MarkMakies/PIMD/coil-v4/IMG_1528.JPEG

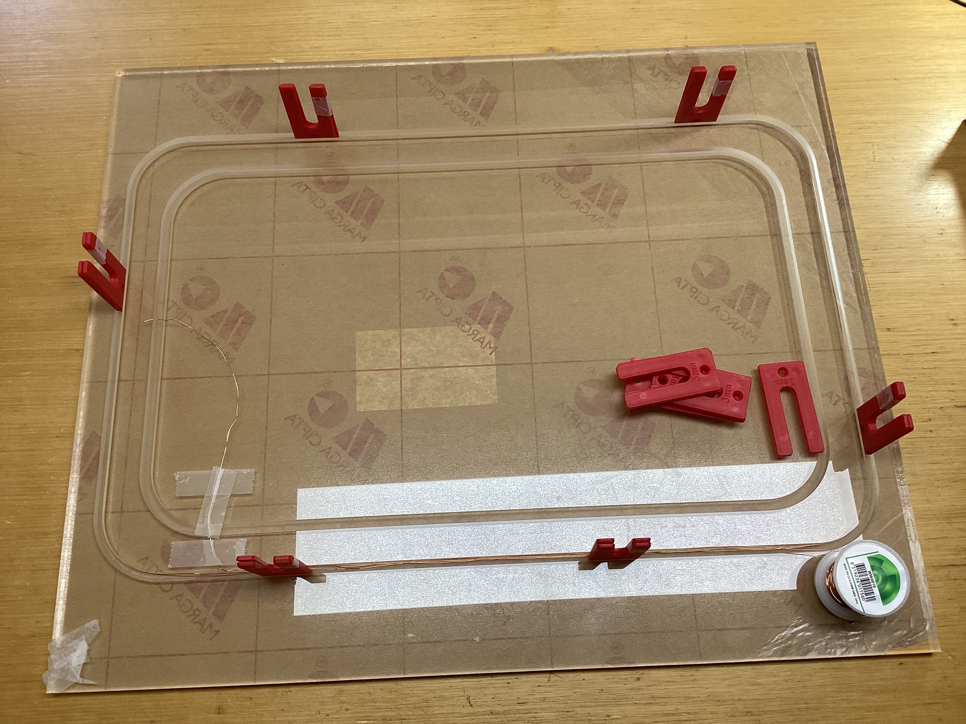
coil-v4/IMG_1528.JPEG
