MarkMakies/PIMD/coil-v4/IMG_1532.JPEG

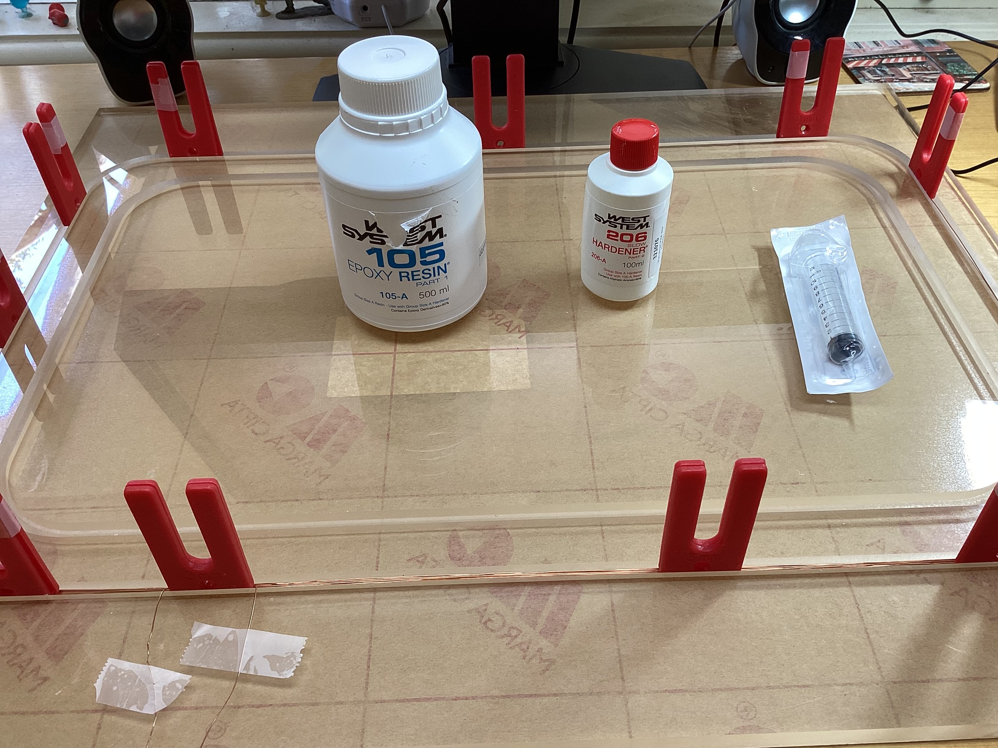
coil-v4/IMG_1532.JPEG
