MarkMakies/PIMD/coil-v4/IMG_1539.JPEG

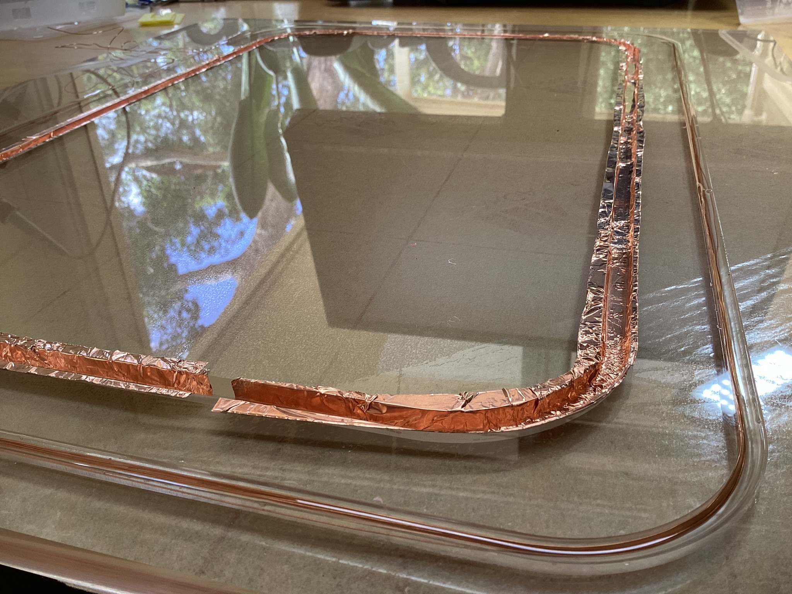
coil-v4/IMG_1539.JPEG
