MarkMakies/PIMD/coil-v4/IMG_1540.JPEG

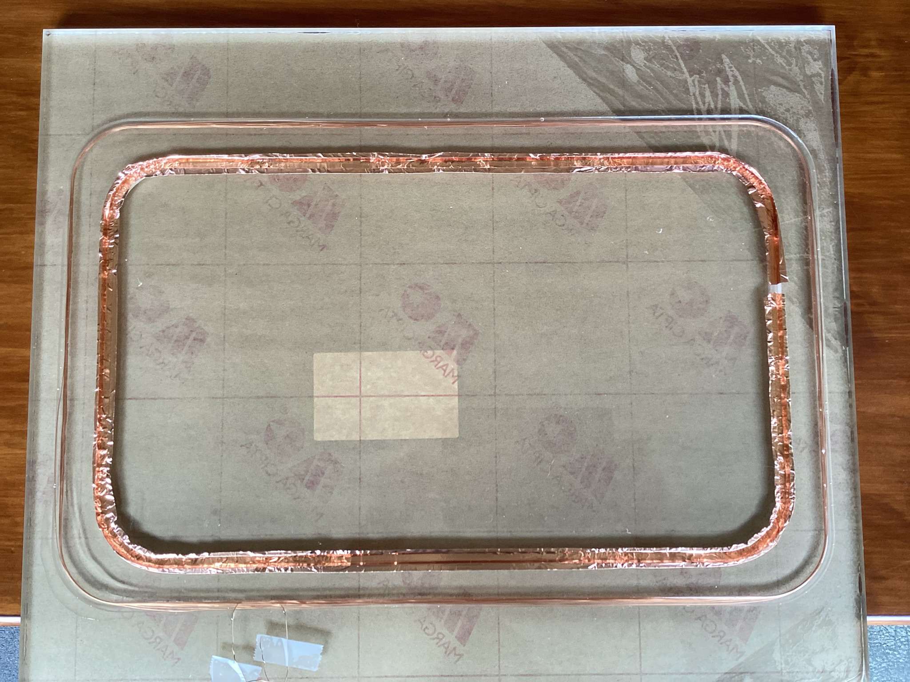
coil-v4/IMG_1540.JPEG
