MarkMakies/PIMD/coil-v4/IMG_1548.JPEG

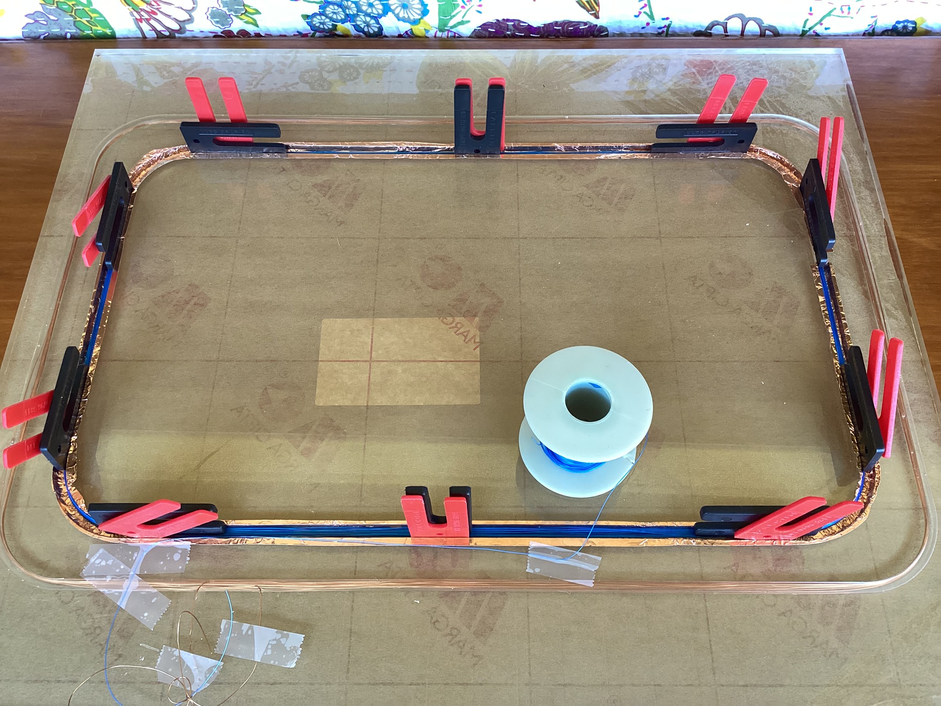
coil-v4/IMG_1548.JPEG
