MarkMakies/PIMD/coil-v4/IMG_1551.JPEG

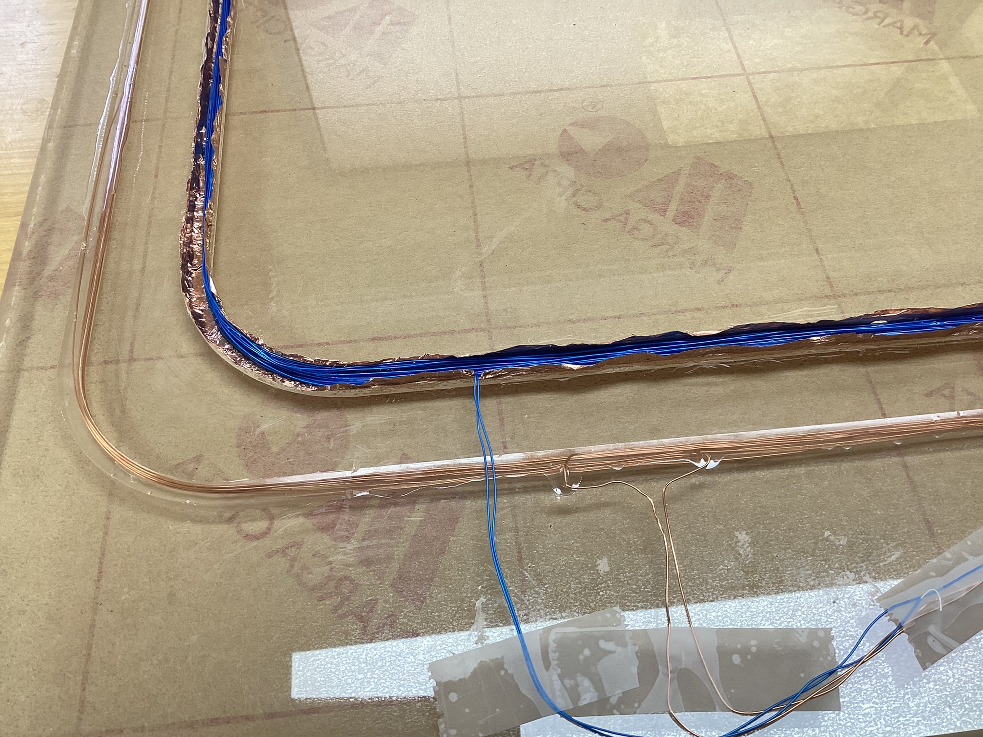
coil-v4/IMG_1551.JPEG
