MarkMakies/PIMD/coil-v4/IMG_1552.JPEG

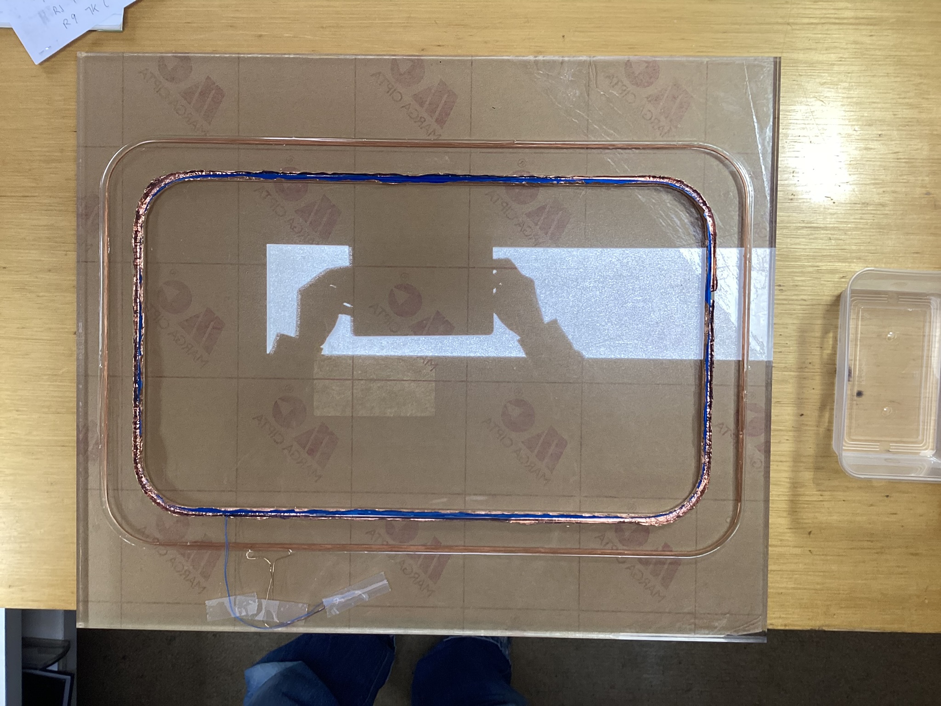
coil-v4/IMG_1552.JPEG
