MarkMakies/PIMD/coil-v4/IMG_1557.JPEG

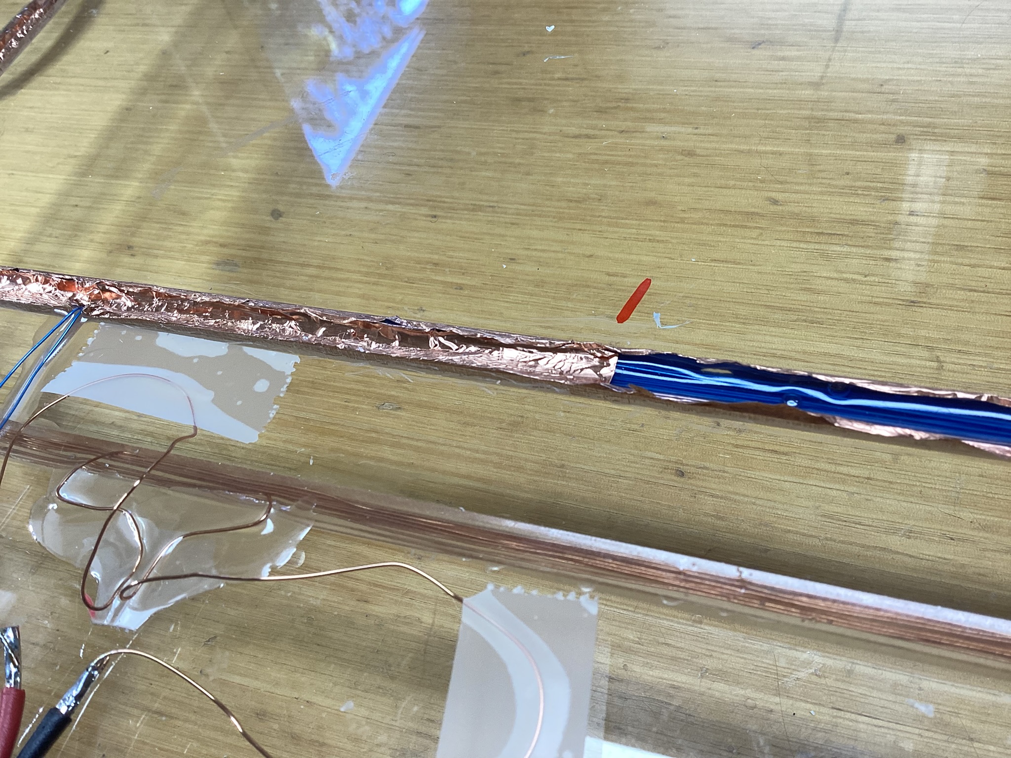
coil-v4/IMG_1557.JPEG
