MarkMakies/PIMD/coil-v4/IMG_1558.JPEG

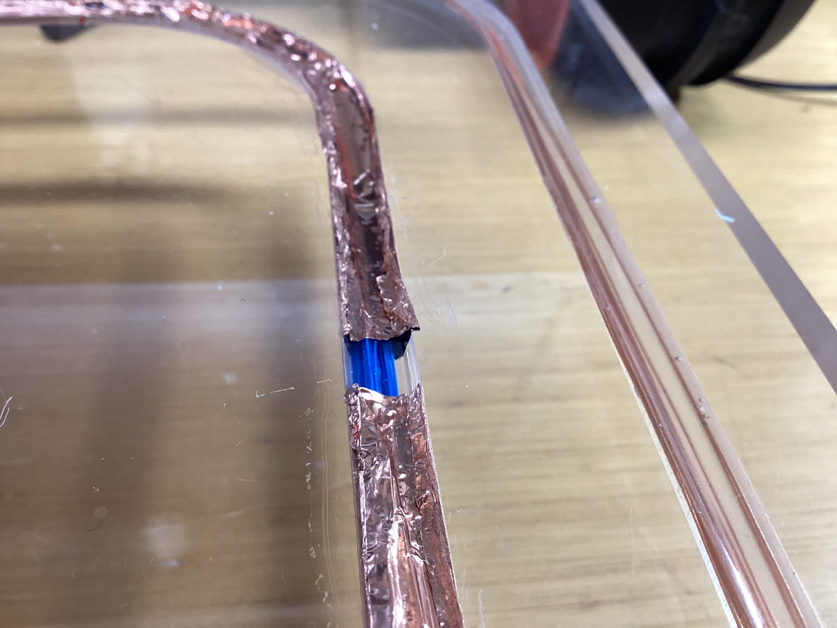
coil-v4/IMG_1558.JPEG
