MarkMakies/PIMD/coil-v4/IMG_1560.JPEG

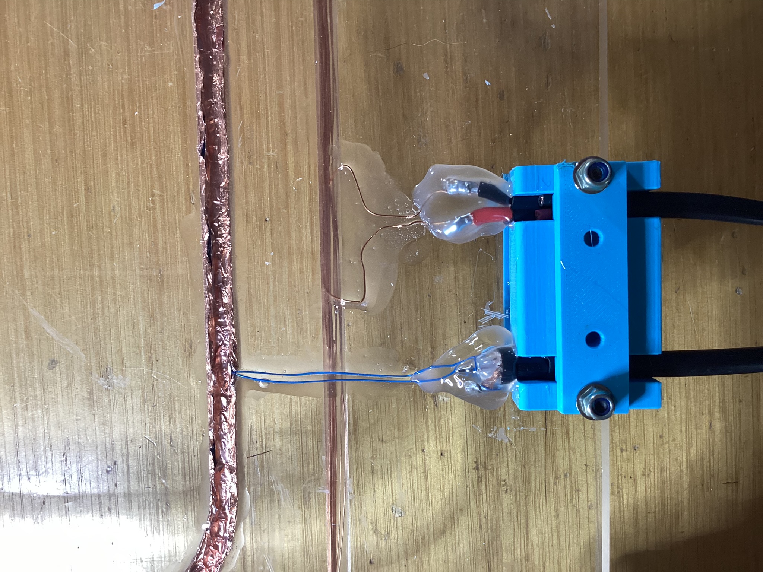
coil-v4/IMG_1560.JPEG
