MarkMakies/PIMD/coil-v4/IMG_1561.JPEG

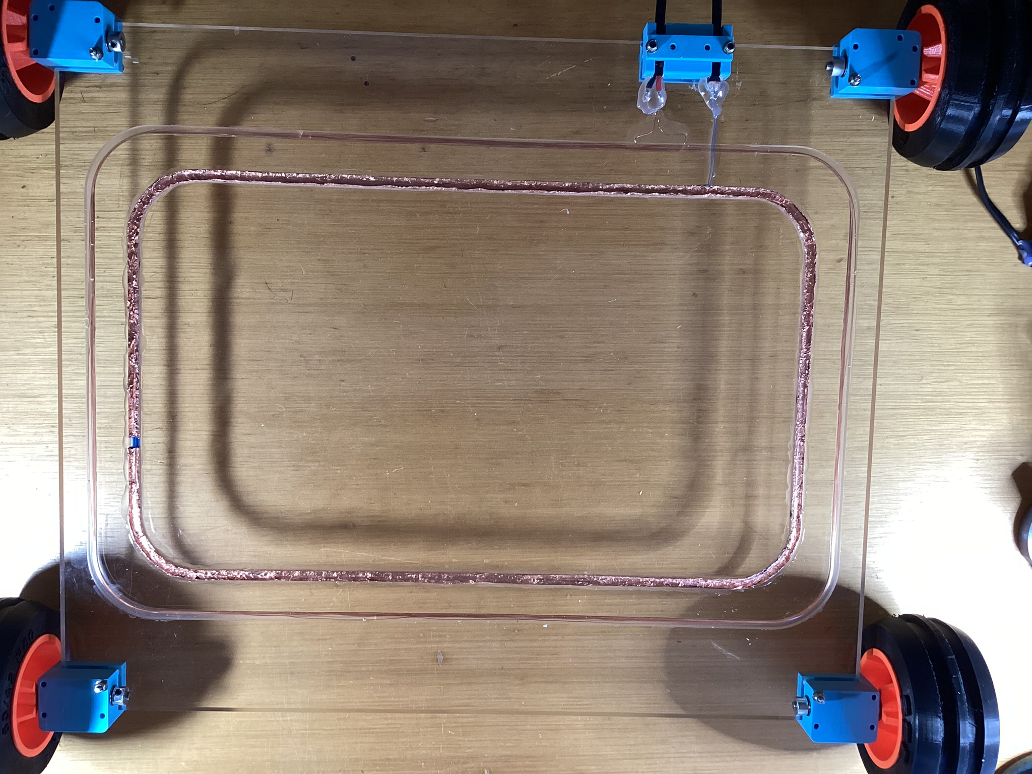
coil-v4/IMG_1561.JPEG
