MarkMakies/PIMD/References/images/6S-pack-discharge-curve.jpg

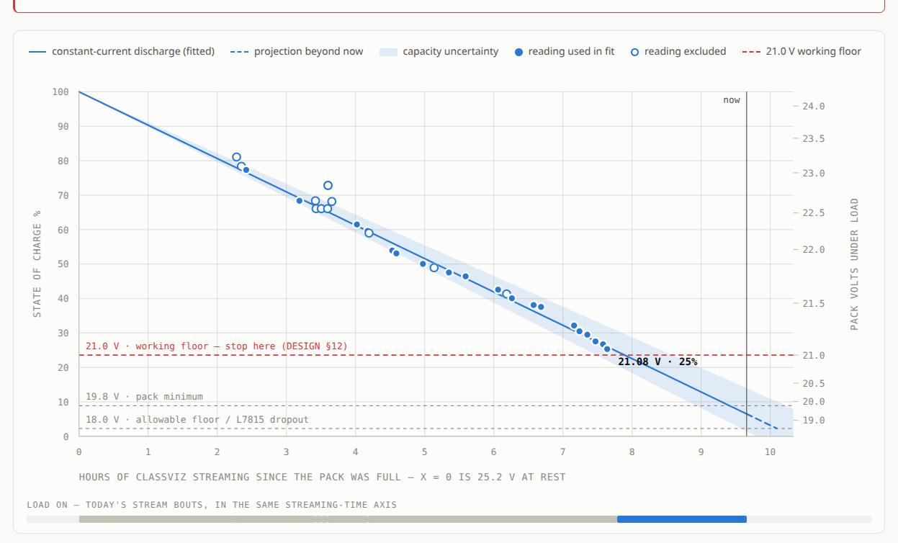
References/images/6S-pack-discharge-curve.jpg
