MarkMakies/PIMD/References/images/bias_mod_delay_plot_20260810.png

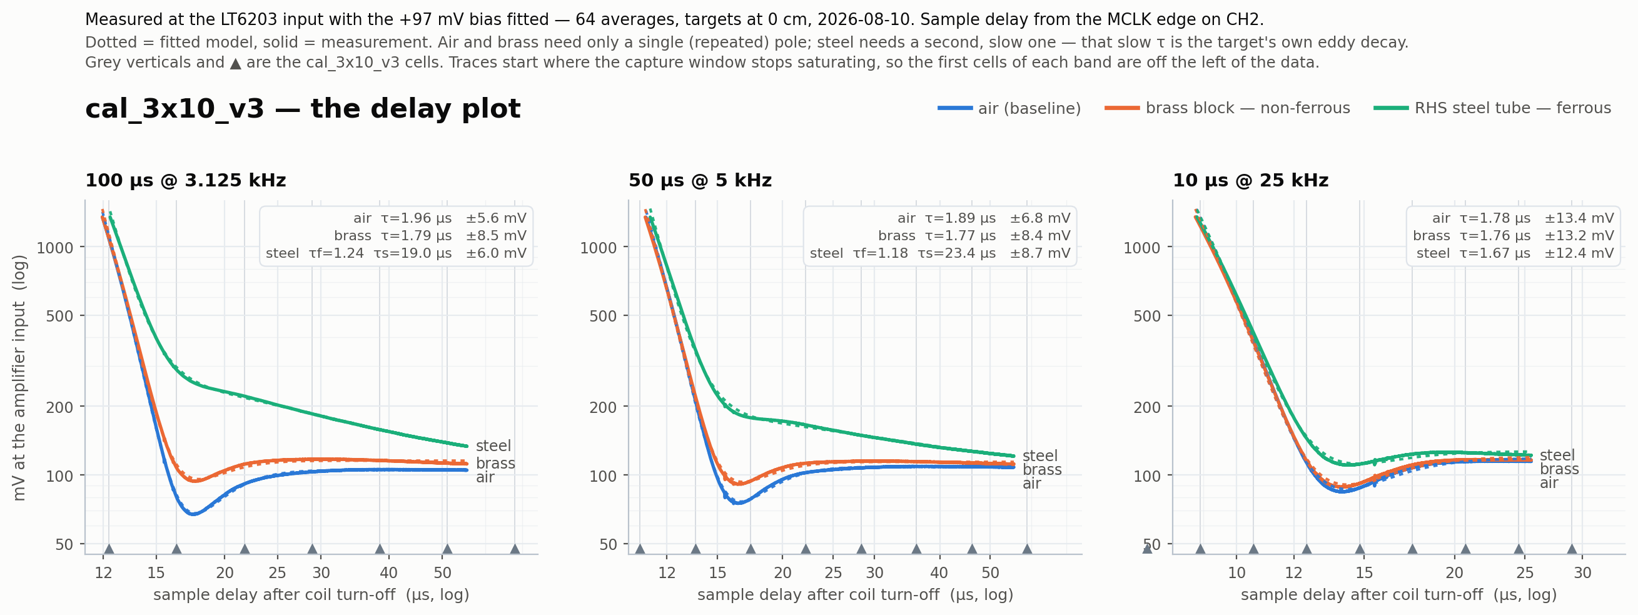
References/images/bias_mod_delay_plot_20260810.png
