MarkMakies/PIMD/References/images/delaycal-3x15v2-full-scale.jpg

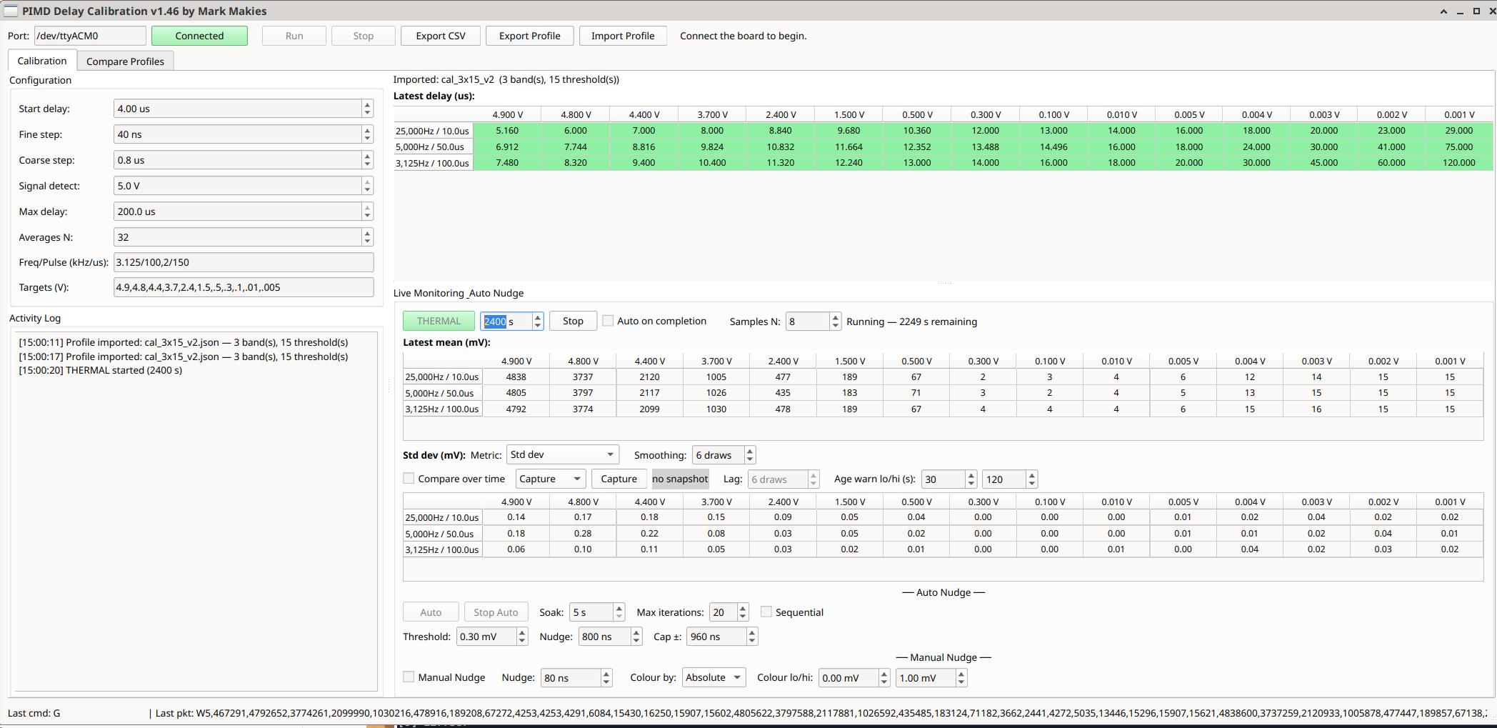
References/images/delaycal-3x15v2-full-scale.jpg
