MarkMakies/PIMD/References/images/GUI-noise-comp.jpg

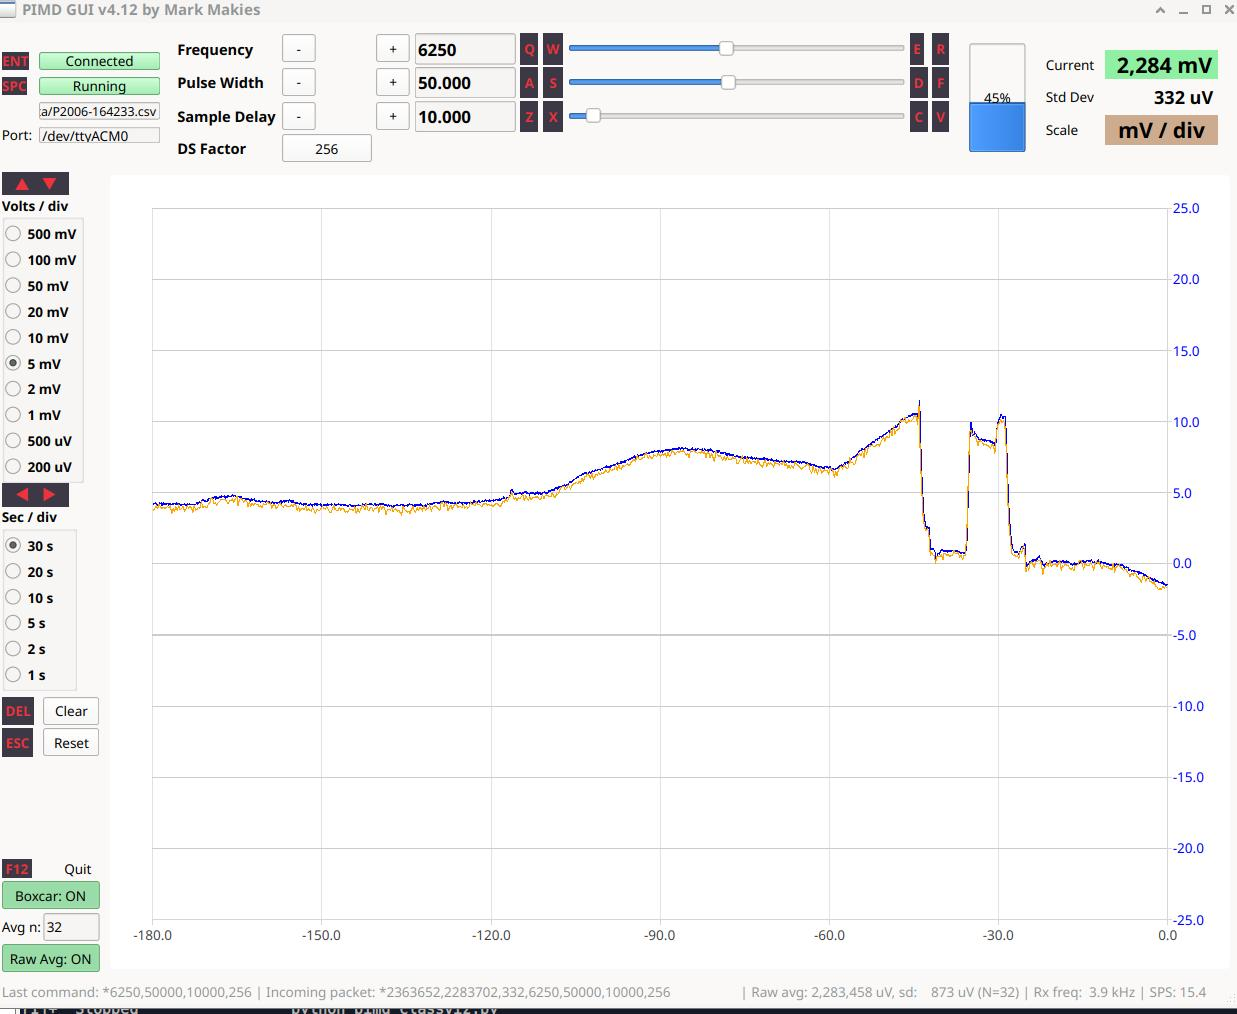
References/images/GUI-noise-comp.jpg
