MarkMakies/PIMD/References/images/GUI-steady-state-256-1024.jpg

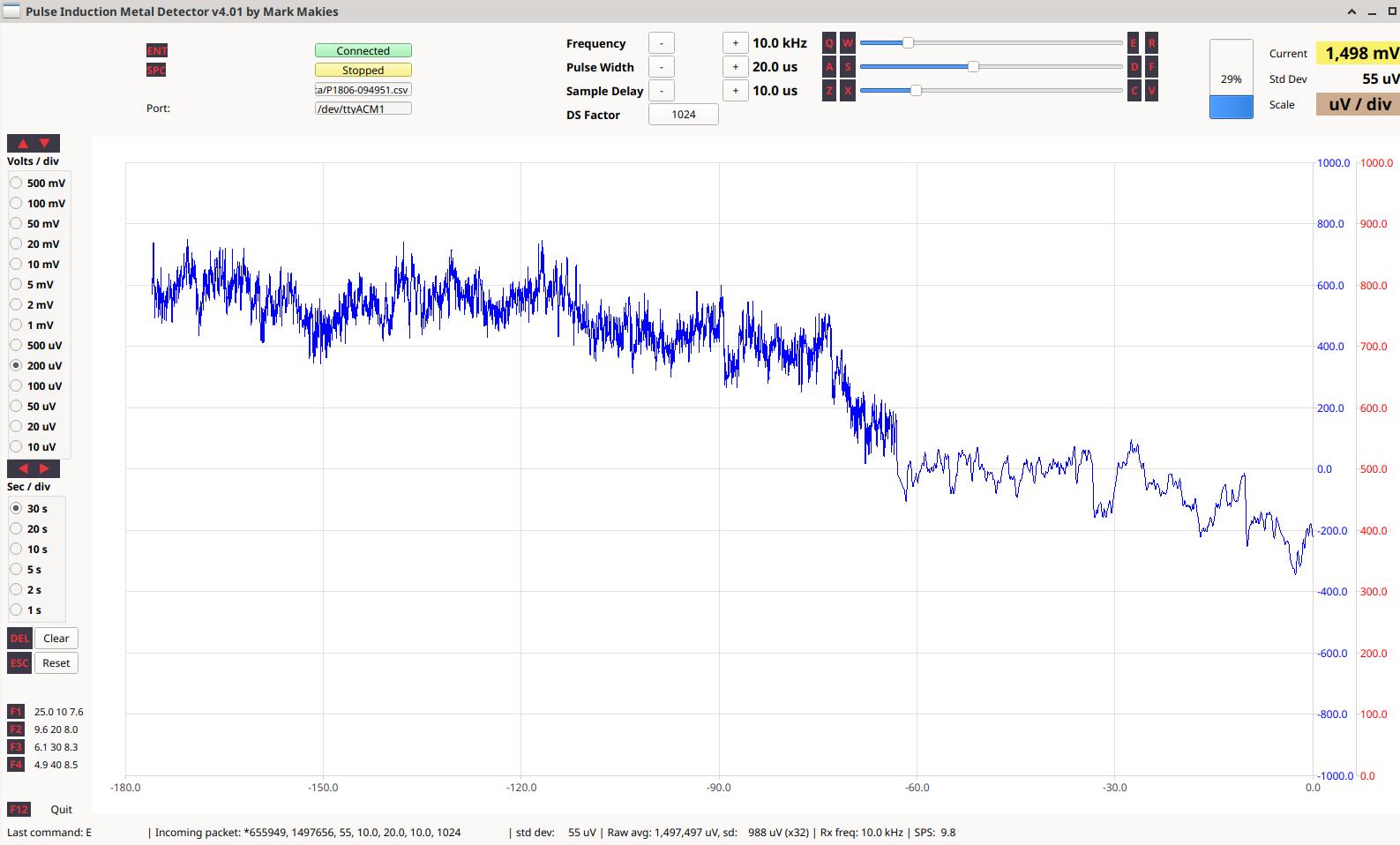
References/images/GUI-steady-state-256-1024.jpg
