MarkMakies/PIMD/References/images/GUI-target-example.jpg

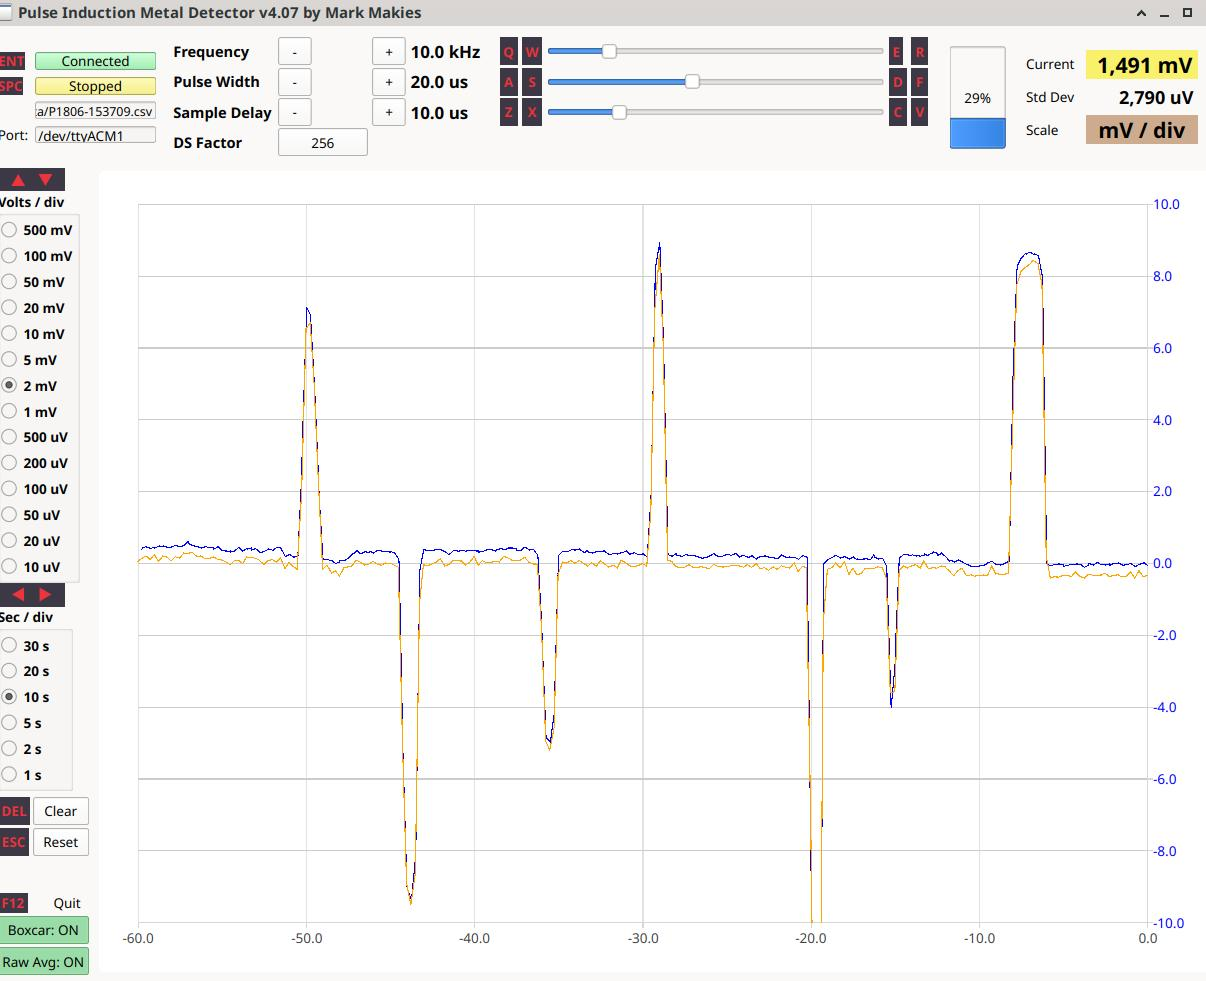
References/images/GUI-target-example.jpg
