MarkMakies/PIMD/References/images/L7815_Overload_2026-08-11.jpg

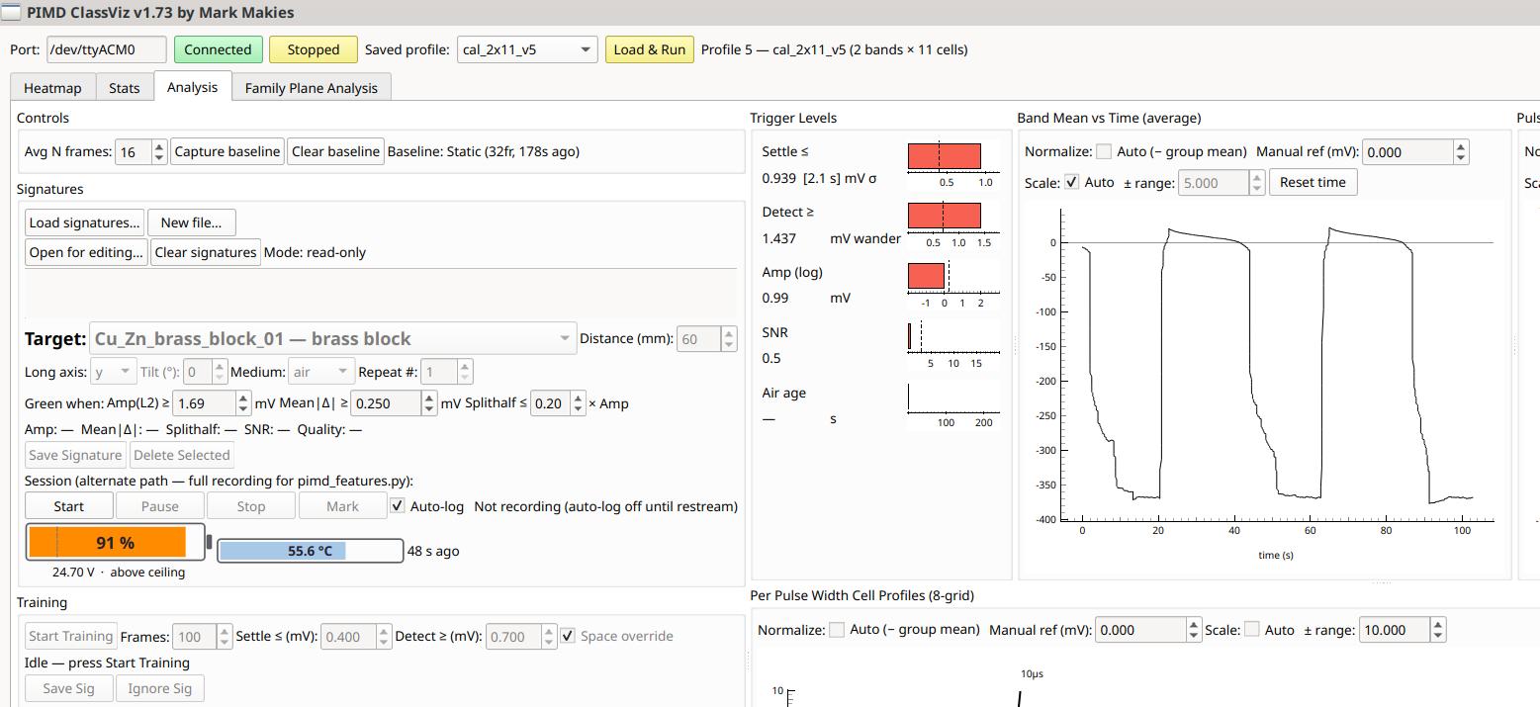
References/images/L7815_Overload_2026-08-11.jpg
