MarkMakies/PIMD/References/images/lobe_at_amp_input_20260808.png

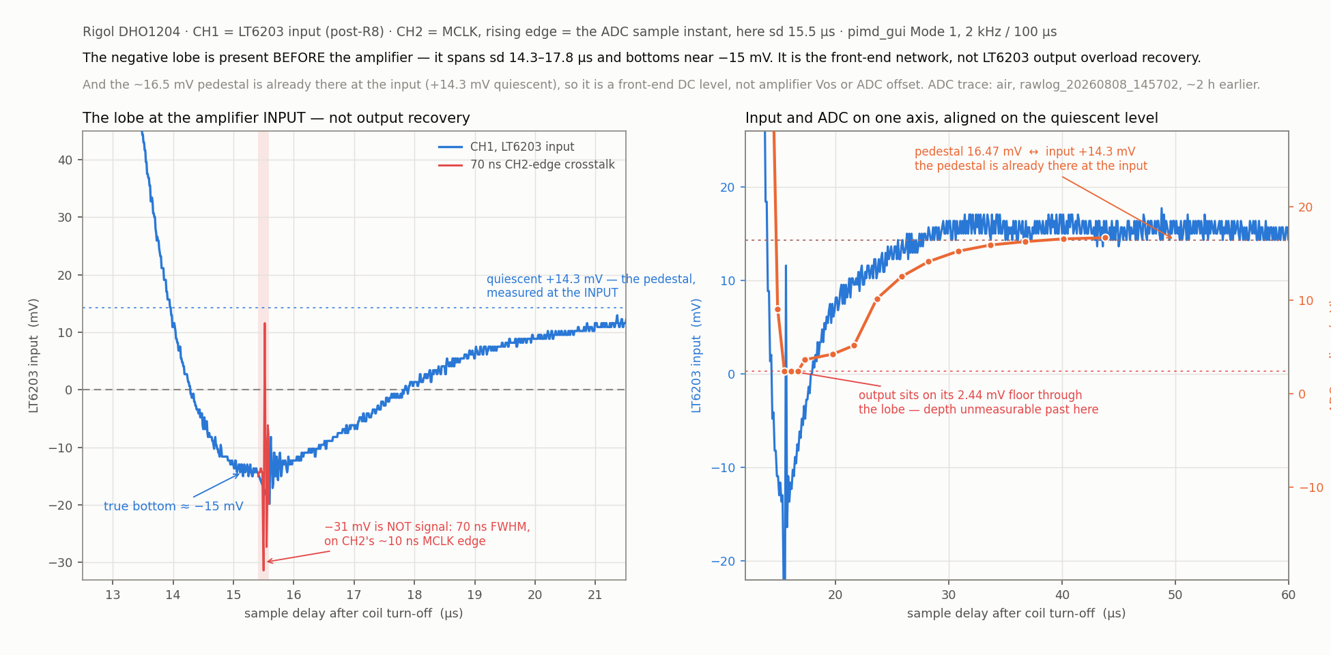
References/images/lobe_at_amp_input_20260808.png
