MarkMakies/PIMD/References/images/new-training-data.jpg

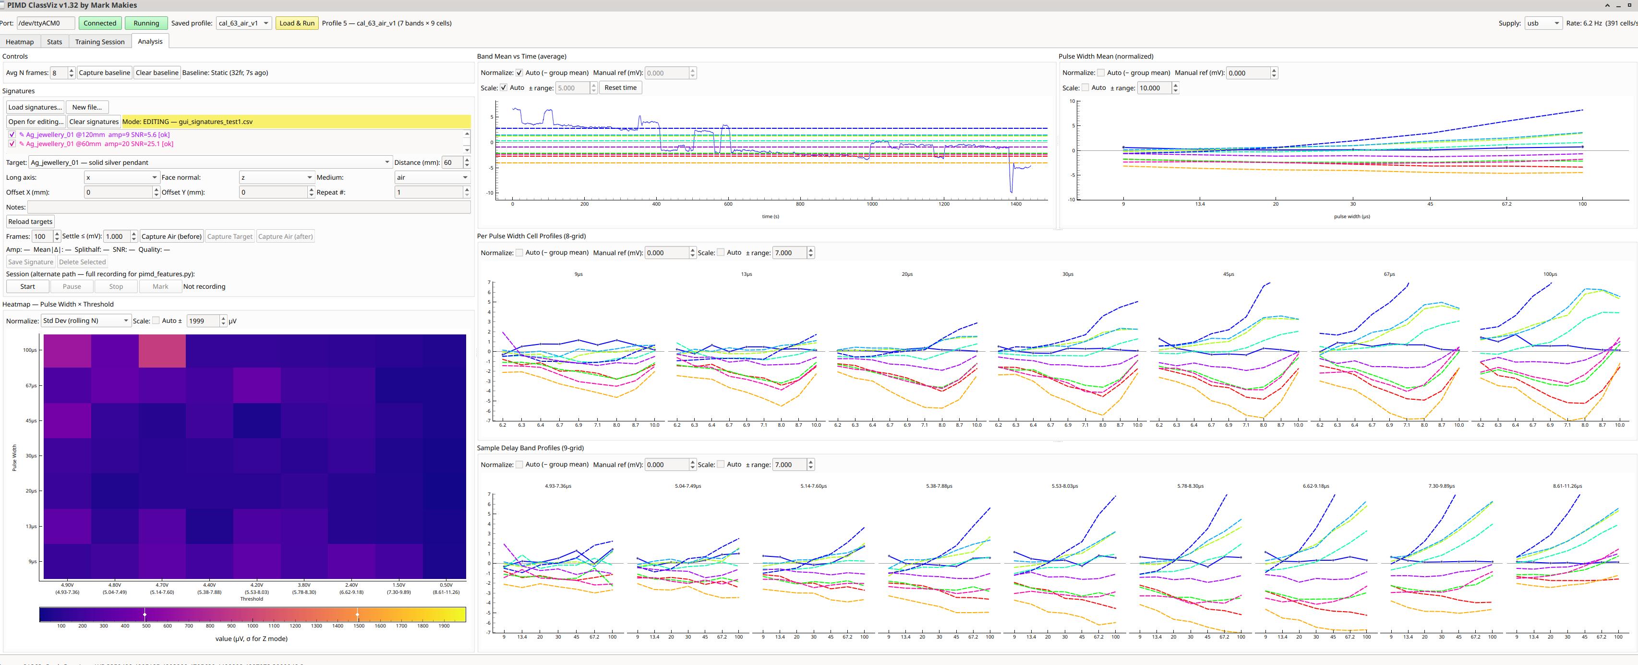
References/images/new-training-data.jpg
