MarkMakies/PIMD/References/images/profile8b-spanner.jpg

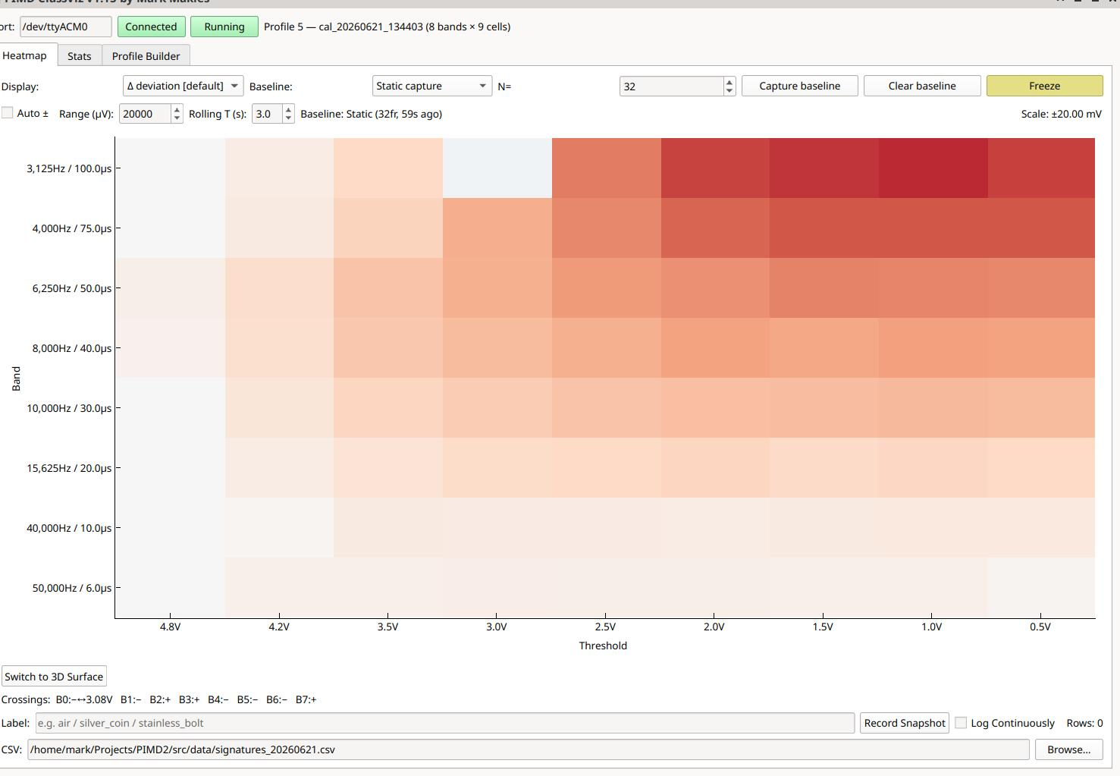
References/images/profile8b-spanner.jpg
