MarkMakies/PIMD/References/images/profile_3x10_timing.png

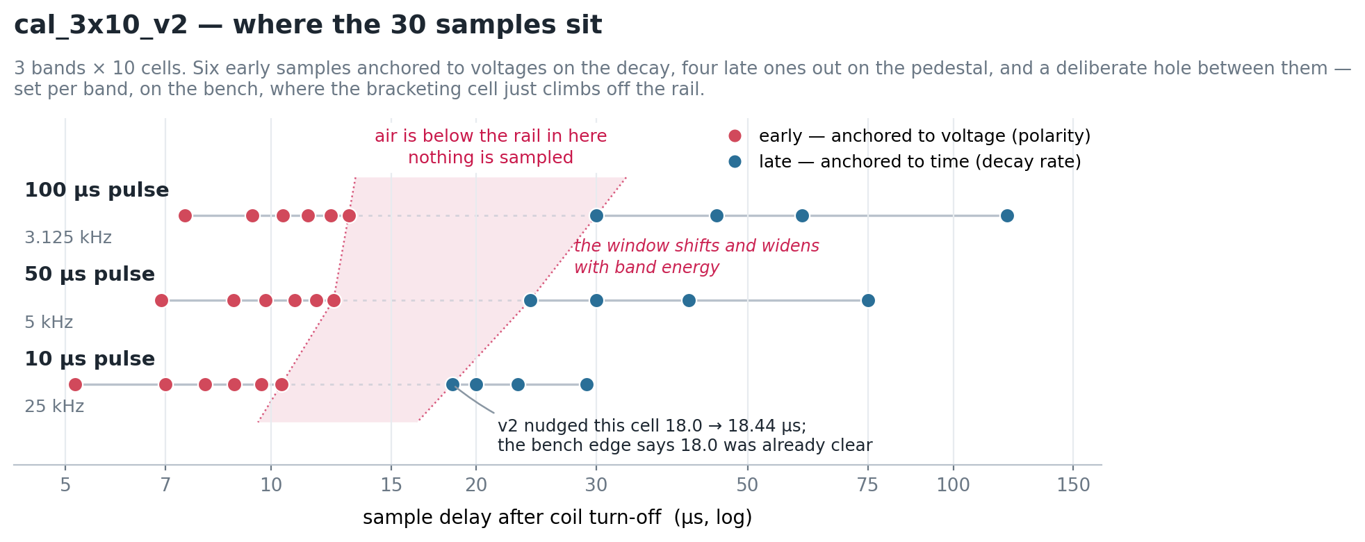
References/images/profile_3x10_timing.png
