MarkMakies/PIMD/References/images/targets v3 a.jpg

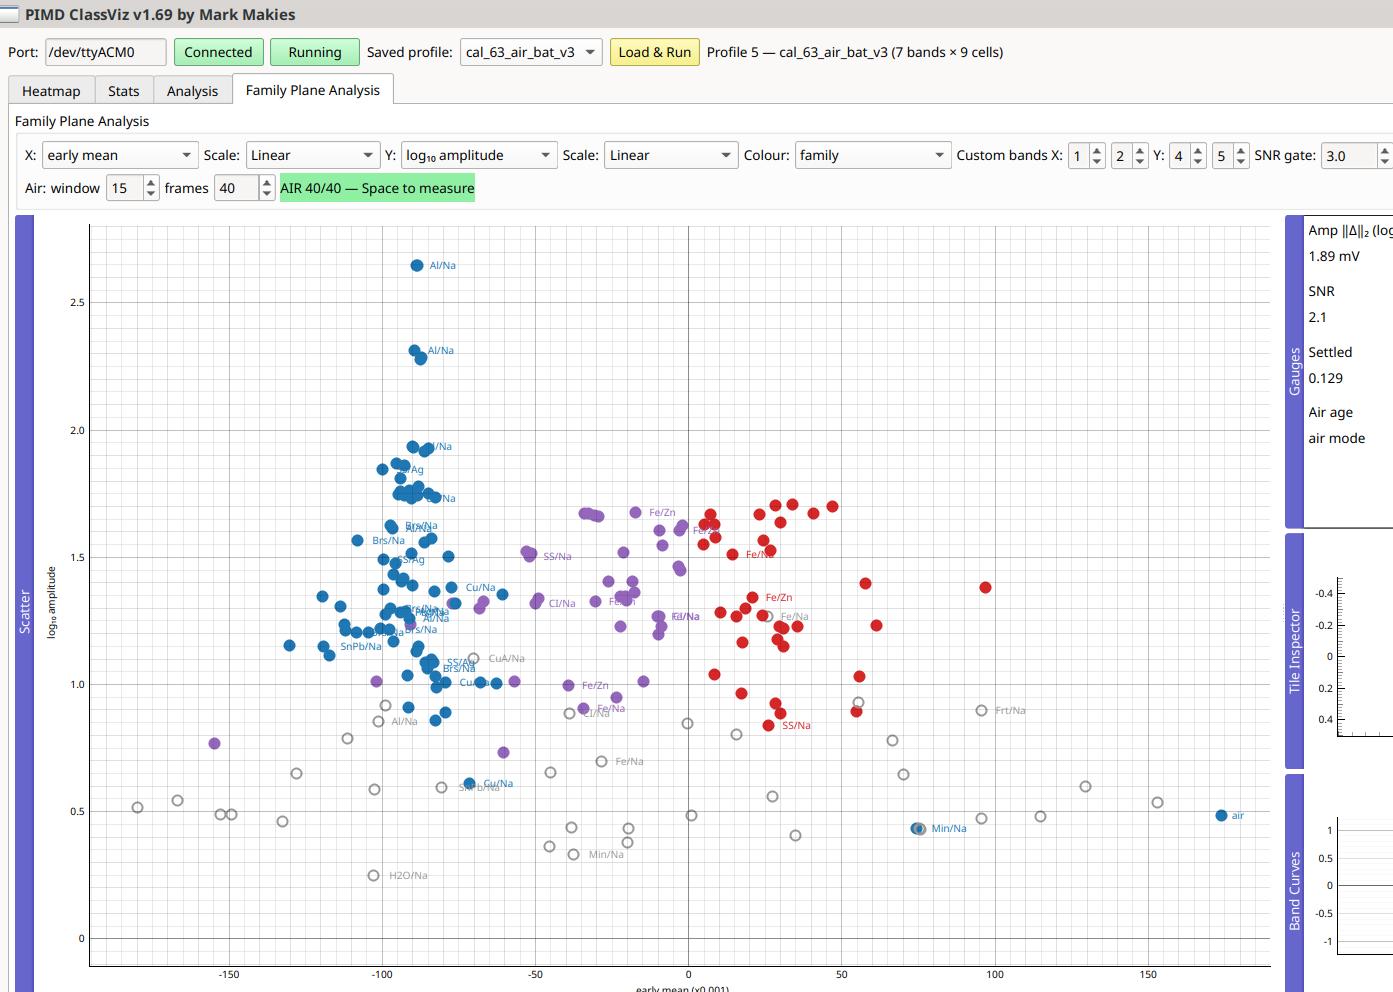
References/images/targets v3 a.jpg
