MarkMakies/PIMD/References/images/targets v3 b.jpg

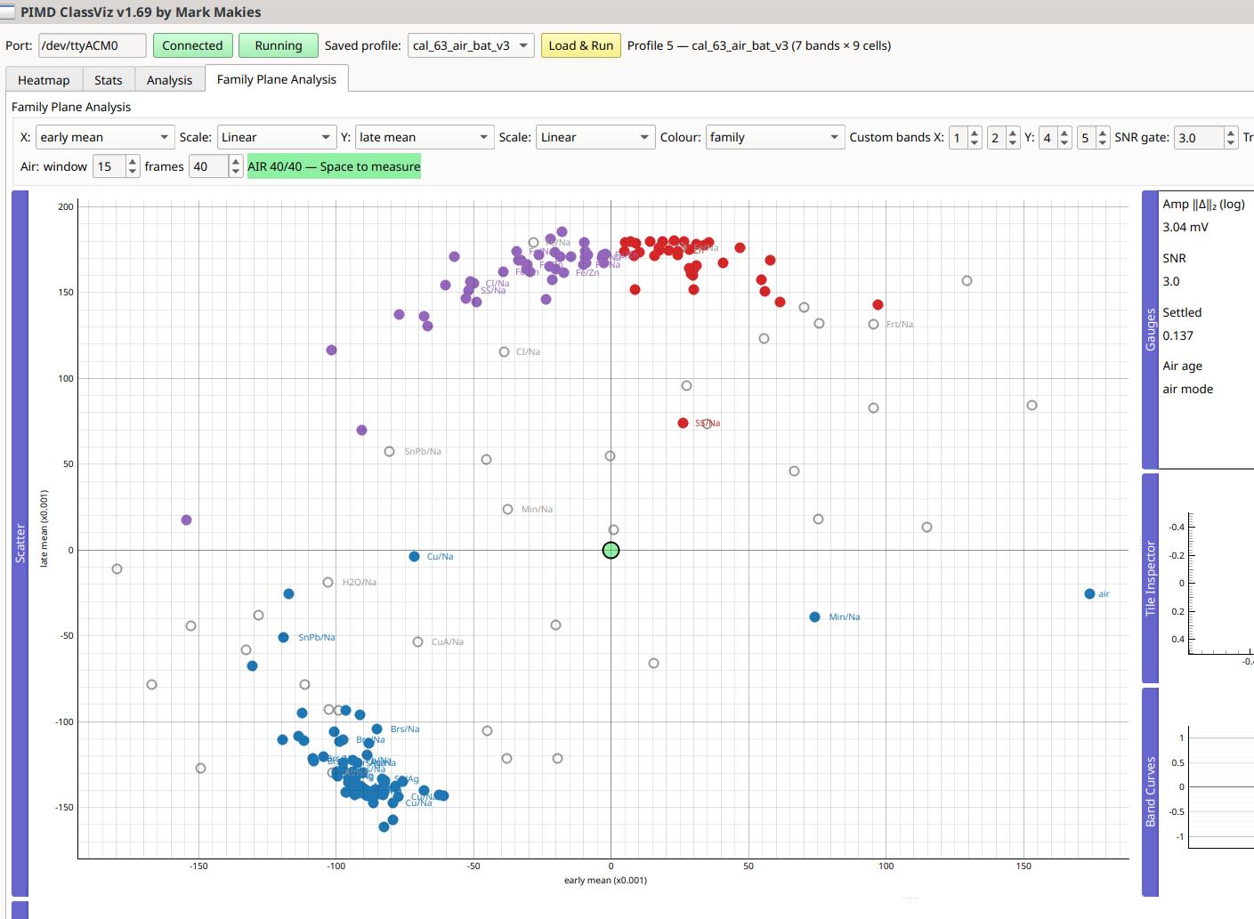
References/images/targets v3 b.jpg
