MarkMakies/PIMD/References/images/training-targets-v3.JPEG

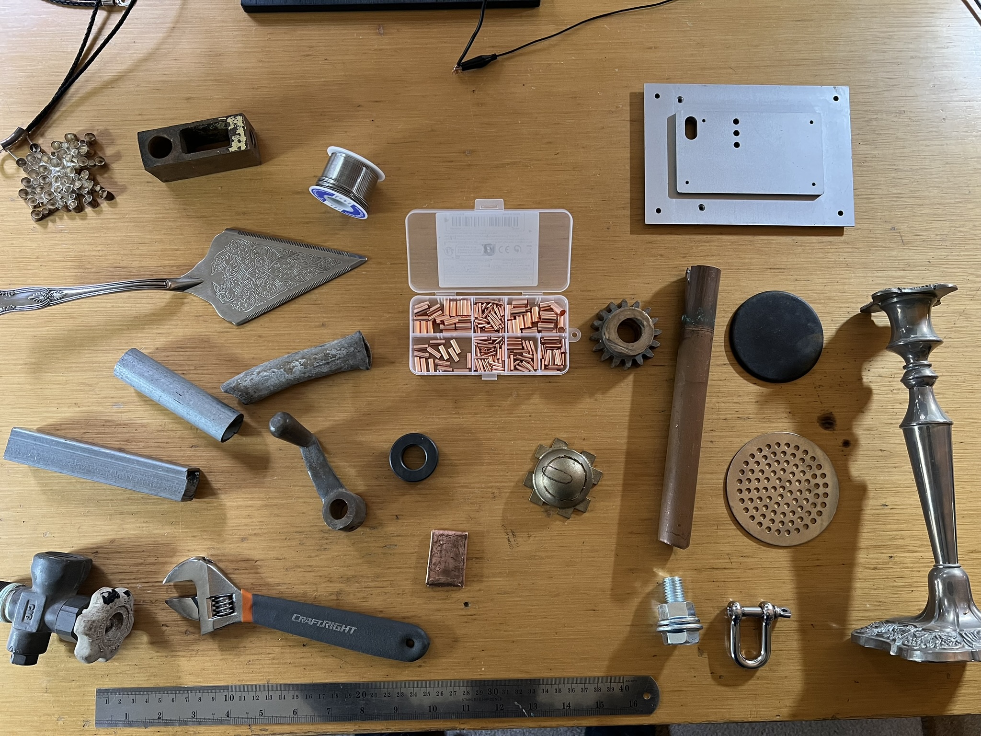
References/images/training-targets-v3.JPEG
