MarkMakies/PIMD/References/images/warmup-with-8ns-steps.jpg

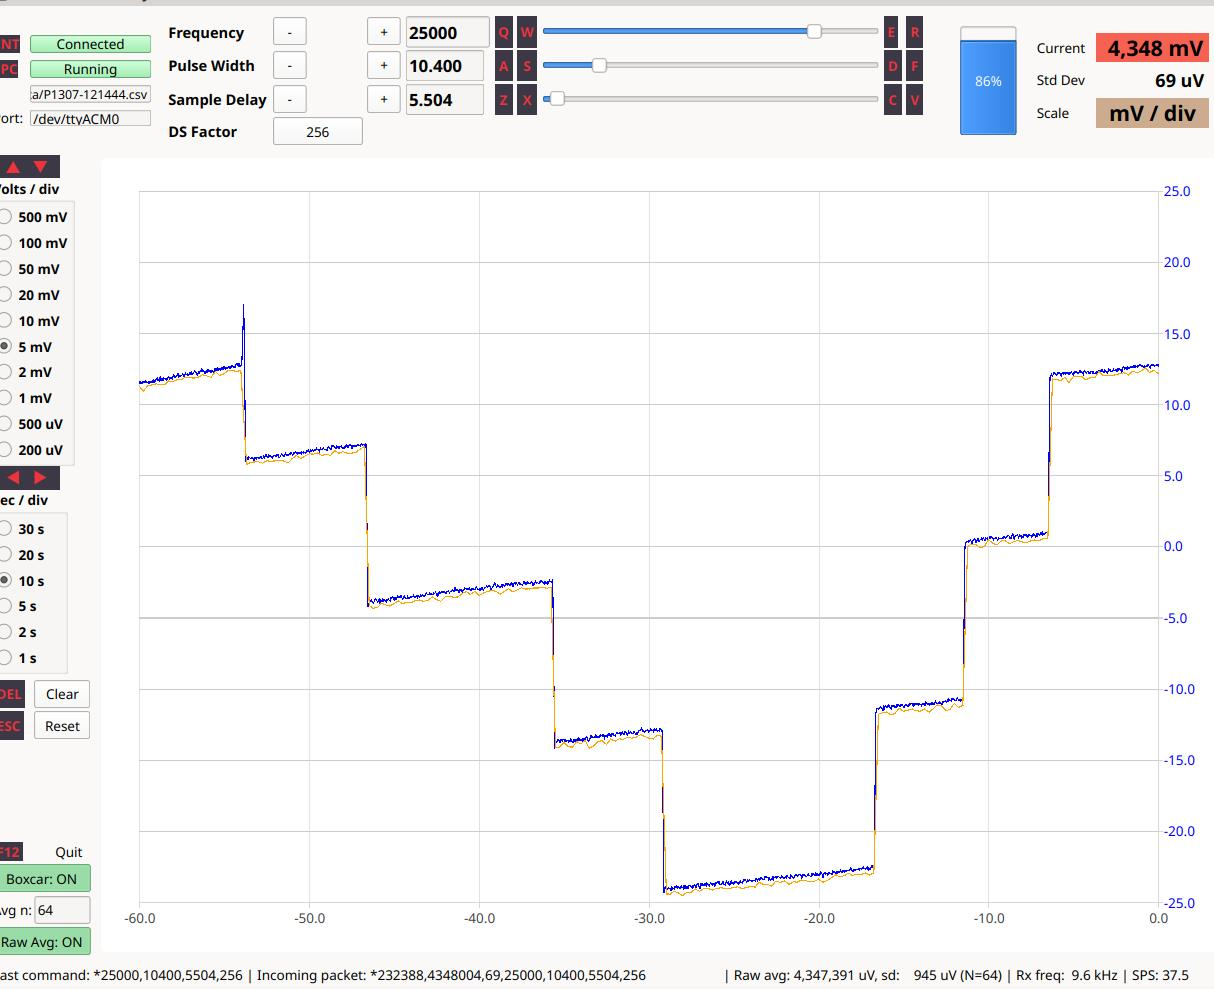
References/images/warmup-with-8ns-steps.jpg
