MarkMakies/PIMD/References/images/early-discrimination-tests.JPEG

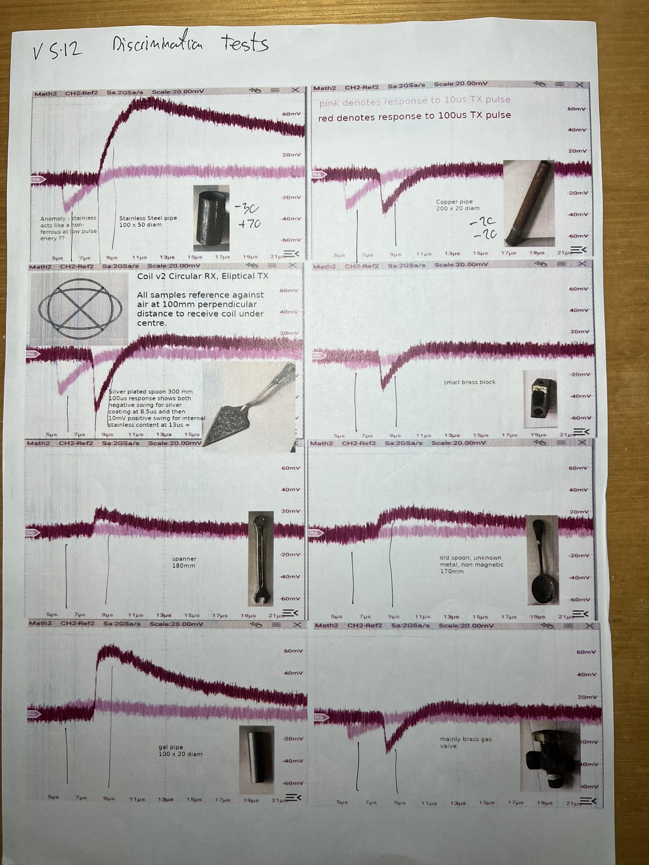
References/images/early-discrimination-tests.JPEG
