MarkMakies/PIMD/References/images/training-results-v1a.jpg

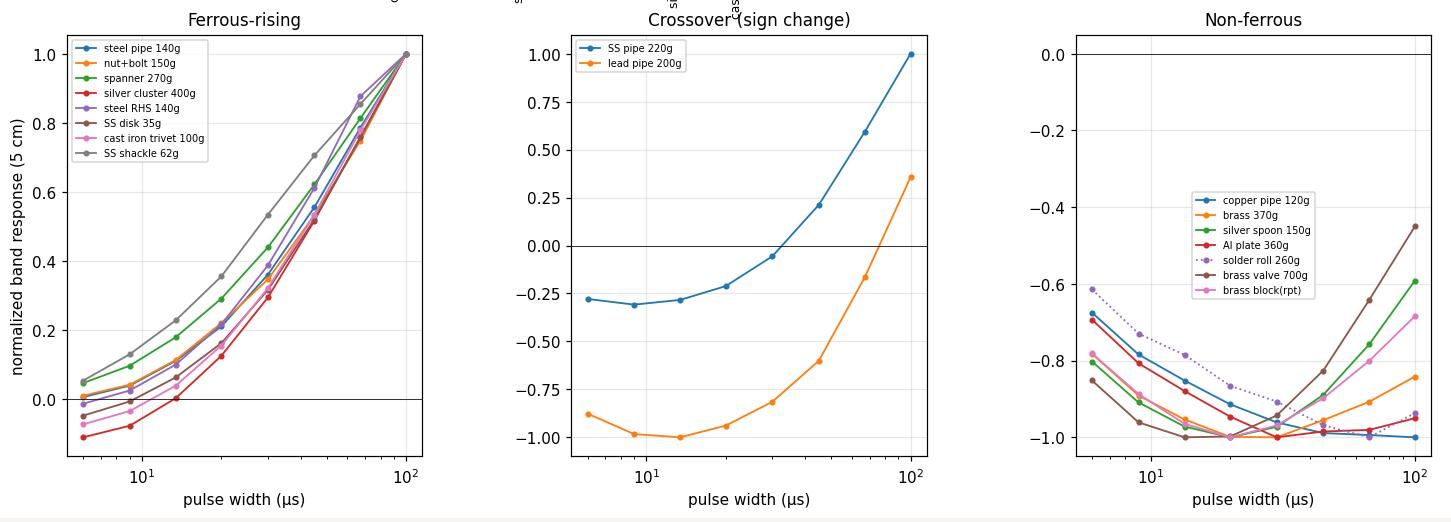
References/images/training-results-v1a.jpg
