MarkMakies/PIMD/References/images/training-results-v1b.png

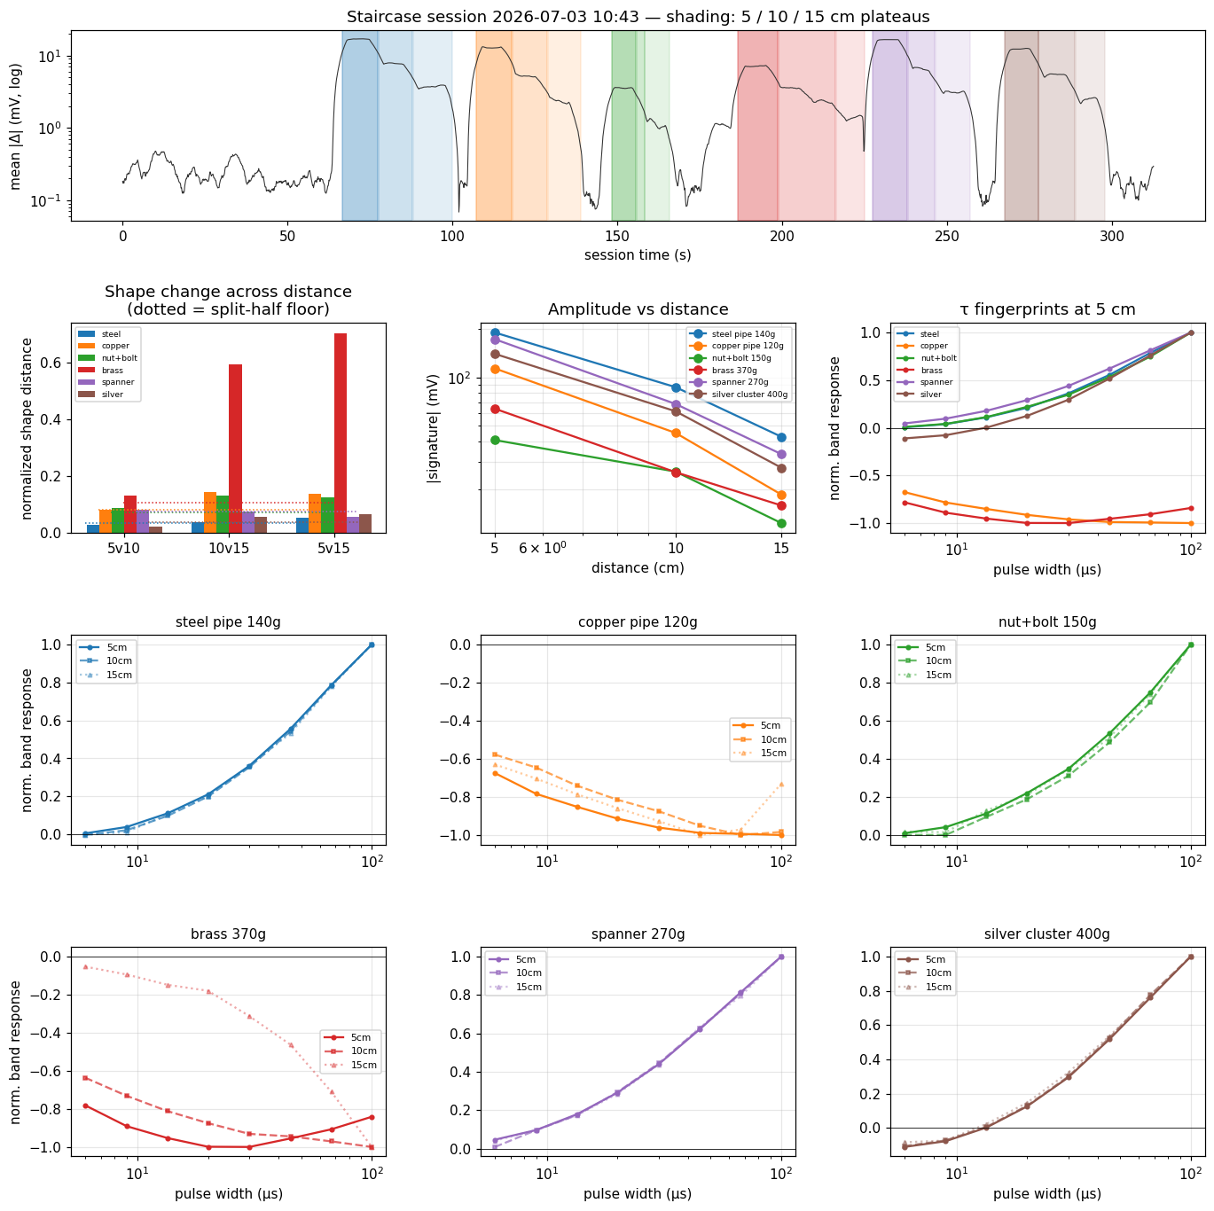
References/images/training-results-v1b.png
