MarkMakies/PIMD/References/images/training-results-v1c.png

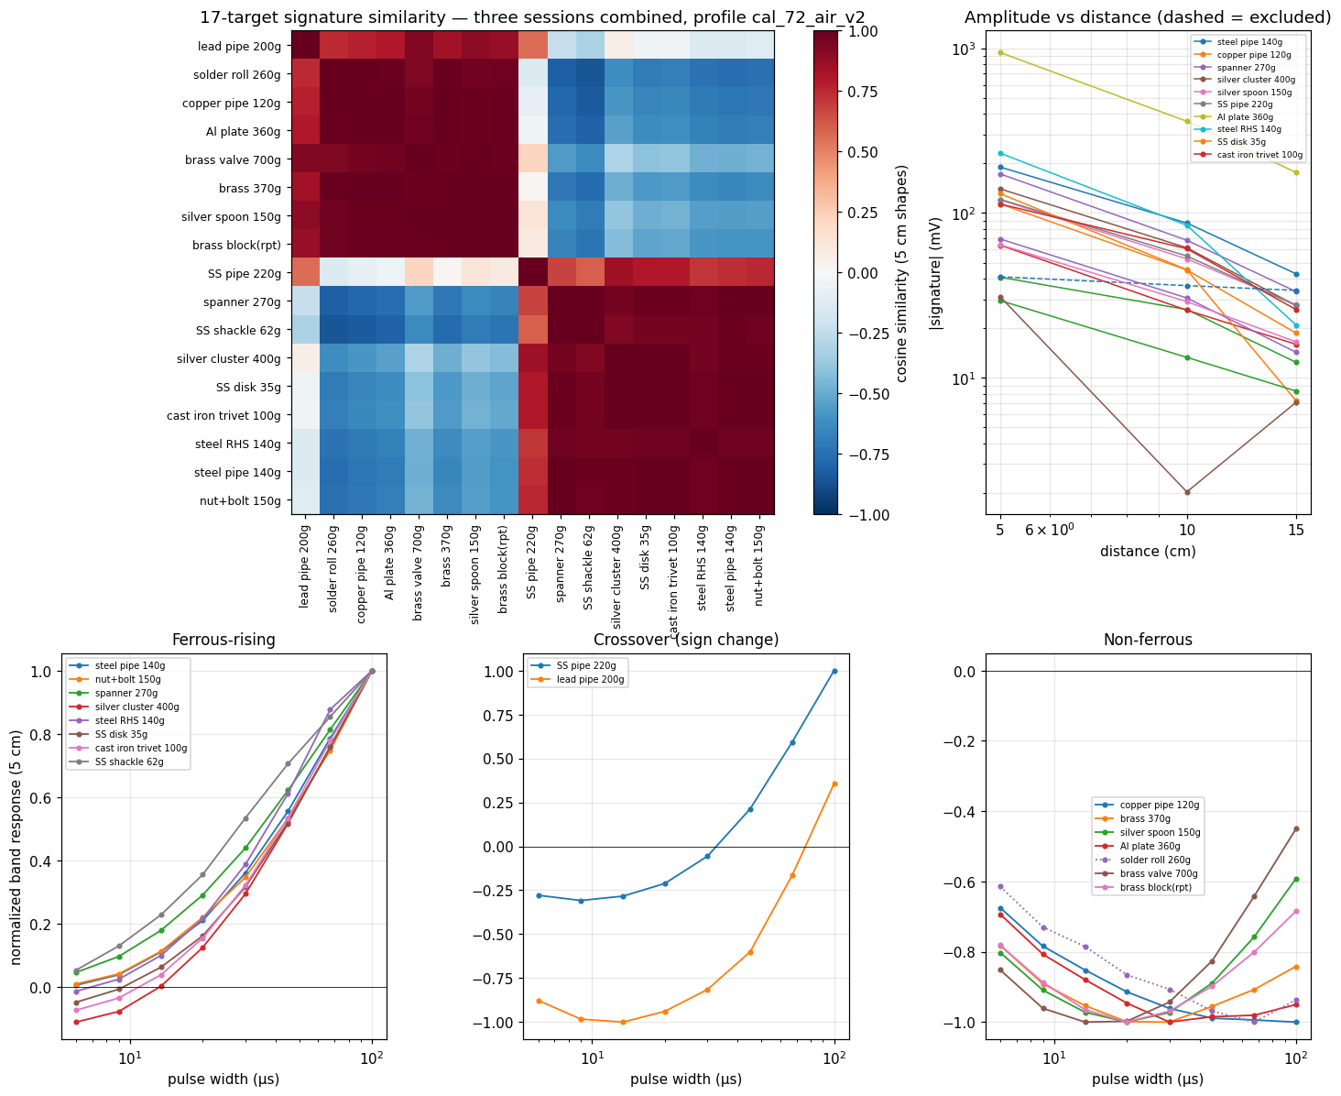
References/images/training-results-v1c.png
