MarkMakies/PIMD/CHANGELOG.md

<!-- Add new entries above this line. Format: ### <file> — v<N> — <short title> -->

## Archive — consolidated 2026-08-14 (Doc-rev 2.9)

### hardware/power — C18 4700 µF 25 V → 2200 µF 35 V; C19 assessed and deliberately unchanged

**What changed.** C18, the bulk electrolytic on the raw `+20V` pack rail (after SW3 / F1 / D4,
upstream of U1), is now a **2200 µF 35 V** part in the same package. It was 4700 µF **25 V**, and a
fresh 6S pack is 25.2 V, so it ran at ~100 % of its voltage rating from the moment a charged pack
went in. **The defect was the voltage rating, not the capacitance** — the swap fixes derating
(25.2/35 = 72 %, where an electrolytic should live) and the halved capacitance costs almost
nothing. This closes the C18 open problem that was DESIGN §14.2 (the number is now the
schematic-mismatch item, which gains C18 as its third instance).

**Why the capacitance loss does not matter here.** C18 does not supply the coil; C19 does, from the
regulated `+15V` side. C18 only feeds U1. Halving it costs roughly **107 mV** of extra dip per pulse
on `+20V`, against a pack that already sags **850 mV at full charge rising to 2.43 V at the trip**
(§12) — a rounding error on the dominant term. Even at the 19.0 V floor the regulator input stays
~1.7 V above the ~17.2 V it needs.

**Why C19 stays at 4700 µF 25 V, having been assessed in the same pass.** Two reasons, and the
second is the binding one. It is already correctly derated — a 25 V part on a 15 V rail, 60 % — so
it has no defect to fix. And **C19 is the pulse reservoir, so it is part of the drive**: the 100 µs
band at 3.125 kHz draws ~235 µC per pulse, which droops C19 by ~50 mV at 4700 µF and would droop it
~107 mV at 2200 µF. Both sit inside the conventional 1 %-of-rail rule, so the change was available
on the arithmetic — but changing the reservoir changes the drive current waveform, and therefore
every bench-measured anchor in the locked `cal_2x11_v5d` table. That means a re-cut and a new
`profile_sha8`, which is not a thing to do immediately before a corpus campaign. **Left alone
deliberately, not by omission.**

**A better explanation of the 2026-08-10 U1 failure, found while sizing this.** U1's dissipation
scales with input voltage, and the 100 µs band's average draw is ~0.73 A: **~3.6 W at 20 V in,
~7.5 W at 25.2 V in.** A freshly charged pack roughly doubles U1's heat load versus one near the
floor. That is consistent with §12's ≈2.5 W → ≈4.6 W figure, and it makes the failure a direct
consequence of the 6S decision raising V_in rather than anything to do with C18. **The C18-as-
contributor line in the old §14.2 was never evidence-backed** — it rested only on C18 being on the
same rail and independently known to be over-derated, in a paragraph that already said no
post-mortem was done. It is withdrawn with the section, and should not be revived: the causal path
was always weak, since an over-volted input electrolytic fails by venting or shorting (which takes
F1) rather than by killing the regulator downstream of it. The worst corner this identifies —
cold start on a full pack — is already covered by §10's 2026-08-13 extractor validation, 104 618
sweeps with zero flagged rows including a cold start at 24.48 V.

**Caveat, and it carries all the numbers above: TX inductance has never been measured.** It is
recorded nowhere in the repo (§5 gives geometry, turns, length and DC resistance only). **L ≈ 200 µH**
is *inferred*, two ways that agree: solving the L/R ramp against the schematic's own bench
annotation ("10 kHz, 40 µs pulses, 500 mA from bench supply at 20 V" = 50 µC per pulse) gives
~200 µH, and the coil geometry alone (10 turns, 17.6 m, equivalent radius 0.28 m) gives ~250 µH.
Within ~20 % of each other, which is enough to size a capacitor and not enough to call a
measurement. Every current, charge, droop and dissipation figure in this entry scales with it. **One
direct inductance measurement on the TX coil would put all of it on firm ground, and it is logged
here as the open measurement it is.** (2026-08-14)

### DESIGN.md — Doc-rev 2.8 — §14 pruned to the three problems that are still open

**What changed.** Human-directed edit to §14, made by the builder: seven open problems become
three. **Q1 duty headroom, C18's 25 V rating and the schematic/build mismatch at the RX front end
survive unchanged**, renumbered 1–3. Four are closed and their text removed. The §14 cross-refs
elsewhere in the document were re-pointed to match — §6's Q1 bullet `§14.2 → §14.1`, and the two
RX front-end callouts in §7's diagram plus §15's schematic image line `§14.4 → §14.3`. §14 was the
only section touched; no firmware, tool or profile version changed.

**Why each of the four went.** *Thermal drift* is characterised, not open — §3 measures the
warm-up, §17.11/§17.14 give its magnitude against supply, and classviz v1.77 now carries `temp_c`
and soak into every corpus row, so it is a standing operating fact the tooling accounts for.
*The vented enclosure* and *the undecided toroids* are closed on the builder's judgement as not
worth outstanding-issue status; both entries already recorded that the noise floor did not regress
(§3), which is the practical bound, and the toroid question additionally needed a full-charge-to-
floor run per condition that is not planned.

**`streamed_s` is the one to explain, because a code reading alone will re-raise it.** The defect
is real and still present at classviz v1.79 — `_streamed_s()` counts wall-clock from when the run
armed, and `_stall_total_s` is only ever added to inside `_note_frame_gap()`, which runs on frame
*arrival*, so a source that goes silent forever is never booked as stalled. What retired it is the
exposure, not the code. There is no auto-capture in classviz, so a corpus row can only be written
by an operator click, and at that moment the screen carries `Rate: 0 Hz` (exact last-second count,
not smoothed), the latched red lockout gauge and the telemetry-stale warning. A silence that
*ends* is booked correctly and retroactively, since the gap is measured on the firmware clock. And
a session dump over a silent stretch still carries its `# mark: firmware: LOCKOUT` line with no `W`
rows against it — which is how the 2026-08-12 case was diagnosed. The trigger also got rarer: that
lockout came off the imbalanced 6S pack, since retired. **One hole is acknowledged and accepted:**
a silence that ends with the firmware clock stepping backwards returns early at
`_note_frame_gap`'s `fw_time_ms < prev` guard and loses the whole gap. That needs an MCU reset,
which should drop the USB port and end the run instead (§16 notes a reset does not re-enumerate
reliably) — not proven from the code, and accepted as low-probability. If it is ever worth
closing, the fix is a wall-clock frame-arrival watchdog that accrues stall time while no frame has
arrived, rather than waiting for the next frame to declare the gap. (2026-08-14)

### src/data/profiles/cal_2x11_v5d.json — v5d — the 43–51 mV/V pack figure withdrawn; sha8 fc7519cd

**What changed.** Notes text only — delays and `threshold_v` untouched. `profile_sha8`
**c42a5f1e → fc7519cd**.

**Why.** The notes claimed *"Amplitude moves 43–51 mV/V with pack state (DESIGN section 12)"* and
sized the full-pack headroom warning off it. **DESIGN §12 does not carry that figure and never
did.** §12, §3 and fact 17.23 say the opposite — supply sensitivity is **~1 mV/V grid mean**,
−0.8 % over a 2.1 V swing, marked *corrected 2026-08-12*. The 43–51 number was inherited verbatim
from `cal_2x11_v5a`'s notes and propagated through v5b and v5d without being checked against the
document it cited.

**What replaces it.** The measured pair already in these entries: cell 1 moved **10.9 mV/V** on the
100 µs band and **4.5 mV/V** on the 10 µs between air windows at 20.70 → 20.17 V. That is not in
conflict with 17.23 — ~1 mV/V is a *grid mean*, and the steep early anchors depart from it by an
order of magnitude — so 17.23 gains a qualifier rather than a correction, and the profile now cites
**17.23, not §12**.

**Consequence for the headroom warning.** At 10.9 mV/V, extrapolating 20.17 V → 24 V puts cell 1
near **4.72 V** against the 5.000 V full scale, not the ~4.85 V the withdrawn figure implied —
roughly 130 mV more margin. The notes flag that as indicative only: it extrapolates 3.8 V from a
0.53 V measured span across which board temperature also moved 49.0 → 49.4 °C. Cell 1 still wants
checking on a genuinely full pack.

**Where the old figure went.** Withdrawn in DESIGN 17.23 by name, so it cannot quietly return via
another profile's notes. (2026-08-13)

### src/pimd_classviz.py — v1.79 — header title line corrected to v1.79

**What changed.** The header title line read `v1.76` while `APP_VERSION` was already `'1.79'` and the
History block correctly listed v1.77, v1.78 and v1.79. Title line only — no code, no behaviour
change, so no version bump: this brings the header into line with the version the file already is.

**Why.** Found in a pre-corpus-sweep repo audit. `APP_VERSION` is what stamps `tool_version` into
the session dump and therefore into every corpus row, so nothing recorded was ever mis-labelled —
the defect was confined to the header a reader sees first. The v1.77–v1.79 edits each added their
History line and left the title behind. Corrected now rather than after the corpus exists, so the
first `cal_2x11_v5d` capture day starts against a file whose header and constant agree.
(2026-08-13)

## Archive — consolidated 2026-08-13 (Doc-rev 2.7)

### src/data/profiles/cal_2x11_v5b.json — v5b — top amplitude anchor raised to 4.7 V, ladder re-cut and bench-locked

**What changed.** A new profile derived from `cal_2x11_v5a`, same geometry (2 bands × 11 cells,
`averages` 32, same band frequencies and pulse widths). The top amplitude anchor moves
**2.4 V → 4.7 V** and cells 2–4 are re-cut as a constant-ratio ladder down to the held 125 mV of
cell 5: targets **4.700 / 1.900 / 0.765 / 0.310 / 0.125 V**, step ratio 2.4763×. Delays after
hand-nudging: **9.456 / 11.392 / 12.704 / 13.872** µs on the 100 µs band and **6.496 / 8.384 /
9.648 / 10.776** µs on the 10 µs band. Cell 5 and **cells 6–11 are carried from v5a unchanged on
both bands**. `threshold_v` now carries the real targets for cells 1–5 — v5a's whole column was a
placeholder — while cells 6–11 stay ordering keys only, now 100 / 90 / 80 / 70 / 60 / 50 mV instead
of the old 5.0 → 0.5 V countdown. `profile_sha8` is **89d18e52**. `cal_2x11_v5a.json` is retained
and untouched.

**Why.** v5a's 2.4 V top anchor was chosen when the early samples were far noisier. They are no
longer: at 4.7 V the delaycal std dev reads 0.04–0.05 mV (N=8, 3-draw smoothing), the same as
everywhere else on the profile. So the anchored region can start higher up the decay, putting five
anchored cells across a 37.6:1 amplitude span instead of v5a's 19.2:1. Cell 5 is held at 125 mV
because it is the tested handoff into the null region and cells 6–8 are time-anchored and
band-dependent — moving it would only shift the gap into mid-descent.

**Measured, in air, 4 871 sweeps over 275 s at pack 21.59 V / board 47.1 °C** (session
`session_20260813_185559.csv`, fw v4.37, classviz v1.79):

| cell | target | 100 µs band | 10 µs band | cross-band |
|---|---|---|---|---|
| 1 | 4.700 V | 4698.1 mV −0.04 % | 4703.2 mV +0.07 % | 0.11 % |
| 2 | 1.900 V | 1893.0 mV −0.37 % | 1898.1 mV −0.10 % | 0.27 % |
| 3 | 0.765 V | 762.0 mV −0.39 % | 762.2 mV −0.37 % | 0.02 % |
| 4 | 0.310 V | 311.3 mV +0.42 % | 310.5 mV +0.16 % | 0.26 % |
| 5 | 0.125 V | 127.1 mV +1.68 % | 125.6 mV +0.52 % | 1.15 % |

Every anchored cell is within 1.7 % of target on both bands against v5a's +0.8 / +2.6 / +3.3 /
+4.4 / +7.9 %, and cross-band matching is 0.02–1.15 % against v5a's 0.4–5.3 %. Band-dependent cells
6–11 measure (100 µs / 10 µs) 80.3/78.7, **63.3/70.3** (null minimum), 92.6/92.2, 112.6/108.3,
112.8/110.3, 112.4/111.3 mV — the null keeps v5a's depth ordering (deepest on 100 µs) at v5a's
59/69 mV within 4 mV. **Sweep rate 17.75 Hz**, confirming the geometry is unchanged from v5a's
17.85 Hz.

**New finding — the decay is not log-linear above ~2 V.** The measured log-slope across cells 1–5
steepens monotonically with delay: **0.470 / 0.694 / 0.767 / 0.752 nepers/µs** on the 100 µs band
and **0.481 / 0.722 / 0.796 / 0.764** on the 10 µs. The top segment is only ~61 % as steep as the
bottom three, which are flat to within 5 % of each other. Two consequences. First, a constant
voltage-ratio ladder is *not* a constant time-step ladder up here — the cell 1–2 gap is 1.936 /
1.888 µs against ~1.17 µs at the bottom of the ladder. Second, cells 1–4 were first placed on paper
(as `cal_2x11_v5b_test`) by extrapolating v5a's own local rates, which assumed log-linearity, and
**cell 1 came out 544 ns late on both bands** and had to be nudged earlier by exactly that amount,
while cells 2–4 landed within 24 ns (3 grid steps). The 544 ns error being identical on both bands
says it is the model, not the band. This also contradicts the paper profile's stated expectation
that a miss would read high and want nudging later — it read low and wanted nudging earlier.

**Two standing cautions.** 4.700 V is 94 % of the 5.000 V ADC full scale and this cut was taken at
21.59 V / 47 % SoC; amplitude moves 43–51 mV/V with pack state (§12), so a fresh 24.5 V pack could
add 120–145 mV and put cell 1 near 4.85 V. Not clipping, but cell 1 wants watching on a full pack —
if it does clip, drop the top anchor to 4.5 V and re-run the ladder. Separately, cell 1 now sits at
6.496 / 9.456 µs, earlier than anything used in v5a (8.016 / 11.016 µs) and earlier than the
~9–12 µs window the scope captures cover, so the front-end transient is not independently
characterised there; it measures clean, and the 0.11 % cross-band agreement says both bands are
reading the same point on the same decay.

**Details.** All 22 cells validated against the firmware's own `compute_pulse_duties` /
`pulse_duties_valid`: every delay an exact multiple of the 8 ns PWM grid, both duties inside 16 bits
with sample strictly after drive, delays strictly increasing and `threshold_v` strictly descending.
The 10 µs band's last cell keeps its 96 ns (157 counts) of margin. Duty is unchanged at 31.25 % /
25 %, so the fan requirement is unchanged and still structural. The changed `threshold_v` column and
five moved delays give a different `profile_sha8` from v5a, so frames from the two must never be
mixed in one dataset (§10) — the `(profile_name, profile_sha8)` guard in `pimd_features` enforces
it. The validation session logged 39 flagged rows (0.80 %), all in one contiguous 5 s burst at
18:57:55–18:58:00 and none before or after — a single external disturbance during the run, not a
profile property. **Known wart:** as with v5a, the exported `notes` field carries the superseding
profile's preamble forward verbatim — here `cal_2x11_v5b_test`'s "UNTESTED, UNSWEPT … DELAYS ARE
EXTRAPOLATED … will read HIGH and want nudging LATER", none of which describes this file. Not
corrected in place, because `profile_sha8` hashes the literal profile-file bytes including `notes`,
so editing the prose would move the sha8 off the 89d18e52 already stamped into the air sessions
above. (2026-08-13)

### src/data/profiles/cal_2x11_v5d.json — v5d — knee cells re-placed by hand; FINAL, locked, corpus next

**What changed.** `cal_2x11_v5d` is the new operating profile, locked at `profile_sha8`
**48de8676**. Against `cal_2x11_v5b`, only cells 3 and 4 moved, both earlier on both bands:
100 µs band cell 3 **12.704 → 12.136** (−568 ns), cell 4 **13.872 → 13.272** (−600 ns), cell 5
15.064 → 15.088 (+24 ns); 10 µs band cell 2 8.384 → 8.376 (−8 ns), cell 3 **9.648 → 9.088**
(−560 ns), cell 4 **10.776 → 10.160** (−616 ns). Cells 1, 2 and 6–11 are unchanged from v5b, which
carried 6–11 unchanged from v5a. Geometry, band frequencies, pulse widths and `averages` are
unchanged. `threshold_v` cells 1–5 are updated to the voltages the cells were **measured** to
sample — **4.700 / 1.900 / 1.150 / 0.500 / 0.125 V** — replacing v5b's 0.765 / 0.310 entries, which
the move had made stale. Cells 6–11 remain ordering keys at 100 / 90 / 80 / 70 / 60 / 50 mV.
The exported `notes` field, which by v5d had accumulated a four-deep nested "Carried forward
from…" chain still ending in `cal_2x11_v5b_test`'s "UNTESTED, UNSWEPT" preamble, was replaced with
a description of this profile — the wart called out in the v5a and v5b entries, fixed here.

**Why.** The cells were placed **by hand against live target charts**, not solved to a voltage
target. On v5b the steepest part of the measured target response fell in the cell 2 → cell 3 gap
and cell 3 sat past the knee, so the response read as a kink rather than a shape. Moving cells 3
and 4 earlier puts them on that limb. The resulting gaps are **1.936 / 0.744 / 1.136 / 1.816 µs**
(100 µs band) and 1.880 / 0.712 / 1.072 / 1.800 µs (10 µs) — deliberately uneven, tight through the
knee and wide either side. That is the reverse of v5b's even-in-log-amplitude ladder and is the
point of the change: v5b's spacing rationale had already been falsified by the measurement that the
decay is not log-linear above ~2 V (see the v5b entry), so even log spacing had no remaining claim
on the design.

**Measured in air — 3 932 sweeps over 220 s, zero flagged rows, pack 20.70 V, board 49.0 °C**
(`session_20260813_193503`, fw v4.37, classviz v1.79):

| cell | 100 µs delay / mean | 10 µs delay / mean | cross-band |
|---|---|---|---|
| 1 | 9.456 µs · 4685.8 mV | 6.496 µs · 4698.4 mV | 0.27 % |
| 2 | 11.392 µs · 1880.0 mV | 8.376 µs · 1901.7 mV | 1.15 % |
| 3 | 12.136 µs · 1136.8 mV | 9.088 µs · 1153.4 mV | 1.45 % |
| 4 | 13.272 µs · 491.4 mV | 10.160 µs · 507.2 mV | **3.16 %** |
| 5 | 15.088 µs · 123.2 mV | 11.960 µs · 124.5 mV | 1.13 % |
| 6–11 | 78.8 / 62.2 / 91.6 / 111.9 / 112.3 / 112.1 mV | 78.1 / 70.0 / 92.0 / 108.0 / 110.0 / 111.1 mV | band-dependent |

Air std dev is 0.07–1.03 mV per cell on the 100 µs band and 0.07–0.25 mV on the 10 µs. **Sweep rate
17.86 Hz**, unchanged from v5a/v5b as expected since the geometry did not change.

**Known wart, left in deliberately.** Cell 4's cross-band matching is **3.16 %**, against 0.26 % on
v5b — the hand placement moved the two bands by slightly different amounts (−600 vs −616 ns) on a
steep part of the decay. Cells 1–5 are meant to be amplitude-matched across bands so that cell
index *n* is the same point on the decay in either band, and cell 4 now bends that. It is left as
cut because the profile is locked; ~20 ns on either band would close it if it is ever revisited.

**Standing caution — cut at a low pack.** These delays and voltages were taken at **20.70 V**,
below v5b's 21.6 V and near the bottom of the §12 clean window. At 43–51 mV/V the cells read higher
on a fuller pack — roughly +150 to +200 mV on cell 1 at 24 V, putting it near 4.85 V against the
5.000 V full scale. Not clipping, but cell 1 wants watching at the top of the pack range.

**Details.** All 22 cells validated against the firmware's own `compute_pulse_duties` /
`pulse_duties_valid`: every delay an exact multiple of the 8 ns PWM grid, both duties inside 16 bits
with sample strictly after drive, delays strictly increasing and `threshold_v` strictly descending.
The 10 µs band's last cell keeps its 96 ns (157 counts) of margin. The file was written without a
trailing newline to match the `pimd_delaycal` export convention its siblings use, since
`profile_sha8` hashes the literal file bytes.

**Next step: build the corpus against this profile.** `profile_sha8` **48de8676** is the pin —
the running session that produced the air numbers above was stamped `8894f0b9`, the pre-lock bytes,
so **the profile must be reloaded in the tool before recording** or the corpus rows will carry a
sha8 that no longer matches the file and the `(profile_name, profile_sha8)` guard in
`pimd_features` will separate them (§10). (2026-08-13)

### src/data/profiles/cal_2x11_v5d.json — v5d re-cut — cell 4 cross-band mismatch closed; sha8 6339c35e

**What changed.** Cell 4 only, on both bands: 100 µs **13.272 → 13.248 µs** (−24 ns), 10 µs
**10.160 → 10.176 µs** (+16 ns). Nothing else in the file moved — the other 20 cells, `threshold_v`,
`averages` and the geometry are as locked in the previous entry. `profile_sha8` moves
**48de8676 → 6339c35e**. Nothing was ever recorded against 48de8676, so the name `cal_2x11_v5d`
stays unambiguous in practice despite having carried two hashes; the profile's `notes` records both.

**Why.** As hand-placed, cell 4 read 491.4 mV on the 100 µs band against 507.2 mV on the 10 µs — a
**3.16 % cross-band mismatch**, against 0.26 % on v5b. Cells 1–5 are the amplitude anchors, matched
across bands precisely so that cell index *n* means the same point on the decay in either band, and
cell 4 was the one bending that. The previous entry recorded it as a known wart left in place; it is
cheaper to close now than to bake into every corpus row, so it was closed before recording starts.

**How the step sizes were derived.** Both bands were trimmed onto the 500 mV cross-band consensus
using the measured local log-slopes either side of cell 4 — **0.73837 nepers/µs** (cells 3–4) and
**0.78010** (cells 4–5), from the same air window the previous entry's table came from. Both
resulting delays land exactly on the 8 ns PWM grid with no rounding compromise. Gaps become
1.936 / 0.744 / 1.112 / 1.840 µs on the 100 µs band and 1.880 / 0.712 / 1.088 / 1.784 µs on the
10 µs — the knee stays tight, which was the point of v5d.

**Predicted result: 500.1 / 500.9 mV, a 0.15 % mismatch** — down from 3.16 %. **These two numbers
are calculated, not measured**, and are flagged as such in the profile's `notes`; every other value
in that table is measured. They want confirming against a fresh air window before the corpus is
recorded, and the `notes` block corrected if the bench disagrees.

**Details.** Re-validated against the firmware's own `compute_pulse_duties` / `pulse_duties_valid`:
all 22 cells on the 8 ns grid, both duties inside 16 bits with sample strictly after drive, delays
strictly increasing and `threshold_v` strictly descending; the 10 µs band's last cell keeps its
96 ns (157 counts) of margin. As before, reload the profile in the tool before recording so the
corpus is stamped against **6339c35e**. (2026-08-13)

### findings — 2026-08-13 — delaycal and classviz are not at the same thermal state; classviz is the reference

**Bench observation.** Coming straight out of a `pimd_delaycal` calibration into `pimd_classviz`,
the band mean is still falling — the board is still warming. The two tools are not at the same
thermal state at handover, and delaycal is the cooler of the two. Recorded as an observation, not
a defect: nothing misbehaves, and no change is proposed.

**Corroborated from the v5d handover.** delaycal saved `cal_2x11_v5d` at 19:34:44 reporting board
**47.3 → 47.2 °C**. classviz opened its session 19 s later at 19:35:03 reporting **48.0 °C** — already
0.8 °C higher at handover — and the board then climbed to **49.6 °C** by 19:46, i.e. **+1.5 °C after
the handover and +2.4 °C above delaycal's last reading**, before flattening. Over the same span the
100 µs band mean fell **816.9 → 806.8 mV (−1.24 %)** and was still declining at t = 600 s.

**The drift is band-asymmetric.** The 10 µs band mean was essentially flat across the same window
(812.6 → 813.9 mV, +0.16 %) while the 100 µs band carried all of the decline. That is consistent
with the 100 µs band carrying the dissipation — 31.25 % duty against the 10 µs band's 25 % (§12,
and the U1 thermal work in the entries below).

**Confound, stated for honesty.** Pack fell 20.78 → 20.58 V across the same window, and pack droop
and warming push the band mean the same way (43–51 mV/V, §12). This session cannot separate the two
contributions; the handover temperature step is direct evidence, the band-mean decline is
consistent with it but not attributable to thermal alone.

**Consequence for the workflow.** A profile's anchors are *cut* in delaycal at a cooler board than
the state it will be *operated* in, so **classviz is the authority for a profile's measured
voltages**. That is how `cal_2x11_v5d`'s measured table was produced — from a classviz air window at
board 49.0 °C, not from delaycal's own readout — and it is the likely reason classviz figures and
delaycal figures for the same cells do not match exactly. (2026-08-13)

### src/data/profiles/cal_2x11_v5d.json — v5d — cell 4 re-cut bench-confirmed; all cells measured; sha8 c42a5f1e

**What changed.** Notes text only — **the delays and `threshold_v` are byte-identical to
`6339c35e`**. The two predicted numbers for cell 4 are replaced with the measured ones, the whole
air table is re-taken at steady state against the re-cut geometry, and the profile is no longer
carrying any unmeasured value. `profile_sha8` moves **6339c35e → c42a5f1e**.

**Cell 4 confirmed.** Predicted 500.1 / 500.9 mV at 0.15 % cross-band; **measured 498.9 / 499.4 mV
at 0.09 %**. Prediction error −1.2 / −1.5 mV (−0.24 % / −0.30 %), both low and consistent with the
pack having fallen 20.70 → 20.17 V between the two measurements. Against the 3.16 % it was
hand-placed at, **cell 4 is now the tightest-matched anchor in the profile** — better than
predicted.

**Measured in air at steady state** — 1 666 sweeps over 93 s, zero flagged rows, pack 20.17 V,
board 49.4 °C (`session_20260813_200336`, fw v4.37, classviz v1.79):

| cell | thr | 100 µs | 10 µs | cross-band |
|---|---|---|---|---|
| 1 | 4.700 V | 4680.0 mV | 4696.0 mV | 0.34 % |
| 2 | 1.900 V | 1874.3 | 1898.5 | 1.28 % |
| 3 | 1.150 V | 1133.2 | 1151.0 | 1.56 % |
| 4 | 0.500 V | 498.9 | 499.4 | **0.09 %** |
| 5 | 0.125 V | 123.0 | 124.2 | 0.91 % |
| 6 | ord | 79.0 | 77.9 | 1.32 % |
| 7 | ord | 62.5 | 69.9 | 11.32 % (null minimum, band-dependent by design) |
| 8–11 | ord | 91.8 / 111.8 / 112.3 / 112.0 | 92.0 / 108.0 / 109.9 / 111.0 | 0.24–3.45 % |

Air std dev 0.07–0.88 mV per cell on the 100 µs band and 0.05–0.23 mV on the 10 µs.

**Pack sensitivity, two measurements.** The same cells at pack 20.70 V / board 49.0 °C read
4685.8 / 4698.4 mV on cell 1 against 4680.0 / 4696.0 mV at 20.17 V / 49.4 °C. Both cuts sit near
the **bottom** of the §12 clean window; on a fuller pack the cells read higher (43–51 mV/V), putting
cell 1 near 4.85 V at 24 V against the 5.000 V full scale.

**Three hashes, no corpus behind any of them.** The file has carried 48de8676 (cell 4 hand-placed,
nothing recorded), 6339c35e (cell 4 re-cut, notes carrying the predictions — the two air validation
sessions are stamped with this one) and now c42a5f1e. Since only the notes text moved between the
last two, anything recorded under 6339c35e is *physically* comparable to anything recorded now, but
the `(profile_name, profile_sha8)` guard cannot know that and will group them separately (§10).
**Reload the profile before recording the corpus.**

**Housekeeping.** Superseded profiles `cal_2x11_v5`, `cal_2x11_v5a` and `cal_2x11_v5b` are removed
from the working tree — `cal_2x11_v5d` is the only profile in `src/data/profiles/`. They remain in
git history and can be restored if an old recording ever needs its geometry re-read. All session
dumps in `src/data/sessions/` were cleared at the same time; that directory is gitignored, so those
raw recordings are gone rather than archived, and the measured tables in this file and in the
profile's `notes` are now the only surviving record of them. **Note that DESIGN §10 still names
`cal_2x11_v5a` as the operating profile** — it is regenerated from this changelog by the human
consolidation pass (§18) and has not been re-run since v5b. (2026-08-13)

## Archive — consolidated 2026-08-13 (Doc-rev 2.6)

### src/data/profiles/cal_2x11_v5a.json — v5a — 100 µs band anchors re-cut on the extractor rig

**What changed.** A re-cut of `cal_2x11_v5`'s amplitude-anchored early cells. On the 100 µs
band cells 1–5 move later — 10.792 → 11.016, 11.904 → 12.192, 13.032 → 13.256,
13.912 → 14.152, 14.816 → 15.064 µs — and on the 10 µs band they move by ±0.03 µs
(8.040 → 8.016, 9.120 → 9.152, 10.208 → 10.176, 11.064 → 11.040, 11.984 → 11.960 µs), which
was already on target. **Cells 6–11 are untouched on both bands**, geometry is unchanged at
2 bands × 11 cells, and `averages` stays 32. `cal_2x11_v5.json` is retained, not deleted.

**Why.** v5's carried delays were cut at board 70.3 °C — a temperature the permanent 40 mm
extractor can no longer reach, since it plateaus near 47.8 °C. On the cooler board the 100 µs
band sat 15–25 % above its amplitude anchors and could not be waited back into place: the
anchors are voltages on the decay, and the decay itself moved. Re-cutting the delays is the
only way to put cell *n* back on the voltage it is defined as.

**Result, measured in air after the re-cut.** 100 µs band anchors landed at
+0.8 / +2.6 / +3.3 / +4.4 / +7.9 % against +14.8 / +24.9 / +21.1 / +22.6 / +21.8 % before.
Cross-band matching on cells 1–5 — the profile's stated invariant, that cell index *n* is the
same point on the decay in either band — went from 16 % mismatch to 0.4–5.3 %.

**Details.** All 22 cells were validated against the firmware's own `compute_pulse_duties` /
`pulse_duties_valid`: every delay an exact multiple of the 8 ns PWM grid, both duties inside
16 bits with sample strictly after drive, delays monotonic and `threshold_v` strictly
descending. The 10 µs band's last cell keeps its 96 ns of margin, unchanged from v5. The
profile's `notes` field still carries v5's "DERIVED ON PAPER / NOT swept" preamble forward
verbatim, which no longer describes this file — not corrected here. `profile_sha8` is
**7730b4e3**, already stamped into recorded session dumps and corpus rows, which is why the
file has to be in version control for those recordings to mean anything. (2026-08-13)

### src/pimd_classviz.py — v1.79 — warm-up countdown by the temperature gauge, temp colour steps, and the last two Analysis splitters persist

**What changed.** Three operator-facing items on the capture strip and the Analysis tab.

*Warm-up countdown.* The board-temperature gauge gained a caption row carrying `warm in M:SS` —
the time left before effective soak reaches `WARMUP_SETTLE_S` — mirroring the battery gauge's
`volts · time left` caption directly opposite it. It fills only while streaming with time still
to serve and clears once served, so it costs nothing on the strip for the rest of the session.
Driven from `_rate_timer` at 1 Hz, which is the resolution the text needs; `_redraw`'s 30 Hz
would repaint the same second thirty times.

*Gauge geometry.* `BarGauge` now mirrors `BatteryGauge`'s metrics exactly — 170×52 instead of
170×24, the same body rect (giving up the same width the battery spends on its nub, so the two
outlines are one rectangle in two places), the same 11 pt bold reading, the same 15 px caption
row. Previously the two gauges sat side by side sharing neither height nor centre line, and the
temperature read two points smaller than the pack percentage.

*Temperature colour steps.* `BarGauge` gained an optional `thresholds` list — the bar takes the
colour of the highest threshold the reading has reached — and the temp gauge is built with
yellow at `TEMP_WARN_C` 50 °C and red at `TEMP_CRIT_C` 60 °C, keeping its normal blue below 50.

*Telemetry age.* The sensor-age label reads `telemetry 50 s ago` rather than a bare `50 s ago`,
which alongside two gauges and a countdown read as the age of whichever one you looked at last.

*Splitter persistence.* `analysis_main_split_sizes` and `analysis_right_split_sizes` now save
and restore alongside the `left`/`row1` pair that already did.

**Why.** The countdown and the gauge answer two different questions that were easy to confuse.
Temperature says how hot the board is; it does **not** say whether the rig is ready, because
DESIGN §3 is explicit that the DS18B20 reaches its final reading well before the signal settles
— on 2026-08-13 the board sat at 43–46 °C while band 0 was still drifting for a further ~3 min.
Putting the countdown beside the gauge is what makes that distinction visible at the moment of
capture. 50 °C is "hotter than this rig normally runs" and worth a look rather than an alarm:
the extractor plateaus the board near 47.8 °C. On the splitters, `main_split` is the vertical
divider that sets the heatmap panel's **width** — `left_split` only sets its height — so it was
the one divider on the tab whose position was discarded on every launch.

**Details.** The threshold colours are given as hex, **not** as the `_HL_YELLOW`/`_HL_RED`
constants they match. Those are Qt *stylesheet* strings — `'rgb(246,  97,  81)'` — and neither
parses as a `QColor`: it returns an invalid colour and the bar paints **black** with the dark
reading text unreadable on top. Caught by rendering the gauge and looking at it rather than by
reading the value back; both the yellow and the red step were affected. `BatteryGauge` already
used the `'#f66151'` hex form for the same red, for the same reason.

Both new time readouts reduce to whole seconds before splitting into `M:SS`; formatting the raw
float rendered 359.99 s as "5:60", and the same slip was fixed in v1.77's Soak span, which showed
59.9 s as "0:60". An earlier revision of the countdown was a standalone `QLabel` with a filled
yellow background; it was dropped for the caption because a colour block on that strip shouted
over the reading it was qualifying and collided with the age label. That version also guarded its
show/hide on `isVisible()`, which reports False whenever the Analysis tab is merely not the
current tab — a guarded hide would have been skipped in the background and the label would have
appeared on switching to the tab. The caption has no such state: it is derived from the current
soak every tick, so it also returns on its own if a new streaming run restarts the soak.

`pimd_gui.py` has its own copy of `BarGauge` and is deliberately not touched, so its temperature
gauge keeps the old geometry and no colour steps. Splitter restore reuses the existing
child-count length guard. Verified against a driven window: both gauges report 170×52 at the same
y, the colour ladder steps exactly at 50.0 and 60.0 and renders correctly at each, the caption
fills and clears across the start/stall/stop states, and a dragged main/right divider round-trips
through save and reload unchanged. (2026-08-13)

### src/pimd_classviz.py — v1.78 — FIX '# capture:' lines never carried their window spans

**What changed.** `# capture:` lines now actually contain the `tgt=` / `air_before=` / `air_after=`
frame-window spans they were designed to carry. The bounds are snapshotted into the stats dict
when the signature is computed (`_sig_window_spans()`) and passed to `_append_capture()`, instead
of being read off `self._sig_target` / `_sig_air_before` / `_sig_air_after` at write time.

**Why.** Those three slots are already `None` when Save runs. `_sig_finish_air_trail()` drops them
the instant the stats exist — deliberately, so the readout and Save gating go inert while the
Save/Ignore decision is pending — and Save happens after that. So v1.68's `span()` helper always
saw `None`, its `if s:` guard skipped every field, and the line went out as bare
`capture_id/session/n_central`. Silent, because a spanless line is also the legitimate output
when nothing is recording. **Every session dump on disk is affected**, and `pimd_features` v13's
exact corpus-row → frame-window join — the entire point of the line — has had nothing to bind to
since the day it was written. The v1.68 comment at the call site asserting the buffers were
"still populated" was describing an ordering that was never true on this path.

Found while reconstructing which frames a capture came from: a band-0 excursion in
`session_20260813_155623` was initially read as a cooling artefact and turned out to be the
spanner on the coil (correlation r=0.9996 against its own recorded delta vector). The spans would
have made that unambiguous immediately; `captured_at` is stamped at save time, ~18–19 s after the
target window closes, which is exactly the confusion the line exists to prevent.

**Details.** Full window bounds, first to last frame, unchanged in format and unit (PC epoch
seconds, the same clock as `pc_wallclock`) — so `pimd_features._parse_capture_content` reads them
with no change, verified round-trip. The reduced slice is the central 60 % and stays recoverable
from `n_central` on the same line. `windows` is additive in the stats dict and every consumer
reads named keys, so nothing else sees it. Verified against a driven capture cycle with the slots
explicitly cleared first: both-anchor captures write all three spans, single-anchor captures write
`tgt`+`air_before` only, and an absent/empty `windows` still writes the line without spans — the
mark and capture_id are never lost. The geometry-mismatch path returns an error dict with no
`windows` and is `.get()`-safe. (2026-08-13)

### src/pimd_classviz.py — v1.77 — captures record board temperature and soak; the readout warns while the board is still warming

**What changed.** Every signature saved to a corpus now carries three more columns:
`temp_c` (the DS18B20 reading at capture time), `streamed_s` and `stalled_s` (how long this
classviz session had been streaming, and how much of that the firmware was silent). Both corpus
write paths pass them. The signature readout gained a **Soak** span on the same green/amber
ladder as the existing quality fields, showing effective soak as `M:SS` and appending
"warming" below the DESIGN §3 warm-up window (`WARMUP_SETTLE_S`, 360 s); a tooltip explains
what the number is. It is a warning only — the capture still saves.

**Why.** The corpus recorded the covariate DESIGN §3 calls weak (`pack_v`, ~1 mV/V) and
discarded the one it calls dominant — thermal drift, ~10× supply, with §17.11/§17.14 showing the
operating point moving with board temperature while pack voltage barely registers. classviz has
written `temp_c=` on every `# pack_v:` session-dump line since v1.72, but it never reached a
corpus row, so an offline review had to cross-reference the dump by timestamp to recover the one
variable most likely to explain a capture. Soak is carried alongside because §3 is explicit that
the DS18B20 settles well before the *signal* does and "is not a readiness indicator": the sensor
reading alone cannot separate a warm capture from a cold one, and warm-up from cold is ~6 min.

**Details.** `streamed_s` and `stalled_s` are stored as a pair and never as their difference,
following the rule already stated at `_soak_fields()` — `streamed_s` alone counts a silent
source as streamed, which is DESIGN §14.7 (70 minutes of zero data logged as streamed after the
2026-08-12 lockout). The new `_effective_soak_s()` takes the difference, clamped at 0, and the
warm-up gate reads *that*, not the raw run clock: a 70-minute all-stalled session correctly
reports 0 s and shows "warming". `_board_temp_c_value()` returns None rather than 0.0 when the
sensor is silent, mirroring `_pack_v_value()`, so a blank column stays distinguishable from a
freezing board. `_scan_editable_signature_file()`'s v1.67 bounds guard became an `opt()` helper
covering all four optional trailing fields, so the 25-column v1 corpus and the 27-column v3 and
20260813 corpora all still open — verified, 66 / 188 / 2 signatures, no IndexError. Appending to
one of those files still writes that file's own column count (`_corpus_fields_for_path`,
unchanged), so no corpus goes ragged; only newly created files get the 30-column schema.
Nothing in the acquisition, protocol or reduction path is touched. (2026-08-13)

### src/pimd_features.py — v15 — temp_c / streamed_s / stalled_s corpus columns

**What changed.** `CORPUS_HEADER_FIELDS` gains `temp_c`, `streamed_s`, `stalled_s`, appended
after `tilt_deg`; `build_rows()` and `build_wide_row()` take them as additive keyword arguments
defaulting to None and write blank rather than 0; `WIDE_TAIL_FIELDS` matches. The schema
docstring documents what each column is — and what it is not. The reduction, segmentation and
`pack_v_at()` paths are deliberately untouched: there is no `temp_c_at()` interpolator, and the
session-dump → corpus route is unchanged.

**Why.** Schema-owner half of the classviz v1.77 change above; see there for the measurement
argument.

**Details.** `tilt_deg`'s "MUST stay last" comment was wrong the moment three fields followed
it, so the rule is restated as what it actually is — append-only, with every optional trailing
read bounds-guarded, the guard being index-based rather than last-field-based and so
indifferent to how many columns follow. The docstring is explicit that `temp_c` is a sensor
reading and not board thermal state (the DS18B20 sits on the load resistor, is blind to the
regulator die, and §3 records 1.8 % spread on band 0 at the same indicated temperature), and
that its absolute scale is epoch-bound — it reads ~8 °C hotter since the 2026-08-13 extractor,
so readings either side of that date are different quantities. The `# pack_v:` line's
documented form was also corrected: it has carried a `temp_c=` field since classviz v1.72 and
the docstring still showed the v1.66 three-field form. (2026-08-13)

### src/pimd_corpus_check.py — v1.10 — the three v15 columns are optional on read

**What changed.** `OPTIONAL_FIELDS` gains `temp_c`, `streamed_s`, `stalled_s`. Nothing else —
no check, pass band or threshold is altered.

**Why.** `CORPUS_FIELDS` *is* `pimd_features.CORPUS_HEADER_FIELDS` and `REQUIRED_FIELDS` is the
set difference against `OPTIONAL_FIELDS`, so growing the schema without this line would have
made three columns mandatory and rendered every corpus on disk unloadable on sight. This is a
keep-it-working companion to features v15, not new work on the checker — whose thresholds
remain epoch-bound to the 2026-07-23 corpus and are knowingly left alone.

**Details.** Verified inert: output on all three corpora on disk is byte-identical to v1.9's,
including the v3 corpus's 229 undiagnosed FAILs. A file written with the v15 schema loads and
exits 0. (2026-08-13)

### src/pimd_classviz.py — v1.76 — Band Mean vs Time splits into early (blue) / late (red) at a selectable sd index

**What changed.** The Analysis tab's *Band Mean vs Time* strip gained a second mode. Off (the
default, and unchanged in every respect) it is the single black all-cell average it has always
been. On, it draws **two** curves of the same quantity taken over two halves of the delay ladder —
**early cells blue, late cells red** — divided after the sd index in a new spin box. The spin box
is 1-based and reads "last early cell": at 5 on `cal_2x11_v5`, blue is sd 1–5 and red is sd 6–11.
Both bands stay averaged into each curve, exactly as the unsplit curve averages them; the split is
over cells only. A legend beside the control names the two colours and their sd ranges, and the
spin box's tooltip gives the delay spans either side of the divider (per band, not averaged — the
two bands' ladders are different times at the same index).

**Why.** The single average sums the two ends of the ladder that carry *opposite* information.
Early cells split the families by **polarity** and late cells by **decay rate** (DESIGN §2, §13) —
so a target that pushes the early cells one way and the late cells the other is precisely the case
the all-cell mean cancels to nothing. Splitting at the operator's chosen sd makes the
non-ferrous/ferrous divergence visible as two traces pulling apart in time, on the chart that is
already being watched during a capture cycle. Default divider 5 is `cal_2x11_v5`'s
amplitude-anchored early zone (DESIGN §10's zone breakdown), i.e. the boundary the profile was
designed around rather than an arbitrary midpoint.

**Details.** Each curve is normalized independently, so Auto subtracts each curve's own window
mean — the same rule `_normalize_group` already applied to the single curve, which makes the read
the *shape* of the two excursions against each other rather than their DC offset; a Manual ref
subtracts one shared value from both and keeps the offset. The divider is clamped to
`1..n_cells-1` so neither side can come out empty, and the range is rebuilt on every profile
change. The remembered value follows the Family Plane's v1.49 band-pair rule: a clamp under a
narrower profile is display-only and never overwrites the operator's choice, and it is the
preference — not the possibly-clamped spin box — that `classviz_settings.json` persists
(`analysis_strip_split`, `analysis_strip_split_sd`). Corpus-template overlay lines on this strip
follow the mode too: one reference line per curve drawn, over the same cells, since an all-cell
average is a reference for neither half once the strip is split.

No acquisition, protocol, profile or recorded-data path is touched — this is display only, and the
unsplit mode's numbers are bit-identical to v1.75's. Bench-verified offscreen against a synthetic
frame stream: opposite-sign early/late ramps that cancel to a flat line unsplit come apart to
−39.0 / +48.8 mV split, dividers at both extremes draw two finite curves, and a wide→narrow→wide
profile round-trip restores the divider. (2026-08-13)

## Archive — consolidated 2026-08-13 (Doc-rev 2.5)

### findings — 2026-08-13 — the 40 mm extractor validated on the bench: noise −26 %, warm-up 10 → 6 min, U1 safe at 3.125 kHz

**Four sessions, one code path, `cal_2x11_v5` (`43617fed`) throughout.** Three cold-start runs on
the extractor (`111223`, `115209`, `125730`, fw 4.37) against the 2026-08-12 38 mm blow-on baseline
(`100209`, fw 4.35). The statistic is the one §3 already quotes — **32-sweep σ per cell** — and the
method is validated rather than assumed: re-running it on the baseline reproduces §3's documented
ppm figures **to the digit**, ch0 → **93.8 ppm** and ch11 → **37.9 ppm** against §3's "93 vs 38".
So §3's ppm figures are *raw* 32-sweep σ, and everything below is the same statistic. σ is also
reported **detrended** (σ about a least-squares line within each 32-sweep block), which removes
in-window thermal drift and is the metric used for comparisons, because a settled rig and a warming
rig are otherwise not comparable.

**Noise — the fan improved the floor by ~26 %, and this one is not pack-confounded.** Detrended σ,
null/pedestal cells, warm-up excluded, 2.5-min buckets:

| condition | n | pack range | σ (µV) | sd | sem |
|---|---|---|---|---|---|
| 38 mm blow-on + USB toroid (08-12) | 30 | 21.10–23.32 V | 50.9 | 6.4 | 1.2 |
| 40 mm extractor + USB toroid | 7 | 19.61–20.93 V | 44.9 | 4.7 | 1.8 |
| 40 mm extractor, USB toroid out | 15 | 21.96–22.97 V | **37.7** | 2.2 | 0.6 |
| 40 mm, both toroids out, power cable −27 cm | 5 | 21.26–21.72 V | 42.4 | 1.8 | 0.8 |

Row 3 against row 1 is **−13.3 ± 1.3 µV** over **overlapping** pack ranges (row 3's window sits
inside row 1's), so it is not a pack-state artefact; the toroid-matched pair (rows 1 vs 2) still
favours the extractor by **6.0 ± 2.1 µV** despite being taken 2 V lower on the pack. **Bucket
scatter fell 6.4 → 2.2 µV**, so the rig is ~3× more repeatable run-to-run, which matters more for
capture work than the mean. The commutating-motor / conducted-path objection raised when the 38 mm
fan went in is answered: the pack-fed extractor did not raise the floor.

**Warm-up is now ~6 min and a clean single exponential, against §3's 10 min.** The extractor fits
**τ = 1.15 min (r² = 0.982)** and **τ = 0.90 min (r² = 0.988)** on two independent cold starts,
within 0.2 % at **5.6** and **3.8 min**. The 38 mm baseline was **two-stage** — a fast drop then a
slow soak — fitting a single exponential badly (r² = 0.52 over the first 20 min) and still drifting
at 20–25 min. That shape change is what the extractor did: continuous bulk exchange suppresses the
slow case-soak stage. **Repeatability of the settled operating point is the striking number** — band-0
settles at **523.9** and **523.6 mV** across two runs, **0.06 % apart**, against the 38 mm rig where
a fan nudge was worth **3.7 %**. That is the permanent mount retiring §3's measurement-critical
variable, quantified: ~60× tighter.

**Thermal.** Zero flagged rows in **104 618 sweeps** across 27.3 + 47.0 + 23.3 min at 3.125 kHz,
including a run started at **24.48 V on a cold 22.2 °C board** — the worst U1 corner. The 27.3 min
run ended on the **19.0 V pack floor**, not on heat, and rested back **+2.17 V** (§12 records
+2.04 V, consistent). Sweep rate **17.83–17.88 Hz** against the baseline's 15.61 Hz — but that is
**fw 4.37 vs 4.35, not the fan**, and it is also above §10's recorded 16.1 Hz, so §10's figure wants
a re-measure. DS18B20 plateaus **47.8 °C** (extractor) vs **39.8 °C** (blow-on).

⚠ **The toroid experiment is NOT decidable from these runs, and the earlier reading of it was
wrong.** The USB toroid was removed before `115209` and the power toroid removed plus the power
cable shortened 27 cm before `125730`. Taken at face value the table says removing the USB toroid
cut σ by 7.2 µV — but **each condition occupied a disjoint pack band** (19.6–20.9 / 21.3–21.7 /
22.0–23.0 V, no overlap between any two), so the hardware change is perfectly collinear with pack
voltage and the two cannot be separated. An attempt to break the confound from within-session σ-vs-pack
trends failed because those trends **contradict each other** across the four sessions
(r = +0.61, −0.53, +0.64, −0.78) — bucket σ is too noisy to establish a pack law in either
direction, which also means **§3's "noise does not rise as the pack falls" is neither confirmed nor
contradicted here; flagged, not settled.** What *is* safe: every toroid-out measurement is at or
below every toroid-in measurement, so **nothing indicates either toroid was doing useful work** —
but "removing it improved things" is not established. **To settle it, each condition must sweep the
same pack window** — run each from full charge to the 19.0 V floor (~45 min each) and compare at
matched voltage. Today's runs stopped at 20.95 V and never overlapped. Note also that `125730`
changes **two** things at once (power toroid *and* cable length), so even with matched packs those
two would still need splitting. (2026-08-13)

---

### hardware — the cooling fan is now permanent: a 40 mm 24 V extractor in the case lid, switched and fused

**A 40 mm 24 VDC fan has been fitted permanently to the case**, mounted above the FET, the
regulators and the load resistor, and running as an **extractor — it sucks, drawing air out over the
cluster** rather than impinging on U1's tab the way the temporary part did. It is **powered directly
from the pack through a switch and a fuse, and nothing else** — no regulation, same unregulated
pack feed as before. This supersedes the 25 V 38 mm fan fitted 2026-08-11, which was a loose part
blowing onto U1 from 50 mm. *(If both fans are in fact present rather than the 40 mm replacing the
38 mm, only this paragraph needs correcting — everything below holds either way.)*

**The measurement win is the mount, not the airflow.** The 2026-08-12 sweep found that nudging the
fan off the U1/FET cluster moved **band 0 by +3.7 %** — a smooth ~2.5 min thermal exponential that
fully reversed when the fan was put back, and the explanation for the unexplained band-mean rise
logged at 15:12. That made **fan position a measurement-critical mechanical variable** whose value
outweighed the entire pack discharge range, and it was carried in `DESIGN.md` §3 as a standing
warning. A case-fixed mount retires the variable: the geometry is now a property of the build
instead of where a loose fan was last left. This is the single largest repeatability gain in the
entry, and it is worth more than any thermal difference between the two fans.

**The switch does not create a fan-off state — it is the rig's own switch.** The fan runs whenever
the switch is on, i.e. whenever the detector is powered; **there is no operating state in which the
board pulses and the fan does not** *(operator, 2026-08-13, stated as final)*. The 38 mm fan's
"pack connected ⇒ fan running" interlock is therefore **preserved, not weakened** — the fan is
simply energised by the supply switch instead of by connecting the pack. The fuse additionally gives
the fan feed a fault path it never had. The 2026-08-11 operating rule stands unchanged and is now
structural rather than procedural: the 100 µs band at 3.125 kHz requires the fan, and the fan cannot
be absent while the band is running. §12's **620 streaming-minutes** figure still needs its
re-measure to state whether the fan was running, since the fan remains a continuous 1–2 W pack load
for the whole of any powered session.

⚠ **Four gates were raised here. Three were closed the same day by bench measurement — see the
findings entry above for the numbers and method; the status below is the summary.**

1. ✅ **RESOLVED — the extractor is thermally sufficient at 3.125 kHz.** Three cold-start runs on
   2026-08-13 streamed `cal_2x11_v5` for **27.3, 47.0 and 23.3 min** with **zero flagged rows in
   104 618 sweeps** and no rail collapse. One of them started at **24.48 V on a fresh pack from a
   cold board (22.2 °C)** — the worst U1 corner this gate asked for, full pack and maximum
   regulator drop, walked from cold. The 27.3 min run ended on the **19.0 V pack floor**
   (`PACK_VOLTAGE_TRIP_MV`), not on heat. 3.125 kHz is no longer provisional on this build. *(Still
   not done, and still worth doing while a lid is off: a thermocouple or IR read on U1's tab. The
   evidence here is "U1 never tripped", which is the outcome that matters but is not a die
   temperature.)*
2. ✅ **CONFIRMED, exactly as predicted — and the numbers are now on record.** The DS18B20 plateaus
   at **47.8 °C** on the extractor against **39.8 °C** on the 38 mm blow-on, from comparable cold
   starts. It reads ~8 °C *hotter* while the signal settles *faster and lower*, because the sensor
   sits on the load resistor and has lost the old fan's direct impingement. **Board temperatures
   either side of 2026-08-13 are different quantities and must not be compared.** It remains blind
   to the regulator die.
3. ✅ **RESOLVED for the fan — the noise floor improved, it did not regress.** Detrended 32-sweep σ
   on the null/pedestal cells, warm-up excluded: **50.9 ± 1.2 µV** on the 38 mm rig (pack
   21.10–23.32 V) against **37.7 ± 0.6 µV** on the extractor (pack 21.96–22.97 V) — a
   **−13.3 ± 1.3 µV** improvement measured over *overlapping* pack ranges, so it is not a pack-state
   artefact. The toroid-matched pair favours the extractor by **6.0 ± 2.1 µV** despite being taken
   2 V lower on the pack. Bucket-to-bucket scatter also fell from **6.4 to 2.2 µV**, i.e. the rig
   is ~3× more repeatable. The commutating-motor objection was real and is now answered by
   measurement rather than argument.
   **The fan-on/fan-off capture is withdrawn, not outstanding** — the fan is powered from the rig's
   own switch, so a fan-off streaming state does not exist to capture *(operator, 2026-08-13,
   stated as final)*. §14.8's separate gate is untouched by any of this.
4. **The enclosure is now vented by construction.** §12 describes U1's dissipation as a problem
   specifically *"inside a sealed shielded enclosure"*; a permanent case-mounted extractor makes the
   vents permanent too. What that costs the shielding is a mechanical/EMI question **not determined
   here**, and it now applies to the shipped build rather than to a temporary bench arrangement.

**On the 24 V rating against the pack window.** The pack-tracking argument carries over unchanged
and still points the right way — U1's heat is `(V_pack − 15) × I`, worst at a full pack, and fan
speed rises with pack voltage over the same span, so the weakest cooling coincides with the lightest
load. At the **19.0 V** floor the fan sees ~79 % of its 24 V nameplate, still clear of the ~60 %
where a DC fan stalls; at a full 6S pack (~25.2 V) it runs slightly **above** nameplate, which is
ordinarily harmless for a DC fan but is worth stating rather than discovering. Favourable, and still
not by design.

**Doc follow-up for the next consolidation pass** *(not applied here — `DESIGN.md` is not edited
directly)*: the **hardware-rev line** should replace "38 mm forced-air fan on the U1/FET cluster —
mandatory, fitted 2026-08-11, used in all cases" with the 40 mm case-mounted extractor and this
date; **§3**'s "The fan mount is measurement-critical" warning should be rewritten as *resolved by
the permanent mount* while keeping the 3.7 % figure as the evidence for why fan cooling moves the
operating point at all; **§3**'s noise-floor, warm-up and board-temperature figures all need
restating from the findings entry above (65 µV → ~38 µV, 10 min → ~6 min, and the DS18B20 plateau);
and **§10 / §15**'s "requires the cooling fan running" notes should record that the fan is on the
rig's own switch, so the requirement is structural and not an operator step. (2026-08-13)

---

### DESIGN.md — Doc-rev 2.4 — §13's pedestal corrected to the measured ~110 mV

`DESIGN.md` contradicted itself on the tail pedestal: §10's cell 9 read "~110 mV air pedestal"
while §13's span statement read "2.4 V down to the **~70 mV** pedestal". Resolved in favour of
§10 — human-directed, hence the Doc-rev bump.

**§10 is the measured one, three ways.** The pedestal was measured directly at **113.0 / 111.9 mV**
(band 0 / band 1) on a healthy frame after the +97 mV bias mod; §17.7 records the mod meeting its
design number at **predicted +111.7 mV, measured +112.8 mV**; and the profile-design work landed
the late cells "on the ~110 mV air pedestal" by cell 7–8. §13's ~70 mV matches **no recorded
pedestal measurement anywhere in this file or `DESIGN.md`**.

**Where the 70 came from — worth recording, because both candidates are real numbers that are not
the pedestal.** §17.7's own sentence continues "air's worst case moved from clipped to **67.2 mV**
above the 2.441 mV floor" — headroom above the noise floor, not a pedestal level. And the **null
minimum** measured 59 / 64 / 69 mV on the predecessor profile — genuinely the lowest voltage the
profile samples, but a different cell from the pedestal cells (§10 lists cell 7 as the null minimum
and cells 9–11 as out on the tail). Either way the span sentence had collapsed two quantities into
one phrase; §13 now names the pedestal only.

`README.md`'s delay-anchoring bullet had inherited the ~70 mV from §13 the day it was rewritten,
and is corrected with it. No measured value is dropped: 67.2 mV and the null-minimum depths keep
their own homes in §17.7 and §10. (2026-08-13)

---

### README.md — the profile description caught up with the rig

`README.md`'s technical description had drifted two profile epochs, in the same way and for the
same reason as the `USAGE.md` retired alongside it. Corrected against `DESIGN.md` §10/§13:

* **The Mode 2 bullet** claimed "the current locked profile (`cal_63_air_v1`) spans 7 pulse widths
  × 9 sample delays = a 63-cell matrix". Now: the 63-cell grid is named as what the **July 2026
  corpus** was captured on, and the current `cal_2x11_v5` is described as it is — 2 pulse widths
  (10 and 100 µs) × 11 delays = **22 cells at 16.1 Hz** *(measured)*, **not locked, no corpus**,
  with the 100 µs band's 3.125 kHz fan requirement stated.
* **The delay-anchoring bullet** claimed an amplitude ladder of **4.9 → 0.5 V**; §10's anchor table
  runs **2.4 V → 125 mV**. It also described delays as "deliberately avoiding the LC-ringing dead
  zones and the measured ~4.45–4.65 V noise keep-out zone" — that keep-out **no longer exists
  anywhere in `DESIGN.md`**, and §13 states the opposite outright: the profile spans the whole
  decay with no gaps and "there is nothing it has to avoid", sampling the null minimum deliberately.
  A retired *constraint*, not merely a stale number, so the clause is gone rather than renumbered.
  Rewritten around §13's two-scheme framing — amplitude anchors early where polarity separates the
  families, time anchors late where only decay rate does.
* **Three consequential mentions** that would have contradicted the above: the Highlights bullet
  ("63-cell" → "multi-band"), the Phase 3 roadmap line, and the *Faster response* roadmap bullet,
  which still read "nothing is cut yet" when 63 → 22 is exactly that cut — it now records the cut
  as made and names the open work as re-validating the narrowed grid against a fresh corpus.

**Flagged, not fixed.** (a) `DESIGN.md` disagrees with itself on the tail pedestal — §10's cell 9
says "~110 mV air pedestal", §13's span statement says "~70 mV pedestal". README follows §13 as the
whole-profile claim; the two should be reconciled at a consolidation pass. **[Resolved the same day
in favour of §10's ~110 mV — see the entry above; README's ~70 mV came from here and went with
it.]** (b) The hero image's alt
text still says "8×9 decay-space matrix" — left alone deliberately, as it captions one specific
historical frame rather than making a present-tense claim. (2026-08-13)

---

## Archive — consolidated 2026-08-13 (Doc-rev 2.4)

### USAGE.md — retired at v1.31 — the per-app file headers are the usage doc now

**Deleted `USAGE.md`**; its one irreplaceable section — the pipeline diagram and the typical
workflow ordering — is lifted into `README.md` as a new **Toolchain & workflow** section, and the
three `USAGE.md` references in `README.md` (repo layout, Documentation, the CC BY-SA licence list)
are gone with it. Recover the last version with `git show 798faef:USAGE.md` (v1.31, 2026-08-09).

**Why.** It had become a fourth history stream — file header lineage → `CHANGELOG.md` → `DESIGN.md`
→ `USAGE.md` — and it lost the sync race, in the way a doc that nobody's edit path passes through
always does. Measured at deletion, against source:

* **Wrong about the rig.** §1 named `cal_63_air_v2` (7 × 9 = 63 cells) as the operating profile.
  Reality is `cal_2x11_v5` (2 × 11 = 22 cells) — two profile epochs later, and the only JSON in
  `src/data/profiles/`. §6 meanwhile referenced the `cal_3x10_v1` turnover that §1 had not heard
  about, so the document contradicted the rig *and* itself.
* **Behind on every version it tracked:** mcu v4.27 → actual **v4.37**; gui v4.14 → **v4.18**;
  delaycal v1.47 → **v1.49**; classviz v1.72 → **v1.75**; features v10 → **v14**.
* **Internally inconsistent:** the §1 pipeline diagram said classviz v1.61 / features v7 /
  delaycal v1.29 while its own section headings said v1.72 / v10 / v1.47 — the tell that recent
  updates only patched whichever section was in front of the editor.
* **Silent on two shipped apps:** `pimd_rawlog.py` (v1.17) and `pimd_pack.py` (v1) had no section
  at all, and rawlog is now a primary capture tool.
* **~130 of its 691 lines were an inline changelog** duplicating this file. The 2026-07-30 pass
  above already flagged the consequence — USAGE.md v1.24/v1.25/v1.26 exist *only* in that inline
  block, putting three versions of history outside the single source of detailed history.

**What replaces it.** The per-app headers overtook it: mcu 129 lines, classviz 110, rawlog 106,
delaycal 94, gui 64 — carrying intent, the wire commands each app uses, the records it parses,
sentinel semantics, log formats, rationale, and the terse version lineage. They stay current
because they are colocated: the header is edited by the same change that alters the behaviour,
which is exactly the property `USAGE.md` could not have. The new README section is deliberately
**version-free and profile-name-free** — naming neither was what rotted `USAGE.md`, and
`DESIGN.md`'s header line already owns the version roster and says to bump it on every edit. It
now changes only when the *shape* of the pipeline changes.

**Consolidated the same day, Doc-rev 2.3:** §15's `USAGE.md` file-table row is dropped, and the
`README.md` row amended to record that it inherited the pipeline section while per-app detail went
to the file headers — so the table still says where the content went. (2026-08-13)

---

### src/pimd_classviz.py — v1.74 — FIX Load & Run never armed the soak/stall run state

`_finish_load_run_profile()` — the Load & Run path, which is **also** the v1.53 launch autostart and
therefore how most sessions actually begin — sends its own `Q`/`G` instead of going through
`start_stop()`, and never set `_stream_run_start_wall`. Everything in the v1.66 soak track keys off
that one attribute, so the failure was silent and total: the periodic emit is guarded on it
(`_update_pack_v_age` tick) and never fired, `_streamed_s()` returned only the banked total,
`_idle_before_s()` returned None, and the stream-stop banking was skipped so `_streamed_total_s`
stayed 0 for the life of the app. The same path also skipped the v1.64 per-run stall reset, so
back-to-back Load & Runs in one app session had the second inherit the first's stall total.

**Caught on `session_20260812_121058`**, a 38-minute run whose only soak lines were the header's
`session-open` and a closing `stream-stop` reading `streamed_s=0, stalled_s=113`. Effective soak is
defined as `streamed_s - stalled_s`, so that pair computes to **−113 s** — a negative soak, which is
the tell that the field is broken rather than merely surprising. (`stalled_s=113` was itself
correct: 59.768 s at 12:16:01 plus 53.281 s at 12:25:03. Its coincidence with the 113.259 s outage
in the morning's `session_20260812_100209` is exactly that, a coincidence — no counter leaks across
sessions.)

Fixed by factoring the run-arming out of `start_stop()` into **`_begin_stream_run()`** and calling it
from both entry points. In Load & Run it goes immediately after the `G`, *ahead* of `_apply_profile`,
because that can reopen the dump and the header's soak line reads `_stream_run_start_wall` to compute
`idle_before_s` — arming afterwards would record `unknown` permanently. A matching
`_append_soak('stream-start')` now brackets the run the way `start_stop()` already did. One helper
rather than two inline copies, so a third streaming entry point cannot drift the same way; the
docstring records what the drift cost so the next reader does not have to re-derive it from a
negative soak figure. No change to the wire format, the dump schema, or the acquisition path.

**Verified on the bench the same afternoon, and the failing case was caught too.**
`session_20260812_150333` (v1.74, Load & Run) opens with `session-open` *and* `stream-start`, then
emits `periodic` on the minute with `streamed_s=61`, `121`, … and a real `idle_before_s=747` — all
four symptoms cleared on the path that had never worked. The session immediately before it,
`session_20260812_145123` (v1.73), is the counter-leak predicted from the code and not previously
observed: it opens with **`stalled_s=113` already on the clock**, inherited from the 12:10 run in the
same app process, because Load & Run never ran the v1.64 per-run reset. Both halves of the bug are
therefore evidenced, one by its fix and one by a last example of itself. (2026-08-12)

### mcu/pimd_mcu.py — v4.36 — TEST BUILD: pack floor 21.0 → 19.0 V, re-arm 21.5 → 19.5 V

`PACK_VOLTAGE_TRIP_MV` 21_000 → **19_000** and `PACK_REARM_MV` 21_500 → **19_500**, to let the
detector be characterised below the DESIGN §12 working floor. **This is a deliberate, temporary
divergence from §12 and must be reverted before any pack that is meant to survive.** Both constants
moved together and must always move together: 500 mV of hysteresis is now the only thing the re-arm
level means, the old 21_500 having doubled as the §12 clean-window edge. Left at 21_500 against a
19_000 trip the hysteresis would have been 2_500 mV, and because the MCU is USB-powered and outlives
the rail, a latch at 19.0 V could not then be cleared by cycling the pack at all — only by unplugging
USB mid-test.

**Why the floor was in the way.** On `session_20260812_100209` the pack tripped at 21.02 V with the
+15 V rail still measuring **15.20 V on a DMM** — flat to 10 mV across a 24.69 → 21.37 V pack swing.
D4 is a shunt clamp with no series drop, so the L7815 sees the pack directly and needs ~17.2 V in.
The 21_000 trip was never a rail limit; it is cell protection, and the rail has ~3.8 V of headroom
left at the point the firmware stops.

**What it costs, and why the comment in the source is as blunt as it is.** The ClassViz SoC gauge
read 11 % at 21.02 V while an independent charger measured cells at 3.84 V (52–55 %). Both are
correct: `pack_soc_pct()` is a *resting* OCV curve being handed a *loaded* terminal voltage —
21.02/6 = 3.503 V/cell → 10.8 %, 3.84 V/cell → 56.2 %. Sag is real and large (the first 44 s of the
session show **24.69 → 23.84 V, an 850 mV load step at full charge**). But only four of six cells
were measured, and the arithmetic on the remainder — 21.02 − 4×3.84 = 5.66 V over two cells,
**2.83 V/cell** — was then **confirmed on the bench**. The string is badly imbalanced, so pack volts
÷ 6 does not describe it: at a 19_000 trip the weak pair reaches roughly **2.0–2.1 V**, under the
ICR18650-26C 2.75 V cutoff and into copper-dissolution territory, where the hazard appears on the
*next charge* rather than during the test. Corroborating evidence that the pack is not the 53 % the
charger implies: the discharge rate roughly doubled over the run, ~22 mV/min at t=35 min to
~55 mV/min over the last 15 — a knee, not a half-full pack.

Deliberately **not** done: no serial re-arm for the latch. The v4.28 hard latch exists because of an
actual over-discharge incident, and a below-floor test is precisely the run that wants it intact.
Also unchanged: `PACK_ZONES` / `PACK_WINDOW_LO_MV` in the four PC tools still paint the lockout floor
at 21.0 V, so the gauges will disagree with the firmware for the duration of the test build — left
deliberately, as the mismatch is a standing reminder that this is not the §12 floor. (2026-08-12)

> **Superseded 2026-08-13.** The "must be reverted before any pack that is meant to survive"
> warning above **must not be acted on**. It rested on a per-cell figure inferred from a partial
> measurement, which the 2026-08-12 sweep's direct readings did not support; the floor was decided
> kept on that day's results, and the pack in question has since been replaced. 19.0 V is the
> working floor, not a test-build divergence. The `PACK_ZONES` / `PACK_WINDOW_LO_MV` mismatch this
> entry signs off on was resolved on 2026-08-13 — those constants no longer exist. The firmware
> source comments that carried the same instruction have been reworded.

### mcu/pimd_mcu.py — v4.37 — FIX the unbounded IRQ-off BUSY spin that silenced the board on rail loss

Switching the +20 V rail off while the MCU stayed alive on USB used to silence the board
**completely** — no Mode 2 `W` records, no 60 s `P` telemetry, and not even the `PACK: rail absent`
line the failsafe exists to print — resuming as if nothing had happened when the rail returned. Long
treated as a convenient property for flashing and debugging with the high-power side off. On
2026-08-12 it cost a diagnosis: `session_20260812_121058` stopped dead at 12:48:55, **19 minutes
before anyone cut the power**, and left no pack voltage or board temperature across the event.

**Mechanism, and it is worse than "interrupts stop firing".** `read_raw_bytes_hold()` calls
`disable_irq()` and then spins on two unbounded, non-yielding loops (`while not busy_pin.value():
pass` / `while busy_pin.value(): pass`); `enable_irq()` is only reached ~160 lines later after the
PWM writes. With the ADC unpowered, BUSY parks and the MCU spins there forever **with interrupts
globally masked** — which masks USB CDC too, so even already-queued stdout cannot drain. That is why
the silence was total rather than merely missing sweep records. Compounding it, `service_sensors()`
is the only path to the pack ADC, the DS18B20, the `P` line and `_pack_voltage_trip_check` (whose
`pack_mV < PACK_ABSENT_MV` test is the sole rail-absence detector), and both its call sites are
downstream of a *completed* `read_raw_bytes_hold()`. **The missing `PACK:` message was therefore a
symptom of the bug, not evidence against it** — the detector was unreachable by construction.

**The fix.** Both spins are bounded by a new `BUSY_SPIN_LIMIT`; on expiry the function re-enables
IRQs *itself* and returns `None`. `acquire_mode2` treats `None` as "abandon the sample", sets
`state = 'rail_absent'` and breaks — before the boundary `freq()` writes, so the PWM is never
reconfigured for a discarded sample. This reuses the existing `if pack_voltage_lockout: break` idiom:
the `while` condition is already false, so one `break` leaves both loops. New `service_rail_absent()`
rests there with drive safe and resumes Mode 2 after `RAIL_RESUME_CONSECUTIVE` (3) checks at
`RAIL_RECHECK_MS` (1000) with the pack at or above `PACK_REARM_MV`. The main loop needed no
restructuring: it already calls `check_for_commands()` and `service_sensors()` every pass regardless
of state, so telemetry resumes the moment the state leaves `mode2_running`.

**The constant is the risk, and it is deliberately generous.** A *healthy* spin here is **1–2 ms, not
microseconds**: DESIGN §7 records the poll catching only ~1-in-6 BUSY-high windows, and v4.34
measured per-cell interpreter cost at ~2.3 ms "dominated by the BUSY sync" (`cal_63` cross-checks it
at 63 cells / 6.88 Hz = 2.31 ms/cell). The wait is also stochastic and scales with the PWM period, so
its tail is not knowable from source. **The regression to fear is a false abort mid-sweep, not a slow
one.** A decrementing local int was chosen over a `ticks_ms` deadline because a call per iteration
would roughly double the poll period, and poll period is exactly what sets how late the BUSY falling
edge is caught — late detection is the §7 mid-conversion-read mechanism that produces bit-truncated
outliers at 1/2 and 1/4 of true value, which the whole v4.16→v4.21 lineage exists to close.

**Bench-timed on this board before the constant was set** (RP2040-Zero, GP15, 50 000-iteration REPL
runs, spread < 0.03 % over 5 repeats):

| variant | µs/iteration |
|---|---|
| `b.value()` alone | 5.816 |
| pre-v4.37 spin (poll + `pass` body) | ≈ 5.816 |
| **bounded spin as shipped** (`n -= 1; if not n:`) | **9.024** |
| bound folded into the `while` condition instead | 9.008 — no cheaper, so the clearer form was kept |
| `for _ in range(N)` | 9.848 — **slower** as well as allocating |

`for/range` was rejected on the file's allocation-free doctrine (the v4.14 heap-churn lesson) and the
measurement independently confirms it as the worst option. `BUSY_SPIN_LIMIT = 2200` × 9.024 µs =
**19.9 ms**, the ~20 ms budget.

**The cost is bigger than the design estimate and is recorded rather than buried: the poll period
rises 5.816 → 9.024 µs, +55 %, against a planning estimate of +20–30 %.** Whether 3.2 µs of extra
latency in noticing BUSY fall matters cannot be settled from source — it needs the LTC2508 data-hold
window (no datasheet in the tree) or a scope. Note §7's ~1-in-6 catch rate predicts the visible effect
may be a **lower sweep rate rather than worse noise**, since a longer poll period should miss
proportionally more BUSY-high windows. The pre-change baseline to compare against is
**16.13 Hz on `cal_2x11_v5`** (measured from `session_20260812_100209`, 62.0 ms median). A before/after
run comparing sweep rate, per-channel σ and `gate_reject_count` is the acceptance test for this
change and had not been run when this entry was written.

**Also fixed, a pre-existing latent bug:** an exception raised anywhere inside the per-cell IRQ-off
section unwound to the Mode 2 handler with interrupts still masked, and that handler's first act is
`print()` — so the board would brick itself silent while reporting its own error. Interrupts are now
restored before the report.

**Behaviour changes on the wire.** `B` grows from 6 to 9 fields (additive; nothing in `src/` parses
it): `busy_timeout_count` answers "did this happen", `busy_spin_min_left` records how close a healthy
spin came to the cap — the field that turns the constant from a guess into a measured margin, and it
resets to the limit rather than 0 — and `rail_absent_ms_max` is the longest outage dwell.
`busy_high_count`, incremented but unchecked since v4.11, becomes meaningful: near-zero beside a
non-zero `busy_timeout_count` means the outage spanned the whole read window. Two new `PACK:` lines
and one new `ADC:` line; `PACK:` is already classified by all three PC consumers so no PC-side change
is needed, and neither new line contains the substring `lockout cleared`, which ClassViz keys its
latch-clear on. **`S` and `A<n>` are now refused while the rail is absent** — a real behaviour change,
made because their read paths still carry the unbounded wait.

**Deferred, with the residual stated plainly.** `read_raw_sample()` (needs a different abort contract:
it returns an int, so `None` would poison `acquire_raw_average`'s arithmetic) and Mode 1's
`acquire_filtered_data()` (a different mechanism — it waits on the DRL ISR with IRQs *enabled*, so a
`ticks_ms` deadline is the right tool there, the opposite conclusion to the hot path). The command
refusals make both unreachable in the case that actually gets hit, but **a rail cut *during* an
already-running Mode 1 stream or an in-flight `A<n>` still stalls telemetry.**

Validated offline: parses; no undeclared global writes anywhere in the file; the abort's `break`
verified by AST to sit inside the `for` nested in the `while` whose condition tests `state`; and
`service_rail_absent()` was executed against stubbed hardware across seven scenarios — normal
off/return cycle, the sub-second cadence gate, BUSY-dead-with-healthy-pack (stops, never
auto-resumes, so no thrash loop is possible), failsafe latching during entry (its `stop` wins),
lockout set (resume impossible), wire discipline (**one line across a simulated 10-minute outage**),
and a brownout return that correctly refuses to resume below `PACK_REARM_MV`.

**Bench-verified on hardware, and the spin cap had to move as a direct result.**

*Test A* — 5 min, `cal_2x11_v5`, 5377 frames: sweep rate **18.18 Hz against the 16.13 Hz v4.35
baseline**, i.e. no throughput cost at all from the +55 % poll period, which settles the concern the
window arithmetic predicted would be benign. Successive-difference noise **17–20 µV on the low
channels and 48/27 µV on ch0/ch11**, against 24–26 and 59/32 µV that morning — same or better, so the
extra 3.2 µs of latency in noticing BUSY fall is not causing mid-conversion reads. One gate rejection
in ~118 k cell reads, no emit blocks, `busy_timeout_count` 0. (The +12.7 % rate is **not** claimed as
caused by v4.37: the baseline came from a ClassViz session and this from a thin capture script, at
different pack and thermal state. The claim is only that there is no regression.)

*Test A also failed the constant, which is what `busy_spin_min_left` was added to catch.* It returned
**887 of 2200** — the worst *legitimate* spin used 1313 iterations = **11.85 ms, 60 % of the budget**,
a margin of 1.68× rather than the ~10× the constant was sized for. Since spin 1's wait scales with
the PWM period, the DESIGN §8 floor of 2 kHz projected to ~18.5 ms, or **93 % of a 2200 cap**. The
constant was raised to **6000** (54.1 ms) before proceeding.

*Test E* — 10 min at the lowest frequency the hardware allows, two bands at 2000/2500 Hz with 100 µs
pulses (22.5 % mean duty, *below* `cal_2x11_v5`'s 28.1 %, so passive-cooling safe), two bands rather
than one so band-boundary `freq()` resyncs are included. 3821 frames at 6.37 Hz.
**`busy_timeout_count` = 0 — no false aborts**, plus `gate_reject` 0, `gate_reprime` 0, `emit_block`
0. `busy_spin_min_left` **4079 of 6000**: worst legitimate spin **1921 iterations = 17.34 ms**,
margin **3.12×**, 68 % of budget left.

Two things worth keeping from that. The period-scaling model **predicted 2052 iterations and the
board delivered 1921 — accurate to 6 %**, so spin 1's tail can be projected to a new profile rather
than rediscovered. And at the original 2200 the same worst case would have consumed **87 % of the
cap**, so 2200 was not merely thin, it was a false abort waiting for an ordinary run-to-run
excursion. The counter did the job it exists for on its first outing.

*Test C — the acceptance test: a real pack switch-off on `cal_2x11_v5`, and it passes on every
criterion.* The 1 Hz failsafe saw the rail go first (`PACK: rail absent (5239 mV)`), then the spin hit
its cap and the sweep aborted **within the same sweep** — `SAFE: Drive OFF / Sampling OFF / Interrupts
OFF` followed by `PACK: rail lost mid-sweep at 4962 mV`. Pre-v4.37 that gap was unbounded and the
board simply never spoke again.

**The property this change exists to create, demonstrated:** with the rail off, **three `P` telemetry
lines arrived 60 s apart** (t = 61 s, 121 s, 181 s), and their `board_temp_dC` field went
**26.1 → 35.2 → 30.1 °C** under a finger on the DS18B20 and after it was removed. Live conversions,
not a stale value being reprinted — which is precisely the distinction the 2026-08-12 12:48 outage was
hidden behind. `V` answered immediately with the rail down. `S` and `A32` were both refused with the
new messages naming the reason.

On restore: `PACK: present again at 23698 mV — failsafe armed`, then **2.1 s later** (the 3 × 1 s
debounce) `PACK: rail back at 23728 mV for 168 s — resuming Mode 2, profile 5`, then sweeps at
15.9 Hz. `B` afterwards read `busy_timeout_count` **1** — exactly one abort — and `rail_absent_ms_max`
**168057 ms**, matching the announced 168 s outage to the millisecond.

One striking incidental: `busy_spin_min_left` returned **4687 of 6000**, i.e. a worst legitimate spin
of **1313 iterations — bit-for-bit the same figure Test A measured** on the same profile against a
different cap. The tail is not random jitter; it is a reproducible structural event, almost certainly
the band-boundary `freq()` resync. That makes it projectable, and it is why the two-band Test E
profile was chosen over a single band. (`emit_block` 11 / `gate_reject` 28 / `gate_reprime` 9 in this
run are artefacts of the test harness — the probe and sleep phases stop draining USB CDC, and the
collapsing signal at the cut is exactly what the outlier gate is for. Both read zero in Tests A and E.)

Flashed and verified by sha256 at each step (`ecb9eb2addd2c06b` at cap 6000). Harness note for anyone
repeating this: the capture script sends CRLF, so the firmware sees an empty second line and answers
`Command Input ERROR: unknown command` after every command. Cosmetic, not a firmware fault.

**Which spin traps is now known from the schematic, not inferred.** GP15 carries a **1k pull-down**,
with **110R in series** from the ADC's BUSY output — chosen to damp digital noise. An unpowered ADC
stops driving BUSY, the pull-down takes GP15 firmly **low**, and `while not busy_pin.value()` — spin
1 — therefore spins. Deterministic, not a floating pin, so the abort path is exercised by every rail
loss rather than by some. This supersedes an earlier inference in this entry's drafting that GP15
"parks high": that came from a single read taken at the REPL with the PWM peripheral still
free-running after a soft reset, so BUSY was still toggling and the read was a coin flip, not a park.
Spin 2 stays bounded for a different reason — an ADC that is powered but stuck mid-conversion, which
no rail check can catch — and it costs little, since at ~15 µs of BUSY-high it runs only a couple of
polls against spin 1's many.

**Logic levels at GP15 are comfortable — a marginal-threshold theory was raised and killed.** The
ADC's **OVDD is tied to 3.3 V** (not to the 2.5 V analogue rail U7 supplies), so BUSY's high arrives
at GP15 as 3.3 × 1000/1110 = **2.973 V** against an RP2040 V_IH of **2.145 V**: **828 mV, 39 % over
threshold**. Recorded because the alternative was briefly worth chasing — had OVDD been on the 2.5 V
rail the level would have been 2.25 V with only ~107 mV of margin, and a marginal high produces a
*fractional* detection rate, which is the shape of §7's unexplained ~1-in-6. It is not the mechanism.

**So §7's ~1-in-6 catch rate remains unexplained, and today's timing makes it more puzzling, not
less.** At a measured 5.816 µs poll against a stated ~15 µs BUSY-high window, roughly 2.6 polls land
inside every window — simple sampling says catch nearly all of them, not one in six. Either the
15 µs figure is not the BUSY-high width, or the ~1-in-6 describes *throughput* (conversions serviced
per conversions occurring, which the ~2.3 ms per-cell cost would dominate) rather than windows
missed. Worth settling with a scope, because the two readings imply very different ceilings on the
sweep rate.

**This also revises the sweep-rate prediction downward in severity.** The concern was that a +55 %
poll period would miss proportionally more BUSY-high windows. But 9.024 µs still fits inside a 15 µs
window **1.66×** over, so every window should still be caught and the catch behaviour should not
change at all. The earlier expectation of a drop from 16.13 Hz was based on a proportional model that
the window arithmetic does not support. Test A still decides it.

This build also still carries the v4.36 test floor (19.0/19.5 V), which must be reverted before any
pack that is meant to survive. DESIGN §8's firmware version and §9's "`B` — 6 fields" go stale until
the next §18 consolidation pass. (2026-08-12)

### findings — 2026-08-12 — thermal / battery sweep, `cal_2x11_v5` on the 6S pack

Four sessions, **186 min of pulsing**, full charge 24.69 V to the 19.0 V trip; fw v4.35 then the
v4.36 test build; classviz v1.73/v1.74; coil in air, no targets. Only the load-bearing results are
here; the raw evidence is the four `session_20260812_*.csv` dumps in `src/data/sessions/`.

**How thermal and supply were separated**, because it is what makes these numbers re-takeable: both
levers already exist in an ordinary run and neither needed a special test. *Thermal* — a cold start
at near-constant pack (session 3, 21.8 → 44.3 °C while the pack moved 0.29 V, so supply contributes
~1 % of the swing). *Supply* — session 4 after 15:15 held 43.8 ± 0.2 °C while the pack fell
21.20 → 19.07 V, a 2.1 V sweep at flat temperature; session 1 gives a second such window
(23.05 → 21.00 V at 39.1 °C) at the other end of the discharge, and the two agree. Reuse this shape
rather than sweeping a bench supply.

**Noise floor 65 µV** — median 32-sweep σ over 1 257 windows. Flat across every null/pedestal cell
and independent of delay, 37× below the 2.441 mV amplifier floor, null-cell SNR ~1000:1. **It does
not degrade as the pack falls**: median σ 76.6 µV at 21.1 V against 71.4 µV at 19.1 V. Open — band 0's
largest cell is ~3× noisier than band 1's at the same amplitude (93 vs 38 ppm), a signal-proportional
term band 1 does not have; wants a scope on the 3.125 kHz drive.

**Warm-up is ~10 min, not 4.** Band-0 mean fits one exponential, τ = 2.15 min, **+12.2 % high at
switch-on**: 1 % at 5.4 min, 0.5 % at 6.9 min, 0.2 % at 8.8 min. The DS18B20 reaches its final reading
at 4.9 min, **well before the signal settles — it is not a readiness indicator**. The old 4 min figure
came from the retired 20 V bench supply and lands at only ~2 %.

**The DS18B20 does not predict the operating point, and the fan is why.** At the same indicated
44.1 °C, band-0 mean read 543.8 and 533.9 mV five minutes apart — 1.8 % at identical sensor
temperature. Nudging the fan off the U1/FET cluster (15:10–15:13) took the sensor 41.0 → 46.0 °C and
band 0 **+3.7 %**, where bulk warm-up across the same span moves it *down*. It is thermal, not a metal
step: a smooth ~2.5 min exponential that fully reversed when the fan was restored, where a moved
ferrous object would step inside one 62 ms sweep. **This is the unexplained band-mean rise logged at
15:12.** Consequences — the fan mount is a measurement-critical mechanical variable (a slight nudge
outweighs the entire discharge range), and *which* component dominates is **not determinable from the
logs**; it needs a thermocouple on U1/Q1. This also corrected §17.14: bulk warm-up moves both bands
the **same** way (band 0 −7.6 %, band 1 −0.46 %, a ~16× ratio) where a supply shift moves them within
~1.5× — so the ratio separates them, not the sign, and the old opposite-directions test (r = +0.99)
identifies a *cooling change* specifically.

**Supply sensitivity is ~1 mV/V grid mean, ~40× below the standing 43–51 mV/V — flagged, not
settled.** Both windows agree (0.85 mV/V at 23→21 V, 1.12 mV/V at 21.2→19.1 V), one sign, and the full
2.1 V sweep moves the operating point only **−0.69 %** grid mean. Consistent with the +15 V rail
measuring 15.20–15.21 V on a DMM across the whole discharge. The likeliest reading is that the old
figure was taken through the U1 that later failed — i.e. it measured the regulator, not the detector —
**but that is an inference, and one deliberate re-measurement closes it.** Until then treat 43–51 mV/V
as pre-U1-replacement. If it holds, thermal drift dominates supply drift by ~10× and **warm-up, not
state of charge, is the thing to control**.

**Battery.** Endurance 3.10 h of pulsing full-charge-to-trip, but a single continuous run is much
shorter — session 1 alone went 24.69 → 21.00 V in 83.5 min, and a 44 min rest then gave back +2.04 V,
so rest recovery is a large part of the apparent endurance. Loaded discharge −32.8 mV/min at 23 V
rising to −72.7 mV/min over the last 13 min: a knee, not a half-full pack. Sag grows 850 mV at full
charge → 2.43 V at the trip. **A latched lockout still draws −30.2 mV/min with the drive off**, ~58 %
of the loaded rate — the pack must be switched off physically after a trip; leaving it latched from
15:58 to 16:55 cost 1.5 V, after the failsafe had already fired to protect it. Pack telemetry agreed
with the DMM to < 80 mV, typically < 20 mV.

**The 19.0 V floor stands, as a pack-quality limit.** The test build did its job and the question is
closed: nothing electrical or measurement-side objects to 19.0 V — the L7815 keeps ≥ 1.9 V of headroom
(D4 is a shunt clamp, no series drop) and noise, SNR and railing are unchanged down there. Cells at
rest after the run measured **3.62 / 3.63 / 3.65 / 3.42 / 3.24 / 3.66 V** — 420 mV spread, weakest
297 mV below the mean. **This supersedes the v4.36 source comment's estimate that the weak pair
reaches 2.0–2.1 V at a 19 000 mV trip**, which came from measuring four cells and doing arithmetic on
the remainder; the direct six-cell reading is far less severe. With that, and with new packs replacing
the recovered laptop cells, the floor is **kept** at 19_000 / 19_500. **Therefore the "must go back to
21_000" instruction in the `PACK_VOLTAGE_TRIP_MV` comment block, and the same instruction in the v4.37
entry above, are superseded** and should be reworded when that file is next touched — otherwise the
next reader reverts a floor that was deliberately kept.

Two loose ends. **Unexplained 1.13 V** between the cell sum (21.22 V) and telemetry (20.09 V) at
16:52 at near-zero load, where telemetry tracked the pack terminals to < 80 mV at three other points
— too large for fuse/wiring IR drop at idle, possible high-resistance joint inside the pack; bench
check. And **cold-start behaviour below 19 °C is untested**: the coldest capture of the day was
3633 mV at 19.5 °C, still 1367 mV (27 %) below full scale, and nothing railed in 3.1 h.

Data hygiene: **zero flagged rows in 63 813 sweeps** across the two uninterrupted sessions; the 200
flagged rows in sessions 1–2 all fall inside deliberate pack interruptions. (2026-08-12)

### findings — `src/pimd_classviz.py` v1.74 — `streamed_s` does not notice a lockout

After the firmware latched `LOCKOUT` at 15:58:04 on `session_20260812_150333` and stopped emitting
sweeps, the session went on writing `streamed_s=7314, 7374, 7434, 7495 … stalled_s=0` until 17:08 —
**70 minutes of zero data counted as streamed**, with the stall detector never firing. `streamed_s`
tracks wall-clock since the run armed rather than the arrival of records, so a source that goes silent
without closing the port is invisible to it. Distinct from the v1.74 fix in the entry above, which
corrected *arming*; this is a defect in what the armed counter measures. It matters precisely for the
long unattended run that soak accounting exists to watch. Not fixed. (2026-08-12)

### DESIGN.md — Doc-rev 2.1 — 2026-08-12 sweep results consolidated

Human-directed mini consolidation pass under §18, scoped to the day's bench results. **§3** gained the
noise floor, the measured warm-up (superseding the 4 min bench-supply figure), the DS18B20
non-predictor result, the fan-mount warning, supply sensitivity and full-scale headroom. **§4/§12**:
working floor restated as **19.0 V**, plus the measured power envelope — endurance, discharge rates,
sag, the +15 V rail flat to 50 mV, telemetry-vs-DMM agreement. **§10**: `cal_2x11_v5` sweep rate
**16.13 Hz** measured, +29.6 % over `cal_3x10_v5`, and the profile is no longer "not bench-verified".
**§17**: 17.23 corrected (pack voltage does not materially scale the decay), 17.14 corrected (thermal
and supply separate by band-magnitude ratio, not by sign), 17.11 qualified.

The header's Firmware / PC-tool version line was **deliberately left stale** at v4.35 / classviz
v1.73: v4.36 is the test build and v4.37 is not yet exercised on hardware, so bumping it now would
enshrine a version about to be superseded. Bump it at the next full consolidation. (2026-08-12)

### hardware/power — the 6S pack was replaced; the 19.0 V floor is now real, not a test build

The imbalanced pack characterised on 2026-08-12 has been retired and replaced with new cells in the
same 6S ICR18650-26C arrangement, balanced. Two things follow, and both matter more than the
hardware swap itself.

**The v4.36 warning is void.** That entry ends "this is a deliberate, temporary divergence from §12
and must be reverted before any pack that is meant to survive". That instruction rested on an
inferred per-cell figure which the 2026-08-12 sweep's own direct measurements did not bear out, and
the floor was decided **kept** on that day, before any swap — nothing electrical or measurement-side
objects to 19.0 V, the L7815 keeps ample headroom, and noise, SNR and railing are unchanged down
there. The new pack adds margin; it is not what settled the question. `PACK_VOLTAGE_TRIP_MV` 19_000
/ `PACK_REARM_MV` 19_500 stand as the working floor, and a supersede note has been added to the
v4.36 entry so the old warning cannot be read as current. The two constants still move together;
500 mV is the hysteresis and nothing else depends on the re-arm level.

**Every discharge figure measured on 2026-08-12 is now epoch-bound.** The §12 envelope — 3.10 h
endurance, 83.5 min continuous, 850 mV → 2.43 V sag, −32.8 rising to −72.7 mV/min, the +2.04 V rest
recovery — was measured on a pack that no longer exists, and a tired imbalanced pack sags harder and
knees earlier than a new one. Those numbers should be re-measured on one continuous run-down before
anything is planned against them. The **shape** of the discharge is expected to carry across (same
cells, same chemistry, same load); the absolute minutes are not. `pimd_pack.py` is built around
exactly that distinction — see its entry below.

Also worth recording: packs are swapped in and out of the rig as they charge, so more than one pack
is in rotation at any time. That is now a design input rather than an incidental habit — it is why
the new fuel gauge fits its rate live and watches for the voltage discontinuity a swap produces,
rather than trusting any single stored calibration. (2026-08-13)

### src/pimd_pack.py — v1 — NEW: shared pack fuel gauge, runtime-fraction SoC and live time remaining

New module, pure stdlib and no Qt, on the same footing as `pimd_shape.py`. It replaces the pack
maths that `pimd_gui.py`, `pimd_classviz.py`, `pimd_delaycal.py` and `pimd_rawlog.py` each carried
their own copy of.

**What was wrong with the old calculation.** `pack_soc_pct()` divided pack millivolts by six and
read a *resting* Samsung ICR18650-26C open-circuit curve. That is wrong twice: it is a resting curve
handed a *loaded* terminal voltage, and pack ÷ 6 assumes a balanced string. On the retired pack it
read 11 % where a charger implied 53 % (v4.36). Note that the charger was not right either — the
same entry shows the discharge rate roughly doubling over the run, which is a knee, not a half-full
pack — so this is not a case of one number to correct toward.

**Why not simply sag-correct the OCV curve.** Tried and rejected. Interpolating sag between the two
measured anchors reproduces the charger's ~53 %, i.e. it reproduces the answer the discharge data
contradicts. Worse, it is unstable where it matters: because pack ÷ 6 lands on the steep part of the
Li-ion curve, a 400 mV change in the assumed sag moves the reading at 22.0 V from 23 % to 36 %. It
would need a sag constant measured per pack, on a rig where packs are swapped.

**What it does instead.** State of charge is the fraction of usable *pulsing runtime* remaining,
read off a curve of loaded terminal volts → minutes-to-trip measured on a real discharge. No
per-cell claim, and no sag constant is needed because a curve of loaded volts has sag baked into it.
Zero percent is pinned to `PACK_TRIP_MV`, so moving the firmware floor re-zeros the gauge from one
constant instead of needing a new table — passing `trip_mV=21_000` puts 0 % back at 21.0 V and
rescales everything above it, which was checked.

`SOC_CURVE_MV` is used for its **shape** only: `pack_soc_pct()` normalises it, so the absolute
minutes of any one pack's calibration never reach the percentage. Absolute time comes from
`PackTracker`, which least-squares-fits the discharge rate over a 15-minute trailing window of the
pack telemetry and projects to the floor, formatted `H:MM`. At ~33 mV/min against a 7.35 mV LSB a
window carries ~68 LSB of travel, so the fit has ample resolution, and it tightens by itself through
the knee as the rate rises. Until a rate is available the caption falls back to the stored curve and
marks it with a leading `~`, so a figure that has not yet earned trust says so.

`PackTracker` is fed `note_pulse()` from each app's measurement-record handler rather than from any
per-app streaming flag: records flowing *is* the coil running, in all four apps, and it needs no app
to expose its state machine. Readings taken while idle are not fitted, because the drive-off drain
is roughly half the loaded rate and would flatter the estimate; a pause keeps the last good rate
rather than discarding it, since pausing does not change the pack. History is dropped on a rise of
more than 500 mV between consecutive readings (a charged pack fitted, or the load coming off), on
the pack going absent and returning, and on disconnect — all three are pack-swap cases, which this
rig sees routinely.

The shipped table is the 2026-08-12 discharge (118.1 min full-to-trip), generated by the module's
own `--recal` path so that regenerating it cannot shift the gauge for methodology reasons, only
because the pack changed. `--recal` works on discharge **rate** rather than elapsed time, which is
what lets it take several sessions without stitching them: each consecutive pair of readings gives
one rate sample at one voltage, rates are binned by voltage and median-filtered, and minutes-to-trip
is the integral of 1/rate. A rest between sessions then contributes no sample rather than appearing
as capacity from nowhere, and one bad reading loses to the median instead of moving the curve. Two
things are cut rather than fitted: samples after a `LOCKOUT` mark, because the drive is off past
that point and the pack drains at roughly half the loaded rate, and rates above 200 mV/min, which
are the load step at session open rather than discharge. An earlier time-stitching implementation
was written and discarded — it merged rest-recovered segments and produced a 73-minute
discontinuity at 21.0 V. (2026-08-13)

### src/pimd_gui.py — v4.18 — pack gauge on the shared fuel gauge; the data-quality zones are retired

The `SOC_NOMINAL` / `PACK_ZONES` / `PACK_WINDOW_LO_MV` block and the two functions over it are
replaced by an import of `pimd_pack.py`. The gauge fill and percentage are now runtime-fraction
state of charge, the caption is measured volts then `H:MM left`, and the fill colour comes from the
state of charge itself rather than from a zone.

**The zones were deleted because the measurement retired them, not for tidiness.** They named a
narrow "clean window" of pack voltage and their captions told the operator to stop capturing outside
it. DESIGN 17.23, corrected 2026-08-12, measures that sensitivity at ~1 mV/V — the operating point
moves −0.8 % across a 2.1 V pack swing, and thermal drift dominates it by ~10×. A caption reading
"below window" was therefore advice against an effect that is not there. Gone with them: the dashed
window-edge marker painted across the battery icon, whose whole job was to show where that advice
started applying.

`PackTracker` is fed from the `*` record branch and reset on disconnect. The header comment
explaining what left, and why, is kept in place of the block — the reasoning is the part a future
reader needs, and it is the one thing a deletion cannot leave behind. Checked that nothing
downstream parsed the zone captions: `pimd_features.py` reads only the `# pack_v:` track. (2026-08-13)

### src/pimd_classviz.py — v1.75 — pack gauge on the shared fuel gauge; the data-quality zones are retired

Same change as `pimd_gui.py` v4.18: the duplicated pack block and both functions give way to
`pimd_pack.py`, the zone captions and window marker go, and the caption becomes volts plus `H:MM`
left. `PackTracker` is fed `note_pulse()` from the `W` handler, immediately after the parse guards
so only accepted sweeps count, and reset on disconnect.

This file carried the note saying the pack constants were duplicated deliberately because "every PC
app in this repo stands alone", with an instruction to retune all four apps together if any one of
them changed. That instruction was the argument against itself — four hand-synced copies of a
calibration table is exactly the thing that drifts — and the rule is reversed here for the pack
maths only. It still stands for `_build_d_command`, which is a few lines of wire formatting rather
than a calibration. The gauge tooltip keeps its sentence about every reading landing in the session
dump as a `# pack_v:` line, since that track is what `--recal` reads. (2026-08-13)

### src/pimd_delaycal.py — v1.49 — pack gauge on the shared fuel gauge; conditions line reports time left

Same change as `pimd_gui.py` v4.18, plus one thing unique to this tool: `_sensor_summary()`, the
one-line form written into both the Activity Log and every exported profile's CSV header, used to
end with the zone caption. It now ends with time remaining — `pack 21.90 V, 53 % SoC, 1:37 left` —
because a sweep that outlasts the pack is the failure that line exists to let you see coming, and
the zone name it replaced described a window that no longer means anything. A recorded `~` prefix
marks a figure taken from the stored curve rather than the fitted rate, so an archived conditions
line stays honest about which it was. `PackTracker` is fed from the `R` handler and reset on
disconnect. (2026-08-13)

### src/pimd_rawlog.py — v1.17 — pack row on the shared fuel gauge; the data-quality zones are retired

Same change as the other three. This app renders its pack state as coloured label text rather than a
painted gauge, so it needed the darker end of the palette where the GUI apps need the pale end; that
is now `soc_colour(for_text=True)` rather than a second copy of the table, so the breakpoints stay
shared and only the shade differs. The row reads `Pack: 53% · 21.90 V · 1:37 left`.

Worth noting against this file's "deliberately dumb, so it cannot develop display-layer defects"
property: the import does weaken standalone-ness slightly, but the pack row is not on the raw
logging path, and the verbatim-line guarantee is untouched. `PackTracker` is fed `note_pulse()` from
the `W` branch and reset on disconnect. (2026-08-13)

### mcu/pimd_mcu.py — v4.37 — the pack-floor comments no longer instruct a revert to 21_000

**Comment-only; no version bump** (per `CLAUDE.md`, pure comment edits do not bump). The behaviour,
the constants and the wire format are untouched — but the comments around them were actively
dangerous, which is why this is recorded rather than folded in silently.

`PACK_VOLTAGE_TRIP_MV`'s block still opened "TEST BUILD FLOOR — 19_000, NOT the DESIGN §12 working
floor of 21_000" and closed "it must go back to 21_000 before any pack that is meant to survive";
`PACK_REARM_MV`'s block ended "Restore BOTH to 21_500/21_000 together"; and the header lineage's
v4.36 line read "Revert before a keeper pack". The 2026-08-12 sweep had already decided the opposite
— the floor was **kept** — and flagged these three sites to be reworded when the file was next
touched. They were not, so the source was instructing a future reader to undo a deliberate decision.
That is the whole risk here: nobody rereads a decision they think they are simply restoring.

Reworded to state the floor is settled and why (nothing electrical or measurement-side objects to
it; D4 is a shunt clamp with no series drop so the L7815 keeps ample headroom over its ~17.2 V
requirement; noise, SNR and railing are unchanged at the bottom of the range; the trip protects the
cells, not the rail), and to record explicitly that the restore-21_000 instruction is **withdrawn**.
The per-cell arithmetic the old warning rested on is not restated — it came from measuring part of a
string and inferring the rest, the direct readings did not support it, and that pack is gone. The
re-arm block keeps the one rule that still matters, now stated without version archaeology: it
tracks the trip, moves only in the same edit, and a wider gap breaks recovery because a USB-powered
MCU outlives the rail and cannot be reset by pulling the pack. (2026-08-13)

### DESIGN.md — Doc-rev 2.2 — full consolidation pass

Human-directed §18 consolidation. **Header**: firmware v4.35 → **v4.37** (bench-verified, which is
what Doc-rev 2.1 was waiting for before bumping); PC tools to gui **v4.18**, classviz **v1.75**,
delaycal **v1.49**, rawlog **v1.17**, plus **pack v1**; hardware-rev gains the **6S pack replaced
2026-08-13**; last-bench-update corrected 2026-08-11 → **2026-08-12**, the sweep it actually
describes.

**§9** — two protocol corrections, the first found by reading firmware against the doc rather than
from any changelog entry: `B` is **9 fields, not 6**, the v4.37 rail-loss abort having added
`busy_timeout_count`, `busy_spin_min_left` and `rail_absent_ms_max`; DESIGN had been describing a
record the firmware stopped emitting. The `avg` bound drops its "since v4.35" qualifier. §11 and the
rest of §9 are verbatim.

**§12** — the working floor is restated as **settled, not a test build**, with the reasoning that
kept it; the measured envelope is marked **epoch-bound to the retired pack** rather than deleted,
since its shape still carries and only its absolute figures are pack-specific; pack rotation is
recorded as a standing condition; and state of charge is defined as a runtime fraction, with the
note that a resting per-cell OCV curve on a loaded pack voltage is not a valid gauge here. Retired
per-cell voltages are deliberately **not** carried forward.

**§14** — one live open problem added, as 14.5: classviz's `streamed_s` counting a silent source as
streamed (70 minutes of it on 2026-08-12, unfixed). A second candidate — supply sensitivity at
~1 mV/V against a standing pre-U1-replacement figure of 43–51 mV/V — was drafted and then
**dropped at the builder's direction**, on the grounds that the older figure is not believed ever to
have been correct. That figure is now cited nowhere in DESIGN; ~1 mV/V stands unqualified in §3 and
17.23.

**§15** — new row for `src/pimd_pack.py`; five version bumps; and `README.md` / `TODO.md` added,
which the inventory claims a line per file but had never listed.

Dangling references fixed: the 2026-08-12 findings entry pointed at a `thermal-test.md` that does
not exist in the repository, now redirected to the four `session_20260812_*.csv` dumps that are the
actual evidence. Every asset DESIGN cites was verified present in `References/`; **17 files in
`References/images/` are cited nowhere** and were left alone rather than guessed into place — mostly
epoch-bound to retired profiles and corpora. (2026-08-13)

## Archive — consolidated 2026-08-12
**The user undertook a full and independent review of document and rewrote/culled many sections.**

---

### hardware — a 38 mm fan on the regulator/FET cluster; **3.125 kHz is now a forced-air-only setting**

**A 25 VDC 38 mm fan was fitted, blowing directly onto U1 from 50 mm**, with the same airstream
covering the load resistor and Q1. It is **powered directly from the pack**, unswitched and
unregulated. Under it the 100 µs band runs at **3.125 kHz** — the cut that had been tripping U1
every ~42 s — and the operator reports the +15 V rail *"appears very stable"*.

**Powering it from the pack makes the cooling track the dissipation, which is the right direction.**
U1's heat is `(V_pack − 15) × I`, worst at a full pack; fan speed rises with pack voltage over the
same span. At the 21.0 V floor the fan sees 84 % of its rated 25 V — comfortably above the ~60 %
where a DC fan stalls — while U1's drop has fallen from 9.7 V to 6.0 V. So the weakest cooling
coincides with the lightest load. **Favourable, and not by design** — worth stating so it is not
mistaken for a specified behaviour.

**Why this is the second of two exits, not a tweak.** The entry below meters the trip at **≈ 2.0×**
the U1 dissipation `cal_3x10_v5` was proven at, arriving as **1.40×** from the profile's heavy-band
duty and **1.41×** from running a full pack at 24.70 V. There are only two ways out: **cut the
watts** (the 2 kHz re-cut, which lands at 1.07× and costs the whole sweep-rate gain, 15.87 → 12.08 Hz)
or **cut the thermal resistance**. The fan takes the second, and it is the one that keeps the speed.

> **Operating rule this establishes — the pair is the specification, not the profile alone.**
> **The 100 µs band at 3.125 kHz requires the fan running.** At **2 kHz** the geometry is safe on
> passive cooling. Running `cal_2x11_v5.json` (3125 Hz) with the fan off reproduces the ~42 s trip
> cycle and 37 % frame loss described below. A profile is now specified by *(delays × pack window ×
> cooling)*, the same way §10 already makes it *(delays × pack window)*.

⚠ **Four things this does not yet establish.**

1. **"Appears very stable" is a short observation, and not at the bad corner.** The trip scaled with
   pack voltage — worst at **24.70 V** — and the 2 kHz evidence it is being compared against was
   only 132.6 s. **A full warm-up from cold on fresh cells is scheduled for 2026-08-12**, which is
   the right test: it walks the worst thermal corner (full pack, maximum drop) and the cold-start
   corner in one run. Until it lands, the operating rule above rests on a short observation.
2. **`board_temp_dC` will now read much lower, and it still means nothing about U1.** The sensor is
   on the **load resistor** — directly in the new airstream. It was already blind to the regulator
   die (see below); the fan makes it optimistic as well as blind. **Do not read a cool board as
   evidence the regulator is cool.** What would settle it is a thermocouple or IR read on U1's tab
   during the 08-12 run, which costs nothing extra while the lid is off.
3. **The noise floor has not been re-measured, and the pack feed adds a second path.** A brushless DC
   fan is a commutating motor beside a front end whose noise floor is a first-order concern (§3,
   §12) — the same objection that applies to a switching pre-regulator. Feeding it **directly from
   the pack** adds a *conducted* path on top of the radiated one: its commutation current now shares
   the `+20V` rail with everything else, upstream of D4 and FB1, and that rail is also the
   pack-sense divider's node (§12). §3's raw figures (**± 1400 µV** on the slope, **709 µV**
   per-sample past the lobe) are the check, and the 08-12 run can carry it at no extra cost — an air
   capture fan-on against fan-off. **Nothing should be captured against a fan-cooled rig until this
   is measured**, alongside §14.8's outstanding gate. If it does show up, a separate feed or local
   decoupling for the fan is the obvious first move.
4. **The enclosure.** §12 describes U1's dissipation as a problem specifically *"inside a sealed
   shielded enclosure"*; forced air implies vents. What that does to the shielding is a mechanical
   question not determined here.

**Minor:** the fan is unswitched, so it is a continuous pack load whenever the pack is connected —
order 1–2 W for a 38 mm 25 V part, and drawing most at full charge. §12's **620 streaming-minutes**
capacity figure is therefore now slightly optimistic, and its next re-measure should state whether
the fan was running. (2026-08-11)

---

### findings — U1 thermal shutdown, reproduced and metered: a profile's geometry is a thermal budget

**The 2026-08-10 failure mode, reproduced on the replacement part and its larger heatsink.** The
entry below records U1's death with the root cause *inferred* from the mitigation, because no
post-mortem was done. This one is the same failure caught live, on the new regulator, in a session
that was recorded end to end. **It is no longer an inference.**

**What the operator measured, and it is the primary evidence.** A DMM across the +15 V output while
`cal_2x11_v5` streamed: the rail sits at **15.22–15.3 V**, drifts slowly down to **15.0 V**, then
**collapses to ~7 V** and recovers — repeatedly, with the TO-220 hot to the touch **even with the
lid off**. Re-cutting the 100 µs band from 3.125 kHz to 2 kHz removed the problem entirely.

**Thermal shutdown rather than current limit.** The cycle in `session_20260811_161828.csv` has
period **42.1 s and 42.9 s**, ~15.8/18.9/19.2 s down against ~26.1/23.2/23.8 s up, and it took out
**37 % of 1891 frames**. Four things point the same way: the regularity, the slow pre-collapse
droop, recovery without a power cycle, and a fix that reduces *average* current. Current limit keys
on peak current, not on time-since-start, and would not produce a slow ramp into collapse.

**The signature is TX-side only, which the pedestal proves.** Comparing a healthy frame (t = 30 s)
against a collapsed one (t = 58 s), measured above each band's own pedestal:

| | healthy | collapsed | |
|---|---|---|---|
| band 0 (100 µs) cell 1 | +2574 mV | **−54 mV** | 47× down, now *below* the pedestal |
| band 1 (10 µs) cell 1 | +2290 mV | +69 mV | 33× down |
| pedestal, band 0 / band 1 | 113.0 / 111.9 mV | 117.4 / 128.9 mV | intact |

The pedestal surviving means the RX front end, U5's reference and the +97 mV bias are all healthy.
Only the drive is gone.

**§7's second-order prediction, observed.** The null minimum migrates from **cell 7 to cell 2** on
band 0 (16.92 → 11.90 µs) and from **cell 7 to cell 4** on band 1 (13.80 → 11.06 µs). §7 flagged
exactly this as *"second-order and worth a check rather than an assumption"*: a sagging rail changes
the initial conditions at release, hence the residue ratio `A/B`, and the crossing sits at
`ln(A/B) / (1/τ_f − 1/τ_s)` — so the crossing time moves while ζ holds. Band 1's lobe also goes
**shallower**, 40.1 → 32.1 mV below pedestal, the direction §7 predicts for reduced drive. *Band 0's
lobe figure is not a clean measurement in this state* — the whole waveform has moved inside the
sampled window, so the grid no longer straddles the minimum.

**The mechanism: sweep rate and coil-drive dissipation are the same knob, not two.** Pulse width is
fixed per band, so mean coil-drive current tracks **100 µs pulses per second** with no modelling
assumptions:

| profile | sweep | 100 µs pulses/s | wall clock driving the heavy coil |
|---|---|---|---|
| `cal_3x10_v5` | 12.45 Hz | 1245 | 12.45 % |
| `cal_2x11_v5` @ 3125 Hz | 15.87 Hz | 1746 | **17.46 % — 1.40×** |
| `cal_2x11_v5` @ 2000 Hz | 12.08 Hz | 1329 | 13.29 % — 1.07× |

**Total TX on-time barely moved — 19.9 % → 19.2 %.** What moved is the *heavy band's share*.
Dropping the 50 µs band removed the dilution that had been holding the 100 µs band at 12 % of wall
clock. **Fewer band boundaries buys sweep rate by deleting dead time, and dead time is also the
cooling.** §10's "fewer cells and fewer band boundaries is faster" is true and incomplete: faster is
also hotter, and there is a ceiling.

**Then multiply by the pack.** At 24.70 V the 7815 drops **9.70 V/A** against **6.89 V/A** at the
21.89 V corner `cal_3x10_v5` was tuned at — **1.41×**. Net **≈ 2.0× the dissipation** of the
conditions the known-good profile was proven at, which is why a profile that looked fine in delaycal
tripped the regulator in classviz. The 2 kHz re-cut lands at **1.5×** — under the trip, still above
the corner. **Pack voltage is therefore a thermal multiplier as well as a signal one**, and §12's
"above ceiling" zone above 24.0 V now has a second, demonstrated reason to exist.

**The fix works, and it costs the entire speed gain.** `session_20260811_163830.csv` ran 132.6 s on
the 2 kHz cut with **11 frames below 1500 mV against 697 of 1891**, at **12.08 Hz** — statistically
the same sweep rate as `cal_3x10_v5`'s 12.45 Hz. So `cal_2x11_v5` @ 2 kHz buys 2 bands × 11 cells at
the 3×10 sweep rate; it does not buy a faster sweep. **Read the fan entry above before treating
2 kHz as the only option** — forced air attacks the thermal path instead of the duty, and restores
the 3.125 kHz cut and its 15.87 Hz. 2 kHz remains the setting that is safe *without* the fan.

**Timing model, for sizing future geometries — a fit, not a measurement.** Three measured sweep
rates on fw v4.35 solve `sweep = K·Σ(cells/freq) + O` for **K ≈ 10 pulse periods per cell** and
**O ≈ 23.4 ms of per-sweep overhead**. Fitted on the two `2x11` points it predicts `cal_3x10_v5` at
79.4 ms against 80.32 ms measured — 1.1 %. **One lever falls out of it and is recorded as an option,
not a proposal:** because `O` is fixed dead time, halving `averages` shortens the sweep *and* lowers
duty. At `averages` 16 the model puts the 3.125 kHz geometry at ~23 Hz with a heavy-band share of
~12.7 % — thermally equivalent to `cal_3x10_v5` and nearly twice as fast, at √2 more noise (§3).
**Untested.**

⚠ **Two gaps let this run silently for 37 % of a session, and neither is fixed here.**
*(a)* **The failsafe is blind to it by construction** — `board_temp_dC` is sensed on the load
resistor, **not on U1**, so no telemetry sees the regulator's die. The board read a placid
53.5–54.1 °C throughout. *(b)* **classviz's `flagged` column does not mark it.** `flagged` is a
64-frame rolling-median glitch mask at 100 mV, so it re-centres on the collapsed level in ~4 s:
**53 % of deep-collapsed frames carry `flagged = 0`**. A collapsed detector is quiet and stable, and
reads as good data. **A corpus run would ingest those frames as valid** — live against §14.8, which
already gates capture on a null-sampling profile.

⚠ **This does not close §14.2's "+15 V rail under a TX pulse".** A DMM reads an average and cannot
see per-pulse sag; the scope measurement is still the cheapest open item on the list, and it is now
also the thing that would confirm the replacement U1 is healthy under a duty it can survive.

**Also touched:** §14.3 — the 100 µs band's pulses per second rose **40 %** on a Q1 (IRF610) already
run well above the schematic's < 2 % duty note. (2026-08-11)

---

### profile — `cal_2x11_v5` — 2 bands × 11 cells: the 50 µs band drops out, the early ladder gains two

**Not locked, not swept, and now known to need a re-cut** — read the thermal entry above before
using it. Two files sit untracked in `src/data/profiles/`, differing only in the 100 µs band's PRF:
`cal_2x11_v5.json` at 3125 Hz (the one that tripped U1) and `cal_2x11_v5 thermal test.json` at
2000 Hz (the one that does not).

**Why the 50 µs band went.** Read off the classviz sample-delay-band profiles by eye, the 50 µs
band's centre point sits essentially **on the straight line between the 100 µs and 10 µs bands** —
so it spends a band boundary's settle budget, the dominant per-sweep cost (§8), on information the
other two already carry. 2 × 11 = 22 channels against 3 × 10 = 30.

**Why 11 cells.** `cal_3x10_v5` spent **4 cells before the null, 1 in it, 5 after**; this spends
**6 before, 1 in it, 4 after** — two more in the early amplitude-anchored region where polarity
separates the families (§2), one fewer on the pedestal where three interpolated points were carrying
much the same decay-rate information.

**The two new cells, and both are interpolations rather than measurements.** Cell 2 at **~1.1 V**
fills the biggest hole in the old ladder, the 2.24 / 2.17 µs jump from 2.4 V to 0.5 V; it is placed
at the geometric midpoint of its measured neighbours (1092 / 1095 mV) by log-linear interpolation,
which the decay supports to ~3 % across that span. Cell 6 at **~85 / ~92 mV** fills the other hole,
the descent into the null, and is anchored **in time** at the midpoint between cell 5 and the null
minimum — it cannot be amplitude-matched across bands because the null depth is band-dependent
(59 vs 69 mV). Read it as a fill-depth cell, not an amplitude anchor.

**What the change buys geometrically:** pre-null gaps are now **0.86–1.13 µs across both bands**,
against a tight 0.9 µs cluster with 2.2 µs holes either side in `cal_3x10_v5`. **Cross-band
amplitude matching now holds for cells 1–5**; cells 6–8 are null-region and band-dependent by
construction; cells 9–11 are a geometric time-anchored ladder (ratio 1.7834 / 1.2152 per band)
between cell 8 and the band's longest delay. All 22 delays are exact 8 ns PWM-grid multiples with
both duties inside the 16-bit ceiling; only the 10 µs band is near the wall, at 29.0 against
29.095 µs.

**Measured sweep rate 15.87 Hz** at 3125 Hz and **12.08 Hz** at 2000 Hz (fw v4.35), against
`cal_3x10_v5`'s 12.45 Hz.

⚠ **Open, and it must be settled before anything is captured against either file.** Both JSONs
carry the internal `name` **`cal_2x11_v5`** with different geometry. The `profile_sha8` guard does
distinguish them, but §10 makes the **`name` field** what corpora record and what the cross-epoch
guard reports — so the recorded name is ambiguous between two profiles that are not comparable.
Left as-is at the operator's direction; **no file renamed by this entry.** (2026-08-11)

---

### hardware — U1 L7815CV **failed** on 2026-08-10 and was replaced like-for-like on a larger heatsink

**Operator record, supplied 2026-08-11 to close the gap the Doc-rev 1.16 pass had to leave open.**
The +15 V coil-drive regulator **died**; the replacement is the same L7815CV part with a **larger
heatsink**. It failed **about the same time the 240 k bias resistor was fitted**, which is why the
two changes are confounded in the 2026-08-10 session and why this entry matters more than a parts
note would.

**This was predicted, in writing, and the prediction was cut from DESIGN.md as history two weeks
later.** The 2026-07-24 6S entry recorded that adding a cell rather than replacing like-for-like
would **roughly double U1's dissipation, ≈ 2.5 W → ≈ 4.6 W** at the measured ~0.5 A average,
**inside a sealed shielded enclosure, on a project whose first open problem is thermal drift.**
Doc-rev 1.15.6 kept that bullet deliberately, calling it "the one place the enclosure does bite, and
a live concern, not a stale measurement". **Doc-rev 1.15.7 cut it as duplicated history on
2026-08-10.** The part died the same day. The larger heatsink is the mitigation that bullet implied,
so the bullet goes back into §12 as a **failure record**, not as background.

**It explains the lobe deepening, and in the right direction.** The Doc-rev 1.16 pass voided §7's
2026-08-08 voltages because air's lobe went **29.3 → 38.2 mV** below quiescent between that capture
and 2026-08-10, which a 240 k shunt cannot do — it attenuates ~2 %, making a lobe *shallower*. A
degraded 7815 does exactly the opposite: it sags the +15 V rail under pulse load, which cuts coil
drive, which cuts flyback and decay amplitude, which makes the lobe **shallower**. So the 08-08
capture reads as **the compromised measurement and 08-10 as the healthy one** — the direction fits
and the void stands, now for a specific reason rather than an unexplained step.

⚠ **Consistent, not proven, and the onset is unknown.** Nothing here establishes *when* the part
began to degrade — only when it finally died. A regulator can fail abruptly from a healthy state, in
which case 08-08 was fine and the deepening needs another explanation. **This cannot be settled from
the record; it needs the scope measurement §12 has been carrying as unmade** — the +15 V rail
during a TX pulse, which would have caught a sagging rail directly. That measurement is now the
cheapest way to confirm the new part is healthy as well as to establish the floor it was written for.

**What survives, and it is the split the consolidation already made.** ζ = 1.06 and the pole ratio
are properties of the RX network (R1, L, C) and **do not depend on drive amplitude** — a linear
RLC's poles do not move with excitation. So "the shape stands, the voltages do not" is *reinforced*
by this, not overturned. **One second-order caveat worth a check rather than an assumption:** a
sagging rail changes the *initial conditions* at release, hence the residue ratio A/B, and the zero
crossing sits at `ln(A/B) / (1/τ_f − 1/τ_s)` — so the **crossing time** can move while ζ holds. The
per-band null bottoms now in §7 (17.52 / 16.10 / 13.99 µs) were measured on 2026-08-10, i.e. on the
new part, so they are current either way.

**Everything current is post-swap, which is the good news.** `cal_3x10_v5` was hand-tuned 2026-08-11
and the v4.35 bench verification ran 2026-08-11, both on the new regulator. The 2026-08-10 bias
session is the only one where ordering is ambiguous — but its measured quiescent of **+112.8 mV**
against a predicted **+111.7 mV** implies a healthy 5 V reference and a sane rail at that point, so
those figures are most likely post-replacement too. Not asserted: the operator's ordering within
that day is what settles it.

**No post-mortem was done, so the root cause is inferred from the mitigation.** Doubled dissipation
in a sealed enclosure is a sufficient explanation and a larger heatsink is the matching fix, but
nothing confirms it — and if the cause was something else (an input transient, or **C18 sitting at
~100 % of its 25 V rating on the same rail, §14.4**), it can recur. **Two consequences to watch:**
the larger heatsink changes U1's thermal mass, so the warm-up and soak figures in §3 and the thermal
drift fingerprint in §14.1 may have shifted; and this is now a **known failure mode of the 6S
decision**, not a hypothetical cost of it. (2026-08-11, event 2026-08-10)

---

### DESIGN.md — Doc-rev 1.16.1 — the 7815 failure is recorded; §12's cut dissipation bullet comes back

Post-consolidation correction, on the 1.13.1 / 1.15.1 precedent. **No new bench data** — it lands
the operator record above into the four places Doc-rev 1.16 had written around it.

**Hardware rev line** gains `U1 L7815CV replaced 2026-08-10 (failed; larger heatsink)`.

**§7's void paragraph** said the deepened lobe meant "the replaced 7815 is the likely cause" with a
parenthetical that the swap "has no changelog entry of its own; it is known only as an aside". Both
are now wrong. It states the mechanism instead — a degraded regulator sags the rail, cutting drive
and making the lobe shallower, so 08-08 is the compromised capture — with the onset flagged as
unestablished and the +15 V pulse-load scope measurement named as what settles it.

**§14.2** loses "the regulator swap has no changelog entry, so there is no record of when it
happened or which part went in" and gains the date, the part and the open question of *why* it
died. **§14.4 (C18)** gains a line noting it sits on the rail feeding the regulator that just
failed, so it is a candidate contributor rather than an independent item.

**§12 gets the dissipation bullet back**, which is the substantive change. It was cut at 1.15.7 as
duplicated history; the part it described failed the same day. It returns as **≈ 2.5 W → ≈ 4.6 W
inside a sealed enclosure — and U1 failed under it on 2026-08-10**, with the larger heatsink as the
fitted mitigation. The lesson is recorded in place: **a standing risk that has not yet fired reads
as history right up until it does.** (2026-08-11)

---

### DESIGN.md — Doc-rev 1.16 — §18 consolidation: the null is sampled on purpose, and the retired profiles go

Consolidation pass over the twenty entries above the 2026-08-09 marker. Net state rather than
replay: firmware **v4.35**, classviz **v1.73**, delaycal **v1.48**, hardware **6.04 + the
2026-08-10 RX bias mod**, operating profile **`cal_3x10_v5`**. DESIGN.md 869 → 1068 lines; the
growth is almost entirely §7 and §10, which had to be rewritten rather than trimmed.

**The substantive reversal, and it runs through six sections.** §7's "⚠ Design constraint: no
profile may sample inside the rail" is **deleted**, along with the `sd 14.23–18.44` window it
imposed and §17.4's ~3.5× compression fact. The 240 k bias resistor lifted air's worst case from
clipped to **67.2 mV**, so nothing rails and no geometry has to avoid anything. In its place §7
carries the mod itself (design number predicted +111.7 mV, measured +112.8 mV), the per-band null
bottoms, and the case for sampling there — **6–8× steel:brass through the null against 5.8× on the
tail, at +187 mV instead of +78 mV** for a noise floor that does not vary with delay. §2 goes from
one discriminant to **three** (polarity → fill depth → decay rate), with the fill table and the
opposite-slope observation that sets a placement constraint. §13's "stepping over the front end's
own artefact" bullet becomes its opposite and says so.

**§7's 2026-08-08 voltages are marked void, and that is a deliberate downgrade.** The air lobe
deepened 29.3 → 38.2 mV between that capture and the bias session, which a 240 k shunt cannot do.
The shape and the 1.149 gain are kept; the voltages are not, and §14.2's first item is now the
front end itself. **The suspected cause — a replaced 7815 — has no changelog entry of its own**,
so there is no record of when it happened or what went in. Recorded as a gap, not resolved.

**§10 is rewritten around `cal_3x10_v5`**, including the property the older locks did not have:
cells 1–4 are amplitude-anchored **across** the three bands, so cell *n* is the same point on the
decay in every band to ~0.2 %. Both caveats travel with it — it is **not locked**, and its anchors
are verified only at the 21.89 V / 70.3 °C corner. The sweep-rate table gains the 30-cell figure
(**12.30 Hz on v4.34, 12.45 Hz on v4.35**) that §10 had been explicitly missing, and drops the
63/45-cell rows.

**Every superseded profile is cut as design material.** `cal_3x10_v1…v4`, `cal_3x10_v4_railtest`,
`cal_63_air_v1`, `cal_72_air_v2/v3`, `cal_110_full_range_v4` and `sweep_100us_decay_v1` are named
once, in §15, as out-of-tree and git-recoverable. `cal_63_air_v2` and `cal_63_air_bat_v3` stay, and
§15 now says **why** — the two corpora were captured against them and §16's `--selftest` runs
against the first, so a corpus whose profile is gone cannot be interpreted. §3's `[63-cell]` tags
become `[prev-epoch]`: same warning, no dead profile names.

**§14 goes from 7 open problems to 10.** New: **8** — the null's discrimination is measured at
**0 cm only**, and nothing should be captured against a null-sampling profile until one 50 mm
repeat on the 100 µs band confirms it (flagged as the highest-priority item, because it gates the
corpus); **9** — `cal_3x10_v5` is unlocked and single-corner; **10** — Plan C, the differential
bias onto the ADC's IN−, whose argument is precisely that Plan A worked. §14.5 grows a third limb:
the bias resistor is not on the schematic either. §14.1 gains the finding that board temperature
does not merely drift the reading, it decides where the ladder lands (46.7 % → 100 % railed on the
same cell between 52.5 °C and 31.5 °C).

**§8 and §9, minimally.** §8's v4.25 outlier-gate bullet is replaced by the v4.35 rule, stated as
four properties to preserve rather than as the story of the latch; the v4.25 note stays as an
explicit "do not assume this was covered". Added: the structural ~88.6 % overrun ratio, the 8 ns
minimum cell spacing, and the `D OK` requirement. §9 changes in exactly two places, both real wire
changes — `B` is **6 fields** since v4.35, and `D` bounds `averages` to 1..128. No rewording
elsewhere; §11 is byte-identical.

**§17 renumbered 17.1–17.23** with the six new front-end and firmware facts folded in and the
epoch column re-tagged. **§15** corrects two things the file had wrong: `References/scope/` is
tracked again (`20260810_bias_mod/`, the evidence behind §2 and §7) after being listed as retired,
and `targets_v4.csv` is tracked and read by `pimd_rawlog` alone despite never being mentioned —
flagged in place as **not** a successor to `targets_v3.csv`. `profile_3x10_timing.png` is demoted
to history, since it renders a geometry that no longer exists. (2026-08-11)

---

## Archive — consolidated 2026-08-11

### profile — `cal_3x10_v5` — the new baseline: nothing rails, and the null is sampled on purpose

**Hand-tuned in `pimd_delaycal` v1.48 Manual Nudge against fw v4.35, 2026-08-11, over a 1866 s
run.** Not swept — no threshold crossing was measured for any cell; these are the operator's
placements, verified live against the measured means. The operator's shorthand notes are
rewritten in the file itself; the two unit slips in them (cells 5 and 6 were "60-80us" and
"90us" for what the table shows as **mV**) are corrected there, and the geometric span was
"8,9" for what is actually cells **7,8,9**.

| band | delays (µs) |
|---|---|
| 100 µs @ 3.125 kHz | 10.792 · 13.032 · 13.912 · 14.816 · 16.92 · 21.16 · 32.656 · 50.392 · 77.76 · 120.0 |
| 50 µs @ 5 kHz | 10.016 · 12.256 · 13.144 · 14.08 · 16.08 · 19.36 · 27.152 · 38.088 · 53.432 · 75.0 |
| 10 µs @ 25 kHz | 8.04 · 10.208 · 11.064 · 11.984 · 13.8 · 16.16 · 18.704 · 21.648 · 25.056 · 29.0 |

**The substantive change is that cells 1-4 are amplitude-anchored and matched ACROSS the three
bands**, not just within one. Cell *n* means the same point on the decay whichever band it is
in, to within ~0.2 %:

| cell | target | measured (100 / 50 / 10 µs) |
|---|---|---|
| 1 | 2.4 V | 2396 / 2400 / 2401 mV |
| 2 | 0.5 V | 498 / 499 / 499 mV |
| 3 | 250 mV | 248 / 250 / 249 mV |
| 4 | 125 mV | 124 / 125 / 124 mV |
| 5 | null minimum | 59 / 64 / 69 mV |
| 6 | rising out, ~90 mV | 91 / 90 / 90 mV |

Cells 7-9 are a geometric ladder interpolated between cell 6 and cell 10 (constant ratio
1.5431 / 1.4027 / 1.1574 per band, all on the 8 ns grid), landing on the ~110 mV air pedestal by
cell 7-8, so they carry **decay rate** rather than amplitude. Cell 10 is the band's longest
delay.

**No cell rails.** The largest reading is 2.4 V against 5.000 V full scale, so every cell is a
measurement rather than a limit — **the first `cal_3x10_*` profile for which that is true.**
`cal_3x10_v3` and the original `cal_3x10_v4` both clipped cell 1 of every band, and the
2026-08-11 findings entry below shows v3 still doing it. It also leaves real headroom rather
than sitting just under the limit, which matters because the operating point moves with pack
state and board temperature.

**The null is now sampled deliberately at its minimum** (cell 5) with cell 6 on the way out,
rather than skipped. That closes the arc from `cal_3x10_v2`, which had to skip the whole span
because the front end clipped there, through v3 which removed the skip once the +97 mV bias was
fitted, to v5 which puts a cell *on* the feature. Cell 5 also shows the null depth is
band-dependent — deepest at 59 mV on the 100 µs band, shallowest at 69 mV on the 10 µs — which
independently corroborates the 2026-08-10 "below-rail window is band-dependent" finding by a
different route.

**Two caveats, both about where it was tuned.** Conditions were **pack 21.89 V (22 % SoC — the
LOW end of the §12 clean window) and board 70.3 °C**, i.e. nearly the opposite corner from that
morning's 23.5 V / 31.5 °C. Amplitude-anchored delays are a function of pack state (43-51 mV/V,
§12) and of board temperature, so cells 1-4 will not sit on those voltages at full charge or on
a cold board — the anchors are verified at one corner only. And the file's "10: max possible" is
true only of the 10 µs band (29.0 against a 29.095 µs hardware limit, 95 ns of margin); the 100
and 50 µs bands sit at 120 and 75 µs against limits of 219.091 and 149.093, carried over from
v3 rather than pushed out.

Validated offline: all 30 cells pass the firmware's `pulse_duties_valid()`, every band strictly
ascending, every delay on the 8 ns PWM grid, `averages` 32 inside the v4.35 `D` bound. Std dev
across the whole table was **0.00-0.10 mV, every cell green**, which against the v4.35 findings
entry's measured floor (56-72 µV on tail cells) is a quiet table on a hot board at low pack.
**Not locked** — nothing has been captured against it yet. (2026-08-11)

---

### findings — v4.35 bench-verified: the latch is gone on the geometry that caused it

Regression run on the original failing cell geometry (`cal_3x10_v4_railtest`, `profile_sha8
43379c54` — the same delays as the latched `69d51733`), fw v4.35, ClassViz v1.73,
`session_20260811_095403.csv`, 1578 frames. **Every channel that latched on v4.34 now tracks
continuously.**

| ch | delay | v4.34 (session_20260810_174641) | v4.35 (session_20260811_095403) |
|---|---|---|---|
| 2 | 12.8 µs | frozen at 720214, 1813 frames | 1562 unique, longest identical run **2** |
| 3 | 13.6 µs | frozen at 384521 | 1500 unique, longest run **3** |
| 12 | 11.904 µs | frozen at 664062 | 1424 unique, longest run **4** |
| 13 | 12.8 µs | frozen at 332641 | 1235 unique, longest run **5** |
| 21 | 7.0 µs | frozen at 4015503 | 541 unique, longest run **4** |
| 22 | 9.904 µs | frozen at 624389 | 408 unique, longest run **7** |
| 23 | 10.8 µs | frozen at 293579 | 320 unique, longest run **7** |

Longest identical run anywhere among the live channels is **9 frames**, against 1813-and-still-
frozen-at-end-of-file on v4.34.

**ch0/1/10/11/20 are still constant, and that is hard ADC saturation, not the latch.** All 1578
frames sit at exactly 4999389 µV (8191 codes, positive full scale), so the converter really does
return the same code every sweep — there is no firmware change that can move it, and the fix is
at the delay ladder, which is what the operating `cal_3x10_v4` did on 2026-08-10. Worth noting
they rail *harder* than they did yesterday: ch0 was 46.7 % at the rail on 2026-08-10 at 52.5 °C
board temperature, and is 100 % at 31.5 °C today. Consistent with the v4.27 observation that
cooling moves the operating point up, and a reminder that **which cells clip is a function of
board temperature and pack state, not a static property of the ladder.**

**The gate did not fire at all** — `B47400,42007,0,0,0,0` over 1580 sweeps, and
`B34740,30756,0,0,0,0` over 1158 sweeps on the re-cut profile before it. That is the arming
change (`cnt >= avg_depth`, was `>= 8`) doing the work: the v4.34 latch was seeded by the gate
going live a quarter of the way through the first ring fill, while the cell was still settling
after the profile change, and locking onto that warm-up value. Arm after the transient and the
rejection that started it never happens. Note also that **a railed cell does not itself provoke
rejections** — pinned samples are all 8191, so deviation from the rolling mean is ~zero; on
2026-08-10 ch0 varied by ~93 codes against a gate of 811.

Zero rejections across 34,740 and 47,400 samples is *lower* than the 2026-07 cell-0 finding
would predict (outliers above 100 mV at 23.3 per 1000, which over these windows would be ~80 and
~110 events). The likeliest reading is that the v4.26 IRQ critical section and the v4.34 settle
fix between them largely cleared that population — both postdate the measurement — but it is an
inference, not a result. The counters are now in place to settle it whenever it matters.

**No sweep-rate cost.** v4.35 adds a list index, a comparison and an occasional ring re-prime to
`acquire_mode2`'s per-cell path, so the question is whether that shows up as a slower sweep. It
does not. Measured from the firmware clock in the two session dumps, over the **identical**
30-cell geometry:

| session | fw | frames | span | rate |
|---|---|---|---|---|
| `session_20260810_174641` | 4.34 | 2213 | 179.9 s | **12.30 Hz** (369 cells/s) |
| `session_20260811_095403` | 4.35 | 1578 | 126.6 s | **12.45 Hz** (374 cells/s) |

v4.35 is marginally *faster*, i.e. the difference is run-to-run variation. This supersedes the
`cal_3x10_v3` regression run the fix entry originally called for — that would have compared a
different profile against no published v4.34 baseline (DESIGN §8 records 11.49 Hz for 3 × 11 = 33
cells and notes no 3 × 10 measurement exists), whereas these two runs are the same delays on the
same rig either side of the change. **A 30-cell 3-band profile runs at ~12.3-12.5 Hz on fw
v4.34/v4.35**, which is the figure §8 was missing.

**`overrun_count` is ~88.6 % of `busy_high_count` on every run** (30756/34740, 42007/47400), and
that is structural, not a regression: per-cell interpreter cost is ~2.3 ms against band periods
of 320/200/40 µs, so `remaining` is negative on every non-boundary cell by construction. The
arithmetic confirms it — 47400 − 42007 = 5393 non-overruns against 1580 sweeps × 3 boundary
cells = 4740, i.e. the cells that do not overrun are essentially the ones receiving the settle
budget. (2026-08-11)

---

### src/pimd_classviz.py — v1.73 — clipped cells are marked as clipped, and Load & Run waits for the firmware to accept the profile

The two PC-side items from the v4.35 Mode 2 audit below, split out to keep the firmware change
reversible on its own. Neither is a new discovery; both are gaps that audit named and that the
`cal_3x10_v4` session made concrete.

**1. ADC rail marking.** Raw Mode 2 samples are signed 14-bit, so a cell that reaches +8191 /
−8192 is clipped and its reported value is a *limit*, not a measurement. The firmware sends no
clip flag and ClassViz had no rail detection at all, so a railed cell arrived as 4999389 µV and
read exactly like a reading — in `session_20260810_174641.csv`, ch0/ch10/ch20 sat there for the
opening ~140 frames and nothing said so. Detection is now done here, from the value itself:
`RAIL_POS_UV` / `RAIL_NEG_UV` derived from DESIGN §9's `raw14 * 10_000_000 / 2**14` scaling, with
a 2-code (~1.2 mV) tolerance so the firmware's rolling average pulling the mean a code below full
scale while individual samples are still pinned there does not hide it.

Surfaced three ways, and the split between them matters. **Current state** gets a standing
readout: a top-bar `lbl_rail` label beside `lbl_rate`, blank when nothing is clipping and a red
`⚠ RAIL: N cells` when something is, visible on every tab. **Per-cell detail** gets the Stats
tab's **Latest (mV)** cell turning red with a tooltip — Latest is the right column for it,
because Mean and Std are window statistics while Latest is the single number that *is* the
converter's limit. **Transitions** get a status-bar line and a session mark, following the
firmware's own `_ds_mark_present` convention: only entries are reported, because a cell leaving
the rail is the normal case and a target passing through lifts and drops cells constantly,
whereas a cell that has clipped even once has produced at least one frame that is not a
measurement, and that does not expire for the run. Rail state resets on a profile change, because
which cells clip is precisely what changing the delay ladder changes.

**The standing label was added after the bench found the first shape wrong** (2026-08-11, in this
same pass, so there is no released v1.73 without it). The transition message alone was invisible
in practice: the status bar has ~80 other `showMessage()` callers, so a one-shot line announcing
a condition that then persists for the entire run is gone long before anyone looks at it. The
detection had been right all along — the run's session dump carried the correct mark, naming
exactly the five clipped cells, written on the first frame — but a standing condition needs a
standing readout, which is the same reasoning `lbl_rate`'s own comment gives for living in the
top bar.

**The value is deliberately NOT filtered or substituted**, which is the opposite of the 100 mV
glitch mask sitting a few lines above it. A glitch is a sample to clean up; a rail is a profile
problem to fix at the delay ladder, and hiding it would remove the only evidence that it needs
fixing.

**2. `Load & Run` no longer sends `Q`/`G` blind.** The firmware refuses the *whole* `D` on any
invalid cell and leaves the previous dynamic profile in place, so the old sequence — `E`, `D…`,
`Q5`, `G`, then `_apply_profile()` with the file's contents regardless — would select that stale
profile, stream its geometry, and write a session header naming the profile it had just failed to
load. **A CSV that names a profile it does not contain, with nothing in it that offline analysis
could use to notice.** `pimd_delaycal` has guarded this since v1.41; the guard is ported here as
`_send_dynamic_profile(profile, on_ready)` plus the second half of the load path split out as
`_finish_load_run_profile()`, so everything that commits to the new geometry happens only after
`D OK`. The gate sits after the V/P/PACK handlers in `process_packet()` for the reason delaycal
puts it there: an unsolicited `P` can land inside the D window and the gate consumes every line
it sees.

Two things delaycal does not have, both because this path is also the v1.53 launch auto-start
where a silent stall reads as "ClassViz never started" with nothing on screen to explain it. A
`D_ACK_TIMEOUT_MS` (3 s) single-shot timer **fails closed** — no reply means no `Q`/`G` and a
status line saying the profile was not loaded, never a stream on an unconfirmed profile. And a
second `Load & Run` is refused while one handshake is in flight, since two overlapping sends
would let the first `D`'s reply fire the second profile's callback and re-open the exact race
this closes.

**Verified headless** (offscreen Qt, feeding `process_packet()` directly, which is what the serial
reader does): `E`+`D` sent with `Q`/`G` withheld; an unsolicited `P` inside the window neither
consumes the gate nor fires the callback; `D OK` fires it once and stops the timer; a
`Command Input ERROR` clears the gate with `Q`/`G` never sent; the timeout fails closed and is
idempotent; rail reporting fires once per newly-railed cell, stays quiet while it holds, reports
again for a new cell, and is silent when cells leave the rail; the standing label tracks the
current count, clears itself when the last cell comes down, and gets the singular/plural right.
Against the real bench frame, the detector flags exactly ch0/ch10/ch20 and none of the tail
cells. What offscreen rendering cannot confirm is the red Latest cell and its tooltip — check
that on the bench. (2026-08-10, standing label 2026-08-11)

---

### mcu/pimd_mcu.py — v4.35 — the outlier gate was an absorbing state; cells latched and never came back

**Symptom, on the bench:** running `cal_3x10_v4` in ClassViz, the early cells of every band
read "stuck" — flat lines in the Analysis grids, near-zero σ everywhere except one cell, no
response to a target. `pimd_delaycal` showed the same thing as inflated std-devs and frozen
cells. **Reloading the profile into the MCU cleared it for a while**, which is the detail that
puts it in firmware state rather than in the analogue front end.

**Proof, from `src/data/sessions/session_20260810_174641.csv`** (2213 frames, fw v4.34,
`cal_3x10_v4` / `69d51733`): eleven of thirty channels — ch0-3, ch10-13, ch21-23, i.e. cells
0-3 of every band bar ch20 — stop changing between 17:46:58 and 17:47:01 and are then
**byte-identical for the remaining 1813 frames**. Not quiet: the same integer, repeated. The
last step before each freeze is exactly −19 µV on all eleven, which is −1 raw14 code
(10 V / 2¹⁴ / 32 averages = 19.07 µV) — an integer floor-division ratchet, not noise. The one
bright cell in the heatmap (10 µs row, 5.00 V column) is ch20, the only early cell that did
*not* latch, and so the only one still reporting real σ. Nothing was wrong with the analogue
side.

**Root cause.** The v4.21 plausibility gate rejected a sample by *substituting the rolling
mean and writing that back into the ring*. Three consequences, all fatal together:

1. **"Every slot equals the mean" is an exact fixed point** — `rolling_sum // cnt` returns
   that value, the substitution writes it, the sum does not move. No path out.
2. **Floor division makes the approach monotone**, so the mean walks down one code at a time
   until it converges — the observed −19 µV/frame ratchet, then the hard stop.
3. **It is self-reinforcing.** Once the mean sits further than `gate` from the true signal,
   every subsequent sample is rejected, which is exactly what holds the mean there.

`gate = max(|mean_raw| // 10, 164)` counts is a 10 % proportional band, so anything that moves
a cell more than 10 % — a cell still settling after `G`/`Q`, a warming rig, a fast waveform, a
railed cell dropping into the linear window — walks out of the band and cannot walk back. Two
things made it easy to fall in: the gate armed at `cnt >= 8` against an `avg_depth` of 32, so
it went live a quarter of the way through the ring's first fill and could lock onto a warm-up
value; and only re-entering `acquire_mode2` rebuilds `rolling`/`rolling_count`, which is why a
profile reload bought a working detector until it re-latched.

**v4.25 fixed a different latch path** — near-zero and negative means flooring the threshold to
0 or below — by adding `OUTLIER_GATE_MIN`. It did not touch the write-back, so the proportional
band kept an independent latch of its own. Do not read the v4.25 line and assume this was
covered.

**The fix keeps the gate and removes its ability to become a state.** The §7 bit-truncation
artefacts it exists for are real, land at exactly 1/2 and 1/4 of the true value, and are
volts-scale. Four changes in `acquire_mode2`:

- **A rejected sample is dropped, never substituted.** No `rolling_sum` update, no ring write,
  no index advance, no count change. The ring keeps its real history, the reported mean simply
  holds for that sweep, and the fixed point and the ratchet both cease to exist.
- **`OUTLIER_GATE_MAX_RUN = 4` bounds the rejection run.** Per-cell `reject_run[]` increments
  on rejection and clears on acceptance; on the fourth consecutive rejection the gate yields —
  it empties the cell's ring and takes the sample, so the cell re-converges on the new
  operating point in `avg_depth` sweeps with the gate disarmed while it refills. A cell is
  sampled once per sweep and the artefacts are single-sample events, so four in a row is not a
  glitch population, it is the signal having moved. 4 costs at most 3 sweeps (~0.24 s at
  12.7 Hz) on a genuine step.
- **The gate arms only on a full ring** (`cnt >= avg_depth`, was `>= 8`), so a settling cell
  can no longer seed it. This makes it inert at `averages == 1`, which is correct — profile 2
  is the single-sample scope-correlation profile and must not be filtered.
- **The fill branch adds without subtracting.** v4.34 and earlier always subtracted the slot
  being overwritten, which was right only because `rolling` is zero-initialised and each slot
  is therefore 0 on its first write. True for the first fill, **not** for a re-prime, where the
  slots still hold the previous generation's values. Without this the re-prime would corrupt
  `rolling_sum`.

**Observability, because the gate was completely silent** — which is why this cost a bench
session instead of one `B`. Two counters, `gate_reject_count` and `gate_reprime_count`, appended
to the `B` response: `B<busy_high>,<overrun>,<emit_block>,<emit_block_ms_max>,<gate_reject>,
<gate_reprime>`, reset-on-read like the rest. Additive, on the v4.27 precedent; nothing in
`src/` parses `B`. The ratio is the number to read: rejections with near-zero re-primes means
the gate is catching glitches, which is its job; re-primes climbing with the signal means it is
fighting real signal and `OUTLIER_GATE_FRAC` is too tight for the profile in use.

**Also in this version:** `D` now bounds `averages` to 1..128. It was unvalidated — `averages=0`
builds zero-length rings and kills `acquire_mode2` on `% avg_depth`, reported as an opaque Mode 2
failure through the v4.14 try/except, and large values are the v4.14 memory crash (128 fine, 256
not). Refused in the parser now, where the operator can see why.

**Offline differential test.** A throwaway harness mirroring the firmware's per-cell
bookkeeping exactly (integer maths, floor division as MicroPython does it), running the v4.34
rule and the v4.35 rule over identical sample streams, with a per-push assertion that
`rolling_sum` still equals the sum of the ring's live entries. Not tracked in the repo — the
results are the record:

| case | v4.34 | v4.35 |
|---|---|---|
| railed at +FS, then drops into the linear window | **frozen at 8191 forever, 2191 codes (1.3 V) off** | recovers to within 4 codes, 1 re-prime |
| 400 random (seed, truth) pairs × 800 frames | **latched 382/400** | **latched 0/400** |
| stationary + 2 % truncation glitches | 14 rejects, tracks | 14 rejects, tracks — filtering unchanged |
| fast sweep through the cell | 82 rejects, tracks | 12 rejects, 3 re-primes, tracks |
| slow thermal drift 1150 → 900 codes | 0 rejects | 0 rejects — no regression on the quiet case |

The railed-cell row is the bench failure reproduced: it is what ch0/ch10/ch21 did.

**Not done, deliberately.** A *structural* gate — reject only when `raw*2` or `raw*4` lands
within a few codes of the mean, since that is what bit truncation actually produces — is the
more precise filter and would drop false rejections to ~nil. It is a bigger behavioural change
than this defect warrants and wants its own bench A/B; the new counters are what would justify
it. Removing the gate outright is also defensible (v4.26's IRQ critical section is the primary
defence and this is explicitly secondary) but discards protection that works when it is not
latching.

**Invariants (DESIGN §11) untouched:** no PWM/slice change, no scan scheduler, no flash writes,
no change to the `W` wire format. **Bench-verified 2026-08-11 on the original failing geometry —
see the findings entry above**, and it costs nothing in sweep rate (measured, same entry). Still
outstanding: a fast target sweep. (2026-08-10)

---

### findings — audit of Mode 2 against the wider capture range

Prompted by the v4.35 latch above: with fast, slow and near-stationary waveforms now in the same
sweep, what else in the acquisition path assumes a narrow or slow-moving signal. Everything below
was checked; only the two items folded into v4.35 were changed. Recorded so they are not
re-derived.

**Left alone, by decision:**

- **`cal_3x10_v4`'s first two cells per band are inside ADC saturation.** ch0/ch10/ch20 read 8191
  codes (4999389 µV, positive full scale) for the opening ~140 frames — delays 8.848/9.0,
  7.936/8.0, 5.744/7.0 µs. This is what tripped the gate. The v3 entry already flagged it ("the
  first cells of every band sit inside the saturated region and are unverified"). **Operator
  decision 2026-08-10: leave as is.** With the gate fixed those cells are readable for what they
  are, which is the right basis for any later re-cut. Note `cal_3x10_v4.json` is still untracked
  and its *delays* have never been recorded here — only its `threshold_v` change was.
- **The 32-deep across-sweep rolling average is a ~2.5 s low-pass** at 12.7 Hz, and ClassViz's
  64-frame display median can add ~2.5 s more. For genuinely fast waveforms this is the dominant
  limit, well before the gate. No code change — `averages` is per-profile and tunable — but
  wider-range profiles should pick a depth deliberately rather than inheriting 32.
- **The 10 µs / 25 kHz band caps delay at 29.095 µs** (`pulse_duties_valid`: pulse + delay +
  0.904 µs must fit the period), and `cal_3x10_v4` already sits at 29.0 — 95 ns of margin, as
  DESIGN §10 records. Extending the range on that band is not possible without dropping the
  frequency. The refusal is correct; check an extended profile against it *before* a bench
  session.
- **`service_sensors()` runs inside the sweep loop.** At `i == 0` the DS18B20 scratchpad read
  blocks ~7.6 ms while the PWM free-runs at cell 0's config, once per `DS18B20_INTERVAL_MS` —
  the same class of perturbation as the emit stall in the v4.24/v4.27 notes. Known and bounded;
  logged here so it is not mistaken for a new effect.

**Split out to a ClassViz pass — both done in v1.73, see the entry above:**

- **Saturation is invisible end to end.** `raw14_from_bytes` clips at +8191/−8192, the emitted
  mean carries no flag, and ClassViz has no rail detection anywhere — a railed cell reports
  4999389 µV and reads as a measurement. Six channels spent time there in this session. The
  information is already on the wire, so this is a PC-side marker: flag any cell within ~1 code
  of ±full scale.
- **A rejected `D` leaves the previous dynamic profile live, and the session header lies about
  it.** `check_for_commands` rejects the *whole* `D` on any invalid cell; `dynamic_profile` keeps
  its old value and a following `G` streams the old geometry, while the CSV header records
  `profile_json` from the file. `pimd_delaycal` has guarded this since v1.41 by confirming
  `D OK`; ClassViz's `_on_load_run_profile` fires `E`, `D…`, `Q5`, `G` blind and then applies the
  file's profile regardless. Port delaycal's guard. This gets more likely as the range widens
  into the duty limit above.

**Checked and clear:** `rolling_sum` cannot overflow (256 × 8191 ≈ 2.1 M). The `mean_uV` float
path is fine on RP2040 single-precision floats (worst case < 1 µV at full scale). Sign handling
in `raw14_from_bytes` and in the gate's `abs()` is correct for bipolar data. ClassViz's own
100 mV display gate **cannot** latch — it feeds its median buffer the *raw* value, not the
substituted one, which is precisely the property the firmware gate lacked and the property v4.35
restores; it does still mask real transitions above 100 mV for up to ~32 frames after a step. The
`dd`/`sd` CC-write skip is safe at v4's spacing — the hardware grid is 8 ns on all three bands and
v4's tightest gap (64 ns) is 8 grid steps — but two cells closer than ~8 ns would silently
collapse into one, so keep 8 ns as the hard minimum when cutting wider profiles. (2026-08-10)

---

### profile — `cal_3x10_v4` — the first three delays of every band move out of ADC saturation

The early cells were re-cut by hand in `pimd_delaycal` v1.48 (file saved 2026-08-10 18:06:30; the
profile's own `notes` records the session — no sweep, delays imported or edited by hand, pack
23.39→23.18 V, board 64.4→55.5 °C). Cells 3-9 of every band are unchanged.

| band | cells 0 · 1 · 2 — was | now |
|---|---|---|
| 100 µs @ 3.125 kHz | 8.848 · 9.0 · 12.8 | **10.0 · 11.0 · 13.0** |
| 50 µs @ 5 kHz | 7.936 · 8.0 · 11.904 | **9.0 · 10.0 · 12.0** |
| 10 µs @ 25 kHz | 5.744 · 7.0 · 9.904 | **7.0 · 8.0 · 10.0** |

**This closes the saturation problem the v3 entry flagged and left open** ("the first cells of
every band sit inside the saturated region and are unverified"). On the old ladder, cells 0/1 of
every band read a flat 8191 codes — 4999389 µV, positive full scale — which is a limit rather
than a measurement; the geometry is preserved as `cal_3x10_v4_railtest` and the evidence is in
the v4.35 findings entry above.

**Evidence for the re-cut ladder is one REPL frame, not a recorded session** — `W5,582028,`
`4388599,2841510,759563,483531,64315,83847,…`, whose largest cell is 4.39 V against a 5.0 V rail,
with the null visible as the 64 mV dip at cell 4 (17.52 µs) recovering to 84 mV at cell 5. That
is consistent with clearing the rail on all three bands, but it is a single frame and **no
capture session has been recorded against this ladder yet.** The rationale for these particular
values is the operator's and is not recorded here; the ClassViz v1.73 rail readout is the quick
way to confirm the ladder stays clear across pack state and board temperature, which the v4.35
findings entry shows is exactly what moves it — `cal_3x10_v3` still rails ch0/ch10 at today's
31 °C (`session_20260811_095143.csv`). (2026-08-10)

---

### src/pimd_delaycal.py — v1.48 — Manual Nudge cells take a typed delay, not just −/+ steps

In Manual Nudge, reaching a delay that is far from the calibrated one meant clicking −/+ dozens of
times (the step is capped at 9600 ns, and each click reconfigures the running stream). The cell
readout in the overlay is now a `NudgeCellEdit` (a frameless, transparent `QLineEdit`) instead of a
`QLabel`: **type a delay in µs, press Enter, done**. Transparent and frameless so the item's std-dev
heat colour still shows through — the `QTableWidgetItem` remains the single source of truth, the
overlay only occludes it, exactly as before. Focus selects the existing value so typing replaces it;
the editor gets a visible border and a solid background only while focused.

Typing and stepping share one apply path, `_apply_manual_delay()`, factored out of
`_on_manual_nudge_clicked()`: snap to the 8 ns PWM grid → `_pulse_duties_valid()` pre-check → write
the item → log → `_manual_push_profile()`. So a typed value cannot bypass the duty-limit refusal
that protects against the firmware silently rejecting the whole `D` command (v1.41). A refusal, a
non-numeric entry, or Escape reverts the editor to the item's text, so a half-typed number is never
left standing as if it had been applied — `editingFinished` only fires on validator-acceptable
input, so `focusOutEvent` reverts the unacceptable rest. Leaving Manual Nudge discards an
uncommitted edit rather than applying it on the way out (the commit path is guarded on
`cb_manual_nudge.isChecked()`). A value re-typed identically is a no-op — no log line, no
reconfigure. A blank or `N/R` cell can now be given a delay by typing, which the −/+ buttons
(needing a number to step from) still cannot do.

Space-to-capture-baseline was already guarded against `QLineEdit` focus (v1.39), and `NudgeCellEdit`
is a `QLineEdit`, so typing in a cell does not capture a Compare baseline. Verified headless
(offscreen Qt): grid snapping 12.345 → 12.344, refusal at 39.0 µs on 25 kHz/10 µs (max ≈ 29.095 µs)
leaving the cell untouched, garbage reverting, `N/R` accepting a typed value, −/+ still stepping
through the shared path, and an uncommitted edit discarded on exit. The transparent-background
colour show-through is the one thing offscreen rendering can't confirm — check it on the bench.
(2026-08-10)

---

### profile — `cal_3x10_v4` — `threshold_v` is now an obvious placeholder countdown

The `threshold_v` list in all three bands was still the measured ladder inherited from
`cal_3x10_v1` — `4.85 · 2.17 · 1.05 · 0.48 · 0.19 · 0.07 · 0.017 · 0.016 · 0.015 · 0.014`. Those
numbers are meaningless for `cal_3x10_v4` (nothing was swept against it and no threshold crossing
was measured for any cell), but they still *read* as real measurements, and the bunched
0.017→0.014 tail rendered as four near-identical `{:.3f}V` cell labels in `pimd_classviz`. Replaced
with a plain **5.0 → 0.5 V countdown in 0.5 V steps**, the same synthetic-ladder idiom already used
at `pimd_classviz.py:558`. The `notes` field now states outright that the field is a placeholder and
an ordering key only.

Nothing load-bearing moved. `threshold_v` is consumed three ways: as the cell ordering key
(`argsort(-threshold_v)` in `pimd_classviz`, `sort by -threshold_v` in `pimd_shape` /
`pimd_corpus_check`), which needs only strict descent — preserved, and the sort is still the
identity permutation; as a unique `(freq_hz, pulse_us, threshold_v)` dict key in
`pimd_delaycal._profile_cells` — still 30 distinct keys; and as `_nominal_baseline_uv` behind the
optional `nominal` baseline mode and the crossings label, both of which were already meaningless
against placeholder voltages and remain so. Delays, band geometry and the 8 ns grid are untouched.
(2026-08-10)

---

### .gitignore — KiCad auto-backup zips are ignored

`Electronics/**/*-backups/` — KiCad writes a timestamped zip into `<project>-backups/` every time the
schematic is opened, and they were accumulating as untracked noise in `git status`. The rule is
directory-scoped and does not touch the 11 tracked sources in `Electronics/PIMD604/`. (2026-08-10)

---

### profile — `cal_3x10_v3` — the skip is gone; a geometric ladder replaces it, and the model says the slow pole belongs to the target

**Not locked, not swept, nothing captured against it.** The operator fixed the **first and last delay
in each band by hand**; the 8 interior delays are filled in here as a **geometric ladder** between
them — constant ratio **1.3296 / 1.2762 / 1.1836** per band — snapped to the 8 ns PWM grid. Every
cell is strictly increasing and passes the firmware's `pulse_duties_valid()` check. Geometry stays
3 × 10 = 30.

| band | delays (µs) |
|---|---|
| 100 µs @ 3.125 kHz | 9.24 · 12.288 · 16.336 · 21.72 · 28.88 · 38.4 · 51.048 · 67.88 · 90.256 · 120.0 |
| 50 µs @ 5 kHz | 8.352 · 10.656 · 13.6 · 17.36 · 22.152 · 28.272 · 36.08 · 46.048 · 58.768 · 75.0 |
| 10 µs @ 25 kHz | 6.36 · 7.528 · 8.912 · 10.544 · 12.48 · 14.776 · 17.488 · 20.696 · 24.504 · 29.0 |

**The skip spans are deliberately gone** — with the +97 mV bias fitted no cell is excluded for
railing, so the constraint that shaped `cal_3x10_v2` no longer exists.

**Geometric was chosen after an information-weighted placement was tried and rejected.** Equal arc
length along the three targets' combined log-signature put **nine of ten cells below 18 µs** and left
a 6.5× gap to the fixed 120 µs endpoint, because log-space arc length is dominated by the steep early
fall. Constant ratio gives equal resolution per decade of delay, which is the same principle as the
retired ×1.5 pulse ladder, applied to delays.

**`threshold_v` is carried over from v2 UNCHANGED, and that is deliberate.** It is no longer a
voltage in any sense — nothing was swept — but it is the **cell ordering key**: `pimd_shape` and
`pimd_corpus_check` both sort rows by `(pulse_us, -threshold_v)`, and `pimd_rawlog` already calls the
field vestigial. Writing modelled air voltages there would have been **non-monotonic through the
null** and would have scrambled cell order. The profile's `notes` now says this in the file itself.

**Model fits over the measured window** *(2026-08-10 captures, fitted in log space)*. **Air and brass
need only a single repeated pole** — the free two-pole fit drives τ_fast → τ_slow, and
`(P + Q·t)·e^(−t/τ)` fits identically well. **Steel on the two long bands needs a genuine second,
slow pole, and that is the target's own eddy decay:**

| band | air | brass | steel |
|---|---|---|---|
| 100 µs | τ 1.96 µs · ±5.6 mV | τ 1.79 µs · ±8.5 mV | τf 1.24, **τs 19.0 µs** · ±6.0 mV |
| 50 µs | τ 1.89 µs · ±6.8 mV | τ 1.77 µs · ±8.4 mV | τf 1.18, **τs 23.4 µs** · ±8.7 mV |
| 10 µs | τ 1.78 µs · ±13.4 mV | τ 1.76 µs · ±13.2 mV | τ 1.67 µs · ±12.4 mV |

**The slow pole appears only when a ferrous target is present, and it vanishes again on the 10 µs
band** — a 10 µs pulse barely excites it. That is the same conclusion the fill fractions reached by a
different route (steel filled only 62 % of the null at 10 µs), which is worth something as
corroboration. *Caveat on the fast pole: every capture starts at ~9–12 µs because the window
saturates below that, so a ~1.2 µs pole is far outside the data and **τ_fast is not independently
identifiable here** — treat it as a fitted shape parameter, not a measurement.*

**Three reasons this must not be locked yet:**

1. **Only two cells sit inside the measured polarity window** on the 100 µs band (9.24 and 12.288,
   against §2's 7.97–12.30) where `cal_3x10_v2` had six. Geometric spacing buys tail resolution and
   sells early density. **If the ferrous/non-ferrous sign split matters more than decay-rate
   resolution, this ladder is weighted the wrong way** and wants re-cutting.
2. **Several cells are placed beyond any measurement** — 67.88 / 90.256 / 120 µs (100 µs band),
   58.768 / 75 (50 µs), 29.0 (10 µs). The scope record stops at 55.5 µs.
3. **The first cells of every band sit inside the saturated region** and are unverified. One capture
   per band at a coarser vertical (500 mV/div or 1 V/div) closes this and item 1 together.

`References/images/bias_mod_delay_plot_20260810.png` is the delay plot for this profile — the same
three bands with the fitted models overlaid dotted, so the fit quality is visible rather than
asserted. (2026-08-10)

---

### findings — the bias mod is fitted and the null is real, discriminating signal

**Plan A is built and it works.** 240 k from 5V-REF into U3A pin 3, as specified in the proposal
below. Bench session 2026-08-10, `pimd_gui` Mode 1, scope on the LT6203 input (CH1) with MCLK on CH2
as the sample-instant reference, 64 averages, all three bands, air / RHS steel tube / brass block at
**0 cm** — pressed as close to the inner coil as possible to maximise swing. Nine traces and the
plotting script are in `References/scope/20260810_bias_mod/`; the figure is
`References/images/bias_mod_delay_plot_20260810.png`.

**The design number was met.** The operator had already centred CH1 at **+112.8 mV** before the
session began; the proposal predicted a biased quiescent of **+111.7 mV**. The timing chain also
checked itself: the capture assumed scope t = 0 was sd 15.504 µs and the CH2 rising edge landed at
**15.512** — one 8 ns PWM grid step.

**Air never goes below 67.2 mV** (worst case, 100 µs band), against the old 2.441 mV output floor.
Every cell in the previously-railed window, on all three bands, is now live signal with ≥ 65 mV of
headroom underneath it.

| band | air null bottom | depth below quiescent |
|---|---|---|
| 100 µs @ 3.125 kHz | 67.2 mV at **sd 17.52 µs** | 38.2 mV |
| 50 µs @ 5 kHz | 75.0 mV at **sd 16.10 µs** | 33.7 mV |
| 10 µs @ 25 kHz | 84.5 mV at **sd 13.99 µs** | 30.3 mV |

***This retires the "amplitude-invariant crossing" argument in the entry below.*** That entry
separated an amplitude-invariant zero crossing from an amplitude-dependent rail crossing, and
concluded the null's *timing* was fixed across bands. **Measured, the null bottom itself moves
1.4 µs between 100 µs and 50 µs, and 3.5 µs across the full band set.** The reasoning was incomplete:
pulse width changes the **initial conditions** — how much energy sits in L versus C at release — so
the ratio of the two mode amplitudes changes and `ln(A/B)` moves with it. What survives is the
conclusion the operator's bench edges were right about: the window is band-dependent, and the
per-band brackets in `cal_3x10_v2` were tracking a real shift in the feature.

**Sign is not the discriminant inside the null — fill depth is.** Both families read *positive*
against air there, because air is the thing that dips and both targets fill the dip in. Defining
**fill = 1 − (target dip depth / air dip depth)**, depths taken against each trace's own late level:

| band | brass fill | steel fill |
|---|---|---|
| 100 µs | 52 % | **100 %** — monotonic, no dip at all |
| 50 µs | 38 % | **100 %** — monotonic |
| 10 µs | **8 %** | 62 % |

The two families are **7× apart on the shortest pulse and 2× on the longest**. Note the metric
saturates at 100 %, so the 100/50 µs steel figures are floors rather than measurements. This is a τ
probe read through the null rather than through amplitude — a third mechanism alongside the polarity
split and the late-tail decay rate.

**Both mechanisms are visible in one trace now.** Brass crosses from negative to positive against
air at **~12.3 µs** on the 50 µs band and **~11.7 µs** on the 10 µs band; below that it is the
classic sign split (§2), above it, fill. The crossover marches earlier with shorter pulse, same as
everything else here.

**The case for keeping these cells is SNR, not novelty.** The steel:brass magnitude ratio through
the null is **6–8× on every band** — but out on the tail at sd 30 µs it is 5.8×, i.e. much the same
discrimination. What differs is amplitude: **Δsteel is +187 mV at sd 17.5 against +78 mV at sd 30**,
for a noise floor that does not change with delay. These are the best-SNR cells in the profile.

**Two things only visible when the traces are read cell-by-cell through the null** *(sampled at the
null bottom ±3 µs; reproducible from the CSVs)*:

- **On the 10 µs band brass and air are 3–5 mV apart across the whole null**, against a 12–13 mV fit
  RMS on that band. That is at or below the noise, so **the 10 µs band contributes essentially
  nothing to non-ferrous discrimination in the null** — the 7× fill ratio quoted above is carried by
  the ferrous side alone.
- **Past the bottom, steel's slope is opposite to air's and brass's.** On the 100 µs band air and
  brass recover (67 → 91 mV, 94 → 111 mV over the following 4 µs) while steel keeps falling
  (254 → 223 mV). **The sign of the slope is a cleaner discriminator than the levels**, and reading
  it needs at least two cells past each band's null bottom — a placement constraint that no other
  finding here implies.

**Three things this session did not settle, and the first is load-bearing:**

1. **Everything here is at 0 cm.** Coupling dominates, and a feature that only exists on contact is
   not corpus material. One repeat at 50 mm on the 100 µs band answers it, and **nothing should be
   captured against a filled-in profile until it is answered.**
2. **The top of the decay is unverified.** Everything moved up ~97 mV and the 4.85 V cell now sits
   near 4.95 V against 5.000 V full scale. The scope window clipped above 1.4 V, so this needs a
   delaycal sweep or a coarse capture.
3. **All pre-mod scope values are void.** Air's dip went 29.3 → 38.2 mV, and the bias cannot deepen
   it — a 240 k shunt attenuates ~2 %, which would make it shallower. **The replaced 7815 is the
   likely cause**, which means §7's measured front-end values need re-taking on their own account,
   independently of the bias. (2026-08-10)

---

### hardware — proposal — bias the RX front end ~97 mV so the null stops being thrown away

**Not built. Operator has chosen Plan A; this entry is the record of the design and the acceptance
test, written before anything is soldered.** The motivation is the finding below: the null is real
coil physics, it responds to metal, and `cal_3x10_v2` deals with it by refusing to sample there. If
the region can be lifted into the linear window instead, it is corpus material rather than a hole.

**The mechanism is a single-supply floor, not a fault.** U3A is a unity-gain follower on +12 V and
its output cannot go below ~2.441 mV, so air's excursion below quiescent is clipped. Lifting the DC
operating point at pin 3 lifts the whole transient clear of that floor. **Plan A is one resistor,
no track cuts, fully reversible:**

```
U5 pin 7 (5V-REF) ──[ 240k, 1 % metal film ]──► U3A pin 3
```

Pin 3's DC path to ground is `R8 + R9 + RX coil` ≈ **4.77 kΩ** (the coil's 19.9 Ω shorts out R1's
1304 Ω, so R1 barely features), giving 5.0 × 4770/244770 = **97.4 mV**. Measure R_gnd at pin 3
unpowered and re-derive from `Rb = R_gnd × (5.0 / V_offset − 1)`; the result is insensitive to it.

**~97 mV is the right target, not a round number.** Air bottoms 29.3 mV below quiescent, but air is
not the worst case — the largest measured non-ferrous excursion is −74.4 mV at the ADC, ≈ −65 mV at
the input, so worst-case depth below quiescent is ≈ 94 mV. 50 mV would clip the strong non-ferrous
targets that are the whole point.

***Corrected during the design:*** an earlier sketch split the bias into 2 × 120 k with 100 nF at
the midpoint and called the signal-node loading 2.5 %. **Both parts were wrong.** With the cap at
the midpoint the node sees 120 k against `R9 + R8` = 4.747 kΩ, which is **3.8 %** attenuation; a
single 240 k sees 240 k against the same, **1.9 %**. The LTC6655 is quiet enough not to need the RC,
so the single resistor is preferred — fewer parts, half the signal loss, easier to remove.

**Take the bias from 5V-REF, not +5V or +12V.** That net is the ADC's own reference, so offset and
full scale drift together and the code does not move. Use metal film: the new thermal term is
`97 mV × divider tempco`, ~2.5 µV/°C at 25 ppm/°C (invisible) but ~300 µV over a 30 °C soak at
100 ppm/°C, which is at the noise floor on a project whose first open problem is thermal drift.

**Acceptance test — re-run the 2026-08-08 scope capture at the LT6203 input with the bias fitted:**

| | before | predicted after |
|---|---|---|
| air quiescent | +14.34 mV | **+111.7 mV** |
| air lobe bottom | −15 mV | **+82.4 mV** |
| worst-case non-ferrous (−65 mV at input) | below the floor | **+32.4 mV** |
| input-referred output floor | 2.12 mV | unchanged |

The pass condition is the strongest non-ferrous target at closest coupling staying above ~2 mV at
the input.

**What it costs, and it is not small.** **LTC2508 pin 6 (IN−) is grounded** *(operator confirmed)*,
so the ADC reads `IN+ − 0` and the bias appears in the data: every `threshold_v` in the ladder
moves, the pedestal goes ~16.5 → ~113 mV, and this is **a new profile, a new sha and a new
measurement epoch**. Top-end headroom also tightens — the 4.85 V cell becomes 4.947 V against
5.000 V full scale, 53 mV of margin — so re-anchor the top early cell to ~4.70 V at recalibration.

**Timing, which is the decision that actually matters.** A corpus run was imminent. Capturing 30
cells now and then fitting this resistor means capturing twice, because nothing before the mod is
mergeable with anything after it. **Fit, scope-check, then decide** whether the profile becomes
3 × 10 with the middle filled in or stays as it is.

**Plan C, recorded but not chosen.** The spare half of the same physical DIP-8 (sheet 2's `U18B` —
sheet 2's designators are known wrong, and its pin 7 lands on TP24) could buffer the same bias onto
the ADC's IN−, making the offset cancel differentially: the ladder would stay valid, only the newly
visible middle would need sweeping, and drift would be common-mode. It costs three cuts —
`R80`/`R82` links out, IN− lifted from GND, RX cold end floated onto V_b. **If Plan A shows real
discrimination information in the null, build Plan C before capturing**, because Plan A as a
permanent fitting spends an epoch for no reason.

**Open before anything is cut:** whether R1 is through-hole (Plan C lifts its ground leg), and D3's
reverse leakage once permanently back-biased by ~100 mV — Schottky leakage roughly doubles per
10 °C, and a few hundred nA through R9's 4.7 kΩ at the 54.8 °C board temperature is a few mV of
temperature-dependent error. Probably lost in the noise; worth a bench look, not an assumption.

**R1 is untouched, so ζ = 1.06 is unchanged, and no §11 invariant is involved.** No firmware change.
(2026-08-10)

---

### findings — the below-rail window is band-dependent, and §7's single figure is a 100 µs number

**Operator bench result: the rail window shifts and widens with band energy.** The edges of each
band's skipped span were tuned by hand — nudging the bracketing cell's delay until it climbs off the
**~2.4 mV** rail onto the **~16.5 mV** pedestal — **independently per band, not derived from the
scope capture.** Read off the lock, the brackets are:

| band | last clean early cell | first clean late cell |
|---|---|---|
| 100 µs @ 3.125 kHz | 13.0 µs | 30.0 µs |
| 50 µs @ 5 kHz | 12.352 µs | 24.0 µs |
| 10 µs @ 25 kHz | 10.36 µs | 18.44 µs |

**The mechanism is consistent with §7's two-pole model, and it is worth separating two things that
had been conflated.** The *zero crossing* is amplitude-invariant: it sits at
`ln(A/B) / (1/τ_f − 1/τ_s)`, and driving harder scales both residues together so `ln(A/B)` does not
move. But **the rail is not zero — it is a fixed 2.441 mV floor**, and where a curve crosses a fixed
threshold depends on its depth. The lobe's depth scales with band energy, so a deeper lobe crosses
the floor earlier and climbs out later. Same null, different below-rail window. That is exactly the
ordering the bench found.

**So §7's `sd 14.23–18.44` is a 100 µs / 2 kHz figure, not a global constant**, and the sentence
"any new profile must clear sd 14.23–18.44" over-generalises a single-condition reconstruction to
all three bands. Worth rescoping at the next consolidation pass. Note also that pack voltage scales
the decay (§12), so these crossings drift with state of charge within a session — the brackets are
a bench-tuned centre, not a hard edge.

***Correction to the `cal_3x10_v2` entry below:*** that entry moved the 10 µs band's first late cell
**18.0 → 18.44 µs** on the grounds that 18.0 "may still be inside the rail", reading the 100 µs
band's reconstructed rail exit as if it applied to the 10 µs band. **It does not** — the 10 µs band
has the shallowest lobe and therefore the *earliest* rail exit of the three, so 18.0 was already
clear, which is the operator's assessment from the independent bench tuning. **The stated
justification for v2 is withdrawn.** The move itself is harmless — 18.44 is on the 8 ns grid,
validates clean, and 0.44 µs later on the pedestal costs nothing measurable — so **`cal_3x10_v2`
stands as the lock** rather than churning a v3 for no gain, and no corpus exists against either
version. What is retired is the reasoning, not the file.

The pattern is the same one the v2 entry itself called out an hour after writing it: **a
single-condition measurement quietly applied outside the condition it was taken in.** First time it
was a placeholder column read as data; this time it is one band's rail exit read as every band's.

`References/images/profile_3x10_timing.png` is redrawn accordingly — the shaded window is a wedge
following the per-band brackets rather than one rectangle across all three lanes. (2026-08-10)

---

### References/images — `profile_3x10_timing.png`, the sample-timing map for `cal_3x10_v2`

A figure for the blog, tracked here because it is also the clearest single picture of the operating
geometry. Three lanes, one per band, on a log delay axis: the six amplitude-anchored early cells,
the four time-anchored late cells, and the below-rail window shaded across all three — which lands
in the gap in every lane, because that is what the profile exists to do (§7, §10). *(Superseded on
the same day by the findings entry above: the window is drawn as a per-band wedge, not as a single
rectangle, and the 10 µs band's annotation is corrected.)*

**The delays are read from `src/data/profiles/cal_3x10_v2.json` at render time, not transcribed**,
so the figure cannot drift from the lock it describes; only the rail bounds are hard-coded, from §7.
The generator is a one-off and deliberately **not** in the repo — `utilities/` was retired at the
epoch turnover and `src/*.py` is live tool source, so a throwaway figure script belongs in neither.
Regenerating it means rewriting it, which is the right cost for something this small. (2026-08-10)

---

### DESIGN.md / .gitignore — Doc-rev 1.15.7 — content already carried by CHANGELOG.md is cut, and the superseded profiles come back into the repo

Operator trim, plus repair of the artefacts it left. No new bench data.

**Cut from DESIGN.md as duplicated history rather than current design fact:** §12's U1 dissipation
cost bullet (≈ 2.5 W → ≈ 4.6 W across the discharge) and its ADC error-budget RSS bullet (≈ 92 mV
pack-referred, ≈ 53 mV available ratiometrically off the LTC6655, identified not built); the
standing caution about regulated-window claims taken over a narrow interval; the retired
`cal_63_air_bat_v3` 21.5–23.3 V data-quality window with its 22.5–24.0 V transition band; the
idle-drain-vs-streaming 15× and session-planning arithmetic, and the ≈ 0.29 V measured IR drop; the
"highest-value unmade measurement" note (the +15 V rail under scope during a TX pulse, fresh pack vs
near-flat); §13's footnote on what retired with the 63-cell epoch; §14 open problems 8–12 (threshold
noise zone, classification-layer rebuild, the `Sn_Pb_solder_spool_01` id collision, the missing
within-placement quality gate, fw v4.34's outstanding bench acceptance); and §16's recalibration
procedure. **All of it is in this file — the findings stand, and none of them are withdrawn.**

**Four consequences of the cut are repaired.** The `---` rule before §14 had been left as `--`, so
it rendered as text. Two stray spaces went (`*(measured)*. ` and `pedestal** .`), as did a doubled
blank line in §12. The §14.8 / §14.9 / §16 cross-references pointed at sections that no longer
exist — each is dropped rather than left dangling, with the substance it pointed at stated in place:
delaycal's §15 row now says *why* Import Profile comes first (persisted settings are not anchored to
the locked profile, so a stale baseline is inherited, band plan included) instead of pointing at the
deleted procedure.

**1.15.6's own text no longer described the file.** It stated that two enclosure references were
deliberately kept, one being §12's note that the dissipation is trapped inside a sealed enclosure —
that bullet is one of the ones cut here, so the Hardware rev line is now the only enclosure
reference and the Doc-rev block says so.

**All six superseded calibration profiles are restored to the repo** — `cal_3x10_v1`,
`cal_63_air_bat_v3`, `cal_63_air_v1`, `cal_63_air_v2`, `cal_72_air_v2`, `cal_72_air_v3` — recovered
from git history, where each had been untracked at its retirement. **This reverses the
track-by-exception convention:** `.gitignore` no longer carries a per-lock retirement list, so it is
no longer the authoritative record of which locks are retired (1.15.5 relied on it for exactly
that), and a retired lock can no longer be lost by a working-copy accident. §15's profiles row is
rewritten to match. `.gitignore` also loses rules for `REDO.md` and `assets`, neither of which
exists. (2026-08-10)

---

### DESIGN.md — Doc-rev 1.15.6 — the 2026-07-13 enclosure is no longer a measurement epoch

**Operator assessment: fitting the shielded enclosure did not materially move what was being
measured at the time.** All "pre-enclosure" staleness framing is removed from DESIGN.md
accordingly — §3's flyback, RX front-end node voltages, sample-timing precision and thermal drift
now stand as current rather than as historical reference awaiting re-measurement.

**The 2026-07-13 epoch row survives, re-attributed.** That date bundled two changes, and only one of
them is being retired as a reset: **fw v4.24 made Mode 2 boundary settling time-floored**, which
genuinely voided Mode 2 per-cell values and delay tables (§8 — it was the root cause of the
first-heatmap-column noise). The enclosure went on the same day and rode along in the framing. §1's
table now names fw v4.24 as the reason and drops the enclosure from it.

**Two enclosure references are deliberately kept, because they are build facts rather than staleness
claims:** the Hardware rev line, and §12's note that the doubled U1 dissipation sits **inside a
sealed shielded enclosure** on a project whose first open problem is thermal drift. That last one is
the one place the enclosure does bite, and it is a live concern, not a stale measurement.

**§12's supply-noise table keeps its caveat, on the other reason.** Those rows were taken on the
**5S** pack that the 6S supply replaced — a different supply, a real and specific reason to
distrust them — so "5S / pre-enclosure, stale on both counts" becomes simply 5S. §14.2 is retitled
from "Post-enclosure / post-6S re-measurement backlog" to "Re-measurement backlog" and rescoped: the
unreconciled ±200 µV / ±450 µV filtered-path pair stays its first item, now on the grounds that
neither has been measured on current hardware rather than on epoch grounds.

**The Doc-rev block is compressed from ~57 lines to a terse lineage**, matching the one-line-per-
version header convention `CLAUDE.md` sets for source files. It had accreted six stacked revisions
of prose — including archaeology about a tagging scheme that no longer exists — which is the
accretion §18 exists to prevent. Full detail for every rev is in this file. (2026-08-09)

---

### DESIGN.md — Doc-rev 1.15.5 — §10 epoch ledger dropped; §3's per-value epoch tags become one sentence

Operator trim, plus repair of two artefacts that came with it. No new bench data.

**Dropped from §10:** the epoch-ledger table of superseded profiles, and the 63-cell / 45-cell rows
of the sweep-rate table. A retired profile's lineage belongs in this file and in git history, not in
the working brief; `.gitignore` remains the authoritative list of which locks are retired, and every
superseded JSON is still on disk and still usable as a delaycal comparison reference. **Verified
before removing the pointer:** all four sha8s — `4a2352d2`, `89590f69`, `b4bee9d2`, `def96704` — are
present in this file, so nothing became unfindable.

**Changed in §3:** the per-value `[pre-enclosure]` tags are replaced by a single statement in the
section banner naming the five pre-enclosure quantities (flyback, RX front-end node voltages,
sample-timing precision, thermal drift, and the on-slope noise row). Same information, less markup.
This mattered because the tags had been removed while the banner still *defined* the tag — which
would have left those five values reading as current again, the exact defect Doc-rev 1.15.2 was cut
to fix. The `[63-cell]` tags are unchanged.

**Two artefacts repaired.** The tag removal left **empty backtick pairs and stray spacing**
(`*(measured)* .`, `after R9 : `, a table row with trailing double-spaces), and a line in §10 was
**truncated mid-word** — `r sweep and a 3-band`, the front of the sentence gone. The truncated
sentence explained the 63-vs-33-cell rate difference, and with those rows deleted, restoring it
verbatim would have pointed at data no longer present; it is rewritten to stand alone: measured on
fw v4.34, rates from earlier firmware are not comparable because v4.34 delivers the full boundary
settle it had been short-changing, and **`cal_3x10_v2` has not been rate-measured yet**.
(2026-08-09)

---

### DESIGN.md — Doc-rev 1.15.4 — §13 and §10 described the retired profile, not this one

**§13 "What makes this design unusual" was largely a description of `cal_63_air_bat_v3`.** Four of
its claims are false of `cal_3x10_v2`, and §10's "Design principles (**carried across every
epoch**)" repeated two of them under a heading that made the error worse.

| claim | reality on `cal_3x10_v2` |
|---|---|
| "Geometric pulse ladder (×1.5)" | pulses are **100 / 50 / 10 µs** — ratios **2× and 5×** |
| "evenly spaced slice of log target-τ" per band | log₁₀ gaps are **0.7 and 0.3** — not even |
| "sampling the **0.5 – 4.9 V** band" | span is **4.85 V down to the ~16.5 mV pedestal** |
| "amplitude-anchored **thresholds** … the matrix self-normalising" | only the **6 early** cells are amplitude-anchored; the **4 late** ones are at fixed delays |

The ×1.5 figure was exact on the retired profile — its ratios run 1.49–1.50 across all seven bands —
so this is not a rounding quibble. It is a **design principle that was dropped at the epoch change
and never written down as dropped**, which is the same failure class as the rest of today's audit:
the statement stayed true-sounding while the thing it described was replaced.

**What the design actually is now, and it is a more interesting story than the one it replaced.**
The ladder is a **hybrid of two anchoring schemes**, because the front end makes the two halves of
the decay carry different information (§2):

- **6 early cells, amplitude-anchored** on the volt-scale decay — this is where target **polarity**
  separates families, so voltage is the right anchor. They inherit the pack-scaling cost (§12).
- **4 late cells at fixed delays** on the tail, landing on the pedestal — past the front end's lobe
  **both families read positive**, so sign is not a discriminant and **decay rate** is what
  separates them. Time is the right anchor there, and amplitude anchoring would sample the wrong
  quantity.
- **Nothing in between**, because that is where the unipolar front end rails (§7).

Conventionally a PI profile picks one anchoring scheme. Using one here would have sampled the wrong
quantity in one half of the ladder.

**Three-band spacing is a bench judgement, not a derived optimum**, and §10 now says so: three bands
cannot tile log-τ evenly, and the plan trades τ resolution for sweep rate (63 cells 6.49 Hz → 33
cells 11.49 Hz). The old ×1.5 rationale — constant-ratio spacing gives equal discrimination
information per slice — was a real principle and is recorded as retired rather than deleted.

**Two follow-ons in the same class.** §14.7 (possible TX coil-current plateau above ~67 µs) rested
entirely on the retired ladder's band-to-band clip-release increments; `cal_3x10_v2` has no 67 µs
band, so that comparison **cannot be repeated** — re-scoped, and noted that the question matters
more now, since the 100 µs band is one of three rather than one of seven. And a boundary worth a
bench check is recorded: §2's measured polarity window on the 100 µs band is **sd 7.97–12.30 µs**,
while two of that band's six early cells sit **outside** it (7.48 and 13.0 µs) — so the polarity
split may be carried by four cells there, not six. Flagged, not asserted: that window was measured
against one target pair, and its ends are where the split narrows rather than vanishes. (2026-08-09)

---

### DESIGN.md — Doc-rev 1.15.2 / 1.15.3 — staleness audit, and R1 is two resistors in parallel

**A full pass for claims of the same kind as the withdrawn damping figure**: internally consistent,
but undated, from a retired epoch, or propping up something newer. Five found. **Three are
regressions the 1.15 consolidation introduced**, which is the useful lesson — a trim that removes
qualifiers is a way of *creating* stale statements, not just of shortening the document.

1. **§3's epoch banner was gutted.** The pre-1.15 text read *"every value below was measured before
   the shielded enclosure"* — a blanket claim covering the whole section. 1.15 replaced it with a
   per-value tagging scheme and then tagged almost nothing, silently promoting flyback, the RX
   front-end node voltages, sample-timing precision and thermal drift to "current". §3 now carries
   explicit `[pre-enclosure]` / `[63-cell]` tags and states that untagged means current.
2. **Two unreconciled filtered-path noise figures.** §3 gives ≈ ±200 µV, §7 gives ≈ ±450 µV for the
   same SDOA path — 2.25× apart, both pre-enclosure, and §7's boxcar arithmetic is built on the
   larger. The pre-1.15 doc flagged this; 1.15 dropped the flag. Restored in **both** sections and
   promoted to the head of §14.2. Nothing downstream depends on it (the acquisition path is raw,
   where ±1400 µV is consistent throughout), which is how it survived — but one of the two is wrong.
3. **§3 and §17 disagreed on epoch tags for the same numbers.** `splithalf_floor`, the
   between-session component and the 70–130 ps timing jitter are tagged `63-cell` in §17 and were
   untagged in §3. Now consistent.
4. **SoC's "4 min warm-up" is a bench-supply figure** and warm-up is longer on the pack; the caveat
   was dropped in 1.15 and is restored, along with Mode 2 warm-up's "untested on `cal_3x10_v2`".
5. **§17.1's ~0.5 A was tagged "all epochs"** — it was measured on the 63-cell profile and the §12
   capacity figures rest on it. Now tagged, with a duty check recorded as *inference*: mean band
   duty goes 28.1 % → 27.1 % across the profile change, so the figure should carry, but it has not
   been re-measured.

**Then the substantive finding, from the bench rather than the document: R1 is two resistors in
parallel and the schematic does not show it.** Brown-green-red-gold ∥ brown-black-black-red-gold =
**1.5 kΩ ∥ 10 kΩ = 1304 Ω**, where schematic v6.04 draws a single `R1 1.3k`. That is within
**0.33 %** of the value the front-end fit assumed, so **no measured result moves** — but the
schematic is what a future reader will trust, and it is wrong. Recorded as new open item §14.5a,
with the suggestion that a single 1 % part would be preferable to a ±5 % pair.

**The best thing to come out of it: ζ does not depend on R at all.** For a parallel RLC the fitted
poles alone fix it —

> ζ = (τ_f + τ_s) / (2 √(τ_f · τ_s)) = **1.0622**

— because C ∝ 1/R and L ∝ R, so √(L/C) ∝ R and the R cancels. **The over-damped verdict is therefore
immune to the R1 uncertainty and to the ±5 % tolerance**, which is a much stronger statement than
the document previously made. L and C individually *do* move with the assumed R (577 pF / 4.43 mH at
1304 Ω against the published 579 pF / 4.41 mH at 1300 Ω — a 0.33 % shift kept as published, being far
inside the fit's own uncertainty).

Consequently the ζ-vs-R table is **relabelled as substitution sensitivity**, not as uncertainty in
this build: it holds the fitted L and C constant and asks what a *different* resistor would do, so
it inherits the R = 1300 assumption and is a guide to picking a part rather than a measurement. Read
that way it still says something worth knowing — a ±5 % pair spans 1239–1370 Ω, and the upper corner
sits ~10 Ω from critical. (2026-08-09)

---

### DESIGN.md — Doc-rev 1.15.1 — the legacy critical-damping figure is withdrawn as corroboration

**Question asked, and it was the right one: is the front end under- or over-damped?** The answer is
**over-damped, mildly, ζ = 1.06**, and it is consistent everywhere — but checking it surfaced a
stale claim propping up the fit.

DESIGN §7 carried an undated bench note, *"critically damps at ≈ 1.3–1.4k (measured)"*, and the
`RX L and C — pinned` block cited it as **independent corroboration** of the 2026-08-08 fit,
saying that "two quantities obtained years apart by different means agreeing to a few per cent is
why these are recorded rather than left open". **That corroboration is withdrawn.** The note is in
the very first repo commit (2026-06-22) with no date of its own, so it predates all recorded
history; it also predates the June 2026 front-end rework, and it describes an RX network that may
not be this one. It is not a check on the current values.

**The fit does not need it.** C = 579 pF, L = 4.41 mH, R_crit = 1381 Ω rest on the 2026-08-08 scope
measurement alone — 894 points, residual RMS 0.87 mV, taken at the amplifier input on the current
hardware. What changes is the *warrant*, not the numbers.

**The practical consequence is worth more than the retraction, because that band straddles the
boundary.** Damping is a shunt, so lower R means more damping:

| R1 | ζ | |
|---|---|---|
| **1300 Ω — as built** | **1.06** | over-damped, the intent |
| 1381 Ω | 1.00 | critical |
| 1400 Ω | 0.99 | **under-damped — ring returns** |

So the legacy "1.3–1.4k critical" band is **not a range to pick R1 from**: its top end is
under-damped by the current fit. Anyone swapping R1 to 1.4k on the strength of that line would
reintroduce ring. §7 now states the ζ table explicitly and marks the old band historical.

Two smaller repairs in the same pass. The **direct RX self-resonance measurement** is promoted in
priority — with the corroboration withdrawn it is the only thing that would confirm L and C
independently of a transient fit. And the guard against re-deriving **ζ = 1.00** is restored: it was
cut as narrative in the 1.15 consolidation, but it is a methodological warning, not history —
assuming the critically-damped form and fitting τ = 2RC can only ever report ζ = 1.00, and did, on
2026-08-07. Cutting it made the same mistake available again. (2026-08-09)

---

## Archive — consolidated 2026-08-09

### profile — `cal_3x10_v2` closes the last open question: no cell sits inside the rail

The one thing the `cal_3x10_v1` entry below deliberately left open is now shut. That profile's
10 µs band placed its first *late* cell at **18.0 µs**, while the reconstructed below-rail window
runs to **sd 18.44** (§7) — so the single cell most likely to still be clipped was in the very
profile cut to eliminate clipped cells. It moves to **18.44 µs**, the measured rail exit itself.
Nothing else changes: the diff is three lines — `name`, `notes`, and that one delay.
**sha8 `def96704`** (was `89590f69`). `cal_3x10_v1` is retired to the superseded list without ever
having been captured against. (2026-08-09)

**This is the cheapest this change will ever be, which is why it happens now.** The profile was
locked less than two hours ago and **no corpus exists against it** — so retiring it orphans
nothing, splits no dataset, and costs no recapture. The same edit made after a capture campaign
would have meant a new `(profile_name, profile_sha8)` group that `pimd_features` refuses to merge
with the first, i.e. throwing away or re-running the campaign. Locked profiles are never edited in
place, so this is `cal_3x10_v2` as a new file, not a corrected v1.

**Checks run before writing it, not after.** 18.44 µs is **exactly on the 8 ns PWM grid**
(2305 × 8 ns — the firmware cannot produce a delay between grid points, so an off-grid value would
have been silently rounded to something nobody chose); `_validate_profile_pwm()`, the client-side
mirror of the firmware's `validate_profile()`, returns clean; the ladder stays monotonic; and the
profile round-trips through `_apply_profile()` at 3 / 10 / 30 with a `D` command that builds. Worth
noting the 10 µs band's headroom is genuinely tight — **max valid delay 29.095 µs against a
largest-used 29.0 µs**, about 95 ns of margin, unchanged by this edit but not much to give away.

***Correction, same day, before any capture:*** this entry originally claimed that the moved
cell's `threshold_v` of **0.017 V** had gone stale — that it was a pedestal figure *measured* at
18.0 µs and no longer described a cell now sitting at the rail exit — and called for a re-measure
or a v3. **That was wrong, and it contradicted the `cal_3x10_v1` entry below, which already had it
right.** The last four `threshold_v` values in **every** band (`0.017, 0.016, 0.015, 0.014`) are
**placeholders for the pedestal, not measurements of anything.** The 1 mV steps exist only to keep
the ladder monotonic. Only the six *early* values are measured voltages.

So moving a late cell's delay invalidates nothing: a placeholder does not describe where its cell
sits and was never claiming to. **No v3 is needed and no re-measurement is owed.** The rule that
matters for anyone reading this column later is the one the v1 entry already states — *the four
late values are not four distinct measurements and should not be mined as such* — and it applies
uniformly across all three bands, at whatever delay each late cell ends up at.

Recorded rather than edited away, because the mistake is instructive: the drift happened between
two entries written an hour apart, where the second treated a column the first had explicitly
flagged as placeholder data as though it were measured. **A column that mixes measured and
placeholder values is exactly the kind of thing that gets mis-mined later** — which is the reason
the v1 entry called it out in the first place.

**The pack-voltage window is now carried in the profile's own `notes`** — "full charge down to
21.5 V" — rather than living only in a CHANGELOG entry. §10 requires a profile to be specified
together with a voltage range, and the file is the thing that gets loaded, copied and handed
around; a lock that has to be cross-referenced against a changelog to be fully specified is
half-specified in practice.

---

### repo — `pimd_classify.py` archived to history, then deleted; `src/*.py` is now all repo source

The classification/heatmap surface goes the same way as the rest of the previous epoch, but in
**two commits rather than one, and the ordering is the entire point.** `pimd_classify.py` was
untracked at `ff3b619` as a previous-epoch ML tool, and the newest copy in any commit was
`2f7f58a`'s **v1.2** — while local development had continued to **v1.5**. Deleting straight from
the working tree would have silently destroyed three versions that existed nowhere else. So it was
force-added first (**`08c9892`**, ~97 KB, verified byte-identical to the working tree before the
removal) and deleted second. (2026-08-09)

What that saved, and why it was worth a commit:

- **v1.3** — heatmap rows sorted delay-descending to match the standard grid orientation.
- **v1.4** — heatmap band order keyed on `pulse_us` rather than the `delays_us[0]` proxy. This is
  the one that mattered: `25d6a9a` made the identical fix in `pimd_classviz` v1.71 and recorded
  that *"the two must agree or one profile renders two different ways"*. Deleting unarchived would
  have left a **paired** change with one half committed and the other half gone, and a CHANGELOG
  entry describing code that no longer existed anywhere.
- **v1.5** — `DEFAULT_CORPUS` repointed out of the `ML/` tree deleted in `16edf75`.

**This is the opposite call to `pimd_v2_findings.py`**, deleted an hour earlier with no archive
commit — and the difference is not inconsistency. That file was checked against its history copy
and found **byte-identical**, so history already held everything; this one was three versions
ahead. The rule worth carrying forward: *before deleting an untracked file, diff it against the
newest copy in history — untracked does not mean unrecoverable, and tracked-once does not mean
tracked-current.*

**Nothing depended on it.** No module imports it anywhere in `src/` or `mcu/` — verified, the only
reference is a comment in `pimd_delaycal.py` citing it for a shared display convention, which
needs no code. It was a leaf: it consumed `pimd_features`, `pimd_corpus_check` and
`pimd_v2_findings`, and nothing consumed it. It had also stopped running entirely — an
`ImportError` once `pimd_v2_findings` went, on top of the older `pimd_features.DEFAULT_PROFILE`
`AttributeError` that killed it at argument parsing.

**Consequences.** The `.gitignore` block covering the 2026-07-13 "previous-epoch ML tools" is gone:
all three files it named are resolved (`pimd_corpus_check.py` re-tracked 2026-07-15, the other two
deleted), and **every `src/*.py` is now repo source** with nothing ignored in its place. Its
`src/data/classify_settings.json` went with it — gitignored, so invisible to the repo, but a
settings file for a tool that no longer exists is just a thing to wonder about later. **Retiring a
tool means retiring its settings file too**, which is the precedent worth having here. `USAGE.md`
→ **v1.31** records the deletion in §6 with the recovery shas for both files and the warning that
reviving one means reviving both. *For the next §18 consolidation pass:* §15's `src/pimd_classify.py`
row (still describing v1.3) should go, and §1's pipeline diagram and the "fourth tool in the
gui/classviz/delaycal/classify family" framing no longer hold — it is a three-tool family plus
`pimd_rawlog`.

---

### repo — `utilities/`, `ML/`, `References/scope/` and `References/Targets v1 Analysis/` retired at the epoch turnover

Four directories removed now that `cal_3x10_v1` has replaced `cal_63_air_bat_v3` (entry below).
All four served the previous epochs and none of them describes the instrument as it now stands:
`ML/V1` and `ML/V2` are **72-cell**, two epochs stale, and were already superseded by
`pimd_classify.py`; `References/Targets v1 Analysis/` is the offline analysis of the 2026-07-23
**63-cell `cal_63_air_v2`** corpus; `References/scope/` and `utilities/` are the measurement and
tooling behind work that has since been consolidated into DESIGN §7 and §12. The outputs worth
keeping were copied into `References/images/` first — `6S-pack-discharge-curve.jpg`,
`decay_model.png`, `lobe_at_amp_input_20260808.png` and `spanner_fills_the_null_20260808.png`.
(2026-08-09)

**Recoverability is not uniform, and that is the important part of this entry.**
`utilities/` (9 files) and `References/scope/` (5) were tracked and are retrievable in full at
**`59a9117`** — e.g. `git show 59a9117:References/scope/air_wide_20260808.csv`. **`ML/` (24 files)
and `References/Targets v1 Analysis/` (7) were gitignored and had never been committed, so they
are simply gone** — no history, no copy, ~4.8 MB. That was chosen deliberately rather than by
accident, which is why it is written down here: nobody should later go looking through the log
for them.

**Findings that keep their result but lose their tool.** Each of these stands on its own in this
file; what goes is the ability to *re-run* it from a clone. Named individually because a
one-line "utilities removed" would make them unfindable:

| tool | what it produced |
|---|---|
| `decay_model/decaymodel.py` (v5) | the two-pole front-end model of §7 — τ_fast/τ_slow, ζ, the null, the below-rail reconstruction |
| `decay_model/make_sweep_profile.py` | the characterisation sweep profiles (`sweep_*_decay_v1`) |
| `soak_vs_voltage/soakvolt.py` | the 2026-07-30 pack-voltage result (§17.13) — the finding the tracked-utility rule was written to protect |
| `pack_discharge/packv.py` | the SoC curve `pimd_gui.py` copies (its comment still cites the path; the table is duplicated in four tools and is unaffected) |
| `session_relabel/relabel.py` | the reconstructed `# mark:` lines in five session dumps, each stamped `reconstructed cos=… src=…` — those dumps keep their marks, but the reconstruction cannot be redone or audited |
| `mode2_noise/mode2_cell_noise.py` | the cell-0 outlier investigation that traced the ±120/−200 mV population to the blocking emit |

**DESIGN §15's tracked-utility rule retires with the directory.** That rule — *"a utility cited
from `CHANGELOG.md` has to be tracked"* — exists because `soakvolt.py` nearly stayed local and
would have left the project's headline pack finding unreproducible from a clone. It was the right
rule while `utilities/` existed. With the directory gone it now guards nothing, and leaving it in
place would make the next person think a tracked copy must be somewhere. **Recorded here as a
deliberate retirement, not an oversight.**

**Checklist for the next §18 consolidation pass** *(DESIGN.md is regenerated from this file, not
edited directly — these are the rows that will otherwise dangle)*: drop the §15 inventory rows
for `utilities/`, `References/scope/` and `References/Targets v1 Analysis/`; drop §15's
tracked-utility rule; drop the two §16 offline run commands that invoke
`utilities/decay_model/decaymodel.py` and `make_sweep_profile.py`; and check §15's
`src/data/sessions/` row, which cites `utilities/session_relabel/` for the reconstructed marks —
the marks survive, the tool does not, and the row should say so. Also repath the two
`References/training-results-v1b.png` / `-v1c.png` rows, which moved into `References/images/`
with the rest of the kept figures — same files, tracked as renames, new location.

**Three more files go with the same sweep.** `HANDOFF_cell_reduction.md` is retired because its
question has been **answered**: it was the 2026-08-03 brief asking which rows and columns of
`cal_110_full_range_v4` (10 × 11 = 110 cells) could be dropped "without losing information, to cut
sweep/frame time and thermal exposure", and `cal_3x10_v1` — 30 cells, 6.49 → 11.49 Hz — is the
answer. A handover doc outlives its usefulness the moment the handover completes. Also
`sweep_100us_asbuilt_20260808.json`, the reconstruction of the superseded 68-cell ladder (§10),
and `sweep_150us_decay_v1.json`.

**That last one is half of a documented pair, and the consolidation pass needs to know.** §10's
*"Characterisation sweeps — `sweep_100us_decay_v1` / `sweep_150us_decay_v1`"* subsection and
§15's inventory row both describe the two together as the 66-cell single-band sweeps built to
model the decay rather than sample it. **`sweep_100us_decay_v1.json` survives and stays tracked;
the 150 µs half does not.** The §10 subsection and the §15 row should be rewritten around the one
that remains rather than left describing a pair that no longer exists. The 150 µs sweep is
retrievable at **`16edf75`** like the rest of this cleanup, and §10's reasoning for why the pair
existed at all — `cal_110_full_range_v4`'s 150 µs band puts only two columns between clip release
and the rail, and two points cannot constrain a decay — stands as written and should be kept.

**`src/pimd_v2_findings.py` deleted too** — the v1.0 reproduction script for `ML_Findings_v2.md`,
which went with `ML/` above, so it was reproducing a document that no longer exists. Gitignored
since `ff3b619` untracked it, but **tracked before that and byte-identical to the copy at
`84471fe`** *(checked, not assumed)*, so it is recoverable despite not being in the current index.
Its `.gitignore` rule goes with it.

**It takes `pimd_classify.py` with it, and that is worth stating rather than discovering.** That
tool does not merely import it — it delegates its band-mean / crossing-continuum physics to it at
eleven call sites (`bandmeans()`, `crossing_us()`, `continuum()`, and the hand-curated `FAM3`
campaign-2 ground truth), by deliberate design: *"reuses, does not reimplement"*. So
`pimd_classify.py` now fails at **import** as well as at argument parsing. In practice this
changes nothing — it was already unrunnable for the `DEFAULT_PROFILE` reason above, it is
gitignored, and its whole feature set is 63/72-cell — but anyone reviving it needs both
`84471fe:src/pimd_v2_findings.py` and a decision about what it should classify against in a
30-cell epoch.

**Not touched by any of this:** `src/data/corpora/` keeps both 63-cell corpora. They are
previous-epoch and cannot be mixed into a 30-cell dataset, but they remain the only corpora on
disk and `pimd_shape.py --selftest` still expects them (§14.15).

**`src/pimd_classify.py` v1.4 → v1.5** — its `DEFAULT_CORPUS` pointed at
`../ML/V2/PIMD_target_corpus_signatures_v2.csv`, which stopped existing, so the default is
repointed at `src/data/corpora/gui_signatures_targets_v3_20260728_142316.csv` and the `--corpus`
help text corrected. The file is gitignored and so is not in this commit; recorded here because
a silent dangling default is exactly the kind of thing that surfaces months later as a confusing
traceback.

***Flagged, not fixed — and it is worse than a dangling default.*** `pimd_classify.py` does not
currently run **at all**: `build_arg_parser()` reads `pimd_features.DEFAULT_PROFILE` for its
`--profile` default, and `pimd_features` has no such attribute, so every invocation dies with an
`AttributeError` before parsing a single argument — GUI and `--headless` alike. **This predates
the ML/ removal and is unrelated to it**: `DEFAULT_PROFILE` was removed from `pimd_features`
deliberately (its own header comment records *"validate_profile/DEFAULT_PROFILE/--profile
removed"*), and `pimd_classify.py` was never updated to match. Left alone on purpose: it is a
gitignored previous-epoch tool whose defaults are 63/72-cell, and repairing it means deciding
what it should point at in a 30-cell epoch that has no corpus yet — a real piece of work, not a
one-line fix, and not one to fold silently into a cleanup.

---

### profile — `cal_3x10_v1` is the new corpus starting point; the null cells are gone and the matrix is less than half the size

**3 bands × 10 cells = 30 channels**, `averages: 32`, sha8 **`89590f69`**. Bands 3125 Hz/100 µs,
5000 Hz/50 µs, 25000 Hz/10 µs. Per band the ladder is **6 early samples, a skipped span, then 4
late samples** — the skips are **13→30 µs** (100 µs band), **12→24 µs** (50 µs) and **10→18 µs**
(10 µs). This replaces `cal_63_air_bat_v3` (7 × 9 = 63) as the operating profile and is the
geometry the next capture campaign is built on. It was arrived at on the bench as best
representing the range of targets, and it is the first profile in this project cut with the
front-end model in hand rather than by sweeping and hoping. (2026-08-09)

**Why the middle cells are gone.** The front end has two real poles with opposite-sign residues
(τ_fast 1.125 µs, τ_slow 2.270 µs, ζ = 1.06), so air has exactly one zero crossing and swings
negative — measured at the LT6203 input as **sd 14.3 → 18.0 µs**, bottoming **≈ −15 mV** (§7).
The path is unipolar and the output **rails at 2.441 mV**; reconstructed through the 1.149
input→ADC gain, air is genuinely **below the rail for 4.21 µs, sd 14.23–18.44**. §14.17 is the
consequence and it is the whole argument: Δ = target − air, and where air is clipped up onto the
floor the subtrahend is too large, so **the delta is always understated — by up to ~3.5×** (at
sd 17.3 µs the ADC records **+6.3 mV** where the input shows **~+22 mV**). Those cells do not
merely add noise. They compress amplitude non-linearly and by an amount that depends on target
strength, so every band mean, crossing width and amplitude feature computed over them inherits
that bias. Cutting them out of the geometry is the cheapest possible fix: no feature code has to
learn about the rail, because nothing is sampled there any more.

**What that costs, stated plainly.** The null is **real coil physics, not an artefact** — it is
present *before* the amplifier and it **responds to metal**: a steel spanner on the coil removes
the crossing entirely (minimum +15.5 mV, difference up to **+48.9 mV** at sd 13.57 µs). And the
rail is an **air** problem, not a cell problem — a close ferrous target lifts the whole trace
clear of it, so the same cell that is dead in air is perfectly live on a strong target. Dropping
these cells therefore trades a target-present signal for a **bias-free** corpus. That is a
deliberate choice and it should be revisited if the classifier turns out to want that region;
it is not a free win.

**The lineage, all of it on 2026-08-09, all on fw 4.34.** Read off the session dumps in
`src/data/sessions/` — the embedded `profile_json` / `profile_sha8` headers are the primary
record, since none of this line of work was written down until now:

| profile | sha8 | geometry | measured sweep rate |
|---|---|---|---|
| `cal_63_air_bat_v3` (outgoing) | `4a2352d2` | 7 × 9 = 63 | **6.49 Hz** |
| `cal_3x15_v2` | `fd369286` | 3 × 15 = 45 | **8.77 Hz** |
| `cal_3x15_v3` — *"middle nulls removed from v2"* | `baf9019e` | 3 × 11 = 33 | **11.49 Hz** |
| **`cal_3x10_v1`** (new) | `89590f69` | **3 × 10 = 30** | no session yet |

Rates are the median of each dump's `firmware_time_ms` deltas, so they are on the firmware clock,
and all four were taken on the same bench within an hour of each other. **The 63-cell profile
nearly doubles in rate at 33 cells** — which is the direct answer to `next.txt`'s "our current
system is slow to acquire due to large profile matrix".

*Inference, not measurement, on one point:* 6.49 Hz for `cal_63_air_bat_v3` is **below** the
0.1445–0.1455 s / 6.88–6.92 Hz §17.13 records for that same profile on 2026-07-30/31. Firmware
v4.34 now delivers the *full* boundary settle it had previously been short-changing, and a 7-band
profile pays that seven times per sweep where a 3-band profile pays it three. If that is the
cause it is a second, independent argument for fewer bands — but the v4.34 acceptance figure
(§14.18) is still outstanding and this is one 77-frame session, so it wants confirming rather
than asserting.

**`cal_3x15_v3` → `cal_3x10_v1` is one more early cell per band.** Dropped `8.32` µs (100 µs
band), `7.744` µs (50 µs) and `6.0` µs (10 µs) — the second sample in each row — **as noisy and
carrying no information the neighbouring cells did not already have** *(bench observation)*. The
profile's own `notes` field now describes the final geometry rather than the v2→v3 step it used
to record.

**`threshold_v` in this profile is measured voltage, not a nominal target ladder,** and that is a
change of meaning worth flagging because delaycal's `threshold_v` normally records the voltage a
swept delay was *aimed at* (`_targets_v`). Here it is uniform across all three bands and reads
**4.85, 2.17, 1.05, 0.48, 0.19, 0.07** for the six early cells and **0.017, 0.016, 0.015, 0.014**
for the four late ones. Those last four are the **~16.5 mV front-end pedestal** (§7: +14.34 mV at
the input, **16.472 mV** at the ADC), which is exactly what a late sample is *for* — the decay is
over and what is left is the front-end DC. The 1 mV steps between them keep the ladder monotonic;
they are not four distinct measurements and should not be mined as such.

**What this invalidates.** Both corpora on disk are 63-cell and **cannot be migrated** into a
30-cell epoch — `gui_signatures_targets_v1_20260723.csv` (4 158 rows, `cal_63_air_v2`/`b4bee9d2`)
and `gui_signatures_targets_v3_20260728_142316.csv` (11 844 rows, `cal_63_air_bat_v3`/`4a2352d2`).
The `(profile_name, profile_sha8)` guard in `pimd_features.py` refuses to build across them by
design, and §10 is explicit that an identical cell count would not have implied comparability
either. `ML/V1` and `ML/V2` are 72-cell and were already two epochs stale. On the tooling side
nothing needs changing: classviz rebuilds its dims from the profile and discards the
old-geometry air reference, `pimd_classify` derives geometry from the colmap, and **no firmware
change is required** — this rides in the RAM-only `D`/`Q5` dynamic slot, as every 3x15 session
already did. `cal_63_air_bat_v3.json` moves to `.gitignore`'s superseded-locks list and
`cal_3x10_v1.json` becomes the tracked profile, per the procedure in that file's own comment.

**The pack-voltage window: full charge down to 21.5 V — the whole usable pack.** §10 requires a
profile to be specified together with a voltage range, and this is it. **21.5 V is not an
arbitrary floor:** it is where the firmware's low-voltage failsafe re-arms (§12), it is the
dashed edge already drawn on the pack gauge in all four PC tools (`PACK_WINDOW_LO_MV`), and the
LOCKOUT floor sits below it at 21.0 V. The epoch's capture window is therefore bounded by
something instrumented and on screen rather than by a number the operator has to hold in their
head — and the board stops the run itself at the bottom of it.

**This is wider than §12's 21.5–23.3 V clean window, deliberately, and it is a bench judgement
about *this profile* rather than a correction to §12.** The relevant precedent is already in the
record: the 2026-07-24 survey found the suspect columns elevated at **22.4 V**, which the 07-30
rule calls clean, and §17 resolves that tension only as a hypothesis — *"the clean window may
belong to **(pack voltage × profile delays)** rather than to pack voltage alone"*, since the zone
sits at a fixed place on the decay and each profile's delays cut the decay at different points.
`cal_3x10_v1`'s delays are entirely new and were cut against the front-end model, so it has no
particular reason to inherit `cal_63`'s window. **That is consistent with the hypothesis, not
confirmation of it** — DESIGN is explicit that it is "a hypothesis, not a result", and one
profile behaving well over a wider range does not settle it.

What the widening buys is concrete. §12's discharge budget writes off `full → 23.3 V` as
**1.78 h, 17 % of the pack**, "unusable, above the data-quality ceiling", leaving **4.55 h** as
the session-planning number. Capturing from full down to 21.5 V instead makes it **≈ 6.33 h per
charge, +39 %** — the difference between one capture campaign per charge and two. The obligation
that comes with it is that every capture records the voltage it actually ran at, which classviz
v1.72 now does by itself on every `# pack_v:` line. If the wide window does cost quality at the
top end, that per-frame track is what will show it. This is a testable widening, not an
assumption; the sessions that established the geometry already span it, running at **24.30 V**
down to **21.94 V** with the board at **54.8 °C**.

**One thing this entry deliberately leaves open: the 10 µs band's first late cell sits at 18.0 µs,
and the reconstructed below-rail window runs to sd 18.44.** It may still be inside the rail. The
100 µs and 50 µs bands clear it comfortably (first late cell at 30 µs and 24 µs); the shortest
band is where the margin is tightest, and the below-rail figure is a reconstruction from one
scope condition rather than a per-band measurement. Worth one check before a corpus is built on
it — a railed cell is precisely what this profile exists to remove, and it would be an unhappy
irony to ship one.

---

### src/pimd_classviz.py — v1.72 — pack voltage and board temperature from firmware telemetry; Pack V / Log V removed

The `Pack V` spinbox and the `Log V` button are gone, and with them the 20-minute
`PACK_V_REMIND_S` nag. Both readings now come off the wire: `P<time_ms>,<pack_mV>,<board_temp_dC>`
(unsolicited, ~60 s) and fields 8..10 of the `V` identify reply, shown on the same `BatteryGauge` /
`BarGauge` widgets `pimd_gui` uses — pack SoC with its §12 zone colour, board temperature to
0.1 °C. **Why the hand-entry had to go rather than be supplemented:** v1.64 added it precisely
because a 6S pack falls ~2.5 V across a long run and none of it was recorded, but a typed number is
only as complete as the operator's memory, and the 2026-07-29 dump — the one the warm-up findings
rest on — has **1h51m between two readings**, which is exactly where interpolating voltage onto the
frame timeline is least defensible. The firmware has been reporting this on the same wire since
v4.28. Nothing polls: the gauges are primed by the `V` already in `connect_port()`'s handshake
(sent while the rig is idle) and refresh from the firmware's own cadence, so no command is ever
injected between `W` records. (2026-08-09)

**Session dump.** Every accepted reading now appends its own
`# pack_v: <iso>, <volts>, age_s=<n>, temp_c=<c|none>` line while recording, so the voltage track
is complete by construction and a board-temperature track exists for the first time — warm-up and
battery sag are the two confounders that move a session's levels, and only one of them was being
written down. `temp_c` is appended to the same `key=value` tail `age_s` lives in, which
`pimd_features._parse_kv_tail` hands back as strings and ignores when unknown, so **the new field
is additive and every existing reader keeps working** — verified by round-tripping a written dump
through `pimd_features.parse_session_file()` and `pack_v_at()`. The literal `none` rather than a
number when the DS18B20 gave no reading, for the same reason `-32768` is never displayed: a later
reader has no way to tell a sentinel from a temperature. `age_s` changes meaning — it is now the
age of the *firmware's* report (normally under 60 s), not seconds since the value was typed — and
the header gains a `# sensor_source:` line so a dump says which regime produced it. `PACK:` and
`LOCKOUT` firmware messages are marked in as `# mark: firmware: …`; frames after a latched lockout
are not the same experiment as frames before it, and offline there was no other way to know.

The `P` branch anchors on a digit after the tag, which is load-bearing and is the defect
`pimd_gui` v4.17 was cut to fix — a bare `P` test also matches `PACK: …` and the boot banner, which
split on commas into an `IndexError` once per pack power-cycle. `'lockout cleared'` is matched
explicitly for the same class of reason: that message contains the word "lockout" while meaning the
opposite, so a substring test would latch on it and invert the state. The age label beside the
gauges retargets from nagging a human (20 min) to reporting that the board went quiet
(`SENSOR_STALE_S` 180 s ≈ three missed reports). The persisted `pack_v` settings key is no longer
written or restored; a stored one is ignored. Constants, SoC maths and both gauge widgets are
duplicated from `pimd_gui.py` rather than imported, per the standing rule that every PC app in
`src/` stands alone — the four copies (`pimd_gui`, `pimd_rawlog`, `pimd_delaycal`, here) must be
retuned together. **`pimd_features` is deliberately not touched**: it reads the extended track
correctly today, but it does not yet expose `temp_c` as a parsed field or a corpus column, and
doing that is a schema change with its own blast radius.

---

### src/pimd_delaycal.py — v1.47 — pack / board-temperature gauges, and the conditions a calibration was measured under

A calibration is only comparable with another if the conditions match (§14.1), and until now the
conditions were **not recorded anywhere at all** — the exported profile's notes carried the sweep
parameters and the geometry, but nothing about the pack or the rig's thermal state, which is the
variable heavy-band delays actually move with (tens of ns cold-to-warm, §10). This adds a `Rig
State` group to the left column with the same `BatteryGauge` / `BarGauge` widgets `pimd_gui` uses,
fed by the firmware's `P` telemetry and primed by a `V` sent once on connect. (2026-08-09)

The readings are folded into a conditions span reset at connect and again at Run, and that span —
pack first→last (min) and board temperature first→last (max) — is written into the exported
profile's `notes`, alongside a new `#` header block in the exported CSV (export timestamp, tool and
firmware version, sensors at export, the same span). The span deliberately keeps running through
the THERMAL soak and Auto Nudge that follow a sweep, because those refine the delays the profile
ships with. A temperature the firmware could not read is folded in as nothing at all, never as a
number, so a missing DS18B20 cannot drag the recorded minimum to something that looks measured.

**Placement in the serial reader is the load-bearing part.** The new branches sit *ahead* of the
`_pending_d_ready` gate: an unsolicited `P` can land in the window between `D` being sent and its
reply arriving, and that gate consumes every line it sees. They also sit ahead of the
`'ERROR' in raw` catch-all. Nothing here sends a command while a sweep or a soak is running — an
injected command would interleave with the `R` records the sweep state machine advances on — so
the gauges live entirely on the firmware's own ~60 s cadence after the one idle `V`. A latched
`LOCKOUT` now stops a running sweep: past that point the table is being filled with readings taken
against a pack the firmware has cut, and nobody should calibrate against those. The `P` isdigit
guard and the `'lockout cleared'` special case are carried over verbatim from `pimd_gui` v4.17 and
`pimd_rawlog` v1.15 — see those entries for why both are not simplifiable. Constants, SoC maths and
both widgets are duplicated from `pimd_gui.py`, not imported, per the standing rule that every PC
app in `src/` stands alone.

---

### src/pimd_delaycal.py — v1.46 — calibration table rows pulse-ascending, matching the two thermal tables

The two thermal tables (mean, std dev) have sorted their rows by `pulse_us` since v1.17
(`_thermal_display_order`); the calibration table above them stayed in protocol/JSON order, which
the v1.17 comment recorded as deliberate. With `cal_3x15_v1` — protocol order 100 / 50 / 10 µs —
that left the top table reading 100/50/10 while the two below it read 10/50/100. All three now
read top-to-bottom in pulse-ascending order, the project's standard grid orientation (lowest
top-left, highest bottom-right).

**Done as a `QHeaderView` section move, not as a permutation of the data, and that choice is the
whole point of the change.** The calibration table's row index doubles as the **protocol band
index** in ten places: `_build_profile()`, `export_csv()`, `_fill_cell()`, `_mark_row_pending()`,
`_start_auto()`, `_auto_finish()`, `_auto_color_cell()`, `_on_manual_nudge_clicked()`, and the two
thermal colour mirrors in `_update_thermal_tables()`. Several of those *write* a calibration.
Permuting the data would mean getting a protocol↔display mapping right at every one of them, and
getting it wrong in `_build_profile()` would silently pair the wrong delays with the wrong band in
an exported profile — a corruption with no visible symptom until a capture campaign came out
strange. Moving header sections leaves every logical index untouched, so all ten stay correct by
construction and only the screen changes. `_on_manual_nudge_clicked()` is the clearest example: it
uses its row argument both to address the table *and* to index `_fp_pairs` for its log label, and
under this approach both remain right with no edit at all.

**`_fp_pairs` is deliberately not reordered.** It drives the `D` command, so its order *is* the
sweep order — rotating it would move which band sits at which sweep position, and this week's work
has established that sweep position is exactly the variable under investigation.

Verified by driving the real `_rebuild_table` / `_apply_cal_row_order` / `_fill_cell` against
`cal_3x15_v1` under an offscreen Qt: display reads 10 / 50 / 100 µs top-to-bottom, while
`table.item(0, ·)` still returns the 100 µs band's own delays and the full band↔delay round-trip
is intact. Three Qt behaviours were checked rather than assumed — `moveSection()` works
programmatically even though `sectionsMovable` is False (so rows still cannot be dragged by hand),
`clear()` + `setRowCount()` do **not** reset section order (hence the re-apply on every rebuild,
or a stale permutation would survive a profile change), and the move loop converges from any
starting state. Switching afterwards to the 7-band `cal_63_air_bat_v3` renders
9/13.44/20/30/45/67.2/100 with no residue. (2026-08-09)

---

### src/pimd_classviz.py — v1.71 / src/pimd_classify.py — v1.4 — heatmap band order keyed on pulse_us, not the `delays_us[0]` proxy

`cal_3x15_v1` (3 bands: 3125 Hz/100 µs, 5000 Hz/50 µs, 25000 Hz/10 µs) rendered its heatmap rows
**50 / 10 / 100 µs** on both the Main and Analysis sheets — neither the profile's own band order
nor the project's standard grid orientation, which `pimd_rawlog.py`'s header declares as
**lowest top-left, highest bottom-right**.

Cause: `_band_display_order` sorted on `bands[i]['delays_us'][0]`, the band's *first delay*, as a
stand-in for pulse width. That holds for every calibrated profile — a shorter pulse releases the
clamp earlier, so first delay and pulse width ascend together — and v1.70 adopted it having
explicitly verified only that `cal_110_full_range_v4` behaves that way. The proxy fails the
moment two bands are given the **same delay ladder by hand**: `cal_3x15_v1` starts both its 50 µs
and 10 µs bands at 5.160 µs, the tie fell to protocol order (50 before 10), and the 100 µs band's
7.480 µs sorted last. Sorting on `pulse_us` is what the orientation rule actually means, so the
key is now the quantity itself rather than something correlated with it.

**Scope, checked rather than asserted:** across all eleven profiles in `src/data/profiles/`, the
old and new keys produce an identical permutation for ten of them — every tracked and operating
profile included (`cal_63_air_bat_v3`, `cal_110_full_range_v4`, both `cal_72` generations, all
the `cal_100_10_x15` variants). `cal_3x15_v1` is the only one that moves, and it moves from
50/10/100 to 10/50/100. The change is a no-op on every capture ever taken.

Fixed in **both** tools. `pimd_classify.py` carried the same proxy with the same comment
(its v1.3 was the sibling of classviz v1.70) and would have rendered the same profile the same
wrong way — one profile displaying two different ways across two tools is worse than either being
wrong alone. `pimd_delaycal.py` already sorted its thermal rows on `pulse_us`
(`_thermal_display_order`), which is corroboration that pulse width is the intended convention
rather than a new decision made here.

Ties between equal pulse widths now keep protocol order, Python's sort being stable — which is
what a profile carrying a deliberately duplicated band (`cal_100_10_x15_v1_3band`) wants.
`_pulse_sort_order` is left as a separate name even though it is now the same permutation: it
expresses a different requirement ("vs pulse width" plotting on the Analysis tab, not grid
orientation) and the two only coincide while both are defined as pulse-ascending. Noted in place
so neither is collapsed into the other. (2026-08-09)

---

### Findings — the cell-0 population is caused by the EMIT. Not the band boundary, not settling, not dwell.

`cal_100_10_x15_v1_3band` (97a12499) was run under fw v4.34, 1427 frames / 143 s / 9.95 Hz. It
fills the open cell of the factorial and closes the question. The 25 kHz/10 µs @ 5.160 µs cell,
absolute >100 mV gate, Poisson errors:

| run | emit? | energy step? | settle at that cell | events per 1000 |
|---|---|---|---|---|
| `cal_100_10_x15_v1` pos 0 | **yes** | yes | 3 ms | **32.6 ± 5.0** |
| **3-band pos 0** | **yes** | **no** | **none — `needs_settling` is False** | **28.1 ± 4.4** |
| `_bandswap` pos 15 | no | yes | 3 ms | 0.0 ± 0.7 |
| **3-band pos 30** | **no** | **yes** | **3 ms** | **0.0 ± 0.7** |

**The emit alone reproduces the population at full strength.** 28.1 ± 4.4 against 32.6 ± 5.0 is
indistinguishable, and it is produced at a cell with *no* band boundary, *no* energy step and *no*
settle sleep whatsoever. Removing the emit takes it to exactly zero in two independent runs.

**The within-run control is the strongest evidence in this whole investigation.** ch0 and ch30 are
the same frequency, same pulse, same delay, same profile, same sweep, the same second of the same
capture — the only difference between them is which one follows the emit. Over 1426 sweeps:
**ch0 151 events (min −205, max +129 mV), ch30 zero.** Not "fewer": zero.

**Dwell is excluded over the full range tested.** The population appears at ~0 ms of settle (here,
where the wrap changes neither frequency nor drive duty) and at ~16 ms (the v4.35 10 ms-floor run,
10 ms settle + ~6 ms emit) at statistically the same rate, while every *settling* gradient in the
profile responds strongly to that same range. Settling and this population are different
phenomena and always were.

**So the residual mechanism is the emit itself, and it is configuration-selective.** The bandswap
run put the emit in front of the 3.125 kHz/100 µs cell and got 0.0 per 1000, so it is not simply
"the cell after the emit". It is the emit *and* the 25 kHz/10 µs operating point. Dwell is out and
the code path is byte-identical for both bands, which leaves the electrical environment during and
after the USB TX burst — a ~250-byte W record is four packets and TX continues for milliseconds
after `print()` returns, through cell 0's conversion. At 25 kHz a conversion completes every 40 µs
so the BUSY-synced read lands inside that window; at 3.125 kHz the next conversion is up to 320 µs
away. **Per CLAUDE.md this is not decidable from the code and wants the scope** — trigger on the
USB D+/D− activity and watch the LT6203 output and the LTC2508 reference.

**Two firmware options exist that do not require knowing the mechanism**, both cheap and
reversible, and neither is a redesign: (a) decimate the emit via `MIN_EMIT_MS` and confirm the rate
falls proportionally — a one-constant causality check; (b) **move the emit's service point off
`i == 0` to a sweep index whose following cell sits on the pedestal**, where a corrupted sample
costs nothing (cells 13/14 of the 25 kHz band read 15–16 mV at 1 LSB of σ). (b) is a real fix
rather than a diagnostic and would leave the informative top-of-decay cells clean, but it is a hot
path change and the v4.13/v4.20/v4.24/v4.26 sequence is fair warning that it needs its own A/B.

**Secondary, and a caution for profile design.** The same run shows the 100 µs band reading
*higher* and *noisier* in the 3-band profile than in the 2-band one — 4874.3 mV / σ 12.14 against
4845.8 / 9.59 at 7.48 µs, and 3885.3 / σ 23.05 against 3852.4 / 10.87 at 8.32 µs. Thirty of the
forty-five cells are now the low-power band, so the rig runs cooler and the 100 µs band's energy
step is *larger* relative to steady state. **Band composition changes the operating point of the
other bands** — which is §10's "a profile is only fully specified together with a pack-voltage
range" extended to a dimension that was not previously written down. The two identical 25 kHz
bands also differ by **34 mV** at 5.160 µs (4874.1 at position 0 vs 4839.8 at position 30) purely
from position-30's under-settling, a direct measure of the residual boundary bias at a 3 ms floor.
(2026-08-09)

---

### src/data/profiles/cal_100_10_x15_v1_3band.json — new — within-run factorial separating the emit from the energy step

Diagnostic profile, not a calibration. Three bands × 15 delays = 45 cells:
**25 kHz/10 µs, 3.125 kHz/100 µs, 25 kHz/10 µs**, where the two 25 kHz bands are *byte-identical*
— same frequency, same pulse, same delays. The same physical configuration therefore appears at
sweep position 0 **and** position 30 inside one sweep, at the same pack state, the same thermal
state and the same run. Every comparison so far has been between runs; this is the first within-run
control.

**The design turns on a property of `needs_settling`, not on the repetition.** Because band 2 is
also 25 kHz/10 µs, the wrap from position 44 into position 0 changes neither the frequency nor the
drive duty, so `at_boundary or dd != cells[prev][2]` is **false** at position 0 — verified against
the firmware's own arithmetic. That cell gets the blocking emit and *no* boundary settle and *no*
energy step. Position 30 gets the 100 µs → 10 µs energy step and its settle but *not* the emit.
The two confounded factors are separated, and combined with the existing runs the four-cell
factorial is complete:

| | emit | no emit |
|---|---|---|
| **energy step** | `cal_100_10_x15_v1` pos 0 — **32.6 /1000** | `_bandswap` pos 15, this profile pos 30 — **0.0 /1000** |
| **no energy step** | **this profile, pos 0** — the open cell | — |

Reading the result at 25 kHz/10 µs @ 5.160 µs on the absolute >100 mV gate: population at pos 0
only ⇒ the emit alone is sufficient and the energy step is irrelevant; at pos 30 only ⇒ the energy
step alone is sufficient and the emit is irrelevant; at both ⇒ each is independently sufficient;
at neither ⇒ the two are required together, which is what the existing 32.6 vs 0.0 pair implies
and which would point squarely at the emit's interaction with the low-power band rather than at
either factor alone.

Validated before writing: all 45 cells pass the firmware's `compute_pulse_duties` /
`pulse_duties_valid` arithmetic, all three bands carry 15 delays (the `D` command rejects unequal
bands), and the `D` string is 337 chars against 227 for the two-band profile — longer than
anything sent so far but well inside what the 110-cell profiles already require. Expected sweep
~117 ms (~8.5 Hz) at 45 cells and two real boundaries, so the 32-deep rolling window spans ~3.7 s.

Two operational notes. `pimd_delaycal` labels rows by freq/pulse, so **two rows will look
identical**; its thermal tables sort by `pulse_us` with a stable sort, giving display order
band 0, band 2, band 1 — top row is the position-0 copy, middle row is the position-30 copy,
bottom row is the 100 µs band. And `_meas_cache` / any keying on `(freq, pulse, delay)` collides
between the two copies; the session `colmap` carries `band_index`, so `mode2_cell_noise` separates
them correctly (smoke-tested on a synthetic 45-channel session: planted 52.2 outliers per 1000 on
ch0, recovered 44.5, and the identical ch30 correctly reported 0.0 with no false positive).
(2026-08-09)

---

### Findings — SETTLE_FLOOR_US 10 ms was tried and reverted: it fixes settling, and it kills the dwell hypothesis

`SETTLE_FLOOR_US` was raised 3000 → 10000 µs (briefly FW_VERSION 4.35), flashed, run, and
**reverted the same session**. No shipped version carries it, so this is recorded as a finding
rather than a version entry — but the experiment answered two things and should not be re-run
blind. The constant's comment block in `pimd_mcu.py` carries the short form.

**It fixed the settling, comprehensively.** Equivalent timing jitter, first five cells of each
band, across all four runs (`session_20260809_133725` / `_133928` at 3 ms, `_140356` / `_140331`
at 10 ms; "emit" marks the band that sat at sweep position 0 and therefore also received the
~6 ms blocking emit inside its settle window):

| band | floor | at position 0 (**+ emit**) | at position 15 (settle only) |
|---|---|---|---|
| 3.125 kHz / 100 µs | 3 ms | 2.1 2.3 1.9 1.5 1.4 ns | 8.1 7.8 5.3 3.7 4.1 ns |
| 3.125 kHz / 100 µs | **10 ms** | 1.1 1.4 1.4 0.7 1.4 ns | **3.3 3.9 3.0 2.2 2.7 ns** |
| 25 kHz / 10 µs | 3 ms | 2.5 2.2 2.3 2.1 2.6 ns | 2.4 5.2 5.2 4.3 5.2 ns |
| 25 kHz / 10 µs | **10 ms** | 2.5 1.3 1.4 1.4 1.3 ns | **1.0 2.2 2.3 2.1 2.6 ns** |

Every position-15 gradient collapses to roughly the emit-fed figure, and the emit-fed positions
improve again on top. The tool stops flagging a boundary gradient anywhere. The ~9–11 ms transient
estimate is confirmed a second time, and 10 ms covers it.

**It did not touch the cell-0 outlier population, and that is the valuable part.** The 25 kHz /
10 µs @ 5.160 µs cell at sweep position 0, absolute >100 mV gate, with Poisson errors:

| run | events / sweeps | rate per 1000 |
|---|---|---|
| v4.34, 3 ms, original | 43 / 1321 | 32.6 ± 5.0 |
| v4.34, 3 ms, bandswap (same cell at pos 15) | 0 / 1425 | 0.0 ± 0.7 |
| 10 ms, original | 6 / 258 | 23.3 ± 9.5 |
| 10 ms, bandswap (same cell at pos 15) | 0 / 210 | 0.0 ± 4.8 |

32.6 ± 5.0 against 23.3 ± 9.5 is **no change within the error** — and the 10 ms runs are only
20–24 s / 211–259 frames, which is ample for σ (a MAD over ~250 differences) but far too short for
a rate claim off six events. The conjunction holds identically under both floors: the population
appears only where the 25 kHz/10 µs band meets sweep position 0, and position 0 occupied by the
100 µs cell is 0 events in both firmwares.

**So variable emit dwell is not the mechanism.** At a 10 ms floor cell 0 receives ~10 ms of settle
plus the ~6 ms emit — roughly 16 ms at its own configuration before its sample, against a
transient that every other measurement in this profile says is over by ~11 ms. Every settling
gradient in the profile vanished at that dwell. If the population were the emit's *duration*
moving the sample around on a relaxing curve, it would have gone with them. It did not. What
remains is something about the emit that is not its length — USB TX burst coupling into the front
end or the LTC2508 reference is the standing candidate, and per CLAUDE.md that is not decidable
from the code.

**Why it was reverted despite fixing settling.** The floor is global and the cost is real:
12.07 → 10.53 Hz on this profile, and ~6.2 → ~4.8 Hz on `cal_63_air_bat_v3`'s seven boundaries,
against the 6.88–6.92 Hz DESIGN §8 records as that profile's measured rate — and frame rate is
part of the firmware↔ML contract, not a free parameter. The 10 ms number was measured on a **12.5×**
adjacent-band power step (P ∝ pulse²×freq); `cal_63`'s bands step ×1.5 and very likely never
needed it. The right shape, if a characterisation profile wants it, is a **per-boundary floor
scaled to the actual energy step**, not a larger global constant. (2026-08-09)

---

### Findings — the band-swap experiment: settling needs ~10 ms, and cell 0's outlier population is a *conjunction*

Two 2026-08-09 sessions under fw v4.34, **two minutes apart**, same pack and same thermal state —
`session_20260809_133725` (`cal_100_10_x15_v1`, 056797db) and `session_20260809_133928`
(`cal_100_10_x15_v1_bandswap`, 2c205e24) — as controlled an A/B as this rig gets. Scored with
`mode2_cell_noise` on the **absolute** 100 mV excursion gate, matching cells across the two runs
by `(freq, pulse, delay)`.

**The cell-0 outlier population is neither cell-bound nor position-bound. It needs both.** The
25 kHz/10 µs @ 5.160 µs cell runs **32.6 events per 1000 sweeps** at sweep position 0 and
**0.0** at position 15 — the same physical cell, same delay, same firmware, minutes apart. So it
does not follow the cell, which rules out a purely analogue, cell-intrinsic mechanism (clamp
release, converter ceiling). But the cell that *takes over* position 0 in the swapped profile —
3.125 kHz/100 µs @ 7.480 µs — is also **0.0**, so it does not follow the position either. The
artefact requires the 25 kHz/10 µs configuration **and** the sweep position that carries the
emit. Neither prediction in the v4.34 entry was right, and the conjunction is the more useful
answer: it is not "cell 0 is noisy", it is "the emit interacts with the low-power band".

**Settling: whichever band gets the emit comes out clean, and both bands need it.** The emit
costs ~6 ms (from the 82.8 ms sweep: 30 cells × ~2.3 ms + 7.8 ms of delivered settle), and it
lands entirely inside the settle window of whichever band sits at position 0. Equivalent timing
jitter for the first five cells of each band:

| band | at position 0 (settle **+ emit**) | at position 15 (settle only) |
|---|---|---|
| 3.125 kHz / 100 µs (4800 µs settle) | 2.1, 2.3, 1.9, 1.5, 1.4 ns | 8.1, 7.8, 5.3, 3.7, 4.1 ns |
| 25 kHz / 10 µs (3000 µs settle) | 2.5, 2.2, 2.3, 2.1, 2.6 ns | 2.4, 5.2, 5.2, 4.3, 5.2 ns |

σ falls 3–4× on the 100 µs band and ~2× on the 25 kHz band. **Both floors are still too short:**
4800 µs and 3000 µs both leave a gradient, and only the extra ~6 ms removes it. The boundary
transient for this 12.5× power step therefore runs **~9–11 ms**, which confirms by *manipulation*
the ~8–10 ms inferred from the v4.33 data. `SETTLE_FLOOR_US` wants to be ≈ 10 000 for a step this
size — measured evidence for the number v4.34 deliberately deferred. Cost would be ~+12 ms per
sweep on this profile and ~+49 ms on `cal_63_air_bat_v3`'s 7 boundaries, so it is a real trade,
not a free win.

**The §17.7 "first-column noise" model needs a refinement.** In the swapped run the 25 kHz band's
*first* cell (position 15) is its **cleanest** at 2.4 ns while its 2nd–5th sit at ~5 ns. Only the
first cell of a band gets a settle `sleep_us` — a fixed, well-defined dwell. Every later cell has
`remaining` go negative (overrun, no sleep at all), so its sample lands wherever ~2.3 ms of
interpreter time happens to put it, while the band is still relaxing. The excess is not "the first
column is bad", it is "cells 2–5 ride the transient with undamped timing". That is why raising the
floor helps them: it moves the whole band past the transient before any of them sample.

**Correction to the v4.34 entry's caveat.** That entry warned the pack had fallen 24.30 → 22.65 V
and would confound the firmware A/B. The 24.30 V is `pimd_classviz`'s operator-entered `pack_v`
header field (`age_s=unknown`), and it is stale and identical in all three sessions. The
**firmware's** own readings are 22.959 V (12:36, in that session's `V` string) and 22.652 V
(13:26) — a 0.31 V change, ~13–16 mV of decay amplitude. The v4.33/v4.34 comparison is therefore
much better controlled than that caveat claimed.

**And the header is not stale data — it is an unimplemented consumer.** `pimd_classviz`'s
`pack_v` is a manually-typed spinbox (`sp_pack_v`, with a `PACK_V_REMIND_S` 20-minute nag), and
the file contains **no** reference to `pack_mV` or `board_temp_dC`: it never reads the firmware's
`P` telemetry or the `V` reply's trailing sensor fields. `pimd_delaycal` has none either.
`pimd_gui` and `pimd_rawlog` do consume them. So the firmware side (the v4.29 calibrated divider,
the v4.33 DS18B20) is real and reporting; the plumbing into the two tools that write capture
metadata simply has not been built yet. Wiring `pack_v`/`board_temp_dC` straight from the wire
into the classviz session header would satisfy §10's "state the window you ran in" automatically
and remove a hand-entered field from the record — worth doing before the next corpus campaign,
and it is a tooling task, not a firmware one.

**What v4.34 actually bought** (identical profile, 62.5 → 76.5 relative-gate events was an artefact
of the moving gate — see the tool v1.01 entry): σ **halved** across the 25 kHz band (×0.50–0.67),
−15…−35 % on the 100 µs band, ch0 equivalent jitter 5.0 → 2.5 ns, and the cell-0 excursion median
132 → 60 mV with the >100 mV rate 43.3 → 32.6 per 1000. A material improvement that did **not**
eliminate the cell-0 population. Sweep 12.49 → 12.07 Hz, against a predicted ~11.8 Hz.
(2026-08-09)

---

### utilities/mode2_noise/mode2_cell_noise.py — v1.01 — absolute-excursion column; the relative gate is not comparable between runs

v1 gated candidate outliers at `4 × robust sigma` of the step series. That finds the anomalous
cell **within** one run, which is what it was built for, but it is actively misleading **between**
runs: the gate moves with each run's own noise, so halving a channel's sigma lets smaller events
start crossing it. On the v4.33 → v4.34 A/B ch0 read **62.5 → 76.5** events per 1000 while sigma
halved, equivalent jitter went 5.0 → 2.5 ns and the median excursion fell 132 → 60 mV — the count
rose because the run got quieter. Reporting that as "the fix made it worse" would have been wrong.

v1.01 adds a second column gated at an **absolute** `ABS_GATE_MV = 100` mV excursion (a single
sample that far out steps an N-deep boxcar by `100/N`, which is what is detected), and keeps the
relative column alongside it. Same-run diagnosis reads the relative column; any A/B reads the
absolute one. The constant carries the reasoning so the trap is not re-entered. (2026-08-09)

---

### mcu/pimd_mcu.py — v4.34 — boundary settling is measured from the config write, not the loop top

`acquire_mode2()` computed its band-boundary settle as
`remaining = period - elapsed - 2` and then `remaining += period * settle_i`, where `elapsed` is
`ticks_diff(ticks_us(), t0)` and `t0` is taken at the **top** of the loop iteration — before
`read_raw_bytes_hold()` and before the freq/CC writes. Every microsecond of `elapsed` was
therefore spent at the **previous** cell's configuration, and it was being deducted from this
cell's settle budget. Delivered settle was `period·settle − (elapsed − period)`, not
`SETTLE_FLOOR_US`. v4.34 captures `t_cfg = ticks_us()` immediately after `enable_irq(_held_irq)`
— the instant cell[i]'s configuration goes live — and sleeps `period·settle` measured from
*there*. Non-boundary cells are untouched, and the v4.26 IRQ-off critical section is not
lengthened (the one new `ticks_us()` call is outside it).

**How far short it fell.** Per-cell interpreter cost is ~2.3–2.4 ms, dominated by the BUSY sync
(DESIGN §7 — the poll loop catches roughly one BUSY-high in six). That is far longer than any
band period above ~400 Hz, so `elapsed` always exceeded `period` and the floor was always
diluted:

| boundary | intended | delivered before v4.34 |
|---|---|---|
| 25 kHz band, 75 periods | 3000 µs | ≈ 600–740 µs |
| 3.125 kHz band, 15 periods | 4800 µs | ≈ 2.7–2.8 ms |

So **`SETTLE_FLOOR_US` was not an absolute floor on any band in any profile in the repository.**
v4.24 was still a real improvement and its bench verification was not wrong — before it the
sleep went *negative* at high-frequency bands and there was no settling at all — but the
mechanism was never delivering the number §8 and §17.7 quote for it.

**What found it.** Hand-tuning `cal_100_10_x15_v1` (2 bands × 15 thresholds, 25 kHz/10 µs and
3.125 kHz/100 µs) showed the first cell of each row with a std dev far above its neighbours —
2.60 mV and 0.89 mV — that would **not move when the delay was nudged all the way down to
2.5 V**. That control rules out timing jitter and decay slope and points at sweep position.
`session_20260809_123634.csv` (3235 frames / 259 s, `profile_sha8 056797db`, 12.49 Hz) was
analysed with the new `utilities/mode2_noise/mode2_cell_noise.py`, which deconvolves the 32-deep
rolling mean to recover single samples. Two distinct signatures, neither delay-dependent:

- **Band 1's first three cells** carry a decaying excess — 10.3 → 11.9 → 6.2 ns equivalent
  timing jitter against the band's own 4.2 ns settled baseline. That is the §17.7 under-settled
  boundary gradient, and it says this profile's boundary transient is still running **~8–10 ms**
  after the switch.
- **Cell 0 alone** carries a discrete single-sample outlier population: **62.5 events per 1000
  sweeps** against 6.8 for the worst other cell in its band, median excursion 132 mV, bimodal at
  ≈ −200 mV and ≈ +120 mV, spread evenly over all 32 residue classes and uniform in time. At one
  event per 8–16 sweeps against a 12.49 Hz sweep this beats at **≈ 0.8–1.5 Hz**, which is the
  "about 1 Hz" wander seen on the bench; each event then holds the displayed mean off for 32
  frames (2.6 s), which is why an 8-frame std-dev window reports it so loudly and why it is
  insensitive to the delay.

**Falsified on the way, recorded so it is not re-checked.** The 1 Hz `SENSOR_SAMPLE_MS`
pack-voltage read is *not* the cause: its exact schedule was reconstructed from the firmware
clock, and those sweeps run +0.34 ms and carry *less* cell-0 movement, not more. DS18B20 fires
16 times in the session. There is no 1 Hz spectral line, and no correlation between excursions
and sweep interval (79.3 ms on event sweeps vs 80.1 ms otherwise). `src/pimd_delaycal.py` has no
defect here — its "Std dev" is the std of 8 consecutive 32-deep rolling means sharing 31/32 of
their samples, so it faithfully amplifies exactly this.

**This fix does not claim to explain cell 0.** The dilution explains band 1's gradient and
explains why cell 0 is fragile, but cell 0 is also the one cell whose settle window contains the
blocking emit `print()`, so it may already be the best-settled cell in the sweep, and a discrete
bimodal population is not what a settling curve looks like. Three candidates remain, in the same
index-locked family as v4.13/v4.20/v4.24/v4.26: residual transient sampled on its varying part;
emit-adjacent interpreter timing (a GC pass at the emit's allocation site, or USB frame
scheduling); or USB TX burst coupling into the front end or the LTC2508 reference — a ~250-byte W
record is four packets and TX activity continues for milliseconds after `print()` returns, through
cell 0's settle and into its conversion. **That last one is an analogue question and cannot be
settled from the code.** `cal_100_10_x15_v1_bandswap.json` is the discriminator: if the population
follows sweep position 0 it is firmware, if it follows the 25 kHz cell it is analogue.

**Cost, and why it is not a silent adoption.** Roughly +2.3 ms per boundary per sweep:
`cal_100_10_x15_v1` 80.1 → ~85 ms (12.5 → 11.8 Hz), and `cal_63_air_bat_v3` with 7 boundaries
~145 → ~161 ms (6.9 → 6.2 Hz) against the 0.1445–0.1455 s §8 records. It also deliberately moves
every band's first-cell operating point. This is an acquisition change of the same class as v4.24
and v4.26: it wants a v4.33/v4.34 A/B under one profile and a delay re-cal of the operating
profile before any corpus capture. `SETTLE_FLOOR_US` and `BOUNDARY_PRIME` keep their values —
make the floor deliver first, then measure whether 3 ms is the right number. Invariants (§11) are
untouched: GPIO4/5 slice-2 phase-locking, the wire format, no scheduler, no flash writes.
(2026-08-09)

---

### utilities/mode2_noise/mode2_cell_noise.py — v1 — recover per-cell single-sample noise from a Mode 2 session

New offline tool. Mode 2 never emits samples — each W record carries a rolling mean `averages`
deep (§9) — so per-cell noise has not been directly measurable from a session dump. But the
firmware adds exactly **one** new sample per cell per sweep, so
`m[i] − m[i−1] = (x[i] − x[i−N]) / N`, which recovers the single-sample series up to one unknown
constant per residue class `i mod N`. Two statistics fall out:

- **Matched-pair outlier detection.** A single bad sample entering the boxcar steps the mean by
  `+d` and, exactly `N` frames later, leaving it steps the mean by `−d`. Requiring both makes the
  test independent of drift, of the per-class constants and of the reconstruction itself — it is
  not something detrending can manufacture. This is the primary statistic and the one the A/B is
  scored on.
- **Equivalent timing jitter.** A cell's σ is meaningless without its own local decay slope: 5 ns
  is 6 mV on a steep cell and 0.4 mV on a flat one. Dividing the recovered σ by dV/dt from the
  neighbouring cells gives nanoseconds, which is flat across a healthy band at the §8 timing
  precision. A cell that stands out in mV but not in ns is behaving normally; one that stands out
  in ns is not. This is what separates "steep slope" from "actually noisy", which is the exact
  confusion that made the bench symptom hard to read.

Robust statistics throughout (`1.4826·MAD`), so an outlier population cannot inflate the estimate
of the population it is being compared against. The tool flags the two signatures by name —
boundary-settling gradient and index-locked outlier population — against each **band's own**
settled baseline rather than a hard-coded expectation, so it travels across bands, pack states and
epochs. Cells below 1 LSB (610 µV) or flatter than 20 mV/µs report `--` rather than a number:
the rail and the ~16.5 mV pedestal (§7) carry no timing information and dividing by their slope
produces four-figure nonsense. It checks the firmware clock for dropped frames, because a drop
breaks the N-frame pairing. `--hist <ch>` adds the excursion-size histogram and the residue-class
control that distinguishes a real discrete mechanism from a reconstruction artefact.

Read-only, pure numpy, no board required. Baseline for the v4.34 A/B:
`python utilities/mode2_noise/mode2_cell_noise.py --hist 0 src/data/sessions/session_20260809_123634.csv`
must report ch0 at 62.5 events/1000 with a 132 mV median and ch1/ch2 at zero. (2026-08-09)

---

### src/data/profiles/cal_100_10_x15_v1_bandswap.json — new — band-order discriminator for the cell-0 outlier population

Diagnostic profile, not a calibration. Byte-identical to `cal_100_10_x15_v1` — same delays,
thresholds and `averages` — with the two bands in the opposite **protocol** order, so
3.125 kHz/100 µs occupies sweep position 0 instead of 25 kHz/10 µs. It answers the one question
the v4.34 analysis could not: whether cell 0's discrete outlier population is locked to the sweep
position (firmware) or to the 25 kHz cell (analogue). This is the same test §17.8 used on the
index-locked σ anomaly, and it needs no code change. `pimd_delaycal` sorts its thermal rows by
`pulse_us` for display and maps back through `_thermal_proto_to_display`, so the table looks
unchanged and only the protocol order moves — the population visibly jumps rows if it is
position-locked. Not to be calibrated against or captured with. (2026-08-09)

---

### References/images — the three `profile8b-*` captures are tracked; the README image was broken on GitHub

`README.md` has always opened with `profile8b-spanner-copper.jpg` as its lead figure, but
`.gitignore` excluded `References/images/profile8b-*`, so the file existed only on the author's
disk and **GitHub rendered a broken image** — the first thing a visitor to the repository saw.
The markdown was never at fault. Rule dropped and all three captures committed.

**The rule was not arbitrary, and the reason it existed still applies to the content.** Its
comment recorded these as *previous-epoch* captures whose DESIGN.md §15 rows were deliberately
dropped at Doc-rev 1.8. Publishing them fixes the README but does not make them current: they
predate the enclosure, the 6S supply and both `cal_63` epochs, so the 8×9 matrix in that figure
is not what the rig produces today. It is being used as an illustration of *what the display
looks like*, which it still serves, rather than as evidence about the present instrument — worth
knowing before anyone cites it as data. The other two (`profile8b-spanner.jpg`,
`profile8b-copper-pipe.jpg`) are committed alongside it so the directory is not half-ignored,
which is the state that produced this bug.

No DESIGN.md change: §15 rows for previous-epoch assets were removed by a deliberate decision at
Doc-rev 1.8 and reinstating them is a consolidation-pass call, not a side effect of fixing an
image link. (2026-08-08)

---
## Archive — consolidated 2026-08-08

### utilities/decay_model/decaymodel.py — v5 — model refitted to the scope; below-rail reconstruction; file halved

**The model is now measured rather than inferred.** v1–v4 fitted air to the calibrated `cal_63`
ladder, which only samples the volt-scale region, then extrapolated past it — the failure already
recorded on 2026-08-07, where fits agreeing with that ladder to ≤ 2 % predicted anywhere from
+64 to −400 mV at sd 14.7 µs. v5 drops the ladder and fits the 2026-08-08 scope capture of the
LT6203 input, which covers the whole decay including the part the ADC cannot see.

Two real poles with opposite-sign residues plus the measured quiescent DC,
`s(t) = A·exp(−t/τf) − B·exp(−t/τs)`:

| | |
|---|---|
| τ_fast | **1.125 µs** |
| τ_slow | **2.270 µs** (ratio 2.02) |
| ζ | **1.06 — mildly overdamped** |
| residual vs the scope | **RMS 0.87 mV**, max 2.70 mV, over 894 points |
| single zero crossing | sd 13.92 µs modelled, ~14.0 µs measured |

**The component values it implies are an independent check, not an input, and they land.** With
R1 = 1.3 k: **C = 579 pF, L = 4.41 mH, √(L/C) = 2762 Ω → R_crit = 1381 Ω**, against DESIGN §7's
*measured* 1300–1400 Ω critical-damping value, and L close to the stale 3.9 mH. Two quantities
measured years apart by different means agreeing to a few per cent is the reason to trust this
fit. It also supersedes the "ζ = 1.00" of 2026-08-07 for the reason given there: that came from
assuming the critically-damped form and fitting τ = 2RC to it, which cannot report anything else.

**Below-rail reconstruction added.** The scope measures the input, where nothing is clipped, so
multiplying by the input→ADC gain (1.149, from the two quiescent levels) gives what the ADC
*would* have recorded with no output floor. Air really reaches **−16.9 mV in ADC terms** — against
a recorded 2.441 mV — and is below the rail for **4.21 µs, sd 14.23–18.44**. The figure draws that
explicitly, shaded, so the difference between what the instrument records and what the front end
does is visible rather than argued.

The chart is rebuilt around that: full span in ADC terms with the reconstruction and the three
measured classes; the null with the hidden region shaded; and a residual panel, which shows the
one place the model is imperfect — it runs a mean **−0.59 mV** below the measured tail over sd
25–98 µs, i.e. the slow pole is slightly too fast. Left as-is and reported rather than patched
with a third term.

**Comments cut roughly in half** at the same time: **1023 → 489 lines**, 35 comment lines. The
removed material was historical justification that has since been settled and is recorded here —
why the anchors went, why the plateau path exists, what each earlier version got wrong. What is
kept is the load-bearing kind: why the probe column is chosen from the data, why roles come from
`material_class`, why smoothing trims its ends. Three fixes fell out of the rebuild, all
artefacts of my own plotting rather than the data: the MCLK ring was not masked in the wide
capture, `np.convolve(mode="same")` tapered the trace ends toward zero and invented a step, and
smoothing spanned the masked ring gap. Verified across model-only, bracketed-session and
plateau-fallback runs. (2026-08-08)

---

### findings — a ferrous target fills the null in completely, and railed cells under-report target deltas

Follow-up to the entry below, same scope session and settings (DHO1204, CH1 = LT6203 input,
CH2 = MCLK, sd 15.5 µs, 2 kHz / 100 µs). Adjustable spanner 250 (steel, 271 g) resting **on** the
coil; 83 CH1 traces averaged over 169 s, trace-to-trace scatter 0.60 mV. Figure and CSV in
`References/scope/spanner_fills_the_null_20260808.png` / `spanner_vs_air_20260808.csv`.

**The lobe carries target signal, so it is coil physics — the question is now closed from both
ends.** The entry below showed the lobe exists *before* the amplifier; this shows it *responds to
metal*. No-spanner air swings negative from sd 14.3 to 17.8 µs and bottoms at **−15.0 mV**; with
the spanner on the coil the trace **never crosses zero at all**, with a minimum of **+15.5 mV**.
The difference peaks at **+48 mV around sd 13.6 µs** and is still +16 mV at sd 22. An instrument
artefact — amplifier recovery, clock feedthrough, anything downstream of the coil — cannot do
that.

**New, and it bites the corpus: where air is railed, the ADC under-reports the target delta.**
Comparing the true delta at the amplifier input against what the sweep recorded through the same
window:

| sd (µs) | air (ADC) | Δ recorded by the ADC | Δ at the amplifier input |
|---:|---:|---:|---:|
| 14.86 | 9.12 mV | +40.7 mV | ~+43 mV |
| 15.46 | 2.44 (railed) | +24.0 | ~+33 |
| 16.06 | 2.44 (railed) | +12.6 | ~+27 |
| 17.26 | 3.66 | **+6.3** | **~+22** |
| 21.61 | 5.19 | +19.6 | ~+16 |

The mechanism is simple and one-directional: Δ = target − air, and when the air baseline is
clipped up to the 2.44 mV floor the subtrahend is too large, so **the delta is always
under-stated, by up to ~3.5×**. Previous entries called these cells "worthless as a calibration
point" and "not dead cells, just cells where every millivolt is target". Both understate it —
those cells actively **compress** measured target amplitude, and anything derived from them
(band means, crossing widths, any amplitude feature) inherits a non-linear, target-strength-
dependent bias. This is a reason to exclude railed cells from feature maths, not merely to avoid
calibrating on them.

**A corollary that softens the operating note:** the rail is an *air* problem. A strong ferrous
target lifts the whole trace clear of it, so the same cell that is dead in air is perfectly live
on a close target — which is exactly what the 2026-08-03 close-target run saw from the other side.
The right test for whether a cell is usable is therefore whether **air** is railed there, not
whether the cell ever reads low.

**Two corrections to my own working, both caught in the analysis and both mine.** (1) The polling
script computed the time axis without `xorig`, mislabelling the spanner traces by +3 µs; the
pairing was correct but the first comparison table I produced was labelled wrong and was
discarded. (2) I first quoted the air bottom as −19.8 mV using a ±90 ns mask around the MCLK
edge. The edge ring is **asymmetric** — sharp before the edge, ~250 ns of tail after it — so
±90 ns still included ringing. With a ±250 ns mask the bottom is **−15.0 mV** (−13.7 smoothed
across the gap), which is what the operator read off the screen directly. The masking width is
now recorded on the figure.

**Paired reference captured, and the earlier caveat is now closed with a number.** The first
comparison used a no-spanner trace from ~30 minutes earlier, because the spanner was already in
place when the watch began. The spanner was then lifted and 83 air traces taken in the same run,
minutes after the spanner set, at identical settings. **The paired air agrees with the earlier
reference to RMS 1.5 mV, max 3.6 mV** across the whole window — against a target effect of up to
49 mV, so the unpaired conclusion was safe by better than 13×. Paired numbers, which supersede
the earlier ones only in precision: air bottoms **−14.75 mV at sd 15.79 µs** with zero crossings
at **14.29 and 18.00 µs**; spanner bottoms **+15.45 mV** with **no zero crossing**; largest
difference **+48.9 mV at sd 13.57 µs**. Run-to-run scatter 0.31 mV (air) and 0.60 mV (spanner),
so every number above is far outside the noise. Both states are in
`spanner_vs_air_20260808.csv` along with the earlier reference.

Still open, and now the obvious next probe: whether the MCLK-edge ring exists in the circuit as
well as between scope channels. If it does, the ADC samples on that edge and captures the kick.
(2026-08-08)

---

### findings — SETTLED by scope: the negative lobe is at the amplifier INPUT, and so is the pedestal

Rigol DHO1204 over LAN (192.168.2.161, raw SCPI on 5555), `pimd_gui` Mode 1, 2 kHz / 100 µs,
sample delay 15.5 µs. **CH1 = LT6203 input (post-R8); CH2 = MCLK, whose rising edge is the ADC
sample instant** — so scope t = 0 is sd 15.5 µs and the whole trace reads directly in sample
delay. Scope state was saved before and restored after; timebase and CH1 range were changed for
the wide captures and put back. Traces kept in `References/scope/`.

**This closes the question open since 2026-08-05: it is the front end, not the amplifier.** The
negative excursion is present *before* the LT6203, so it cannot be output overload recovery. At
the input it spans **sd 14.3 → 17.8 µs** (zero crossings, ~3.5 µs wide) and bottoms at
**≈ −15 mV**. Both entries below that leaned on "amplifier recovery" as the likely explanation —
including the one that argued the coil poles had no room for it — are wrong on that point.

**The −31.4 mV apparent minimum is not signal, and the operator called it before the analysis
did.** It is a **70 ns FWHM** spike sitting exactly on CH2's ~10 ns MCLK edge — three orders of
magnitude faster than the 3.5 µs feature it sits inside — i.e. crosstalk from the adjacent
channel, not circuit behaviour. Masking ±90 ns around the edge leaves a smooth lobe bottoming at
−14 to −15 mV. Worth keeping in mind for any future scope work at this node: the trigger channel
carries a fast logic edge and the interesting signal is tens of mV.

**The ~16.5 mV pedestal is also a front-end DC level.** The input's quiescent value out past
sd 60 µs is **+14.34 mV**, against the ADC's 16.472 mV pedestal — the offset exists *before* the
amplifier. That retires the 2026-08-05 entry's alternatives: it is not amplifier Vos and not ADC
offset. It is consistent with that entry's preferred mechanism (input bias current through the
front-end resistance), which was explicitly flagged there as "inferred from the datasheet and the
measured level — not measured". It is measured now, at the node. The pedestal-to-quiescent ratio
is 1.15, so the path is near unity gain — but that is two anchor points from captures ~2 h and
one pack-state apart, so treat it as an order check, not a calibration.

**Why the output rails.** The input swings ~29 mV below its own quiescent level. At near-unity
gain that puts the output well under the LT6203's ~2.44 mV output floor, which is exactly the
railed value the sweep measures over sd 15.46–16.66 µs. The rail width does not match the input
excursion cell-for-cell, which is expected: the ADC sweep is the raw path two hours earlier at a
different pack voltage, and the sweep samples the region at only three delays.

**What this implies about damping, and a correction to the 2026-08-07 arithmetic.** A ~3.5 µs
lobe at the input fits a slow real pole of ~2–3 µs alongside the fast decay — which is what
L/R1 gives (3.9 mH / 1.3 k ≈ 3 µs), i.e. the **two-real-poles-with-opposite-sign-residues** shape
the 2026-08-05 entry proposed. The 2026-08-07 entry's "ζ = 1.00" came from *assuming* the
critically-damped form and fitting τ = 2RC to it; with L = 3.9 mH and C = 354 pF the network is
slightly **overdamped** (α = 1.09×10⁶, ω₀ = 8.51×10⁵, ζ ≈ 1.28, poles at τ ≈ 0.57 and 2.44 µs),
and the 2.44 µs pole is the right scale for the observed lobe. That conclusion still rests on the
stale 3.9 mH, so §7's "re-measure RX self-resonance to pin L and C" is now the gating measurement
for the whole front-end model rather than a loose end. **What survives from 2026-08-07 unchanged:
the undershoot is not fixed by changing R1, and damping remains the wrong knob** — the lobe is
the network's own slow pole, not a ringing artefact.

Open and now cheap to answer, since the rig is instrumented: whether the lobe carries target
information at the input (present a target and watch this node), and whether the MCLK-edge
crosstalk exists in the circuit as well as between scope channels — if it does, the ADC samples
on that edge and would capture the kick. (2026-08-08)

---

### findings — first dense sweep: the lobe resolved, the polarity split located, and the ladder is ~0.4 µs off for this pack state

`rawlog_20260808_145702.txt`, 100 µs / 2 kHz, 68 cells, fw 4.33, 711 frames, pack **24.13 → 24.04 V**.
First capture with the bracketed logger (`pimd_rawlog` v1.16) and the dense sweep: air / copper
pipe / air / steel spanner / air, 20 frames each, all `complete=yes`, **targets at 0 mm** (resting
on the coil). Every segment read from its own brackets — no inference.

**Air, resolved.** Clamped through sd 7.168 µs; 4950.9 mV at 7.568; **44.4 mV at 14.264 → 9.1 at
14.864**; bottoms at **2.437–2.441 mV across sd 15.46–16.66 µs**; 3.66 at 17.26; 5.19 at 21.6;
10.18 at 23.6; 15.27 at 30.8; settles at **16.472 mV** from ~37 µs and holds to 311.7 µs.

Three numbers that were previously estimates are now measurements:

- **The air pedestal crossing is at sd ≈ 14.64 µs** (log-interpolated between the two bracketing
  cells), against the session's own settled level of 16.472 mV rather than the §14 constant.
- **The rail flat is ≥ 1.2 µs wide** — three consecutive cells at 2.437/2.441/2.441 mV with σ
  exactly 0. The 2026-08-05 hand-read estimate off a live trace was 0.5–1 µs; it is wider than
  that. Note 17.264 and 19.760 µs also have σ = 0 but sit at 3.662 and 4.272 mV — 6 and 7 LSB of
  the 610.35 µV raw quantum, so those are quantisation-locked, not saturated.
- **Air does not reach the pedestal until ~37 µs**, far later than the ~21 µs the v1 model implied.

**The polarity split is located, and it is a window, not a column.** Steel and copper carry
opposite signs across **sd 7.968–12.304 µs**, widest at **9.568 µs: steel +46.5 mV, copper
−74.4 mV**. Past that the copper delta itself **crosses zero at sd ≈ 12.425 µs** and both targets
read positive thereafter. That crossing is a per-material coordinate the 2026-08-07 capture could
not see at all — it had two usable pre-rail cells and this has 26.

**Copper overtakes steel at ~44 µs** and stays ahead: at sd 311.7 µs copper is **+1.375 mV** over
air against steel's **+0.036 mV**, on a 0.08 mV air σ. Same ordering as 2026-08-07 (crossover
~77 µs there, at 60 mm) — the crossover moves with coupling, which is worth a controlled distance
series rather than an inference from two points.

**Actionable: the ladder is positioned ~0.4 µs early for this pack state.** The crossing region
was placed against the 2026-08-07 measured rail of 14.712 µs, but at 24.13 V the rail sits at
15.46–16.66 µs and the crossing at 14.64 µs — so the fine 0.16 µs cells end at 14.224 and the
crossing falls in the **0.600 µs gap** to the first rail-region cell. It was still bracketed to
0.6 µs, which is why the number exists at all, but the region should follow the pack. The
2026-08-07 session ran at **22.04 V**; ~2 V of pack moved the features ~1–2 µs later, which is
larger than the crossing region is wide. `MEASURED_RAIL_US` in the generator is therefore a
pack-state-specific constant, not a band constant, and should be re-derived per epoch — or the
region widened to cover the range. **Not changed here**; it needs a deliberate decision about
which pack state the profile is centred on.

Also note the capture used a superseded 68-cell ladder (the live file is now 66) and its `META`
name field reads `late / target` from the v2 shadowing bug, so the log cannot identify its own
ladder. Reconstructed and verified as `sweep_100us_asbuilt_20260808.json` — 68 cells, clamped and
railed cells landing exactly where the regions predict — so the capture stays analysable.
(2026-08-08)

---

### utilities/decay_model/decaymodel.py — v4 — roles from `material_class`, probe column chosen from the data, figure text de-hard-coded

Running v3 against the first dense capture surfaced four defects, three of which produced wrong
output rather than an error.

1. **Ferrous/non-ferrous roles were assigned by insertion order.** This session presented copper
   first, so copper was painted with the ferrous colour and the crossover search looked for a sign
   change in the wrong direction and returned `nan`. Roles now come from the log's own
   `material_class` field, which `pimd_rawlog` already writes into every target marker. A target
   with no `material_class` is reported and treated as non-ferrous for colouring only.
2. **The probe column for the plateau fallback was hard-coded to index 3.** That is a good
   post-rail cell in `cal_110`'s 150 µs band and a **clamped** cell in the 100 µs sweep — constant,
   no excursion to find, so the whole session became one active run and there were no air frames
   left, crashing. The column is now chosen from the data as the best excursion-to-MAD ratio among
   unclamped, non-constant columns.
3. **Figure text was hard-coded to the first dataset** — "targets at 60 mm", "2026-08-07 session",
   and a fixed rail value. All now derived from the session: distance and material from the MARK
   fields, date from the first frame, rail and crossing from the data.
4. **`order[2]` assumed exactly two target classes**, crashing on a single-target session.

Also adds the air pedestal crossing to the printout — the coordinate the dense ladder exists to
measure — computed against the session's own settled level rather than `PEDESTAL_MV`, since that
constant is a 2026-08-03/05 figure and this session settles at 16.472 mV. The polarity-split
search judges significance against the **settled-region** noise, not air's per-frame σ at the
cell: on the steep pre-rail slope that σ is slope × timing jitter (26 mV here, §14.3) and a
3σ gate on it rejects a genuine +46 / −74 mV split. Verified against four inputs — the real
bracketed session, a plateau fixture (end markers stripped), a single-target fixture, and
model-only. (2026-08-08)

---

### utilities/decay_model/make_sweep_profile.py — v3 — cal_110 anchors dropped, crossing region tightened, junctions guarded; both profiles regenerated

**The anchors are gone, and the rule that put them there was wrong.** v1/v2 forced the eleven
`cal_110_full_range_v4` delays of the matching band into the ladder so captures would stay
"directly comparable" to `rawlog_20260807_194234.txt`. Measured, that bought nothing. Sampling the
2026-08-07 air curve onto the anchor-free ladder and interpolating back to the anchor delays
recovers them to **≤ 0.05 mV past sd 20 µs** and **0.000 mV from 62 µs out**, against target
deltas of 0.09–7.1 mV. The one large residual, **+2.7 mV at sd 10.912 µs**, sits on the steep
slope where that cell's own frame-to-frame σ is **7.8 mV** — the interpolation error is inside the
cell's own noise. The railed cell cannot be interpolated meaningfully and carries no information
anyway.

Against that, the anchors cost **10 cells at 150 µs and 11 at 100 µs, ~15 % of the ladder**, and
crowded it: `15.448 → 15.600 µs` was a 0.152 µs gap inside a region whose step is 0.600 µs, so one
of that pair was wasted. They also coupled this profile to another profile — the coupling that
broke silently when the 150 µs file was hand-retargeted to 100 µs and kept the wrong band's
anchors (0 of 11 correct). **And the comparability claim was overstated when written:** that
session ran 110 cells at 4.07 Hz with a 7.9 s rolling window against this profile's 7.6 Hz and
4.2 s, on a different pack state and soak, and DESIGN §10's `(profile_name, profile_sha8)` guard
exists precisely because cross-profile comparison is not automatically valid.

**The freed cells went into the crossing region**, which is the one that decides the crossing
time — the pack-independent coordinate. It goes from **11 cells at 0.240 µs to 17 at 0.160 µs**
(1.5× finer) and now runs up to the rail region instead of stopping at 14.810 µs and leaving the
plunge to be covered at 0.600 µs. Net 66 cells (was 72), ~132 ms, ~7.6 Hz, 4.2 s rolling window.

**`MIN_GAP_FRAC` guards region junctions.** Region boundaries do not land on each other's grids,
and the first build after dropping the anchors put the crossing region's last cell 0.040 µs before
the rail region's first — 4× tighter than the finer of the two steps, i.e. exactly the defect the
anchors used to cause. A cell is now dropped if it sits closer than 0.75 × the finer local step to
its neighbour. The region boundaries were then aligned so every junction gap equals the finer
step, and the guard stops firing — it is a safety net, not a workaround, and it is checked by the
per-region cell counts in the printout.

**One bug found by the validation pass, worth recording because it is the same defect this work
flagged in a hand-edited file.** v2 parameterised the profile name, and the per-region reporting
loop then shadowed `name`, so both regenerated JSONs were written with
`"name": "late / target"` — the last region's label. `pimd_rawlog` copies that field into every
session's `META … name=` line, so every capture would have been mislabelled. Fixed (loop variable
renamed) and now **asserted in the generator** before the file is written, so it cannot regress
silently.

Both profiles regenerated and validated end to end: 66 cells each, correct `name`, no off-grid
delays, gaps 0.160–41.936 µs, every cell passing the firmware's own `compute_pulse_duties` /
`pulse_duties_valid`, `D` line 471/473 chars round-tripping losslessly through the MCU parser, no
`threshold_v`, and worst-case `pulse+delay+0.904` of 412.6 µs (100 µs) and 463.4 µs (150 µs)
against the 500 µs period. (2026-08-08)

---

### utilities/decay_model/make_sweep_profile.py — v2 — `--pulse` / `--freq`; regions positioned against the band's measured rail

The v1 generator hard-coded 150 µs: the pulse width, the output name, and the eleven
`cal_110_full_range_v4` anchors. Retargeting it to another band by hand-editing the JSON — which
is what happened to `sweep_150us_decay_v1.json`, now on disk as `sweep_100us_decay_v1.json` with
`pulse_us` changed to 100.0 — leaves three things wrong that the file itself cannot show you:

1. **The internal `name` still reads `sweep_150us_decay_v1`.** `pimd_rawlog` writes that field
   into every session's `META profile=… name=…` line, so every capture would be stamped with the
   wrong band.
2. **The ladder is still positioned for the 150 µs band.** The measured air minimum is at
   sd 14.712 µs at 100 µs drive against 15.448 µs at 150 µs, so the fine steps land ~0.74 µs late
   — the crossing region's 0.24 µs resolution is spent just past where the crossing is.
3. **The anchors are the wrong band's.** `0 of 11` of cal_110's 100 µs delays appear in the
   hand-edited file, so it is no longer a superset and captures are not directly comparable to
   the 100 µs band data already measured.

v2 takes `--pulse` and `--freq`, derives the output name and path from the pulse width, pulls the
anchors from the matching `cal_110_full_range_v4` band, and shifts all six regions rigidly by the
difference between that band's measured rail position and the 150 µs reference
(`MEASURED_RAIL_US`, from the 2026-08-07 session). It **refuses** to generate for a pulse width
with no measured rail rather than guessing an offset — the regions are positioned against a
measured feature, and inventing one would be the same error as cal_110's threshold labels.
Regenerating at 100 µs gives 72 valid cells, all 11 anchors present, drive duty 13107 fixed, last
cell sd 311.736 µs → `pulse+delay+0.904` = 412.6 µs of 500. `--pulse 150` still reproduces v1's
output exactly (shift 0.000). (2026-08-08)

---

### utilities/decay_model/decaymodel.py — v3 — `--session` prefers the log's acquire/end brackets; plateau detection becomes the fallback

Completes the loop opened by `pimd_rawlog` v1.16. `load_session()` now has two segmentation
modes and picks by what the log contains, so a recorded extent is never quietly replaced by an
inferred one:

- **bracketed** — taken whenever the log has any `MARK acquire end` line. Each acquisition is
  read verbatim between its own start and end markers, repeated segments of one label are
  concatenated (two air captures either side of a target become one air set), and nothing is
  inferred at all.
- **plateau** — the v2 behaviour, kept unchanged for pre-v1.16 logs, which have no end markers
  and where the extent genuinely has to be recovered from the probe cell.

The mode is returned, printed in the header, and stated on the figure, so the two can never
disagree silently — a log either has brackets or it does not.

**The bracketed path checks the log against itself rather than trusting it.** The end marker
states `frames=`; the reader counts the frames actually inside the bracket and warns on any
mismatch, because silently believing either number would be the same class of mistake the
brackets exist to remove. It also warns on `complete=no` (keeping the data, labelled short, with
the reason), on an end marker naming a different target than its start, on end markers with no
start, and on a start left open at EOF — which is **skipped**, not guessed at.

Frame selection is `start < t <= end`: the start marker is written before any frame is counted
and the end marker just after the last one, so that half-open form recovers exactly the captured
set. Verified by re-marking the 2026-08-07 session at the plateau boundaries and running both
paths over it — **the bracketed reader reproduces the plateau means exactly** (61 and 70 frames,
`allclose` on all 11 cells), which is the check that says the new path is right rather than
merely different. The integrity warnings were each provoked deliberately and confirmed to fire,
and the unclosed-start case confirmed to skip the segment rather than include a partial one.

Also adds `--profile` (default `cal_110_full_range_v4`) so a session streamed with
`sweep_150us_decay_v1` can be read with the right channel layout — v2 had the profile name
hard-coded, which would have mis-sliced the channel vector for any other profile. No change to
the model, the fit, or the figure's construction. (2026-08-08)

---

### src/pimd_rawlog.py — v1.16 — FIX the grid could force the window off-screen; acquisitions become fixed-length and bracket themselves

Two changes, both surfaced by loading `sweep_150us_decay_v1` (72 delays on one band).

**1. FIX: the last-frame grid set the window's minimum width, and it could not be dragged back.**
`lbl_grid` was a `QLabel`, and a QLabel reports its full text extent as its size hint — a layout
cannot shrink below that. One band of 72 delays is ~720 monospace characters, several times a
3440 px screen, and with the window origin saved at x=1957 most of it was off the right-hand
edge. Measured after the fix: **window minimum width 778 px**, and identical for
`cal_110_full_range_v4` (10 bands × 11) — the width is now independent of the profile.

The numbers moved to a read-only, **non-wrapping** `QPlainTextEdit`, which has a small minimum
width whatever it contains and scrolls horizontally instead; the prose header stayed a QLabel and
now word-wraps. This is the third attempt at this bug and the first that addresses the mechanism:
v1.11 turned on word-wrap (a comma-separated numeric row has no break points), v1.12 truncated the
text (bounds the width by discarding the data you opened the pane to read). Height is set from the
band count and clamped at `GRID_MAX_ROWS = 12`, so the pane is 38 px for a single-band sweep and
164 px for cal_110 rather than claiming a text editor's default. Horizontal scroll position is
preserved across frames — the pane repaints several times a second and resetting it would make a
scrolled-to column impossible to watch. Values are now selectable, which is a free side effect
worth having at the bench.

**2. "Settle window (frames)" becomes "Capture frames", and an acquisition ends itself.** Pressing
Acquire Target/Air now starts a capture of exactly that many streamed frames and writes
`MARK acquire end mode=… [target_id=…] frames=N requested=M complete=yes|no reason=…`
automatically when the count is reached. The operator's model is the one that changed: the settle
figure tells you when it is steady enough to press, and the press then takes a defined number of
samples to average offline — rather than opening a segment of indefinite extent.

**This closes a defect in the record, not just an inconvenience.** A `MARK acquire` recorded the
state *from that point on* with nothing to close it, so the log said when a segment began and
never when it ended, leaving every analysis pass to infer the extent — and inferring wrong is not
a small error. In `rawlog_20260807_194234` the second Fe marker landed ~9 s after the spanner was
already away; segmenting on the markers as written mixes ~30 s of air into the target window and
reports Δ at sd 21.88 µs as **+3.5 mV**, sign-flipping depending on which air segment is used,
against **+7.12 mV** from the actual plateau. Bracketed segments remove that class of mistake from
the log itself.

Details that matter: `frames`/`requested`/`complete` record what was *actually* captured, so a run
cut short by a second press, a Stop or a window close is labelled short rather than silently
truncated (`reason=superseded|stopped|session-closed`). The start marker is written **after** the
previous segment's end, inside `_begin_acquisition`, not by the callers before it — writing it
first emits the new segment's start ahead of the old one's end and the log stops reading as
brackets, which is the whole point; verified by walking a synthetic log and asserting the nesting
depth stays in {0,1} and returns to 0. `_scan_session_file` treats `acquire end` as closing, so a
resume does not re-arm a finished segment; **logs written before v1.16 have no end markers and
still resume exactly as they did**, since "last acquire marker, open to EOF" is what they meant at
the time. A resumed open segment is re-armed for a fresh full count, because the frames it already
captured are in the previous file.

**The settle indicator is now decoupled from the spinbox** (`SETTLE_WINDOW_FRAMES = 20`, fixed).
They answer different questions, and tying them was actively broken once the capture range went to
2000: a 500-frame capture gave a settle figure that needed ~5 minutes at 6.9 Hz to fill before it
read anything. The settings key is now `capture_frames`, falling back to the old `settle_window`
so an existing `rawlog_settings.json` keeps its value. Verified headless (offscreen Qt) across
completion, supersede, stop, resume, and pre-v1.16 back-compat. No firmware or wire-protocol
change — DESIGN §9/§11 untouched. (2026-08-08)

---

### profile — sweep_150us_decay_v1.json — single-band 150 µs ladder built to model the decay, not to detect

New profile in `src/data/profiles/`, plus the generator that produced it
(`utilities/decay_model/make_sweep_profile.py` v1 — the ladder's rationale lives in code, so it
can be re-derived rather than re-guessed). **One band, 2 kHz / 150 µs, 72 delays, averages 32** (66 as of v3 — anchors dropped, crossing region tightened).
Not a calibration and not a detection profile.

**The problem it solves.** `cal_110_full_range_v4`'s 150 µs band places exactly **two** columns
between clip release and the rail — 7.904 and 10.912 µs. Everything else on that band is clamped,
railed, or pedestal. Two points cannot constrain a decay, and the 2026-08-05/08-07 analyses failed
for exactly that reason: fitting the four calibrated cal_63 columns with τ_s pinned at different
values produced fits agreeing with the data to ≤ 2 % that predicted anywhere from **+64 mV to
−400 mV** at sd 14.7 µs. The fix is samples, not a better model. This ladder puts **26 cells in
7.9–15.4 µs** where cal_110 has 2.

**Six regions, each sized to the feature it has to resolve** — deliberately not one geometric
rule, since a single geometric ladder is what under-sampled 8–15 µs in the first place:

| region | cells | span | what it is for |
|---|---:|---|---|
| clamp exit | 6 | 7.040–7.840 µs | clip release on this band is currently **unmeasured** — cal_110 has no cell here at all, and the figure in use is the 100 µs band's 7.392 µs plus an extrapolated shift |
| decay / τ | 12 | 7.904–12.304 µs | 0.4 µs steps ≈ 0.43 τ, ~5 e-folds across the region — enough to pin τ and to separate `(a+bt)·exp` from one exponential from two |
| crossing | 11 | 12.400–14.800 µs | the pedestal crossing, never sampled (892 mV at 10.912, railed by 15.448). Crossing *time* is the pack-independent coordinate, so this is the highest-value region |
| rail width | 9 | 15.000–19.800 µs | the lobe's depth is unmeasurable through a unipolar path, but the **width of the flat bounds it** — the 2026-08-05 observation was hand-read off a live trace and has never been measured |
| recovery | 10 | 20.496–44.520 µs | τ ≈ 4.2 µs currently rests on **two** points; ten decide whether it is one exponential or several — one mechanism or more than one |
| late / target | 14 | 48.000–312.472 µs | pedestal sag and the discrimination window, where copper overtakes steel near 77 µs. **Extended past cal_110's 250 µs stop** — the rep rate allows ~349 µs and copper was still +0.40 mV at 250 |

**~~It is a strict superset of the band it replaces.~~ SUPERSEDED 2026-08-08** — the anchors were
dropped in `make_sweep_profile.py` v3 and this profile regenerated without them. Measured, they
were worth ≤ 0.05 mV past sd 20 µs while costing ~15 % of the ladder; see that entry. The
comparability claim was also overstated: sweep rate, rolling-window duration, pack state and soak
all differ from that session regardless of delay alignment.

**Why 72 cells is affordable on one band when 110 across ten bands cost 246 ms.** The firmware's
`needs_settling` is `at_boundary or dd != cells[prev][2]` — with one frequency and one pulse width
the drive duty is identical for every cell (19660) including the wrap-around, so
`BOUNDARY_PRIME`/`SETTLE_FLOOR_US` never fire. There is no per-pulse energy step for settling to
absorb; only the sample compare value moves. Estimated sweep ~144 ms (~6.9 Hz) at cal_110's
measured 2.24 ms/cell, giving a ~4.6 s rolling window at averages 32 — **shorter** than cal_110's
7.9 s, so less drift inside the average, not more. **Estimate, not measured — confirm on the
bench.**

**Validated offline against the firmware's own arithmetic.** `compute_pulse_duties` and
`pulse_duties_valid` are reproduced verbatim in the generator: all 72 cells pass, all land on the
8 ns grid, and the `%.3f` µs wire format round-trips losslessly through the MCU's own `D` parser.
The `D` line is 517 chars against cal_110's ~780, which already works. Worst-case cell is
sd 312.472 µs → sample duty 60734/65535, `pulse + delay + 0.904` = 463.4 µs of the 500 µs period.

**No `threshold_v`, deliberately.** The field is vestigial for streaming (`pimd_rawlog` never
reads it, `pimd_classviz` guards on its absence). cal_110's copy was carried over unverified and
is wrong by a large factor — its "0.5 V" column at 62 µs sits on the pedestal, because 0.5 V is
reached near 11.5 µs. Inventing a fresh ladder here would repeat that error. **Consequence:
`pimd_delaycal` will refuse to import this profile** ("Profile has no threshold_v field"), which
is correct — it is a characterisation sweep, not a calibration. (2026-08-08)

---

### src/pimd_rawlog.py — v1.15 — pack volts, board temperature, firmware version and firmware alerts on screen

Reported from the bench: the raw logger shows no pack voltage or board temperature. Verified
first against a real 2 m 45 s session (`rawlog_20260807_190829.txt`) that the data was being
*captured* correctly — two `P` records, 60.084 s apart against the firmware's
`SENSOR_REPORT_MS = 60_000`, carrying 22.138 V / 51.3 °C and 22.126 V / 50.0 °C, both real
readings rather than the `TEMP_INVALID_DC` sentinel. So this was never a logging or firmware
fault: the tool wrote every line faithfully and simply never looked at any of them. Its parser
branched on `W` and `D OK` only, and there was no `P` branch anywhere in the file.

Adds a sensor row under the port field, at information parity with `pimd_gui.py`'s gauges: pack
volts with SoC % and zone caption, board temperature, firmware version (board ID on the tooltip),
and an alert line for `PACK:` / `LOCKOUT` / `Command Input ERROR`. Rendered as **text, not
painted gauges** — this tool is deliberately dumb, and a number you can read off and paste into a
Note beats a bar you have to eyeball. The SoC/zone maths is duplicated from `pimd_gui.py` rather
than imported, keeping each PC app standalone exactly as `_build_d_command()` already is; a
parity test over 19–26 V confirms the two agree to the percent and the caption. Only the zone
*colours* differ, and deliberately: the GUI's are pale fills sitting behind dark text, which are
illegible as text colours, so the clean-window and transition entries are darkened.

`V` is sent **once, on connect**, to prime the row rather than leave it blank for up to a minute
until the first unsolicited `P`. It is deliberately not polled on a timer: the whole value of this
tool is that the logged stream is what the firmware sent unbidden, so nothing is injected once
streaming is running. Pack and temperature then refresh from `P` every ~60 s, and a lockout
announces itself on the wire. Sensors are cleared on disconnect so a stale reading cannot outlive
the connection that produced it. **The log file format is unchanged** — parsing feeds the display
only, and every line is still written verbatim, sentinel and all, which is what an offline pass
should be reading.

Two traps taken directly from `pimd_gui.py` v4.17's scars. The `P` branch is guarded with
`raw[1:2].isdigit()`, because a bare `startswith('P')` also matches `PACK:` messages and the
`Pulse Induction Metal Detector v…` boot banner. And the lockout latch is matched narrowly
(`LOCKOUT:` or the literal `lockout latched`) rather than by a substring test for `lockout`,
which would have caught `PACK: present again at … mV — lockout cleared …` and latched the state
that line exists to retire — an inversion caught during review, before it reached the bench.
That message now explicitly *clears* the latch.

Tested headlessly by feeding lines through the real `read_from_serial()` dispatch with a stubbed
port: the session's own two `P` records render correctly; the boot banner and all `PACK:`
variants leave the pack reading untouched and raise no parse error; the `-32768` sentinel blanks
the field while a genuine −55 °C still displays; `V` primes all fields and 8-field pre-v4.28
firmware leaves them blank; a plain rejected config alerts without latching while `LOCKOUT:` and
a latch-naming `ERROR` both latch; the `W` grid path is unaffected. Replaying all 671 `RAW` lines
of the real session leaves the last record's 22.13 V / 50.0 °C on screen with zero parse errors.
(2026-08-07)

---

### src/pimd_gui.py — v4.17 — FIX the `P` record parse also matched `PACK:` messages, so the GUI has never shown a failsafe transition

Reported from the bench: `Sensor packet parsing error: list index out of range`, appearing once
per pack power-cycle. The trigger was diagnostic — power-cycling the pack is exactly what makes
the firmware emit a `PACK:` line.

`process_packet()` dispatched on `line.startswith('P')`, which is true of the `P<time_ms>,…`
telemetry record *and* of every firmware message beginning with P: `PACK: rail absent (… mV) —
USB power assumed, failsafe suspended…`, `PACK: present again at … — failsafe armed`, and the
`Pulse Induction Metal Detector v…` boot banner. Each was split on commas, indexed, and threw.
Now guarded with `line[1:2].isdigit()` — a record always carries `<time_ms>` immediately after
its tag, a message never does. Pre-existing since v4.28 and unrelated to the DS18B20 work; it
surfaced now only because v4.31/v4.32 gave the firmware more to say about the pack.

**The parse error was the smaller half.** Those `PACK:` lines were being *consumed* by the P
branch, so fixing the crash alone would have made them vanish silently — and v4.32 exists
specifically so that an ARMED failsafe is distinguishable from a SUSPENDED one, which is the
state you most need to be sure you are not in. They now reach the alert row. Deliberately
**non-sticky**: each line reports a transition that has already completed, and the standing state
is carried by the pack gauge. A latched `LOCKOUT` is a different kind of thing — a standing
condition — and keeps its own sticky branch, unchanged, along with stopping the run.

`DS18B20:` messages are deliberately left falling through: unlike pack arming, that state already
has a GUI indicator, since the gauge blanks to `—` the moment a reading goes invalid.

Checked against the real firmware strings copied from the v4.33 boot log: both record forms still
parse, all three `PACK:` variants alert without error, the boot banner is ignored, `PACK:` alerts
are non-sticky, and `LOCKOUT` still latches sticky and stops the run. The v4.16 sentinel tests
still pass. (2026-08-07)

---

### mcu/pimd_mcu.py — v4.33 — DS18B20 board temperature on GP6; the GP27 pot placeholder retired

`board_temp_dC` has been on the wire since v4.28 and has never once carried a temperature. GP27
sat on bench pot RV7 scaled by `THERM_TEMP_FULLSCALE_DECIC`, so the field reported a pot position
dressed as degrees — a number the file header, the DESIGN text and the GUI tooltip all warned
about and which the gauge displayed anyway. The planned fix was an analogue NTC on GP27; that is
superseded. A **DS18B20 is wired to GP6**, a pin previously reserved for a panel meter that is not
being fitted. The part is digital and factory-calibrated to ±0.5 °C, so the Beta/Steinhart-Hart
curve the analogue path would have needed — the reason the placeholder constant said it must be
"replaced with the proper curve, not just re-tuned" — does not arise at all.

**The whole design is about where the transaction is allowed to run.** 1-Wire is bit-banged and
each bit slot is ~70 µs with IRQs briefly off inside the driver, so a scratchpad read is ~7.6 ms of
blocking CPU. That is CPU time and only CPU time: the drive/sample PWM pair and the LTC2508's
conversions are hardware and free-run straight through it, and GP6 is on PWM slice 3 used as a
plain open-drain GPIO, so §11's same-slice phase-locking invariant (GPIO4/5, slice 2) is untouched.
The one place ms-scale blocking is already known to be affordable is the `i == 0` service point in
`acquire_mode2()` — it absorbs the blocking emit `print()` today, and per the v4.24 note a delay
there lands as *extra settling* for cell 0 rather than as a corrupted read. So every 1-Wire access
is routed through `service_sensors()`, which **is** that point: it is the function's only Mode 2
call site, so the placement rule is enforced by construction rather than by comment. Nothing goes
anywhere near `read_raw_bytes_hold()`.

Three further choices fall out of the same budget. The 750 ms conversion is **never waited on
inline** — `service_ds18b20()` is a two-step state machine that issues `CONVERT T` on one service
tick (~2.2 ms) and reads the scratchpad on a later one (~7.6 ms), so the longest single block is
the read. **SKIP ROM, not MATCH ROM**, which is why `ds18x20.py` is deliberately not used: its
`read_temp()` addresses the device by its 64-bit ROM code, writing 8 extra bytes — ~4.8 ms of
bit-bang — to reach the only thing on the bus that could answer. And the cadence is
`DS18B20_INTERVAL_MS = 30_000`, not `SENSOR_SAMPLE_MS`: board thermal time constants are minutes,
so 1 Hz would be 30× the hot-path exposure for information the 60 s `P` report cannot even carry.
Net cost is ~10 ms per ~200 sweeps — one sweep in 200 running ~5 % long, well inside the 3× window
span guard the PC tools apply, in the benign direction. All 9 scratchpad bytes are read rather than
the 2 that carry the temperature: the extra 7 cost ~4.2 ms and buy the CRC, which is the difference
between a corrupted bit arriving as a wrong temperature and arriving as no temperature. On a line
running past this front end that is worth 4 ms every 30 s.

**Failure is a first-class path, because the detector must not care.** The `onewire` import is
guarded, bus construction is guarded, and every transaction is wrapped; a missing module, a missing
sensor, a bus exception or a CRC failure all resolve to the same thing — `board_temp_dC` reports
`TEMP_INVALID_DC` and acquisition is untouched. There is no error latch: the state machine returns
to idle and retries on the next interval, so a sensor that comes back simply starts working, with
no reset. Health messages print **only on transitions**, following the v4.32 `PACK:` convention,
because a per-attempt print inside the Mode 2 loop is precisely the emit-block hazard v4.27 exists
to measure. `ds18b20_init()` runs *after* `pack_voltage_boot_check()` — the "never fires a pulse
below the floor" guarantee keeps the front of the boot order — and announces its result
**unconditionally**, since `ds_present` starts `False` and a sensor missing at boot is therefore
not a transition; without that the "no sensor" state would be indistinguishable from a healthy
silent one, the same trap v4.32 closed. `service_ds18b20()` sits *after* the pack block in
`service_sensors()` so a pack trip never waits behind a scratchpad read, and the 9-byte buffer is
allocated once at module scope so the Mode 2 loop cannot trigger a GC pass on it.

**Wire format (§11).** Field *counts* on `P` and `V` are unchanged, so no parser breaks. What is
new is a sentinel: `board_temp_dC == -32768` means NO READING, and a consumer must blank rather
than plot it. This is a semantic extension of a documented field and is recorded here rather than
treated as free, following the precedent §9 sets for the `B` counters. It cannot collide with a
real reading — the part's range is −55…+125 °C, i.e. −550…+1250 dC. `board_temp_dC` starts at the
sentinel rather than 0, because before the first conversion there genuinely is no reading and 0 dC
is plausible enough to be believed.

Verified offline, the board not being on the bench: the raw→deci-degC conversion matches all ten
datasheet reference values including both range endpoints and the two's-complement negatives
(−25.0625 °C → −251 dC, floor-rounded in both directions deliberately); and a 20-check mock-bus
exercise of the state machine confirms the convert/read split, SKIP-ROM-never-MATCH-ROM, CRC
failure resolving to the sentinel and not to a wrong number, transition-only printing, unattended
recovery, and exceptions never propagating into the sweep. The bench acceptance gate is unchanged
and still outstanding: sweep interval must stay 0.1445–0.1455 s on the 63-cell profile measured on
the *firmware* clock, and `B`'s `overrun_count` must not rise against a DQ-unplugged baseline.

DESIGN now trails the code in three places, for the next consolidation pass rather than for direct
edit: §8's SPI/pin map gains 1-Wire on GP6, §9's `P`/`V` `board_temp_dC` semantics gain the
sentinel, and §7's "still to measure" list no longer needs a thermistor front end. (2026-08-07)

---

### src/pimd_gui.py — v4.16 — the temperature gauge stops trusting the field, and the tooltip stops lying

Follows fw v4.33. `pimd_gui.py` is the only consumer of `board_temp_dC` anywhere — classviz,
delaycal, rawlog and features do not read it — so this is the entire PC-side surface of the change.

`_update_sensors()` resolves the firmware's no-reading sentinel exactly once, at the top, so
neither the gauge nor the session log ever sees the raw `-32768`. The gauge gets `None`, which
`BarGauge` has always rendered as `—`, so no gauge code changed. The log gets the word `none`
rather than the number: a `-32768` sitting in a `# sensor:` line is indistinguishable from a
temperature to any later reader, and these session CSVs are read long after the run. The test is a
threshold (`TEMP_INVALID_MAX_DC = -10_000`) not an equality, so any future out-of-band code blanks
too, and it cannot swallow a real reading — the part bottoms out at −55 °C, i.e. −550 dC.

Sub-zero readings are now reachable and are left as-is: `BarGauge` clamps the bar fraction to
[0, 1], so they show an empty bar with the correct negative number printed. That is the right split
— the number is the reading, the bar is the glance. The tooltip's "PLACEHOLDER linear ADC scale —
the thermistor front end does not exist yet" is replaced with what the field now is, and keeps one
line naming fw v4.28–v4.32 as the versions that sent a bench pot on it, because session logs from
that epoch exist and their temperature column is not a temperature.

Checked against a stub: normal, sub-zero, both part endpoints and the sentinel all resolve
correctly in gauge and log, with no raw sentinel leaking into either. (2026-08-07)

---

### findings — DS18B20 on GP6: the RP2040's internal pull-up is not adequate, and the 1-Wire cost is CPU-only

Recorded because both questions have answers that are easy to get wrong in the reassuring
direction — the internal pull-up in particular *appears* to work.

**The external 4.7 kΩ pull-up from DQ to +3V3 is required, not belt-and-braces.** The RP2040's
internal pull-up is ~50–80 kΩ. Against even 50–100 pF of bus capacitance that is a rise time of
several µs, and the 1-Wire master samples a read slot ~15 µs in. On a short lead with one device it
can work well enough to pass a bench test and then fail intermittently once the lead is dressed
into the enclosure — which is the worst available failure mode. MicroPython's driver sets the pad
`OPEN_DRAIN | PULL_UP` regardless, so the internal pull-up is *enabled* in normal operation; that
is not a substitute for the external resistor. Use 2.2 kΩ if the lead is long. The sensor runs from
**+3V3, not +5 V** — DQ is tied to its supply through the pull-up and must not exceed the RP2040
rail — in **normal 3-wire mode, not parasite power**: parasite needs an active strong pull-up
driven onto the line for the whole conversion, which this pin cannot do while the sweep is running.
100 nF across VDD/GND at the sensor body, and the DQ lead routed away from the RX front end — it
only switches for ~10 ms every 30 s, but it is a 3V3 digital edge near a front end whose measured
noise floor is ~450 µV (§7).

**The timing answer.** The instinctive worry about 1-Wire here is the 750 ms conversion, and it is
the wrong worry — the conversion is a property of the *sensor*, not of the bus, and is simply not
waited on. The real cost is the bit-banged transaction: ~70 µs per bit slot with IRQs briefly off,
so ~2.2 ms to start a conversion and ~7.6 ms to read the scratchpad. Crucially that is CPU time
only. The PWM pair and the LTC2508 conversions are hardware and free-run through it, so nothing in
the acquisition is perturbed; what is deferred is the firmware's own ability to do the next thing.
That makes placement the entire question, and the answer already existed in the loop: the `i == 0`
service point absorbs the blocking emit `print()` today and the v4.24 note records that a delay
there lands as extra settling for cell 0. GP6 itself is clean — PWM slice 3, used as plain GPIO,
with the slice-2 drive/sample pair untouched.

Also worth having written down: the DS18B20's power-on scratchpad default is `0x0550`, which is
exactly **+85.0 °C** — a read that beats the first conversion returns a plausible hot number, not
an error. That is guarded by sequencing (the read only ever happens 800 ms after a `CONVERT T`
that got a presence pulse) and deliberately *not* by value-filtering: +85.0 is a legal reading, and
rejecting it would mean silently dropping a real over-temperature, the one reading that must not be
lost. (2026-08-07)

---

### src/pimd_gui.py — v4.15 — the connected board's firmware version is on screen and in the log

Asked for alongside a confirmation that the GUI pulls pack/temp early. It does, and has since
v4.14: `connect_port()` sends `E` then `V` the moment the port opens, and `sensor_poll_timer`
re-sends `V` every 10 s. That connect-time `V` is the whole reason the gauges populate promptly
— the firmware's unsolicited `P` telemetry is only every 60 s, so without it a freshly connected
board would show `—` for up to a minute. No change was needed there.

The version turned out to cost nothing on the wire. The firmware has always answered `V` with
`V<fw>,<board_id>,…` and the GUI has always split that line — it simply used indices 8..10 and
threw fields 0 and 1 away. So this is a **display-only change: no firmware edit, no new command,
no wire-format change**, and DESIGN §11's serial-format invariant is untouched.

A `Firmware:` row now sits in the top-left session block under `Session:`, showing `v4.32` with
the board ID in the tooltip, and `—` when nothing is connected. The parse deliberately sits
**ahead of** the existing `len(parts) >= 11` guard, because fields 0 and 1 exist on every
firmware revision while the pack/temp/lockout trailers need v4.28+ — against older firmware the
version still displays and only the gauges stay blank. `_clear_fw_identity()` resets the row on
disconnect: the version is a property of the open connection, and a stale one outliving it would
be worse than no reading. The gauges are left holding their last value, as before.

`setup_file_logging()` also writes `# fw_version: <N>` beside the existing `# pimd_gui v<N>`
line, so a session CSV records which firmware produced it — previously recoverable only by
correlating timestamps against this file. Falls back to `unknown` if Start is somehow reached
before a `V` reply lands. The alert row moved from grid row 2 to row 3 to make space; no change
to its behaviour. (2026-08-07)

---

### DESIGN.md — errata — §9 documents the `V` identify reply with 8 fields; firmware sends 11

Noticed while wiring up the GUI's firmware readout. `DESIGN.md` §9 still describes the reply as
`V<fw>,<board_id>,<num_profiles>,<active_idx>,<freq_hz>,<pulse_ns>,<delay_ns>,<downsample>` —
the pre-v4.28 shape. Firmware v4.28 appended `pack_mV`, `board_temp_dC` and `lockout`, and both
`mcu/pimd_mcu.py` and `src/pimd_gui.py` have depended on those three ever since; they are
documented only in the two file headers.

Harmless in practice — the append-only convention means nothing splits by field count — but §9
is the reference a reader would trust, and it currently understates the record by three fields.
Recorded here rather than fixed in place, per the rule that `DESIGN.md` is regenerated from this
file. For the next consolidation pass (§18). (2026-08-07)

---

### mcu/pimd_mcu.py — v4.32 — the pack absent→present transition always announces itself

Found immediately on the first bench run of v4.31, and worth its own version because it is an
observability defect rather than a cosmetic one. The rig was booted USB-first with the pack
switched on afterwards — the exact workflow v4.31 was written to support — and it worked: the
boot at 3859 mV suspended instead of latching, and the pack coming back at 22 507 mV cleared
`pack_absent` and left `lockout = 0`. But it did all of that **in silence**, because v4.31 only
printed when there was an actual latch to clear, and there had never been one. The transition
was read as a failure to re-arm.

It was not a failure, but the reading was reasonable, and that is the problem: **a suspended
failsafe and an armed one were indistinguishable from the log and from the wire.** `pack_absent`
is not reported on `V` and the re-arm path printed conditionally, so the one state you most need
to be certain you are not in — protection silently switched off — was the state you could not
observe. Same class of defect as the invisible `LOCKOUT:` line recorded under v4.30.

Every path through the absent→present branch now prints exactly once, and every message ends
`— failsafe armed`, so the arming is stated rather than inferred:

- `PACK: present again at <N> mV — failsafe armed` (no latch had been set)
- `PACK: present again at <N> mV — lockout cleared, failsafe armed`
- `PACK: present again at <N> mV, below re-arm floor 21500 mV — lockout state unchanged, failsafe armed`

No logic change: thresholds, debounce, latch semantics and the trip path are all identical to
v4.31, and `pack_voltage_lockout = False` moved inside the branch that tests it, which is a
no-op. The `V` field for `pack_absent` remains not done — the print covers the transition, and
adding a 12th field is still the better fix for the GUI's gauge reading 0.4 V / 0 % / red
`LOCKOUT floor` while the pack is simply switched off. (2026-08-07)

---

### mcu/pimd_mcu.py — v4.31 — pack-absent suspend (< 6 V ⇒ USB power) and re-arm hysteresis; a battery swap no longer needs an MCU reset

Requested after the v4.28 latch proved impractical to live with on the bench. The MCU is
USB-powered and **outlives the `+20V` rail** — measured during the v4.30 investigation, where
the board ran normally with the rail decayed to 3.85 V. So switching the pack off, or swapping
cells, dropped the sense reading to near zero without the firmware rebooting; the failsafe read
that as a catastrophically flat pack and latched, and clearing it needed a physical MCU reset.
That is not a reasonable price for changing a battery, and it also blocked the ordinary workflow
of powering the board over USB for programming and switching the pack on afterwards.

`PACK_ABSENT_MV = 6_000`: below this the rail is **off**, not low. A connected 6S pack cannot
sit at 1 V/cell, and the +15 V rail dropped out some 12 V higher up — so nothing is being
discharged and there is nothing for the failsafe to protect. The check now suspends (clears the
streak, emits one `PACK: rail absent` line) instead of latching, and takes no view on any pack
while suspended, on the grounds that a reading taken with no pack present says nothing about a
pack.

`PACK_REARM_MV = 21_500`: release requires a returning pack to reach this, **not** merely to
clear `PACK_VOLTAGE_TRIP_MV`. That is the hysteresis, and 21.5 V is the DESIGN §12 clean-window
lower edge rather than an arbitrary margin. The reason it is not 21 000: re-arming at the trip
itself would let a genuinely flat pack, switched off and straight back on, return on its no-load
recovery, re-arm, and sag again under load — precisely the cycle the v4.28 hard latch was built
to stop, and precisely how the cells were damaged in the first place. A pack returning below
this leaves the latch untouched and normal trip logic resumes immediately, so a weak pack that
keeps sagging still latches on its own merits.

**This is not a serial re-arm.** No command clears the latch; it still takes the pack physically
going away and a healthy one being presented. The trip threshold, the debounce, the boot check
and the `S`/`G`/`D` rejection are all unchanged.

Verified against a faithful port of the state machine over nine scenarios, all passing: battery
swap mid-session · USB-only boot with the pack switched on later · genuine discharge to the
floor still latching · a flat pack switched off and on **not** re-arming · a fresh pack fitted
after a latch **does** re-arm · pack removed while already locked, returning healthy · weak pack
returning at 21.4 V then sagging, latching on merit · normal running never tripping.

One behaviour to expect rather than be alarmed by: switching the pack off makes the rail **decay
through the 21 → 6 V band**, which takes longer than the 3-sample debounce, so a `LOCKOUT:` line
is emitted on the way down before the absent threshold is reached. It self-clears on re-arm — the
simulated decay sequence ends unlocked. Note also that the sweep does genuinely stop during a
swap (`state = 'stop'`, `set_safe_state()`); the rail is gone, so that is unavoidable. What v4.31
buys is restarting with `G`/`S` afterwards instead of power-cycling the MCU.

Not done, deliberately: `pack_absent` is not on the wire. It would be a safe additive 12th field
on `V` (the GUI tests `len(parts) >= 11`) and would let the pack gauge show "no pack" instead of
0.4 V, SoC 0 % and a red `LOCKOUT floor` caption, which is what it will now display with the
pack switched off. Left out to keep this change to the failsafe alone. (2026-08-07)

---

### mcu/pimd_mcu.py — v4.30 — harden `pack_voltage_boot_check()` against divider RC settling (defensive; original lockout root cause NOT established)

Prompted by a lockout on a healthy 22.5 V pack: the rig came up latched, the gauge reading the
correct voltage beside a `LOCKED OUT` caption. **The cause was never established, and this
entry does not claim it.** What follows is a real weakness found while investigating, worth
fixing on its own merits, plus an explicit record of what was ruled out — because the
investigation produced two confident wrong answers before the measurements landed.

The weakness is genuine. The v4.28 latch logic is unchanged and had been bench-proven against a
pot, but a 10 kΩ pot wiper is a stiff, capacitor-free node that settles instantly, whereas the
v4.29 divider is 22 k ∥ 2.7 k = 2405 Ω against C_tap 1 µF + C_pin 100 nF. **Measured τ = 2.9 ms**
(predicted 2.65 ms, four independent fit points), needing ~22 ms to reach one LSB of settled.
GP26 also sits under the RP2040 pad's default pull-down for the whole MicroPython boot, released
only when `ADC(Pin(26))` is constructed — a few milliseconds before the boot check runs, since
the module is compiled first and then executed, and everything between is definitions costing
microseconds. So the boot check did sample a recovering node. Two fixes:

1. `PACK_SENSE_SETTLE_MS = 100` (≈ 34 τ) slept before the first boot reading.
2. `PACK_VOLTAGE_BOOT_SAMPLE_MS = 20` spacing the boot samples. This is the more important of
   the two: back-to-back the three reads completed within ~2.8 ms and all landed inside the
   same transient, so `PACK_VOLTAGE_TRIP_CONSECUTIVE = 3` had **degenerated into a single
   sample taken at the worst available moment**. The debounce was decorative. That is a defect
   regardless of what caused the original latch.

**But it does not explain the observed lockout.** Reproducing the exact v4.29 path on the bench
at a live 22.5 V pack — pull-down held 400 ms, released, then three back-to-back 64-conversion
averages — gives 21 497 / 21 839 / 22 035 mV, repeatable across three trials, every read
comfortably above the 21 000 mV trip. Verdict: *would not latch*. An earlier claim that the
mechanism was confirmed rested on a 7.30 % depression measured with the rail decayed to 0.42 V
and then scaled to 22.5 V; measured directly at the live voltage the depression is **5.13 %**,
landing at 21 348 mV — 348 mV clear of the trip. **The extrapolation was unsound and the
conclusion drawn from it was wrong.**

Also ruled out, and recorded so it is not re-proposed: the MCU being USB-powered and outliving
the pack rail. That is *true* — the board was later observed running normally with `+20V`
decayed to 3.85 V — but it cannot explain this event, because the rig had been powered pack-first
with USB disconnected and only plugged in afterwards. A fact about the board is not a cause.

The one condition not reproducible from the REPL is a genuine cold start with `+20V` itself
rising from zero; every bench measurement had the rail already up. That remains the leading
hypothesis and nothing more. **The fault has not recurred since.** If it does, `pimd_rawlog.py`
attached across a boot would capture the `LOCKOUT:` line and its mV value — the number lost the
first time because the failsafe printed it to USB CDC with no host listening.

The latch semantics are **untouched** — no threshold moved, no re-arm path added, the hard
latch is still hard. A genuinely flat pack still latches, 100 ms later than before. This is a
sleep at boot, not a scheduler, so §11 is unaffected.

Worth recording for diagnosis, because it cost time: **the LOCKOUT line was invisible.** The
firmware latched at boot and printed its message to USB CDC with no host attached, so the line
was lost; the GUI connected afterwards and learned of the latch only from field 10 of the `V`
poll, captioning the gauge `"22.51 V · LOCKED OUT"`. That caption was initially read as the
alert text, which sent diagnosis after a phantom — a reading *above* the floor appearing in a
latch message. It cannot happen: `_pack_voltage_trip_check()` zeroes the streak in the same
call before testing it, so the printed value is provably ≤ `PACK_VOLTAGE_TRIP_MV`. The
inconsistency was the tell that the number came from somewhere else. **A failsafe that reports
only over a link that may not be attached when it fires is half-instrumented** — the boot-time
latch reason is a candidate for latching into a variable that `V` can report, not just a print.

Also corrected here: the v4.29 header history line said `FULLSCALE 25000 -> 30304`, the interim
divider-only figure, where the version actually shipped 30083. (2026-08-07)

---

### mcu/pimd_mcu.py — v4.29 — pack-voltage divider built and bench-calibrated; FULLSCALE 25000 → 30083 mV; POT pin comments corrected

The v4.28 sense path is no longer notional: the pack-voltage divider has been built and
wired, so `PACK_VOLTAGE_FULLSCALE_MV` stops being a placeholder and becomes a measured
constant. Hardware fitted (design detail in the findings entry below): **22 kΩ / 2.7 kΩ**
from the `+20V` rail at J11 pin 2 to GP26/ADC0, **1 µF** across the 2.7 kΩ and **1 kΩ + 100 nF**
at the pin, all mounted at the MCU end with the divider return on MCU-local ground.
Bench calibration 2026-08-07: **2.460 V at the ADC pin against 22.59 V at the pack**, giving a
measured ratio of **9.18293** — +0.38 % off the 9.14815 nominal, implying R_top ≈ 22.094 kΩ,
inside 1 % tolerance, so the build itself is confirmed correct rather than merely working. A
second point (2.457 V / 22.55 V → 9.17786) agrees to 0.055 %.

**`PACK_VOLTAGE_FULLSCALE_MV = 30_083`**, which is the *fully* calibrated figure —
divider ratio and ADC reference together. It was briefly 30_304 in this same version, from
3.300 × 9.18293, i.e. divider-only with the reference assumed. That figure never ran on
hardware and the version was amended rather than superseded. **The reference is not 3.300 V:**
the first flash attempt didn't take, so the board was still running v4.28's FS = 25 000 when a
pin measured at 2.457 V reported 18 740 mV — which solves directly for **ADC_VREF = 3.2777 V**,
the RP2040-Zero's 3V3 LDO sitting **0.67 % low**. Re-running the firmware's full integer path
(12-bit quantisation, MicroPython's `read_u16` scaling, `* FS // 65535` truncation) at that
reference reproduces the observed 18 740 to within 2 mV. 3.2777 × 9.17786 = 30.083 V.

Worth recording as method: a reading taken against a *known* constant is a complete
calibration, because `reported = V_pin × FS_config / VREF` inverts for VREF with everything
else measured. The accidental stale flash produced the paired `P`-line/DMM measurement this
entry had listed as outstanding work. The LDO term is **0.73 %, 221 mV at full scale** — not a
rounding error, and **per-module**, so this must be redone if the RP2040-Zero is ever swapped.

The old 25 000 value was not merely uncalibrated, it was **unusable**: full scale sat *below*
a full 6S pack (25.2 V charged; §17.13 measured pack B at 25.04 V no-load), so a fresh pack
would have pegged the reading exactly where DESIGN §12's data-quality ceiling lives. At the
bench point it would have reported 18 636 mV against a true 22 590 mV — a −3.95 V error, far
enough below the 21 000 mV trip that the failsafe would have latched instantly on a healthy
pack. Nothing was lost, because the channel had never been wired.

**The failsafe was proven end-to-end on real hardware by the stale-flash incident**, which is
the one good thing to come out of it: 18 740 mV ≤ the 21 000 mV trip, so the firmware latched,
rejected `S`/`G`/`D`, and `pimd_gui.py` painted the lockout state and caption correctly. The
whole v4.28 chain — ADC read, debounce, latch, `V`-line lockout field, GUI alert — ran against
a live pack for the first time. It was only ever fed a wrong scale factor.

Also corrected here, comment-only but riding along because it was flagged by v4.28's own
"VERIFY against schematic sheet 1" instruction and the check **failed**: the pin→pot mapping
runs backwards from the pin numbering. Sheet 1 wires **GP29→POT-0, GP28→POT-1, GP27→POT-2,
GP26→POT-3**, so v4.28's "GP26 / ADC0, POT-0" and "GP27 / ADC1, POT-1" named the wrong pots.
The *pins* were right (both are ADC-capable and both were pot-wired), so no behaviour was
wrong — but the v4.28 bench procedure would have had the operator turning RV5/RV6 and seeing
nothing move. GP26's pot **RV8 has now been removed** from the board and its footprint reused
for the divider (pin 1 = GND, pin 2 = wiper/GP26, pin 3 = +3V3 left open); leaving it fitted
would have put 10 kΩ across a 2.4 kΩ divider node and swamped the ratio. GP27 remains on RV7.
`THERM_TEMP_FULLSCALE_DECIC` is untouched and still a placeholder. (2026-08-07)

---

### findings — the +20V rail is the correct pack-sense node, and the sense-divider error budget is dominated by the RP2040's own 3V3 reference

Design pass behind the v4.29 divider above, from DESIGN §12 plus both schematic sheets. Three
results worth keeping.

**`+20V` is pack terminal voltage, with no diode drop to compensate.** D4 (1N4004) reads as a
series element in the block description, but on sheet 1 it is a **shunt reverse-polarity
clamp** — cathode on `+20V`, anode on GND, blowing F1 on reversal. So the sense node needs no
forward-drop correction and, more importantly, does not drift with load current the way a
series diode would between idle and streaming (a ~0.3 V, state-dependent error that would have
been indistinguishable from the IR-drop effect §17.13 measured at 0.29 V). `+20V` is also
downstream of SW3, so the divider draws nothing with the rig switched off. J11 pin 2 is the tap.

**Sizing.** Ratio 1/9.148 puts full scale at 30.19 V nominal, so a 25.2 V pack sits at 83.5 %
of range and the ADC pin cannot be over-driven until the input passes 30.2 V — above anything
the board survives anyway. Thevenin 2.4 kΩ, drain 1.02 mA (10.5 mAh over a full 10.33 h
session, 0.2 % of the pack), 23 mW in R_top. The pack-referred leakage error reduces to exactly
**1 µA × R_top**, which is what caps R_top at ~22 kΩ rather than the 82 kΩ a drain-first choice
would suggest. Filter poles at 66 Hz and 1.6 kHz give 237× rejection at a 5 kHz TX rate and
5900× at 25 kHz, settling in 17 ms against the 1 Hz sample. Divider mounted at the MCU with
only the stiff `+20V` lead crossing the board: putting R_top at the source end instead would
have left a 2.4 kΩ node on a long wire beside a µV-scale front end.

**Error budget, pack-referred at 25 V, after one-point calibration** — resistor *tolerance*
does not appear, because a divider is perfectly linear and one-point calibration removes the
ratio error across the whole range; only tempco survives. 3V3 LDO drift ±75 mV · resistor
tempco mismatch (50 ppm/°C over 30 °C) ±38 mV · ADC leakage ±22 mV · RP2040 SAR DNL/INL ±30 mV ·
quantisation ±7 mV → **RSS ≈ 92 mV**. That is comfortably sufficient for the 21.0 V failsafe,
which is the whole reason v4.28 exists, but **marginal for placing the pack inside §12's
21.5 / 23.3 / 24.0 V data-quality bands**, which want ±50 mV. The dominant term is the module's
3V3 LDO serving as the ADC reference. If band placement is wanted from this channel, the fix is
cheap and uses parts already on the board: divide the existing `5V-REF` (U5, LTC6655-5 —
0.025 % initial, 2 ppm/°C) 10k/10k into spare GP29, and compute the pack ratiometrically. LDO
drift then cancels entirely and RSS falls to ≈53 mV; it also lands the reference conversion at
2.50 V, close to the pack's 2.75 V, so both sit on the same part of the SAR's transfer curve.
Not built.

Buffering with the spare LT6203 half was considered and rejected: U3 runs single-supply from
**+12 V**, so its output could present 12 V to a 3.3 V ADC pin on any fault — not worth it for
a 1 Hz housekeeping channel.

**Unrelated observation on the same node, recorded because it was found here:** C18 is a
4700 µF **25 V** part on `+20V`, and a fully-charged 6S pack is 25.2 V (§17.13 measured pack B
at 25.04 V no-load). It runs at ~100 % of rating on a fresh pack, which ages an electrolytic
quickly. A 35 V part is the obvious swap. Not acted on. (2026-08-07)

---

### findings — the RX network is critically damped and the undershoot is not it; damping is the wrong knob for a second reason

Follow-up to the "CORRECTION: the negative lobe is real" entry below, answering "was the model wrong because we are still
underdamped?" Offline, no bench time. Three separate results.

**1. Why the v1 extrapolation failed: it was unconstrained, not merely inaccurate.** Fitting
`A·exp(−t/τ_f) − B·exp(−t/τ_s)` to the same four calibrated columns with τ_s pinned at a series
of values gives fits that agree with the data to **≤ 2 %** while predicting anything from
**+64 mV to −400 mV** at sd 14.7 µs:

| τ_s (µs) | τ_f (µs) | worst residual | predicted V(14.7 µs) |
|---:|---:|---:|---:|
| 1.5 | 1.50 | 9.3 % | +64 mV |
| 2.0 | 2.00 | 8.0 % | +19 mV |
| 3.0 | 2.99 | 2.6 % | −180 mV |
| 5.0 | 2.75 | 2.0 % | −302 mV |
| 8.0 | 2.47 | 2.0 % | −336 mV |
| 30.0 | 2.27 | 2.1 % | −400 mV |

A ~2 % difference in fit quality moves the extrapolation by 460 mV. Sums of exponentials are
famously ill-conditioned and four points over 0.88 decades cannot separate them; the
critically-damped form v1 chose (+38.6 mV) is one member of that family, not the answer, and the
measurement (at or below the 2.441 mV rail) sits inside the family's spread. **The v1 entry
should have quoted the spread and did not.** The lesson is not "fit harder" — it is that this
region needs samples, and it does not have them: between clip release and the rail,
`cal_110_full_range_v4` places exactly **two** columns on the 150 µs band (7.904 and 10.912 µs)
and two on the 100 µs band (7.528 and 10.496 µs). Two points cannot constrain a decay.

**2. The network is critically damped, and the arithmetic closes on itself.** For the parallel
RLC (R1 shunting the coil, C its self-capacitance): α = 1/(2RC), ω₀ = 1/√(LC),
ζ = α/ω₀ = √(L/C)/(2R), and at ζ = 1 the response is `(a + b·t)·exp(−t/τ)` with τ = 2RC — which
is the form that fitted the ladder to ±0.84 %. Taking the measured τ = 0.920 µs and
R1 = 1.30 kΩ: **C = τ/2R = 354 pF**, ω₀ = 1/τ = 1.087×10⁶ rad/s (**f₀ = 173 kHz**),
**L = 1/(ω₀²C) = 2.39 mH**, so **√(L/C) = 2600 Ω** and **R_crit = ½√(L/C) = 1300 Ω** — against
DESIGN §7's independently *measured* 1300–1400 Ω, and against the fitted R1 of 1300 Ω. **ζ = 1.00.**
Two of those numbers were measured on the bench years apart by different means and they agree, so
this is a real check, not a tautology. It also puts a value on §7's outstanding "re-measure RX
self-resonance to pin L and C" item: **354 pF / 2.39 mH, inferred from the decay rather than from
a resonance**, and worth confirming against the direct measurement when it happens. (The stale
figures were 311 pF / 3.9 mH — the capacitance was close; the inductance was not.)

**3. The undershoot cannot be the coil, by a factor of 7000.** The coil transient decays with
τ = 0.92 µs from ~4.7 V at clip release (sd 7.9 µs). By sd 21.9 µs that is 15.2 time constants,
leaving **1.2 × 10⁻³ mV**. The measured deviation from the settled level there is **−8.45 mV** —
7341× more than the network can still supply. By sd 43.9 µs, where air has only just reached the
pedestal, the coil term is 5 × 10⁻¹⁴ mV. Underdamping would not rescue this: at ζ = 0.9 the ring
is 75 kHz and each half-cycle is attenuated ×1.5 × 10⁻³, so the visible consequence is one small
undershoot ~3 µs after the crossing and nothing after — not a lobe bottoming at 15 µs and taking
until 44 µs to clear. **So the answer to "are we still underdamped" is no, and the reasoning that
R1 is the wrong knob (2026-08-05 entry) survives the correction intact — for a stronger reason
than the one given then.**

**4. And it is not a linear network response at all.** From the recovery, −8.45 mV at sd 21.88 µs
to −0.97 mV at sd 30.99 µs, the undershoot's own time constant is **τ ≈ 4.2 µs**, 4.6× the coil's.
A linear network released at t = 0 has every mode present from t = 0, so that component
back-extrapolates to **−114 mV at sd 10.912 µs — 13 % of the 876 mV signal there** — whereas the
ladder fit agrees with measurement to ~3 % at that delay. **The component was not there yet.**
A term that switches on late is the signature of a recovery from saturation, not of an RLC being
released. That is consistent with the LT6203 overload-recovery hypothesis and inconsistent with
any passive coil-network explanation, but it is a deduction from two fitted points and a 3 %
agreement across two epochs, so it is **suggestive, not settled** — the scope at the preamp output
is still the instrument that decides. Note also that target-sensitivity does **not** discriminate
here: overload recovery depends on how hard the stage was overloaded, so a target that changes the
drive changes the recovery too, which is why the +7.12 mV the spanner adds at sd 21.9 µs is weaker
evidence than it looks. (2026-08-07)

---

### findings — CORRECTION: the negative lobe is real, it is in air, and it is on every band

Supersedes the conclusion of the entry below it (2026-08-05, "the calibrated ladder puts the air
decay at ~60 mV where 3 mV was reported"). That entry argued from a ladder fit that the coil
network had no room for the reported undershoot and leaned toward amplifier recovery. The
2026-08-07 session measures air directly across the whole delay sweep and **the undershoot is
there, in air, on all ten bands.** The argument was wrong; the fit that produced it was fine
inside its own range and simply does not extrapolate.

Source: `src/data/sessions/rawlog_20260807_194234.txt`, Mode 2 W5 stream over
`cal_110_full_range_v4` (10 bands × 11 delays), fw 4.33, 4.07 Hz, 562 frames, 138 s.

**What air actually does on the 150 µs / 2 kHz band** (n = 222 frames, σ ≤ 0.18 mV on every
post-rail cell): 4698.9 mV at sd 7.904 µs → 891.7 at 10.912 → **2.441 at 15.448** → 7.40 at
21.880 → 14.88 at 30.992 → 16.14 at 43.888, then a slow sag to 15.86 at 250 µs. The fit
predicted 30 mV at 15.448 µs. On the 100 µs band air reads **2.441 mV at sd 14.712 µs** — the
2026-08-05 session's "flat 3 mV bottom around sd 14 µs", reproduced to the delay. Every band
bottoms out between 2.441 and 4.272 mV somewhere in sd 11.7–16.0 µs, and the bottom moves only
weakly with pulse width (12.3 µs at 4 µs drive, 15.4 µs at 150 µs drive) — a feature nearly
fixed in absolute time after turn-off, which is worth explaining but is not explained here.

**2.441 mV is the rail, and the evidence is now direct.** Its σ is exactly 0.000 across every
frame of every class — air, spanner and copper all read the identical code. 2441 µV is 4 × the
raw path's 610.35 µV LSB (5 V / 8192), so it is not an ADC zero code either. **The 15.448 µs
column of the 150 µs band is a dead cell: it cannot respond to any target.** Same for the
100 µs band's 14.712 µs column.

**Where the fit does and does not hold.** At sd 10.912 µs the fit gives 848 mV against 892
measured (−5 %), and it is ±0.84 % on the four columns it was fitted to (sd 8.4–11.3 µs). Past
~11 µs it diverges hard. So the correct statement is narrow: *the calibrated ladder constrains
the decay only over the volt-scale region it samples, and says nothing about what happens below
0.5 V.* The 2026-08-05 entry's supporting arguments — that ~400× rescaling would be needed, that
a two-pole negative term wide enough to reach the rail could not recover by 20 µs — were
reasoning from that same over-extended fit and should not be relied on. What remains open is
unchanged and still needs a scope at the preamp output: whether the lobe is the coil network or
LT6203 overload recovery. **This session does not settle it** — see below, it argues weakly the
other way.

**Targets: the polarity convention lives entirely on the pre-rail cells.** Two targets at 60 mm,
window means over the plateau of each presentation:

| sd (µs) | air | Δ steel spanner (271 g) | Δ copper pipe (122 g) |
|---:|---:|---:|---:|
| 7.904 | 4698.9 | **+10.8** | **−15.1** |
| 10.912 | 891.7 | **+24.8** | **−12.7** |
| 15.448 | 2.441 | +0.000 | +0.000 |
| 21.880 | 7.40 | +7.12 | +2.46 |
| 30.992 | 14.88 | +3.46 | +1.29 |
| 43.888 | 16.14 | +1.95 | +1.15 |
| 62.152 | 16.13 | +1.19 | +0.91 |
| 88.016 | 16.04 | +0.63 | +0.81 |
| 124.648 | 15.97 | +0.35 | +0.63 |
| 176.528 | 15.90 | +0.15 | +0.51 |
| 250.000 | 15.86 | +0.09 | +0.40 |

Three results in that table. **(1)** §17.6's ferrous-positive / non-ferrous-negative convention
holds on the two pre-rail columns and *only* there — steel +25 mV, copper −13 mV at 10.9 µs.
**(2)** Past the rail **both targets read positive**, so sign is not a discriminant in the late
window; the 2026-08-05 entry's suggestion that a non-ferrous target would cross down through the
pedestal is not what happens. **(3)** The late window discriminates by *decay rate* instead:
steel falls 73× from 21.9 to 250 µs while copper falls only 6.2×, so **copper overtakes steel at
~77 µs** and at 250 µs is 4.3× more visible (+0.40 vs +0.09 mV). A long thick copper tube having
the longer eddy time constant is ordinary PI physics; the point is that it makes the 88–250 µs
columns non-ferrous-selective, which is the opposite of what those columns were assumed to be
worth.

**The targets do move the readings around the lobe, which bears on the open coil-vs-amplifier
question.** At 21.880 µs — the first cell off the rail — the spanner adds +7.12 mV on a 7.40 mV
air baseline, nearly a doubling. An amplifier-recovery artefact should be indifferent to metal.
That is *suggestive*, not decisive: 21.9 µs is past the bottom, and nothing can be learned at the
bottom itself because that cell is railed for every class. A scope is still the instrument that
settles it.

**Method note that changed a number, not just a procedure.** `MARK acquire` records the state
*from that point on*, so the marks locate presentations but do not bracket them — in this session
the second `Fe_spanner_01` mark lands ~9 s after the spanner was already away. Segmenting on the
marks as written mixes ~30 s of air into the spanner window and reports Δ at 21.88 µs as
**+3.5 mV against the wrong baseline, sign-flipped depending on which air segment is used**,
versus **+7.12 mV** from the presentation plateau. The tool therefore uses the marks only to name
each excursion and takes the window from the probe cell's own plateau. Worth considering a
paired place/remove marker in `pimd_rawlog` — not proposed as a change here. (2026-08-07)

---

### utilities/decay_model/decaymodel.py — v2 — `--session` overlay of measured air/ferrous/non-ferrous

Adds `load_session()`: reads a `pimd_rawlog` session, segments it into air and one window per
target presentation, and returns per-class means for one band, which the three existing panels
then overlay as solid measured traces. The v1 modelled curves stay on the figure but are demoted
to thin dashed — they are the reference the measurement broke, and the header now says so rather
than presenting them as prediction. Panel titles, annotations and axis limits switch to the
measured story when `--session` is given; without it the tool renders exactly as v1 did.

The W-line parse mirrors `pimd_rawlog._parse_w_line` rather than importing it — that module pulls
in PyQt6 at import time and this tool is offline. Window detection is the substantive part and is
documented in the function docstring: marks locate, the data delimits (see the findings entry
above for why that distinction changes the answer), each presentation is trimmed to the top 80 %
of its own excursion to drop the operator's approach/withdraw ramps and the 32-deep rolling
average's ~8 s smear, seed searches are narrow and skip already-claimed frames so a strong
target's tail cannot out-peak a weaker one, and air is everything outside the windows plus a
guard, after a 20 s skip for the §17.13 stream-start transient. Run:
`.venv/bin/python utilities/decay_model/decaymodel.py --session src/data/sessions/rawlog_20260807_194234.txt --out …`. (2026-08-07)

---

### findings — the calibrated ladder puts the air decay at ~60 mV where 3 mV was reported, and it settles without an undershoot

**SUPERSEDED 2026-08-07 — see "CORRECTION: the negative lobe is real, it is in air, and it is on every band" above.** Read this header
before quoting anything below it.

- **Wrong:** "the coil network's own poles have no room for a −14 mV excursion at 14 µs", and
  the supporting arguments (the ~400× rescaling, the recovery-time contradiction). Direct
  measurement of air shows the undershoot on every band, reaching the 2.441 mV rail at sd
  14.7 µs on this very band.
- **Wrong:** consequence 1, "air carries no information past ~21 µs". Measured air is still
  recovering at sd 21.9 µs (7.40 mV) and 31.0 µs (14.88 mV) and only reaches the pedestal
  around 44 µs — and then sags 16.14 → 15.86 mV out to 250 µs, a 0.28 mV slope against a
  0.07 mV σ, so it is not flat there either. The pedestal is a level the air approaches, not
  one it sits on.
- **Wrong:** consequence 3's sign claim. Both targets read positive past the rail; non-ferrous
  does not cross down through the pedestal.
- **Stands:** the τ = 0.920 µs critically-damped fit and its ±0.84 % residuals over sd
  8.4–11.3 µs, the pedestal's existence, and consequence 2 — `cal_110_full_range_v4`'s interior
  threshold labels are wrong, now confirmed directly (measured 891 mV at sd 10.912 µs, so 0.5 V
  falls near 11.5 µs, not the 62 µs its label implies).

Offline analysis, no bench time and no hardware change. Prompted by a request to plot the
estimated decay and its crossings from 4 µs / ~5 V out to 250 µs / a few mV on the **150 µs**
drive band. New tool `utilities/decay_model/decaymodel.py` (entry below) does the fitting; this
entry is what it found.

**The air decay was fitted to hard data that the previous two entries did not use.** The nine
`delays_us` in each band of `cal_63_air_bat_v3` are delaycal-converged (0.3 mV, 8 ns grid)
sample points at which the trace *actually reaches* the column's threshold voltage — nine
(delay, volts) pairs on the real curve, per band, sitting in the tracked profile the whole time.
Taking the four columns clear of clamp release (3.8 / 2.4 / 1.5 / 0.5 V at 8.360 / 9.240 /
9.944 / 11.320 µs on the 100 µs band) and fitting the **critically damped** form
`V = 17 mV + (a + b·t)·exp(−t/τ)` — the shape §7's measured R1 ≈ 1.3k should give — lands
**τ = 0.920 µs with residuals of −0.14 / +0.76 / −0.84 / +0.23 %**. Three points to make about
that number. It is a genuine test of the two-real-pole claim, not an assumption: four points, three
parameters, and the form could have failed. It agrees with the τ_fast ≈ 0.9 µs the 2026-08-05
entry fitted by hand from three points on a completely different data set. And it reproduces,
*without being fitted to them*, the same session's held-back observations — model 17.116 mV at
sd 20 µs against "~17 mV by 20 µs", 17.000 against SDOA's 16.674 mV at sd 30 µs, 17.000 at
sd 100 µs against "unchanged".

**Everything the two entries above record is reproduced except the undershoot.** The fitted
curve is **monotonic**: it lands on the 17 mV pedestal from above and never crosses it. At
sd 14 µs, where the session reports a flat 3 mV bottom, the calibrated decay is at **59.6 mV** —
57 mV above the observation and 43 mV above the pedestal. No rescaling closes that: the
amplitude factor required is ~400×, against the ~11× §17.13 allows across the *entire*
pack-voltage range, and the same session's own sd 8 µs reading (4.3 V, model 4.11 V) rules out
a delay offset. Nor does a negative term fix it while staying consistent — any second pole steep
enough to reach the rail by 14 µs is several µs wide and takes ~25 µs to recover, contradicting
both the hand-read 0.5–1 µs flat *and* the measured "17 mV by 20 µs". Fitting a two-pole model
to all of it at once was tried first and degrades the ladder to ±12–24 %.

**This does not overturn the observation; it narrows what the observation can be.** The
2026-08-05 entry already listed, and could not settle, whether the lobe belongs to the coil
network or is LT6203 overload recovery. This is independent support for the second: the coil
network's own poles, pinned by the calibration and by the settling behaviour the same session
measured, have no room for a −14 mV excursion at 14 µs. It remains **inferred from a fit, not
measured** — a scope at the preamp output settles it, and so does the target test that entry
already names (an amplifier artefact will not move when metal approaches). If the lobe *is* real
and *is* the coil, then the calibrated ladder and the fit are both wrong in a way this analysis
cannot see, and that is the more interesting outcome of the two.

**Three consequences that do not depend on which way the lobe goes.**

1. **Air carries no information past ~21 µs on this band.** The fitted curve is inside ±3σ of
   the pedestal (±44 µV at the measured 14–15 µV floor) from sd 21.2 µs onward. Of the eleven
   columns in `cal_110_full_range_v4`'s 150 µs band, **eight** — 21.88, 30.99, 43.89, 62.15,
   88.02, 124.65, 176.53, 250 µs — sit in that region. They are not dead cells; they are cells
   where the air baseline is flat and *every* millivolt is target. That is the same thing the
   2026-08-03 close-target entry saw from the other side, and it is directly relevant to the
   cell-reduction work: those eight columns are near-duplicates *in air* and only separate on a
   target.
2. **`cal_110_full_range_v4`'s interior threshold labels are wrong by a large factor, as its own
   profile entry warned.** That ladder's `threshold_v` came across from `test v4h` "pending the
   voltages this ladder actually reaches on the bench". Against the fit, the column labelled
   0.5 V at 62.15 µs is on the pedestal; 0.5 V is actually reached near 11.5 µs. Only the first
   two or three columns are on the decay at all. The delays are bench-verified and fine — it is
   the voltage labels that should not be quoted.
3. **The rail is closer than the free-air numbers suggest, and it is a non-ferrous problem.**
   Scaling a target term to the one measured post-pedestal amplitude (+11.0 mV over floor at
   22 µs, 2026-08-03 close capture) and giving it the ordinary sign convention (§17.6), a
   *ferrous* target never crosses the pedestal — it sits above it and is still ~0.9 mV up at
   sd 250 µs. A *non-ferrous* target crosses **down** through the pedestal (≈15.4 µs on this
   band) and bottoms out under it, and at the measured coupling it reaches 5.2 mV — **19 % from
   the 3 mV rail.** So the sign of the post-pedestal reading is itself a family discriminant,
   and the cells at risk of clipping are the non-ferrous ones, at close range, in the same
   delay window the 2026-08-05 entry already flagged as unusable. Both target curves are
   illustrative — sign and amplitude anchored, time constants assumed — so treat the 15.4 µs
   as a shape, not a number. (2026-08-05)

---

### utilities/decay_model/decaymodel.py — v1 — new offline decay/crossing model and plot

New standalone tool, offline, read-only against the repo (reads the tracked profile JSONs,
writes only its PNG). Fits the air decay to the calibrated `cal_63_air_bat_v3` ladder,
extrapolates the rigid band shift to a 150 µs drive pulse (+0.24 µs, from the shrinking
per-band slope that §14.6 flags as a coil-current plateau), overlays illustrative ferrous and
non-ferrous target terms, and renders a three-panel figure across 4 → 250 µs sample delay:
the whole span on log-log, the region where the three curves separate, and the late window
with `cal_110_full_range_v4`'s 150 µs columns marked. Prints every number it derives, labelled
measured or modelled.

It exists because that separation is the whole point — the module docstring is an explicit
measured/modelled/unresolved split, the fit consumes only the calibrated ladder, and the
2026-08-05 session observations are **held back and used as a check**, which is what makes the
agreement at sd 20/30/100 µs meaningful and the disagreement at sd 14 µs legible. The model is
not drawn where it is not valid (below its own peak, across the clamp-release stretch), and the
lobe is plotted as an observation sitting off the curve rather than fitted into it. Run:
`.venv/bin/python utilities/decay_model/decaymodel.py [--pulse 150] [--out …]`. (2026-08-05)

---

### findings — the sub-0.5 V plateau has a negative lobe under it; the 3 mV bottom is a rail, not the floor

Bench session 2026-08-05, `pimd_gui` v4.14 (title bar), Mode 1, 100.0 µs pulse / DS 256, pack
23.16 V ("clean window"), board 34.4 °C, GUI at 500 µV/div, on battery. Firmware version not
captured this session. The operator reported the sweep at 3.125 kHz; the reference screenshot
is 4.000 kHz / 100.0 µs / sd 30.000 µs. Delay figures below are as reported. Sample delay swept
by hand across the region the 2026-08-03 entries left open.

**Observed.** ~4.3 V at sd = 8 µs, falling to a **flat ~3 mV bottom** held across roughly
0.5–1 µs around sd ≈ 14 µs, then rising to ~17 mV by sd ≈ 20 µs and sitting there unchanged all
the way out to sd = 100 µs. Across that boundary the Mode 1 std dev drops from ~300 µV to
**14–15 µV**, and the cell still responds clearly to every metal presented. Below the boundary
the reading shows the usual thermal behaviour; above it, it does not. Both acquisition paths
agree on the settled level — at sd = 30 µs the filtered path (SDOA) reads 16.674 mV / σ 15 µV
while the raw boxcar (SDOB, `A32`) reads 16.269 mV / σ 709 µV — so the plateau is not a
decimation-filter artefact. (That 709 µV is the firmware's per-sample σ over the 32 raw samples,
not the σ of their mean, so it is directly comparable to §7's ±1400 µV single-sample figure and
is better than it at this operating point.)

**This refines the 2026-08-03 reading; it does not overturn it.** That entry had the sub-0.5 V
columns "crossing below the RX chain's floor", with the mean thereafter reading the floor
(~16–18 mV, the same in every band regardless of delay). An additive floor can only be
approached from above. **A dip to 3 mV, below the 17 mV level, cannot be a floor effect** — it
requires a signal component of about −14 mV or more negative. The earlier fine sweeps (a smooth
monotonic 6 → 17 mV rise on the 25 kHz bands) were looking at the *recovery* side of a feature
whose bottom they never reached.

Three separate things are stacked in the trace, and separating them is most of the value here.

1. **The ~17 mV level is a DC pedestal — the instrument zero, not signal.** The 2026-08-03
   measurement is the proof: a level identical across delays from 20 µs to 250 µs and across
   every band cannot be decay. The arithmetic is consistent with LT6203 input bias current
   flowing out through R9 = 4.7k — near the ground rail the part's PNP input pair sources bias
   current, and ~3.6 µA × 4.7k ≈ +17 mV, with the datasheet typical (6.5 µA) giving ~31 mV, so
   the measured level sits inside the part's spread. **Inferred from the datasheet and the
   measured level — not measured.** The cheap check is to add 4.7k in series with R9 (the safe
   direction: it *reduces* clamp current, which §7 already flags as possibly under-estimated)
   and see whether the pedestal moves to ~34 mV. If it does not, this model is wrong and the
   pedestal is something else — amp Vos with unexpected gain, or ADC offset.
2. **The 3 mV bottom is a hard rail.** The signal path is unipolar — single +12 V supply, 0–5 V
   into the ADC — so the LT6203 output saturates a few mV above ground. The flat bottom is the
   signature; a genuine minimum would turn around smoothly, and the operator confirmed it is
   flat across several delay steps rather than a single touch. It is *not* an ADC zero code,
   which would read exactly 0 µV. **The lobe's true depth is therefore unmeasurable through this
   path** — at least −14 mV, and the width of the flat says more than that.
3. **One sign reversal is expected behaviour for this front end, not a defect.** The RX network
   is second order with two real poles (≈ R1·C fast, ≈ L/R1 slow). Released with energy in
   *both* L and C — which a 265 V flyback guarantees — the response is a sum of two decaying
   exponentials with opposite-sign residues, and that has exactly **one** zero crossing. A
   critically damped release does it too; it is not evidence of wrong damping. **It is not
   ringing** — ringing means repeated crossings, and §17.4 already located the real ring at
   ~2.08 MHz, dead by 7–8 µs, whereas this lobe is ~7 µs wide (≈150 kHz half-period). Using §7's
   stale inductance, L/R1 = 3.9 mH / 1.3k ≈ 3 µs is the right order for the slow pole. This is a
   direct use for §7's outstanding "re-measure RX self-resonance to pin L and C" item.

**Consequence for R1: damping is the wrong knob.** Reducing R1 pushes the two poles further
apart — null earlier, reverse tail *longer*, which is worse for the quiet region past it.
Raising it pulls them together — null later, tail shorter — until it crosses into real ringing.
Neither removes the crossing. No front-end change proposed and none made.

**What is not established.** Whether the lobe belongs to the coil network at all. The LT6203
input is clamped hard for the first ~7 µs of every cycle at this duty (40 % at 4 kHz / 100 µs),
and amplifier overload recovery produces mV-scale tails over µs that would look identical from
the ADC's side. Nothing in the delay-sweep data distinguishes the two, and it cannot be settled
from the record. The discriminating test does not need a scope: an amplifier artefact will not
move when a target approaches. Scope detail to follow from the operator.

**Operating note.** Any cell landing between roughly 13 and 20 µs at this band is reading a
rail, not a signal — non-linear, sign-ambiguous and worthless as a calibration point. The locked
`cal_63_air_bat_v3` never sweeps below 0.5 V so it is unaffected, but hand-edited ladders that go
lower can land there; `pimd_delaycal` has a signal-detect *ceiling* (`sp_signal_v`, 4.9 V) and no
floor, so nothing currently warns about it. (2026-08-05)

---

### findings — the recorded noise floors are slope × timing jitter, not amplifier noise

Follow-up to the entry immediately above, same session.

The σ drop across the boundary — ~300 µV below, 14–15 µV above — is not the noise improving. It
is the **slope term going to zero**. §14.3 already models the soaked per-cell floor as
slope × equivalent timing jitter (70–130 ps across most of the grid); this is the same model seen
from the other end, at a delay where the slope against sample delay is ~0 and only the amplitude
term survives.

Consistency check, order of magnitude only: fitting τ_fast ≈ 0.9 µs to the 4.3 V @ 8 µs →
~17 mV @ ~13 µs leg gives a slope near sd = 8 µs of ~4.8 mV/ns, and 300 µV / 4.8 mV/ns ≈ **63 ps**,
just under §14.3's 70–130 ps band. The τ is fitted from three hand-read points and the 300 µV was
not tied to a specific delay, so this is corroboration of the model, not a measurement of the
jitter.

**Why this matters more than it looks.** Every filtered-path noise figure in DESIGN §3 (≈ ±200 µV,
and §7's "real-world 450 µV floor") was measured *on the slope*, so each is a mixture of two
unrelated quantities. Measured with the slope removed, the same chain reads **14–15 µV at DS 256**
— 13–30× better. The amplitude floor and the timing floor are separate specifications. The §14.8
re-measurement backlog should record which one it is measuring: a noise figure without the slope
it was taken on is not comparable to another one.

**The same argument disposes of thermal drift in this region.** §14.1's 50 µV/s predicts ~9 mV
over the reference screenshot's 180 s trace; the trace is flat to well inside 100 µV at
500 µV/div — at least ~100× below prediction. Drift cannot couple into a reading whose slope
against delay is zero, which would make the far side of the null intrinsically immune to the
reference-age ceiling §14.1 calls a hard limit on any frozen-reference measurement. Read from one
screenshot, not from a dedicated soak — worth measuring properly before it is relied on.

**Open, and the reason the negative lobe is worth pursuing rather than wearing.** Crossing *times*
are invariant under amplitude scaling, and the dominant confounder in §14.7/§17.13 is pack voltage
*scaling* the decay (~11× across its range, against ~2.5–3× for soak). The clip destroys the
lobe's depth but not its timing: the trace crosses the 17 mV pedestal cleanly on both sides of the
lobe, and both crossings are in the linear region, so both are measurable now with no hardware
change. From the same τ fit the slope at the crossing is ~200× shallower than at sd = 8 µs (order
20 µV/ns), which against the measured 14 µV floor puts the crossing's own resolution below a
nanosecond and implies ~1 mV of target signal would move it ~40 ns. That is roughly the *same*
SNR as reading the 1 mV directly in the flat window — the attraction is not sensitivity but a
coordinate that does not move with the pack. Whether the crossing carries target information at
all is unmeasured, and is the same experiment that settles the coil-vs-amplifier question in the
entry above. (2026-08-05)

---

### src/pimd_gui.py — v4.14 — UI folded into the app, pack/temp gauges, session logs, full pulse/delay range

Five changes in one pass, all in the Mode 1 GUI; no firmware or wire-protocol change (DESIGN
§9/§11 untouched — the app still sends only `S`/`E`/`*`/`A<n>`/`V`).

**1. `pimd111.ui` / `pimd111_ui.py` retired.** The window is now built in code
(`_build_ui()` and four `_build_*_block()` helpers), like `pimd_classviz.py`,
`pimd_delaycal.py` and `pimd_rawlog.py`. The generated module had become a liability rather
than a convenience: every edit since v4.06 was a *deletion* performed at runtime
(`getattr(self.ui, 'label_9').setParent(None)` for the dead F1–F4 preset chips, then the same
for four V/div radios in v4.12), with new widgets bolted onto layouts by object name
(`gridLayout_2`, `formLayout_10`) — so the real layout could only be read by holding both files
in your head at once, and Qt Designer had not been used since 2026-07-02. Both files deleted;
`README.md`'s layout listing and `USAGE.md` §3 updated. Behaviour preserved deliberately:
same widgets, same button-group ids (now assigned explicitly with `addButton(btn, id)` rather
than relying on Qt's implicit −2, −3, … allocation order, which the `vert_scales` /
`horiz_scales` dicts silently depended on), same key chips, same settings keys — an existing
`gui_settings.json` loads unchanged.

*One latent bug fell out of the move.* `apply_soc_defaults()` sets the sliders to values they
already hold at construction, so `valueChanged` never fired and the three QLineEdits kept
whatever text the `.ui` file carried (`25.0 kHz` / `10.0 us` / `7.6 us`) until settings were
loaded over them — on a first run with no settings file those stale strings were what
`change_parameters()` then parsed and sent. The defaults now set the displays explicitly.

**2. ENT / SPC removed.** The Return→Connect and Space→Start/Stop shortcuts and their two
chips are gone. Both are single, deliberate actions at the start of a run, and Space in
particular is one fat finger away from stopping a soaked rig mid-capture.

**3. Connect / Start brought in line with the newer apps.** Connect now sends `E` (safe state)
then `V`, as `pimd_classviz.py` and `pimd_delaycal.py` do; Start is **disabled until a port is
open** and refuses to run without one (previously "Running" would light up green against a
closed port, log to a file and show nothing, with no indication why); disconnecting stops a
running acquisition first; the port field is `.strip()`ed and matched to classviz's width.
State is still read back from the button text, as in the other two apps — left alone
deliberately, since making this app the odd one out is worse than the idiom. New alert line
under the port field carries firmware complaints (`Command Input ERROR: …`, `LOCKOUT: …`),
which the app previously dropped on the floor: the status bar is rewritten ~20×/s by the `*`
stream, so an error posted there is invisible.

**4. Raw-voltage progress bar replaced with pack + board-temperature gauges.** The old
vertical `dialV` bar duplicated the Current readout beside it, at 50 px of width. In its place,
consuming firmware v4.28's new telemetry: a **battery-icon gauge** — fill and centre text are
state of charge, caption is the measured pack voltage and which DESIGN §12 *data-quality* zone
it sits in (≥24.0 above the ceiling / 23.3–24.0 transition / 21.5–23.3 clean window / below
that out of window / ≤21.0 lockout floor), with the clean window's lower edge drawn as a dashed
tick — and a plain **board-temperature bar**. Fed by the unsolicited `P` line plus a 10 s `V`
poll, because the firmware re-samples both channels at 1 Hz but only reports `P` every 60 s,
and `V`'s trailing fields also carry the lockout flag. A latched lockout turns the gauge red,
stops the run, and prints the firmware's own line in the alert row.

SoC comes from the same nominal ICR18650-26C curve as `utilities/pack_discharge/packv.py`,
copied rather than imported (nothing in `src/` depends on `utilities/`, DESIGN §15). It is
applied to the **loaded** voltage with no correction, so it reads a few percent low while
pulsing (~0.29 V at the terminals, §12) — an indicator, not the calibrated runway number, and
commented as such. The temperature scale is the firmware's **placeholder** linear mapping,
so the gauge is deliberately single-colour with no threshold bands: inventing green/amber/red
limits on an uncalibrated placeholder would read as measurement.

**5. Pulse and sample delay reach the profile maxima.** Ranges were 5–40 µs pulse and 5–30 µs
delay (sliders) against 5–100 µs (typed entry), which cannot reach the cells the current
profiles actually sweep. Now **4–150 µs pulse / 4–250 µs delay**, taken from
`cal_110_full_range_v4.json` (pulse 4.0–150.0, delays 4.288–250.0), so Mode 1 can sit on any
cell Mode 2 visits. Whether a given pair is *legal* depends on frequency — the firmware
rejects any config where `pulse + delay + 0.904 µs` does not fit inside one period
(`pulse_duties_valid()`) — and that limit is now reachable at the low-frequency bands, so a new
readout under the sliders shows drive duty and `pulse+delay` against the period, turning red
before the board has to say no. The 8 ns-grid orange highlights are unchanged, and the ±10-count
(80 ns) coarse keys are deliberately left as they were: direct entry is the way across a
250 µs range, and re-tuning muscle memory was not part of the ask.

**Session logs move to `data/sessions/`.** Was `data/P<DDMM-HHMMSS>.csv`, opened in
`my_init()` — so merely *starting* the app left an empty CSV beside the settings files
(three were sitting there, two of them zero bytes). Now `data/sessions/gui_<ts>.csv` opened on
**Start**, alongside every other session dump in this project, line-buffered, with a three-line
`#` header (app version, `session_start_iso`, column names) and `# sensor:` lines interleaved as
pack/temp telemetry arrives — so a Mode 1 dump can be correlated against pack state after the
fact, which is exactly what §17.13 needed and did not have. The filename QLineEdit is replaced
by a label; nothing reads these files, so the added header breaks no consumer. Path is now
absolute (script-relative), not `'data/…'` against the process cwd.

**6. Current readout to µV, and the alert row now clears itself.** Two bench annoyances found
on the first real run. The Current readout formatted a µV integer as `{:9,.0f} mV`, throwing
away the whole sub-mV part — the part being measured; now `{:9,.3f}`, i.e. the full resolution
the `*` record already carries (minimum width 120 → 150 px so the column does not reflow when
the first packet lands). And the new alert row only ever *wrote*: the single clear was on a
successful Connect, so `Command Input ERROR: rejected pulse config (drive_duty=78748,
sample_duty=135161)` sat under the Session row for the rest of the session, while the board ran
happily on a later, valid config. A firmware complaint is about the config that was live when
it was sent, so it now retires when that stops being true: non-sticky alerts self-clear after
`ALERT_CLEAR_MS` (10 s, single-shot `QTimer`), and `change_parameters()` clears before sending
a new `*` — a still-bad config re-alerts within one serial round trip. A latched **LOCKOUT** is
posted `sticky=True` and is exempt from both, since it is a standing condition, not an event:
it goes only on a reconnect or when a `V` reply reports the latch dropped. (2026-08-05)

Verified offscreen against synthetic `*`/`R`/`P`/`V`/`LOCKOUT` lines: layout renders, gauges
track, session file lands in `data/sessions/` with the expected content, the period-fit readout
flips red at 25 kHz / 150 µs / 250 µs and back to a 30.0 % duty at 2 kHz. **Not yet run against
the board** — firmware v4.28's own sensor path is itself still bench-unverified. (2026-08-04)

---

### mcu/pimd_mcu.py — v4.28 — pack-voltage + board-temp sense (ADC), 'P' telemetry, hard-latched low-voltage failsafe

Motivated directly by an incident: the rig was left running unattended and two 18650 cells
over-discharged past recovery, because there is no voltage-sense hardware on the board and no
firmware concept of pack state at all (DESIGN §12: "no divider, no thermistor, no NTC;
GP26-29 appear only as symbol pins"). Schematic sheet 2
(`References/images/schematic-v604-sheet2.jpg`) shows all four RP2040 ADC-capable pins
(GP26-29) already wired to onboard 10k pots (`POT-0`..`POT-3`) for bench bring-up, unused by
this firmware until now — which lets the whole path below be exercised on the bench without a
real pack divider or thermistor circuit.

New `machine.ADC` reads on GP26 (pack voltage, `POT-0`) and GP27 (board temperature, `POT-1`);
GP28/29 (`POT-2`/`POT-3`) are the spare fallback pins if GP26/27 turn out to carry something
else on the real board (flagged for a schematic-sheet-1 check before flashing). Both channels
are 64x-oversampled and serviced together at 1 Hz by a new `service_sensors()`, reusing the
exact `ticks_ms()`/`ticks_diff()` idiom `acquire_mode2()` already used for
`MIN_EMIT_MS`/`COMMAND_POLL_MS` — no new scheduler. `service_sensors()` is called from both the
main loop and from inside `acquire_mode2`'s own `i==0` block, because the main loop's call
doesn't run while control sits inside `acquire_mode2`'s internal `while` for the duration of a
Mode 2 sweep. Every 60 s it emits a new unsolicited, additive telemetry line —
`P<time_ms>,<pack_mV>,<board_temp_dC>` (board_temp_dC is deci-°C, x10 integer, matching the
project's no-floats wire convention) — a prefix no PC tool currently checks for, the same
property that made the `B` line (v4.11/v4.27) safe to add: `pimd_gui.py`, `pimd_classviz.py`,
`pimd_delaycal.py` and `pimd_rawlog.py` all dispatch on `line[0]`/prefix with no catch-all
`else`, so this breaks no consumer. `V` also gains three additive trailing fields
(`pack_mV`, `board_temp_dC`, `lockout`) for the same reason — confirmed nothing in `src/`
splits `V` by field count.

**Low-voltage failsafe**, the higher-priority half: at the 21.0 V floor DESIGN §12 already
documents as the working discharge limit (`PACK_VOLTAGE_TRIP_MV = 21_000`), three consecutive
1 Hz debounced readings latch `pack_voltage_lockout` — forces `state = 'stop'`, calls the
existing `set_safe_state()`, and permanently rejects `S`/`G`/`D` until a physical power-cycle
clears the RAM-only flag. **Deliberately a hard latch, not an auto-resume or a soft re-arm
command** — an automatic resume would repeat exactly the failure mode that damaged the cells
(voltage creeps back up under no load once pulsing stops, a resume reloads the pack, it sags
again). A new `pack_voltage_boot_check()` runs before `'Ready'` is even printed, so a rig
powered on already below the floor never fires a single pulse. `A<n>` is deliberately left
unblocked — verified by reading `acquire_raw_average()`: it never calls `duty_u16()` on either
PWM, only reads at whatever duty `set_safe_state()` already zeroed, so it cannot re-arm the
coil even though the command stays callable.

Both ADC-to-physical mappings (`PACK_VOLTAGE_FULLSCALE_MV = 25_000`,
`THERM_TEMP_FULLSCALE_DECIC = 1500`) are **placeholder linear scales** — the real analog front
ends (pack divider, thermistor conditioning) don't exist yet; 0-3.3V↔0-25V and 0-3.3V↔0-150°C
are the design target as specified by the operator. Flagged explicitly rather than glossed
over: a raw NTC thermistor+divider is **not** linear in temperature (Beta/Steinhart-Hart
curve) — if that ends up being the chosen part, this linear placeholder needs replacing with
the correct curve or a lookup table, not just re-tuning the constant.

Scope deliberately excludes any PC-tool change in this pass; `pimd_rawlog.py` already logs
every raw serial line verbatim regardless of prefix, so it verifies the new `P` line with zero
PC-side code changes. **Not yet verified live** — needs the bench pass in the implementation
plan's checklist: a `POT-0`/`POT-1` sweep smoke test via `pimd_rawlog.py`, then trip/boot/
recovery tests using `POT-0` in place of a real pack. (2026-08-04)

---

### src/pimd_rawlog.py — v1.14 — settings persistence, matching the other PC apps

`pimd_rawlog.py` was the only PC app without settings persistence — port, target/distance,
settle window/threshold, warm-up target, and window geometry all reset to defaults on every
launch. Added `_load_settings`/`_save_settings` following the same JSON-file pattern as
`pimd_gui.py`, `pimd_delaycal.py`, `pimd_classviz.py`, and `pimd_classify.py` (each app owns its
own settings file — `data/rawlog_settings.json` here — not a shared one), loaded at the end of
`__init__` and saved from `closeEvent`. The loaded profile itself is not persisted, consistent
with the other apps (a profile is re-selected via Load Profile / Resume Session each run, not
auto-restored). (2026-08-04)

---

### src/pimd_classify.py — v1.3 — Heatmap rows now match the standard grid orientation

`_band_display_order` sorted bands by first delay value **descending**, and with
`invertY(True)` on `heat_plot` that put the longest-pulse/longest-delay band at the top of the
heatmap and the shortest at the bottom — the opposite of this project's standard grid
orientation (declared in `pimd_rawlog.py`'s header, CHANGELOG v1.13: shortest pulse/delay
top-left, longest bottom-right). Flipped the sort to ascending so this file's heatmap now
agrees with `pimd_rawlog.py`'s raw-value grid and `pimd_classviz.py`'s tables/heatmaps. Found
while auditing `pimd_classviz.py` for the same bug (below) and confirming cross-app
consistency, at the user's request. (2026-08-04)

---

### src/pimd_classviz.py — v1.70 — Main/Analysis heatmap rows now match the standard grid orientation

Same bug as `pimd_classify.py` v1.3 above: `_band_display_order` sorted bands by first delay
value **descending**, so with `invertY(True)` the Main Heatmap and Analysis Heatmap tabs (which
both reindex by this array) showed the longest-pulse/longest-delay band at the top and the
shortest at the bottom — inconsistent with `pimd_rawlog.py`'s declared standard grid
orientation (v1.13: shortest pulse/delay top-left, longest bottom-right) and with this file's
own Stats table, which already derived an ascending (correct) order from the same data via
`reversed(_band_display_order)`. Flipped `_band_display_order` to sort ascending and stopped
deriving `_band_stats_order` by reversing it — both are now the same ascending order, so the
Stats table's already-correct row order is unaffected. Verified against the profile actually in
use, `cal_110_full_range_v4.json`: its bands list `pulse_us` and `delays_us[0]` both ascending
together, so ascending-by-delay is a valid pulse-width proxy for this profile. (2026-08-04)

---

### src/pimd_delaycal.py — v1.45 — Std dev table Colour lo/hi: lo spinbox floor -999 mV (was 0)

The "Colour lo/hi" pair that drives Absolute-mode colouring on the bottom (Std dev / metric)
table shares its lo/hi spinboxes across every metric in the selector, including "Mean level" —
the one metric that isn't a spread measure but the cell's raw signed mean reading (v1.44 gave it
a diverging green/red-by-sign scale). `sp_stddev_lo_mv` was still floored at 0.0 mV from when
every metric was an unsigned spread, so a negative mean reading clipped straight to the lo end
(t=0) regardless of how far negative it actually was, losing all resolution below zero. Lowered
the floor to -999.0 mV (matching the existing ±999 span used elsewhere for these spinboxes); the
hi spinbox's floor is unchanged. (2026-08-04)

---

### .claude/settings.json — config — worktree.bgIsolation set to "none"

Background-job (bg-agent) sessions were auto-isolating every edit into a fresh git worktree,
branched from `origin/main` by default. That's what produced the multi-worktree tangle cleaned
up the same day: `main`, `worktree-move-jpg-images` and `worktree-rawlog-instrument` all
diverging independently, one of them (`worktree-rawlog-instrument`) accumulating zero real
commits while unrelated work landed straight in `main`'s working tree instead. No git config or
prior settings entry actually controlled this — a CLAUDE.md line added in an earlier session
("we prefer to only work in one branch at a time") read as a fix but had no mechanism behind it;
it's been reverted.

Setting `worktree.bgIsolation: "none"` in `.claude/settings.json` makes background jobs edit the
shared checkout directly, like a normal foreground session — no more auto-created worktrees to
merge back and clean up. Trade-off: the isolation that stopped a background job and concurrent
foreground work from touching `main` at the same time is now off. `.claude/` is itself gitignored
in this repo, so this entry is the only record of the change; the setting takes effect purely by
the file existing on disk. (2026-08-04)

---

### DESIGN.md — 1.13.1 — post-consolidation corrections (§18)

Human-directed, read-only rule suspended per §18. **Not a consolidation and no new bench data** —
this folds in the four entries below, all of which are same-day desk work on defects 1.13 had
itself recorded as *known but not fixed*. Doc-rev 1.13.1 rather than 1.14, matching the 1.9.1 /
1.8.1 precedent for a correction pass.

**Why it was needed immediately rather than at the next §18.** 1.13 shipped three statements that
the same day's code changes made false — §14.12 "recorded there and not fixed", and two §15 rows
carrying "Known defect … not fixed". A curated snapshot that describes fixed defects as open is
worse than one that lags, because a reader has no way to tell which claims are stale.

**Sections changed.** Header → versions classviz **v1.69**, delaycal **v1.30**, features **v14**;
Doc-rev 1.13.1, keeping 1.13's summary as a one-line `Previous:` tail rather than a chain.
**§14.12** rewritten from an open problem to a resolved one, carrying the measured before/after
(61 of 4 079 windows now refused on the 07-29 stall dump; worst case 101 s / 14× nominal, from
which the old path drew 1 716 µV of drift as noise; the glitch half verified by injection at
334× → 1.00× because all 12 dumps hold **zero** mid-run glitch frames). **§15** classviz,
features and delaycal rows carry the fixes and both "Known defect" notes are gone. **§17.15**'s
closing line updated — the change it called for was made.

**New §14.15 — both offline acceptance gates fail on the current corpus, and neither failure is a
regression.** This is the one genuinely outstanding item and it needs an operator decision, so it
is recorded as an open problem rather than quietly fixed. `pimd_shape --selftest` reads FAIL (46)
against v3 and PASS against v1 because its expectations are hard-coded from the 2026-07-23
`cal_63_air_v2` analysis and **38 of the 46 are the crossing ladder**, which §17.14 has just shown
to be per-epoch — so §16's documented command has been wrong since the registry moved to v3.
Three fixes are possible and none is obviously right (point back at v1 / re-derive against v3 /
parameterise by epoch), and the trade-offs are recorded with it. `pimd_corpus_check`'s 411 checks
/ 229 FAIL is **not diagnosed** and is written as such — consistent in kind with §17.14's own
measurements, but not assumed to be them. **§16 carries a caveat on both commands** and its
selftest line now points at the v1 corpus, which is the only invocation that currently means
anything, until §14.15 is settled.

**Nothing dropped, no content removed.** (2026-07-31)

---

### findings — the documented `pimd_shape --selftest` command fails, and §17.14 says why

Found while regression-testing the v1.69/v1.30/v14 fixes, **pre-existing and unrelated to them**
(identical output with those changes stashed). Recorded, not fixed — the fix is a judgement call
about what the acceptance test is for.

`DESIGN §16` instructs:

```
python pimd_shape.py --selftest data/corpora/gui_signatures_targets_v3_20260728_142316.csv
```

That reads **FAIL (46 problems)**. Against the v1 corpus it reads **PASS**. The expectations are
hard-coded from the 2026-07-23 `cal_63_air_v2` analysis, and 38 of the 46 are item 3 — the
**crossing ladder**, which §17.14 has just established is a **per-epoch quantity**: under v3 every
interior crossing moves shorter by ×0.76 median, so `Fe_SS_disc_01 @60` reads 18.59 µs against a
hard-coded `30.6 ± 1.5`. The test is not detecting a regression; it is correctly reporting that
the corpus it was pointed at belongs to a different epoch from its expectations. Item 4's two
failures are the same story (`Fe_Cast_iron_trivet_01 @120` decay 1.15 — the §14.13 rogue capture)
and item 3 also names `Fe_SS_shackle_01` / `Fe_Zn_gal_pipe_01` captures now absent from the gated
set.

So §16's command has been wrong since the registry moved to v3: the selftest is an acceptance
check for the **feature maths**, and it can only serve that role against the corpus its
expectations were derived from. **Three options, none obviously right:** point §16 back at
`gui_signatures_targets_v1_20260723.csv` (honest, but the check then never exercises the current
epoch); re-derive the expectations against v3 (exercises the live epoch, but bakes in the rogue
capture unless it is excluded first); or make the expectations epoch-parameterised. Wants a
decision before the next capture day leans on it as a gate.

Separately and also pre-existing: `pimd_corpus_check` on the v3 corpus reads **411 checks:
181 PASS, 229 FAIL** — 101 `splithalf-snr`, 95 `repeat-consistency`, 24 `shape-invariance`,
9 `distance-falloff`. Not diagnosed here. Consistent in kind with §17.14's own measurements (the
SNR gate really being a reproducibility gate of ≈ 2.5–3.5, the §14.13 rogue capture, the §14.14
solder spool), but the count is high enough to want its own look rather than an assumption.
(2026-07-31)

---
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
