MarkMakies/PIMD/Electronics/PIMD604/PIMD604-Sheet2.kicad_sch

## KiCad design Electronics/PIMD604/PIMD604-Sheet2.kicad_sch (2026-06-16)

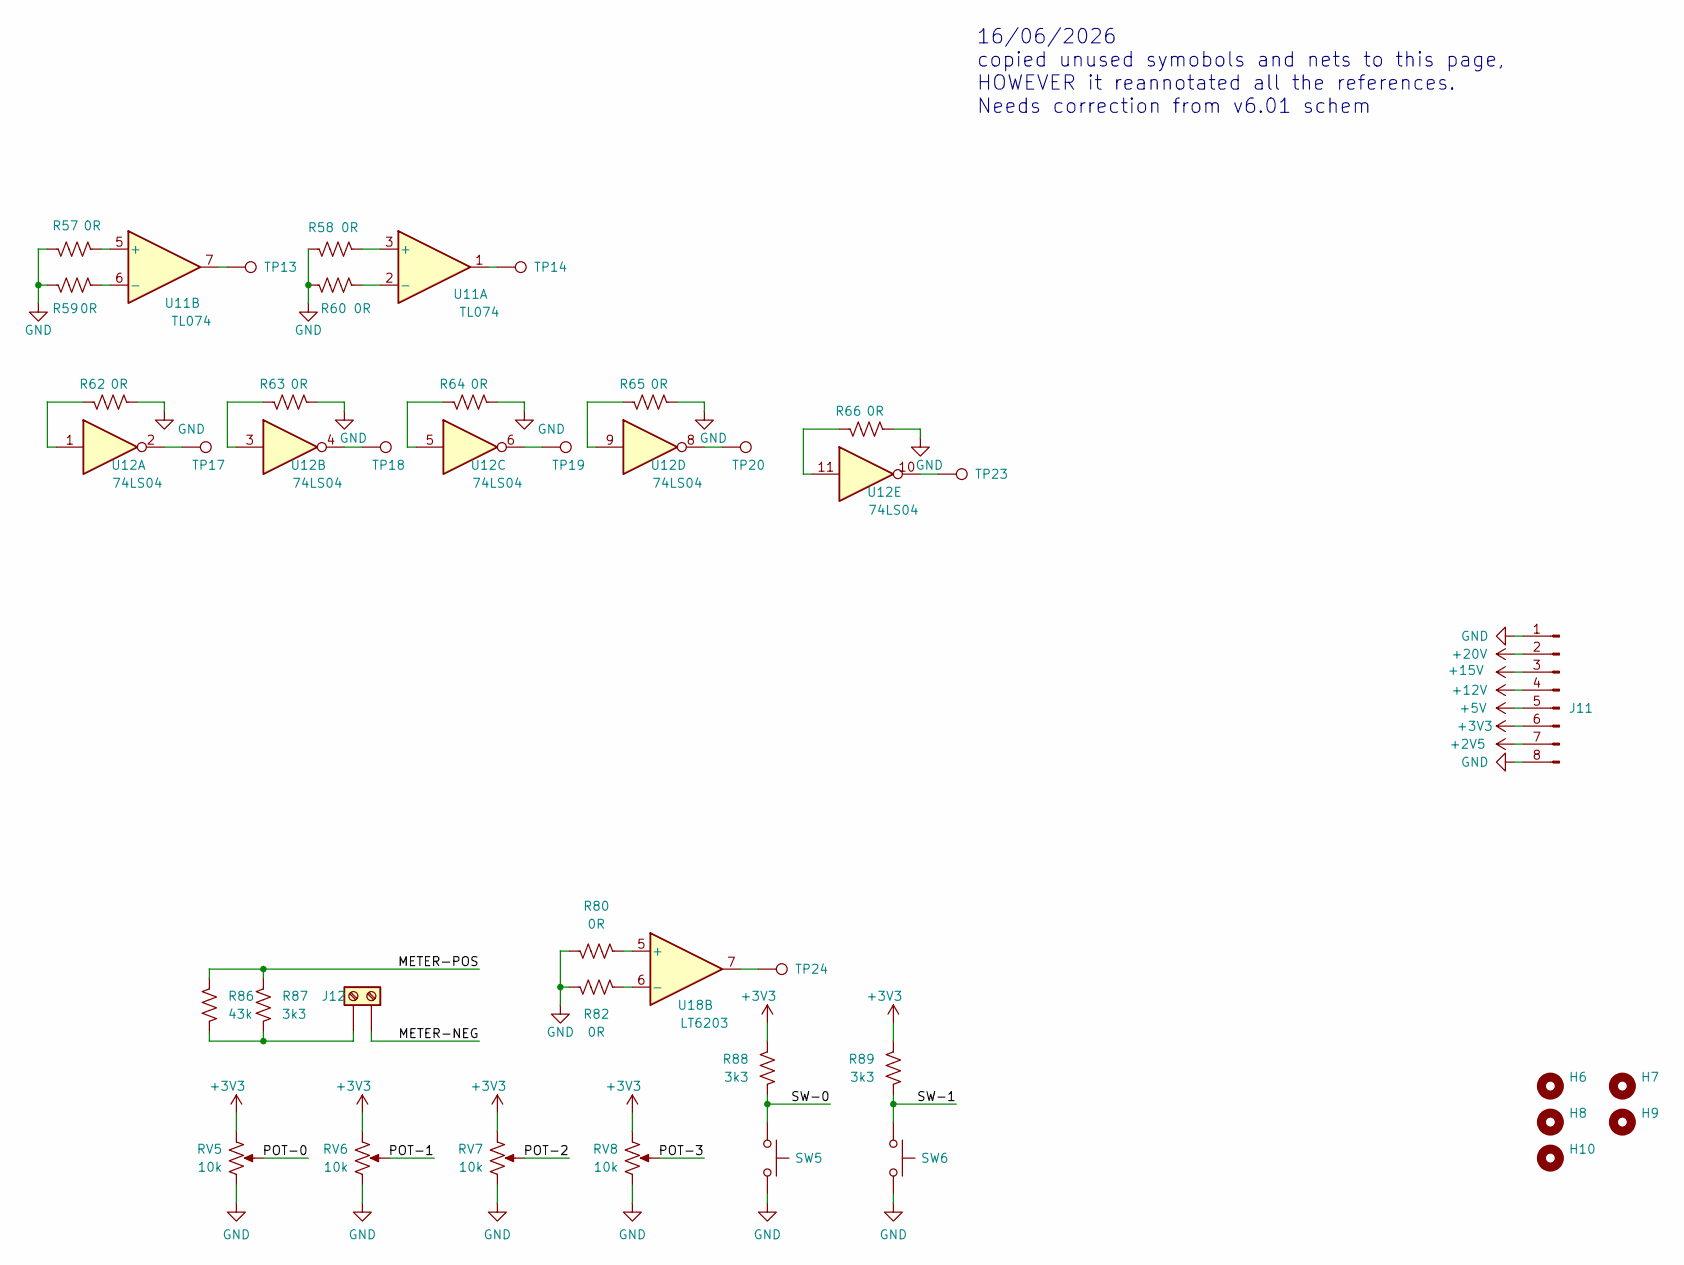
[picture p39: schematic PIMD604-Sheet2.kicad_sch]

Parts:
H6, H7, H8, H9, H10: MountingHole; MountingHole_3.2mm_M3
J11: Conn_01x08_Pin; PinHeader_1x08_P2.54mm_Vertical
J12: Screw_Terminal_01x02; TerminalBlock_bornier-2_P5.08mm
R57, R58, R59, R60, R62, R63, R64, R65, R66, R80, R82: 0R; Resistor
R86: 43k; Resistor
R87, R88, R89: 3k3; Resistor
RV5, RV6, RV7, RV8: 10k; Potentiometer_Alps_RK09L_Single_Vertical
SW5, SW6: SW_MEC_5G; SW_PUSH-12mm_Wuerth-430476085716
TP13, TP14, TP17, TP18, TP19, TP20, TP23, TP24: TestPoint; TestPoint_THTPad_1.5x1.5mm_Drill0.7mm
U11: TL074; DIP-14_W7.62mm
U12: 74LS04; DIP-14_W7.62mm
U18: LT6203; DIP-8_W7.62mm

Connections:
+2V5: J11.7
+3V3: J11.6, R88.2, R89.2, RV5.1, RV6.1, RV7.1, RV8.1
+5V: J11.5
+12V: J11.4
+15V: J11.3
+20V: J11.2
GND: J11.1, J11.8, R57.1, R58.1, R59.1, R60.1, R62.2, R63.2, R64.2, R65.2, R66.2, R80.1, R82.1, RV5.3, RV6.3, RV7.3, RV8.3, SW5.2 (B), SW6.2 (B)
METER-NEG: J12.1
METER-POS: R86.1, R87.1
unnamed: J12.2, R86.2, R87.2
unnamed: R57.2, U11.5 (+)
unnamed: R58.2, U11.3 (+)
unnamed: R59.2, U11.6 (-)
unnamed: R60.2, U11.2 (-)
unnamed: R62.1, U12.1
unnamed: R63.1, U12.3
unnamed: R64.1, U12.5
unnamed: R65.1, U12.9
unnamed: R66.1, U12.11
unnamed: R80.2, U18.5 (+)
unnamed: R82.2, U18.6 (-)
unnamed: TP13.1, U11.7
unnamed: TP14.1, U11.1
unnamed: TP17.1, U12.2
unnamed: TP18.1, U12.4
unnamed: TP19.1, U12.6
unnamed: TP20.1, U12.8
unnamed: TP23.1, U12.10
unnamed: TP24.1, U18.7
POT-0: RV5.2
POT-1: RV6.2
POT-2: RV7.2
POT-3: RV8.2
SW-0: R88.1, SW5.1 (A)
SW-1: R89.1, SW6.1 (A)

Notes on the sheet:
16/06/2026 copied unused symobols and nets to this page, HOWEVER it reannotated all the references. Needs correction from v6.01 schem
