MarkMakies/PIMD/Electronics/PIMD604/PIMD604.kicad_sch

## KiCad design Electronics/PIMD604/PIMD604.kicad_sch (2026-06-17)

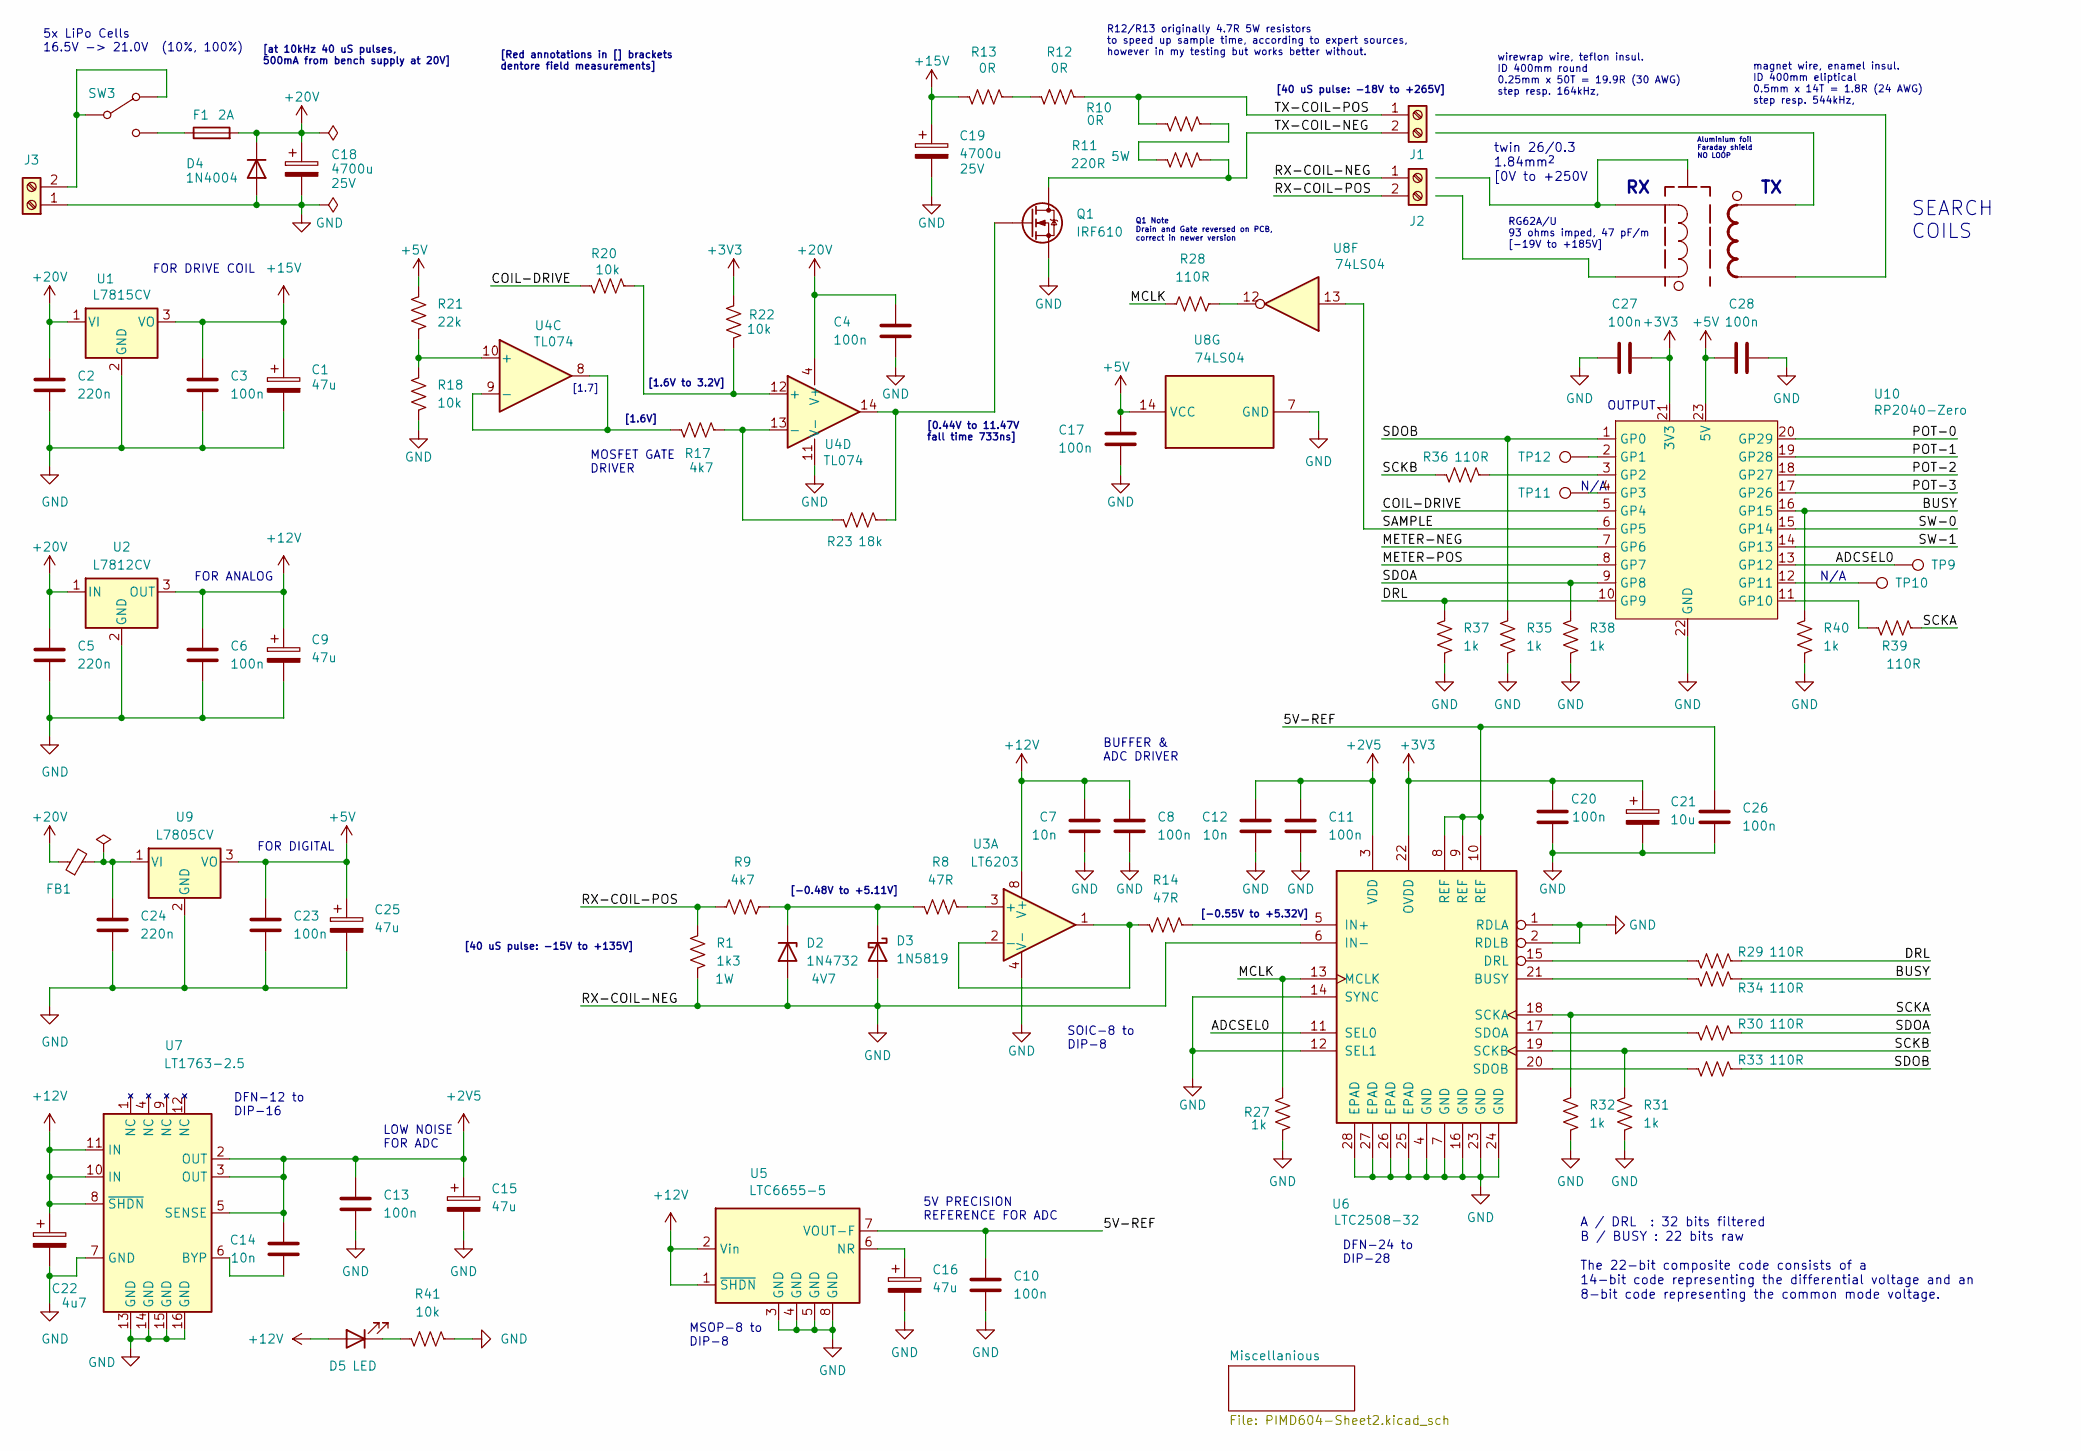
[picture p40: schematic PIMD604.kicad_sch]

Parts:
C1, C9, C15, C16, C25: 47u; C_Rect_L9.0mm_W3.6mm_P7.50mm_MKT
C2, C5, C24: 220n; C_Disc_D5.0mm_W2.5mm_P5.00mm
C3, C4, C6, C8, C10, C11, C13, C17, C20, C23, C26, C27, C28: 100n; C_Disc_D3.0mm_W2.0mm_P2.50mm
C7, C12, C14: 10n; C_Disc_D3.0mm_W2.0mm_P2.50mm
C18, C19: 4700u; CP_Radial_D16.0mm_P7.50mm
C21: 10u; CP_Radial_Tantal_D5.0mm_P2.50mm
C22: 4u7; C_Rect_L7.0mm_W3.5mm_P2.50mm_P5.00mm
COIL1: Transformer_1P_1S
D2: 1N4732; D_DO-41_SOD81_P10.16mm_Horizontal
D3: 1N5819; D_DO-41_SOD81_P10.16mm_Horizontal
D4: 1N4004; D_DO-41_SOD81_P12.70mm_Horizontal
D5: LED; LED_Rectangular_W5.0mm_H2.0mm
F1: 2A; Fuseholder_Littelfuse_100_series_5x30mm
FB1: FerriteBead_Small; L_Axial_L12.8mm_D5.8mm_P20.32mm_Horizontal_Fastron_HBCC
J1, J2, J3: Screw_Terminal_01x02; TerminalBlock_bornier-2_P5.08mm
J4: RFShield_OnePiece
Q1: IRF610; TO-220-3_Vertical
R1: 1k3; R_Axial_DIN0414_L11.9mm_D4.5mm_P20.32mm_Horizontal
R8, R14: 47R; Resistor
R9, R17: 4k7; Resistor
R10, R12, R13: 0R; R_Axial_DIN0922_L20.0mm_D9.0mm_P30.48mm_Horizontal
R11: 220R; R_Axial_DIN0922_L20.0mm_D9.0mm_P30.48mm_Horizontal
R18, R20, R22, R41: 10k; Resistor
R21: 22k; Resistor
R23: 18k; Resistor
R27, R31, R32, R35, R37, R38, R40: 1k; Resistor
R28, R29, R30, R33, R34, R36, R39: 110R; Resistor
SW3: SW_SPDT; SPDT
TP9, TP10, TP11, TP12: TestPoint; TestPoint_THTPad_1.5x1.5mm_Drill0.7mm
U1: L7815CV; TO-220-3_Vertical
U2: L7812CV; TO-220-3_Vertical
U3: LT6203; DIP-8_W7.62mm
U4: TL074; DIP-14_W7.62mm
U5: LTC6655-5; DIP-8_W10.16mm
U6: LTC2508-32; DIP-28_W15.24mm
U7: LT1763-2.5; DIP-16_W10.16mm
U8: 74LS04; DIP-14_W7.62mm
U9: L7805CV; TO-220-3_Vertical
U10: RP2040-Zero; DIP-24_W10.16mm

Connections:
5V-REF: C10.2, C26.2, U5.7 (VOUT-F), U6.8 (REF), U6.9 (REF), U6.10 (REF)
+2V5: C11.2, C12.2, C13.1, C14.2, C15.1, U6.3 (VDD), U7.2 (OUT), U7.3 (OUT), U7.5 (SENSE)
+3V3: C20.2, C21.1, C27.1, R22.1, U6.22 (OVDD), U10.21 (3V3)
+5V: C17.1, C23.2, C25.1, C28.2, R21.1, U8.14 (VCC), U9.3 (VO), U10.23 (5V)
+12V: C6.2, C7.2, C8.2, C9.1, C22.1, D5.2 (A), U2.3 (OUT), U3.8 (V+), U5.1 (~SHDN), U5.2 (Vin), U7.8 (~SHDN), U7.10 (IN), U7.11 (IN)
+15V: C1.1, C3.2, C19.1, R13.1, U1.3 (VO)
+20V: C2.2, C4.1, C5.2, C18.1, D4.1 (K), F1.2, FB1.1, U1.1 (VI), U2.1 (IN), U4.4 (V+)
ADCSEL0: TP9.1, U6.11 (SEL0), U10.13 (GP12)
BUSY: R34.2, R40.1, U10.16 (GP15)
COIL-DRIVE: R20.1, U10.5 (GP4)
DRL: R29.2, R37.1, U10.10 (GP9)
GND: C1.2, C2.1, C3.1, C4.2, C5.1, C6.1, C7.1, C8.1, C9.2, C10.1, C11.1, C12.1, C13.2, C15.2, C16.2, C17.2, C18.2, C19.2, C20.1, C21.2, C22.2, C23.1, C24.1, C25.2, C26.1, C27.2, C28.1, D2.2 (A), D3.2 (A), D4.2 (A), J2.1, J3.1, Q1.3 (S), R1.2, R18.2, R27.2, R31.2, R32.2, R35.2, R37.2, R38.2, R40.2, R41.2, U1.2 (GND), U2.2 (GND), U3.4 (V-), U4.11 (V-), U5.3 (GND), U5.4 (GND), U5.5 (GND), U5.8 (GND), U6.1 (RDLA), U6.2 (RDLB), U6.4 (GND), U6.6 (IN-), U6.7 (GND), U6.12 (SEL1), U6.14 (SYNC), U6.16 (GND), U6.23 (GND), U6.24 (GND), U6.25 (EPAD), U6.26 (EPAD), U6.27 (EPAD), U6.28 (EPAD), U7.7 (GND), U7.13 (GND), U7.14 (GND), U7.15 (GND), U7.16 (GND), U8.7 (GND), U9.2 (GND), U10.22 (GND)
MCLK: R27.1, R28.2, U6.13 (MCLK)
METER-NEG: U10.7 (GP6)
METER-POS: U10.8 (GP7)
unnamed: C14.1, U7.6 (BYP)
unnamed: C16.1, U5.6 (NR)
unnamed: C24.2, FB1.2, U9.1 (VI)
unnamed: COIL1., J4.
unnamed: D2.1 (K), D3.1 (K), R8.1, R9.1
unnamed: D5.1 (K), R41.1
unnamed: F1.1, SW3.3 (C)
unnamed: J3.2, SW3.1 (A), SW3.2 (B)
unnamed: Q1.2 (G), R23.2, U4.14
unnamed: R8.2, U3.3 (+)
unnamed: R10.2, R11.1
unnamed: R12.1, R13.2
unnamed: R14.1, U3.1, U3.2 (-)
unnamed: R14.2, U6.5 (IN+)
unnamed: R17.1, U4.8, U4.9 (-)
unnamed: R17.2, R23.1, U4.13 (-)
unnamed: R18.1, R21.2, U4.10 (+)
unnamed: R20.2, R22.2, U4.12 (+)
unnamed: R28.1, U8.12
unnamed: R29.1, U6.15 (DRL)
unnamed: R30.1, U6.17 (SDOA)
unnamed: R33.1, U6.20 (SDOB)
unnamed: R34.1, U6.21 (BUSY)
unnamed: R36.2, U10.3 (GP2)
unnamed: R39.1, U10.11 (GP10)
unnamed: TP10.1, U10.12 (GP11)
unnamed: TP11.1, U10.4 (GP3)
unnamed: TP12.1, U10.2 (GP1)
POT-0: U10.20 (GP29)
POT-1: U10.19 (GP28)
POT-2: U10.18 (GP27)
POT-3: U10.17 (GP26)
RX-COIL-POS: J2.2, R1.1, R9.2
SAMPLE: U8.13, U10.6 (GP5)
SCKA: R32.1, R39.2, U6.18 (SCKA)
SCKB: R31.1, R36.1, U6.19 (SCKB)
SDOA: R30.2, R38.1, U10.9 (GP8)
SDOB: R33.2, R35.1, U10.1 (GP0)
SW-0: U10.15 (GP14)
SW-1: U10.14 (GP13)
TX-COIL-NEG: J1.2, Q1.1 (D), R11.2
TX-COIL-POS: J1.1, R10.1, R12.2

Notes on the sheet:
N/A
FOR DRIVE COIL
[0.44V to 11.47V fall time 733ns]
[1.6V to 3.2V]
[40 uS pulse: -15V to +135V]
MSOP-8 to DIP-8
[40 uS pulse: -18V to +265V]
5V PRECISION REFERENCE FOR ADC
FOR DIGITAL
[1.7]
DFN-24 to DIP-28
BUFFER & ADC DRIVER
Q1 Note Drain and Gate reversed on PCB, correct in newer version
OUTPUT
twin 26/0.3 1.84mm^{2} [0V to +250V
[-0.55V to +5.32V]
LOW NOISE FOR ADC
R12/R13 originally 4.7R 5W resistors to speed up sample time, according to expert sources, however in my testing but works better without.
wirewrap wire, teflon insul. ID 400mm round 0.25mm x 50T = 19.9R (30 AWG) step resp. 164kHz,
magnet wire, enamel insul. ID 400mm eliptical 0.5mm x 14T = 1.8R (24 AWG) step resp. 544kHz,
SOIC-8 to DIP-8
Aluminium foil Faraday shield NO LOOP
FOR ANALOG
MOSFET GATE DRIVER
RG62A/U 93 ohms imped, 47 pF/m [-19V to +185V]
[1.6V]
[Red annotations in [] brackets dentore field measurements]
DFN-12 to DIP-16
[at 10kHz 40 uS pulses, 500mA from bench supply at 20V]
SEARCH COILS
5x LiPo Cells 16.5V -> 21.0V (10%, 100%)
A / DRL : 32 bits filtered B / BUSY : 22 bits raw The 22-bit composite code consists of a 14-bit code representing the differential voltage and an 8-bit code representing the common mode voltage.
[-0.48V to +5.11V]
