MarkMakies/PIMD/src/pimd_classviz.py

# SPDX-License-Identifier: GPL-3.0-or-later
# Copyright (c) 2022-2026 Mark Makies
###############################################################################
# PIMD Signature Visualiser (ClassViz) v1.79
# — Mode 2 adaptive profile viewer
# Runs on Ubuntu desktop / laptop, standalone PyQt6 app (no .ui file)
#
# Connects to the board, sends Q4/G to start Mode 2 streaming with the default
# CLASSIFY_EP profile, and displays a heatmap of signed cell deviations from a
# captured air baseline. Signature-corpus capture lives on the Analysis tab
# (its Training group runs the automated auto-detect air/target/air cycle and
# writes the corpus CSV), alongside a top-bar saved-profile selector to load/send
# a band/pulse/delay profile to the board as a RAM-only "dynamic" profile
# (firmware D command) without reflashing — the heatmap/stats table resize to
# match whatever profile (static or dynamic) is active. Profile authoring/saving
# lives in pimd_delaycal.py; ClassViz only loads and runs.
#
# Protocol: receives W<profile_idx>,<time_ms>,<ch0>,...,<chN-1>
#           also P<time_ms>,<pack_mV>,<board_temp_dC>   — unsolicited, ~60 s
#           and   V<fw>,<board>,…,<pack_mV>,<board_temp_dC>,<lockout>
# Board firmware: pimd_mcu.py v4.23+ (sensor fields need v4.28+, real board
#           temperature v4.33+; board_temp_dC = -32768 means NO READING)
#
# History (full detail in CHANGELOG.md):
#   v1.79 warm-up countdown beside the temperature gauge; temp gauge goes
#         yellow at 50 °C / red at 60 °C; Analysis main + right splits persist
#   v1.78 FIX '# capture:' lines never carried their tgt/air window spans --
#         the raw slots were already cleared when Save ran
#   v1.77 captures record temp_c / streamed_s / stalled_s; readout warns while
#         the board is inside the warm-up transient
#   v1.76 Band Mean vs Time can split into early (blue) / late (red) cell
#         groups at a selectable sd index
#   v1.75 pack gauge reads runtime-fraction SoC + live H:MM remaining from the
#         shared pimd_pack.py; the data-quality zone captions are retired
#   v1.74 FIX Load & Run never armed the soak/stall run state -- every soak line
#         it produced read streamed_s=0 and no periodic lines were written at all
#   v1.73 ADC-rail marking on clipped cells; Load & Run holds Q/G until the
#         firmware acknowledges the D
#   v1.72 pack voltage and board temperature come from firmware telemetry, on
#         pimd_gui's gauges; the Pack V / Log V hand-entry controls are gone and
#         the session dump's '# pack_v:' track is written automatically
#   v1.71 FIX heatmap band order keyed on pulse_us, not the delays_us[0] proxy
#   v1.70 FIX Main/Analysis heatmap rows sorted delay-descending (longest at
#         top) instead of ascending -- now matches the standard grid
#         orientation (shortest pulse/delay top-left, longest bottom-right)
#   v1.69 FIX both Std Dev displays bypassed the glitch filter and the stall guard
#   v1.68 saving a signature marks the session dump; new '# capture:' frame-window join key
#   v1.67 Tilt (°) capture input for oblique poses; tilt_deg joins the placement tuple
#   v1.66 session dump: pack_v carries age_s; new '# soak:' run/idle history lines
#   v1.65 FIX corpus append wrote the tool's columns, not the file's (ragged CSV)
#   v1.64 window span guard; stream-stall detection; pack voltage; chart pause
#   v1.63 session logging auto-starts with the stream; Session Start adopts a running log
#   v1.62 FIX repeat_idx stuck at r1 (re-suggest after reload; normalise the placement key)
#   v1.61 signature list rows carry long axis + repeat; colour is per target
#   v1.60 remove the face_normal / offset X / offset Y capture inputs (schema unchanged)
#   v1.57 show the central-frame count that survives the trim; Frames default 60 -> 100
#   v1.56 Training A/B labels name the gate holding each phase up (σ/Δ vs threshold)
#   v1.55 lift the v1.41 manual latch: Space-forced placements auto-detect removal too
#   v1.54 FIX removal auto-detect: transient + fresh target ref; Air age = cycle budget
#   v1.53 auto-connect + run the last profile at launch; gauge row spacing; np.bool_ warning
#   v1.52 FIX Detect gauge read a stale air reference; Air age gauge; readout under the label
#   v1.51 Analysis Trigger Levels gauges (Settle/Detect/Amp/SNR) with draggable thresholds
#   v1.50 below-gate frames leave no trail at all; the trail is green by construction
#   v1.49 FIX custom band pair lost on restart (clamped by the startup profile's narrower spin range)
#   v1.48 Family Plane: no gridlines on a rank axis; the zero rails follow the spacing curve
#   v1.47 Family Plane per-axis Scale combo (expand-ends / rank spacing; no log, it is backwards here)
#   v1.46 scratch saves plot immediately (own template source) and draw as triangles
#   v1.45 FIX heatmap colorbar handles now mark Min/Max; live shape cursor/trail green above SNR gate
#   v1.44 Analysis heatmap manual scale is an explicit Min/Max; signature dialogs remember their directory
#   v1.43 Shape Space renamed Family Plane Analysis; material tags, per-axis custom bands, ladder click
#   v1.42 new Shape Space tab (feature-space scatter + docks) + scratch captures
#   v1.41 FIX Space-forced target placement skipped the removal wait (auto-detect latch)
#   v1.40 FIX capture_id reuse after a delete silently merged later saves into an existing capture
#   v1.39 remove the Training Session tab (all capture now via the Analysis tab Training group)
#   v1.38 Analysis: shrinkable heatmap split, auto-check new sigs, black live traces, quality colouring
#   v1.37 FIX Load signatures / Open for editing rejected the app's own v1.32+ files (schema dispatch)
#   v1.36 persist Saved-profile / Saved-list selectors, Stats Std thresholds, Training settle window
#   v1.35 training status labels name air/target; place/remove countdown flashes (red <5 s) + beeps
#   v1.34 training auto-detect cycle (auto place/remove, 30 s countdowns, Save/Ignore, rolling air reuse)
#   v1.33 continuous training capture (Training group; space-bar air/target toggle; supply battery/psu)
#   v1.32 structured target-metadata capture regime (registry-backed Analysis/Training capture)
#   v1.31 Analysis-tab signature captures hardened to session-pipeline rigor (settle gate, glitch exclusion)
#   v1.30 normalize Auto mode subtracts group mean, not first element (noisy-reference-cell fix)
#   v1.29 Analysis heatmap ColorBarItem legend doubling as an interactive range control
#   v1.28 "Std Dev (rolling N)" heatmap display mode + top-bar Rate readout
#   v1.27 Analysis tab layout regrouping (left column + 3-row right side), cosmetic
#   v1.26 Analysis tab settings persistence + in-GUI signature file editor
#   v1.25 Analysis tab: single averaged Band-Mean strip; chart-2 controls; relayout
#   v1.24 Analysis tab: per-group Auto/Manual normalize+scale; bordered charts; Y-lock fix
#   v1.23 new Analysis tab: real-time comparison charts + corpus overlay
#   v1.22 Training Start clears live columns; notes auto-derived from run list
#   v1.21 new Training Session tab: guided target-list capture, Space step-advance
#   v1.20 removed Profile Builder tab; top-bar Saved-profile "Load & Run"
#   v1.19 session-recording mark hotkeys (1/2/3/0/Space) via app-wide eventFilter
#   v1.18 _save_profile_file JSON padded to 3 d.p. (_pad_json_floats)
#   v1.17 3-decimal precision for all voltage/timing fields
#   v1.16 "Record Frames" reworked into self-describing session-dump recorder
#   v1.15 Stats Std column green/yellow/red thresholds; row-height +/- controls
#   v1.14 Stats/Profile tables sorted ascending by first delay
#   v1.13 remove single-cell isolation mode
#   v1.12 heatmap rows in descending delay order regardless of stream order
#   v1.11 settings persistence (port/capture/rolling/display/geometry/...)
#   v1.10 Mode 1 '*' command updated to MCU v4.23 protocol (Hz/ns)
#   v1.09 band labels + Stats delay to 3 d.p. (8 ns grid)
#   v1.08 Stats std-dev window sample-count based (was seconds)
#   v1.07 process_packet: 64-frame median glitch filter on display path
#   v1.06 Stats "Record Frames" toggle (raw W-frame CSV)
#   v1.05 fix _fmt(): no thousands-separator in saved CSV
#   v1.04 per-instance profile dims; Profile Builder tab; D-command dynamic profile
#   v1.03 Stats "Save table as CSV"
#   v1.02 Resume Sweep auto-sends G
#   v1.01 add Stats tab (per-cell value/mean/std) + single-cell isolation
#   v1.00 initial version: heatmap + baseline + labelled CSV logger + 3D surface
###############################################################################

# pyright: reportOptionalMemberAccess=false
# pyright: reportAttributeAccessIssue=false

import csv
import io
import json
import math
import os
import sys
import time
import zlib
from datetime import datetime, date, timedelta
from collections import Counter, deque

import numpy as np

os.environ.setdefault('QT_API', 'pyqt6')

from PyQt6.QtCore import QEvent, QIODevice, QPointF, QRectF, QTimer, Qt  # noqa: E402
from PyQt6.QtGui import (  # noqa: E402
    QBrush, QColor, QFont, QImage, QPainter, QPen, QPixmap,
)
from PyQt6.QtSerialPort import QSerialPort  # noqa: E402
from PyQt6.QtWidgets import (  # noqa: E402
    QAbstractSpinBox, QApplication, QCheckBox, QComboBox, QDialog, QDialogButtonBox,
    QDoubleSpinBox,
    QFileDialog, QFormLayout, QGroupBox, QHBoxLayout, QHeaderView, QInputDialog, QLabel,
    QLineEdit, QListWidget, QListWidgetItem, QMainWindow, QMessageBox,
    QPushButton, QSpinBox, QSplitter, QStackedWidget, QTabWidget,
    QTableWidget, QTableWidgetItem, QVBoxLayout, QWidget,
)

import pyqtgraph as pg  # noqa: E402
from pyqtgraph.dockarea import Dock, DockArea  # noqa: E402 — Shape Space tab layout

try:
    import pyqtgraph.opengl as gl
    _GL_AVAILABLE = True
except ImportError:
    _GL_AVAILABLE = False

import pimd_corpus_check  # noqa: E402 — Analysis tab signature-overlay loader
import pimd_features       # noqa: E402 — Analysis tab signature capture/save
import pimd_pack           # noqa: E402 — pack SoC / time-remaining maths (no Qt in that module)
import pimd_shape          # noqa: E402 — Shape Space tab feature maths (no Qt in that module)
import pimd_target_check        # noqa: E402 — target registry, shared with pimd_features

APP_VERSION = '1.79'

REDRAW_MS   = 33    # ~30 Hz

# Band Mean vs Time split colours (v1.76): early cells blue, late cells red.
# Fixed, not per-target -- this strip's two curves are the SAME quantity over
# two halves of the delay ladder, so the pair has to read as one axis, and the
# colours are named in the legend under the chart.
STRIP_EARLY_COLOR = (26, 95, 208)    # blue  — early cells (polarity zone)
STRIP_LATE_COLOR  = (200, 32, 32)    # red   — late cells (decay-rate zone)

# How long to wait for the firmware's response to a D (dynamic profile) command
# before giving up and refusing to start the stream (v1.73). The firmware always
# answers -- 'D OK' or a 'Command Input ERROR' -- so this only fires on a dropped
# line or a board that is not listening. Generous: D is a long line at 115200 and
# the board may be finishing a sweep before it polls stdin.
D_ACK_TIMEOUT_MS = 3000

# Raw Mode 2 samples are signed 14-bit, so a cell that reaches +8191 / -8192 is
# CLIPPED and its reported value is a limit, not a measurement (DESIGN §9's µV
# scaling: raw14 * 10_000_000 / 2**14). Firmware sends no clip flag, so the rail
# is detected here, from the value itself. Positive FS lands on 4999389 µV; the
# tolerance covers the firmware's rolling average pulling the mean a code or two
# below FS while individual samples are still pinned there.
RAIL_POS_UV  = (2 ** 13 - 1) * 10_000_000 // 2 ** 14   # +4999389
RAIL_NEG_UV  = -(2 ** 13) * 10_000_000 // 2 ** 14      # -5000000
RAIL_TOL_UV  = 2 * 10_000_000 / 2 ** 14                # 2 raw14 codes ≈ 1.2 mV

# Gap between the auto-start connect and the profile send, so the board has
# answered the E/V/Q4 handshake before the D/Q/G burst arrives -- the same beat
# an operator leaves between clicking Connect and Load & Run.
AUTOSTART_PROFILE_MS = 600

# Assumed seconds per W-frame when no measured rate is available yet (the
# _fps_hz readout needs a second of streaming first). ~3.3 Hz is the 63-cell
# sweep -- the same figure behind "a 50-frame window is 15 s at the sweep rate".
SWEEP_PERIOD_FALLBACK_S = 0.3

# Smallest Training "Frames" value whose central 60% still clears
# MIN_CENTRAL_FRAMES, so a full window is not stamped 'short' by
# quality_flags(). pimd_features trims 20% off each end of every plateau
# (CENTRAL_FRACTION) before taking stats, so only 60 of 100 frames feed them.
# This used to default to MIN_CENTRAL_FRAMES itself -- 60 frames, trimmed to 36
# central, which is BELOW the 60 the flag tests against, so a default-Frames
# capture was stamped 'short' every time (v1.57). Same expression the Family
# Plane scratch capture has sized its window with since v1.46.
SIG_CAPTURE_N_DEFAULT = int(math.ceil(
    pimd_features.MIN_CENTRAL_FRAMES / pimd_features.CENTRAL_FRACTION))   # 100

# -- Analysis heatmap colorbar-as-range-slider (v1.45) ----------------------
# ColorBarItem's internal coordinate space is a fixed 0..256 across the bar,
# independent of the levels on its axis.
CBAR_SPAN = 256.0
# The bar's axis shows a *domain* wider than the Min/Max window, so the handles
# have room to travel outwards as well as in. The domain is the union of the
# window and the data actually on screen -- but never so wide that the window
# shrinks below this fraction of the bar, or a tight window on a wide-ranging
# field (Δ mode reaches ~500000 µV) becomes an unreadable sliver.
CBAR_MIN_WINDOW_FRAC = 0.5
# ...and never so narrow that the handles end up pinned on the bar's two ends
# with nowhere to be dragged outwards to, which is what happens whenever the
# window already contains all the data.
CBAR_MAX_WINDOW_FRAC = 0.9

DEFAULT_PROFILE_IDX   = 4   # static CLASSIFY_EP — sent automatically on connect
DYNAMIC_PROFILE_INDEX = 5   # must match firmware's NUM_PROFILES (pimd_mcu.py v4.07+)

CAPTURE_FRAMES_DEFAULT = 64
ROLLING_SECS_DEFAULT   = 3.0
DEFAULT_PORT = '/dev/ttyACM0'

PROFILES_DIR       = os.path.join(os.path.dirname(os.path.abspath(__file__)), 'data', 'profiles')
SESSIONS_DIR       = os.path.join(os.path.dirname(os.path.abspath(__file__)), 'data', 'sessions')
CORPORA_DIR        = os.path.join(os.path.dirname(os.path.abspath(__file__)), 'data', 'corpora')
# Shape Space scratch captures -- deliberately NOT data/corpora/: those ids are
# unregistered, and pimd_features' corpus build hard-errors on an unknown
# target_id. That guard is intentional; a scratch object gets promoted by
# registering it in targets_v1.csv and recapturing it properly.
SCRATCH_DIR        = os.path.join(os.path.dirname(os.path.abspath(__file__)), 'data', 'scratch')
TARGETS_REGISTRY_PATH = pimd_target_check.DEFAULT_REGISTRY_PATH   # single source of truth
SUPPLY_CHOICES = ['battery', 'psu']
SCRATCH_ID_PREFIX = 'scratch_'
SCRATCH_MEDIA = ['air', 'soil', 'sand', 'water', 'other']

# -- Family Plane Analysis tab ---------------------------------------------
# Tab name (v1.43; was "Shape Space"). Held as a constant because it prefixes
# every status-bar line this tab emits.
SHAPE_TAB_TITLE = 'Family Plane Analysis'
# (key, menu label). 'custom' reads the control bar's band-range spin pair
# for that axis (X and Y have their own pair, so custom-vs-custom is a real
# plane and not the identity diagonal); everything else is a fixed pimd_shape
# feature. Used for both axis combos and, with SHAPE_COLOUR_EXTRA appended,
# the Colour-by combo.
SHAPE_AXES = [
    ('early',    'early mean'),
    ('mid',      'mid mean'),
    ('late',     'late mean'),
    ('custom',   'custom band range'),
    ('crossing', 'crossing µs (log)'),
    ('decay',    'decay persistence'),
    ('log_amp',  'log₁₀ amplitude'),
]
SHAPE_COLOUR_EXTRA = [('family', 'family'), ('distance', 'distance'), ('none', 'none')]
# Per-axis spacing curves (v1.47). The family-plane axes are band-range means of
# a UNIT shape, so they are hard-bounded at +/- 1/sqrt(k * n_delays) -- +/-0.1925
# for 3 of 7 bands -- and the corpus reaches 83% of that ceiling. Both families
# therefore pile up against opposite walls with the family decision boundary as
# an empty band between them: on the 2026-07-23 corpus the middle 48% of the Y
# axis holds nothing while each cluster is squeezed into 8-31%.
#
# There is deliberately NO log option. Log expands near zero and compresses at
# the extremes, which is backwards here -- measured, it drives the dead middle
# from 48% to 85%. These curves expand near the ENDS instead (measured on the
# same corpus: cube 15% dead, atanh 14%, rank 2%).
SHAPE_SCALES = [
    ('linear', 'Linear'),
    ('cube',   'Expand ends (cube)'),
    ('atanh',  'Expand ends (atanh)'),
    ('rank',   'Rank'),
]
# atanh(0.999) -- the normaliser that keeps the 'atanh' curve inside [-1, 1].
SHAPE_ATANH_K = math.atanh(0.999)
# Axes whose values are pulse widths in µs -- plotted as log10 with the
# profile's own pulse ladder as ticks (see _shape_axis_ticks). pyqtgraph's
# PlotItem.setLogMode only transforms PlotDataItems, not the bare
# ScatterPlotItems this tab draws, so the log transform is done on the values.
SHAPE_LOG_US_AXES = ('crossing',)
# Axes that are signed band-range means of the unit shape, so 0 is the
# meaningful "no signal" origin. While the air reference is rolling the live
# dot is pinned there rather than drawn at its computed position: the residual
# is ~0 in magnitude but its unit shape still has a definite direction (the
# reference's half-window drift lag), which parks the dot at a consistent
# off-centre spot -- measured, right inside the non-ferrous cluster. On the
# other axes 0 is not the origin of anything, so the dot is hidden instead.
SHAPE_CENTRED_AXES = ('early', 'mid', 'late', 'custom')

SHAPE_FAMILY_COLOURS = {
    'non_ferrous':      '#1f77b4',
    'crossover':        '#9467bd',
    'ferrous':          '#d62728',
    pimd_shape.LOW_SNR: '#999999',
}

# material_class / plating_material -> short tag drawn beside a point. Chemical
# symbols where one exists, so the plane reads as chemistry rather than as
# registry strings; alloys get a 3-letter contraction. Keys are exactly the
# registry's material_class vocabulary (pimd_target_check.DENSITY_G_PER_CM3)
# plus the plating materials that appear only in plating_material/substrate.
# An unlisted material falls back to Title-cased first 3 letters — a new
# registry material shows up as a readable guess, not as '?'.
SHAPE_MATERIAL_ABBREV = {
    'aluminium':    'Al',
    'brass':        'Brs',
    'cast_iron':    'CI',
    'chrome':       'Cr',
    'copper':       'Cu',
    'cu_alloy':     'CuA',
    'ferrite':      'Frt',
    'gold':         'Au',
    'lead':         'Pb',
    'ndfeb':        'NdFe',
    'nickel':       'Ni',
    'silver':       'Ag',
    'solder_sn_pb': 'SnPb',
    'stainless':    'SS',
    'steel':        'Fe',
    'tin':          'Sn',
    'zinc':         'Zn',
}
# Above this many drawn captures the per-point material tags are suppressed:
# past ~200 the text is denser than the points it annotates and the plane
# becomes unreadable. The checkbox still reads checked -- the tags come back
# on their own once the drawn set shrinks (a gate change, a different file).
SHAPE_LABEL_MAX = 200
SHAPE_GATE_DEFAULT  = pimd_shape.DEFAULT_SNR_GATE
SHAPE_TRAIL_DEFAULT = 30
SHAPE_TRAIL_MAX     = 500   # deque cap; the spinbox slices the last N of it
# Air-reference age beyond which the gauge reads amber. Far shorter than a
# static baseline's 600 s would suggest: at the DESIGN §3 drift rate a 60 s-old
# locked reference has already accumulated ~1 mV/cell, the same order as a weak
# target, so a lock older than this is worth re-arming before trusting.
SHAPE_AIR_AMBER_S   = 60.0
# Effective soak (streamed - stalled) below which a capture is inside the
# warm-up transient and the readout says so. DESIGN §3: from cold the band-0
# mean settles as a single exponential, tau ~1.15/0.90 min, within 0.2 % at
# 5.6/3.8 min, and the guidance is "allow 6 min" on the 40 mm extractor.
#
# A WARNING, never a block: a deliberate cold-start study is a real experiment,
# and streamed_s/stalled_s go into the corpus row either way, so a capture
# taken early stays identifiable offline whatever the operator decides here.
# The DS18B20 cannot do this job -- §3 is explicit that it reaches its final
# reading well before the signal settles and "is not a readiness indicator".
WARMUP_SETTLE_S = 360.0
# Air-buffer frames. Deliberately much shorter than the Analysis tab's
# capture-window default (120): that window is for a stationary corpus capture
# bracketed by air on BOTH sides, where length buys noise. A rolling reference
# is single-ended, so its median sits half a window in the PAST and that lag is
# baked straight into every measurement as drift. Measured against a spanner @
# 60 mm on a drifting air simulation, family read correctly out to a 15 s hold
# at 20-40 frames and was already wrong at 5 s by 80-120 frames.
SHAPE_AIR_N_DEFAULT      = 40
# Live/settle window, frames. Much shorter than the Stats tab's 50: the settle
# metric only reads "settled" once the whole window sits inside one state, so a
# 50-frame window means a target does not register for a whole window — by which
# time drift has already spoiled the reading. The split-half noise floor over 15
# frames is still ~0.5 mV against a 39 mV target at 60 mm.
#   Sweep rate, measured (v1.64): 6.9 Hz under cal_63_air_bat_v3, so 50 frames is
#   ≈7.2 s and 15 frames ≈2.2 s. Earlier comments here quoted ~3.3 Hz / 15 s for
#   the 50-frame window; that was never re-measured after the profile changed and
#   is off by ~2×. Nothing derives timing from those numbers — they were prose —
#   but they are what made the frame-count window look time-bounded when it is not
#   (see _window_frames).
SHAPE_WIN_N_DEFAULT      = 15
# Span guard on every frame-count window (v1.64). A window of N frames is only a
# window of time if frames keep arriving; when the host stalls, N frames can span
# minutes and the per-channel σ over them reads accumulated DRIFT as noise. On
# 2026-07-29 23:03-23:50 a host stall (fw v4.27 now counts these MCU-side) made a
# 50-frame window span ~100 s instead of 7.2 s and inflated `settle` ~6×, which
# read on-screen as a noise relapse that did not happen. Any window spanning more
# than this multiple of its expected duration is refused rather than reduced, so a
# stall fails safe to "not settled" instead of to a plausible-looking number.
WINDOW_SPAN_TOLERANCE = 3.0
# Frames used to estimate the nominal frame period for that guard, from the
# FIRMWARE clock (_fw_ms_buf -- arrival time is burst-batched and cannot measure a
# frame period; see that attribute). The MEDIAN is the right estimator and the
# reason is the stall itself: through the whole 47-minute event 87% of firmware
# intervals were still a healthy 0.144 s (the MCU emitted short bursts of
# consecutive frames) and only 13% were the long gaps, so the median holds at
# nominal while the window span blows out. A mean, or the live 1 s rate, would
# rise or collapse with the stream and the guard would never trip.
WINDOW_NOMINAL_SAMPLE_N = 500
WINDOW_NOMINAL_MIN_N    = 20    # below this, no nominal is established and the
                                # guard stays off (stream start must not read stalled)
# A gap in FIRMWARE time this long counts as a stall worth recording (v1.64).
# 2 s is ~14 nominal frames at the measured 6.9 Hz -- well clear of ordinary
# scheduling jitter (p99 of healthy intervals on 2026-07-29 was 0.180 s) while
# still catching every one of the 222 gaps in that session's stall window.
FRAME_GAP_WARN_S = 2.0
# How often a '# soak:' line is written while streaming (v1.66), seconds.
SOAK_EMIT_S = 60
SETTINGS_PATH = os.path.join(os.path.dirname(os.path.abspath(__file__)),
                             'data', 'classviz_settings.json')

# --------------------------------------------------------------------------
# Pack / board-temperature telemetry (v1.72)
#
# v1.64 to v1.71 carried the pack voltage as a number the operator read off a
# meter and typed in, with a "Log V" button to timestamp it and a 20-minute nag
# because a typed number goes stale. The firmware has reported both pack volts
# and board temperature on the wire since v4.28 (real DS18B20 temperature since
# v4.33), so none of that hand-entry is needed any more: the track writes itself
# at the firmware's own ~60 s cadence, and it cannot be forgotten.
#
# The pack maths was duplicated from pimd_gui.py under an "every PC app stands
# alone" rule. That was reversed in v1.75: it now comes from the shared
# pimd_pack.py, because four hand-synced copies of a calibration table is
# exactly the thing that drifts, and the note above telling you to retune all
# four was the tell. (The rule still stands for _build_d_command, which is a
# few lines of wire formatting rather than a calibration.)
#
# Gone with it: the PACK_ZONES "data-quality window", whose captions told the
# operator to capture only inside a narrow band of pack voltage. DESIGN 17.23,
# corrected 2026-08-12, measures that sensitivity at ~1 mV/V -- the operating
# point moves -0.8 % across a 2.1 V pack swing and thermal drift dominates it
# by ~10x -- so the window was advice against a effect that is not there.
# --------------------------------------------------------------------------

TEMP_GAUGE_MAX_C = 80.0         # board-temp gauge full scale
# Board-temp gauge colour steps (v1.79). The extractor plateaus the board at
# ~47.8 °C (DESIGN §3), so 50 is "hotter than this rig normally runs" and worth
# a look, not an alarm. These are DS18B20 numbers and the sensor sits on the
# load resistor, blind to the regulator die -- read them as a trend on one
# sensor, not as a component temperature. Note the reading is also epoch-bound:
# it runs ~8 °C hotter since the 2026-08-13 extractor than on the old blow-on
# fan, so these steps are calibrated to the CURRENT rig.
TEMP_WARN_C = 50.0
TEMP_CRIT_C = 60.0
# Hex, NOT the _HL_* constants they match. Those are Qt STYLESHEET strings
# ('rgb(246,  97,  81)') and the double spaces in them are legal CSS but do not
# parse as a QColor -- QColor() returns an invalid colour and the bar paints
# BLACK, with the dark reading text unreadable on top of it. BatteryGauge
# already uses the '#f66151' hex form for the same red, for the same reason.
TEMP_WARN_COLOUR = '#f9f06b'    # == _HL_YELLOW
TEMP_CRIT_COLOUR = '#f66151'    # == _HL_RED
# Warm-up caption colour. Amber TEXT rather than a filled highlight: this sits
# in the temp gauge's caption row, opposite the battery's quiet grey
# 'volts · time left', and a colour block there would shout over the reading it
# is qualifying. Dark enough to stay legible on the light strip background.
WARMUP_CAPTION_COLOUR = '#9c6500'
TEMP_INVALID_MAX_DC = -10_000   # board_temp_dC at or below this is the firmware's
                                # "no reading" sentinel (fw v4.33 sends -32768).
                                # Threshold, not equality -- see pimd_gui.py.

# Telemetry older than this has stopped arriving: the firmware's cadence is
# ~60 s, so three missed reports mean the board went quiet. This replaces
# v1.64's 20-minute PACK_V_REMIND_S, which was pacing a human with a multimeter.
SENSOR_STALE_S = 180.0


class BatteryGauge(QWidget):
    """Battery-icon pack gauge — fill and text are state of charge, the caption
    is the measured pack voltage and which DESIGN §12 zone it sits in."""

    def __init__(self, parent=None):
        super().__init__(parent)
        self.setMinimumSize(170, 52)
        self.setMaximumHeight(52)
        self._pack_mV = None
        self._lockout = False
        self._tracker = None
        self.setToolTip(
            'Pack voltage from the firmware (P/V telemetry, fw v4.28+).\n'
            'Fill and % are state of charge as the fraction of usable pulsing\n'
            'runtime left, zeroed on the {0:.1f} V firmware floor.\n'
            'The caption is measured volts, then time left at the discharge\n'
            'rate fitted over the last {1:.0f} minutes of pulsing.\n'
            'A leading ~ means no rate has been fitted yet, so the figure is\n'
            'the stored curve ({2}) rather than this pack.\n'
            'Every reading is written to the open session dump as a\n'
            "'# pack_v:' line, so a long run carries a voltage TRACK.".format(
                pimd_pack.PACK_TRIP_MV / 1000.0,
                pimd_pack.PackTracker.WINDOW_S / 60.0,
                pimd_pack.PACK_CAL_EPOCH))

    def set_reading(self, pack_mV, lockout=False, tracker=None):
        self._pack_mV = pack_mV
        self._lockout = lockout
        self._tracker = tracker
        self.update()

    def paintEvent(self, event):
        p = QPainter(self)
        p.setRenderHint(QPainter.RenderHint.Antialiasing)
        w, h = self.width(), self.height()
        cap_h = 15
        body = QRectF(1.5, 1.5, w - 9.5, h - cap_h - 4)
        nub = QRectF(body.right() + 1.5, body.top() + body.height() * 0.30,
                     5.0, body.height() * 0.40)

        outline = QColor('#5e5c64')
        p.setPen(QPen(outline, 1.5))
        p.setBrush(Qt.BrushStyle.NoBrush)
        p.drawRoundedRect(body, 3.0, 3.0)
        p.setPen(Qt.PenStyle.NoPen)
        p.setBrush(outline)
        p.drawRoundedRect(nub, 1.5, 1.5)

        inner = body.adjusted(3.0, 3.0, -3.0, -3.0)
        soc = pimd_pack.pack_soc_pct(self._pack_mV)
        if soc is not None:
            colour = (pimd_pack.soc_colour(0.0) if self._lockout
                      else pimd_pack.soc_colour(soc))
            p.setBrush(QColor(colour))
            p.drawRect(QRectF(inner.left(), inner.top(),
                              inner.width() * max(0.0, min(100.0, soc)) / 100.0,
                              inner.height()))
            text = '{0:.0f} %'.format(soc)
            sub = pimd_pack.pack_caption(self._pack_mV, self._lockout, self._tracker)
        else:
            text, sub = '—', 'no pack reading'

        font = QFont()
        font.setPointSize(11)
        font.setBold(True)
        p.setFont(font)
        p.setPen(QColor('#241f31'))
        p.drawText(body, Qt.AlignmentFlag.AlignCenter, text)

        font.setPointSize(8)
        font.setBold(False)
        p.setFont(font)
        p.setPen(QColor('#f66151') if self._lockout else self.palette().windowText().color())
        p.drawText(QRectF(0, h - cap_h, w, cap_h),
                   Qt.AlignmentFlag.AlignCenter, sub)


class BarGauge(QWidget):
    """Horizontal bar gauge with its reading printed inside and an optional
    caption underneath — used for board temperature.

    Geometry deliberately mirrors BatteryGauge's, cap_h and all (v1.79), minus
    the battery nub: same widget height, same body rect, same fonts, same
    caption row. The two sit side by side on the capture strip, where any
    difference between them reads as misalignment rather than as design -- at
    170x24 against the battery's 170x52 they shared neither height nor centre
    line."""

    CAPTION_H = 15          # must match BatteryGauge.paintEvent's cap_h

    def __init__(self, vmax, fmt, colour='#a8c8e8', thresholds=None, parent=None):
        """`thresholds` is [(value, colour), ...]: the bar takes the colour of
        the HIGHEST threshold the reading has reached, and keeps `colour` below
        all of them (v1.79). Sorted on the way in so the caller may list them
        in any order."""
        super().__init__(parent)
        self.setMinimumSize(170, 52)
        self.setMaximumHeight(52)
        self._vmax = vmax
        self._fmt = fmt
        self._colour = colour
        self._thresholds = sorted(thresholds or [])
        self._value = None
        self._caption = ''
        self._caption_colour = None

    def set_value(self, value):
        self._value = value
        self.update()

    def set_caption(self, text, colour=None):
        """Caption line under the bar; '' leaves the row blank. `colour` is a
        CSS colour string, or None for the palette's normal text. Repaints only
        on a real change -- this is driven from a 1 Hz timer that mostly has
        nothing new to say."""
        if (text, colour) != (self._caption, self._caption_colour):
            self._caption, self._caption_colour = text, colour
            self.update()

    def _bar_colour(self):
        colour = self._colour
        for limit, hot in self._thresholds:
            if self._value >= limit:
                colour = hot
        return colour

    def paintEvent(self, event):
        p = QPainter(self)
        p.setRenderHint(QPainter.RenderHint.Antialiasing)
        w, h = self.width(), self.height()
        cap_h = self.CAPTION_H
        # w - 9.5 gives up exactly the width the battery spends on its nub, so
        # the two outlines are the same rectangle in the same place.
        body = QRectF(1.5, 1.5, w - 9.5, h - cap_h - 4)
        p.setPen(QPen(QColor('#5e5c64'), 1.5))
        p.setBrush(Qt.BrushStyle.NoBrush)
        p.drawRoundedRect(body, 3.0, 3.0)

        inner = body.adjusted(3.0, 3.0, -3.0, -3.0)
        if self._value is None:
            text = '—'
        else:
            frac = max(0.0, min(1.0, self._value / self._vmax))
            p.setPen(Qt.PenStyle.NoPen)
            p.setBrush(QColor(self._bar_colour()))
            p.drawRect(QRectF(inner.left(), inner.top(),
                              inner.width() * frac, inner.height()))
            text = self._fmt.format(self._value)

        font = QFont()
        font.setPointSize(11)
        font.setBold(True)
        p.setFont(font)
        p.setPen(QColor('#241f31') if self._value is not None
                 else self.palette().windowText().color())
        p.drawText(body, Qt.AlignmentFlag.AlignCenter, text)

        if self._caption:
            font.setPointSize(8)
            font.setBold(False)
            p.setFont(font)
            p.setPen(QColor(self._caption_colour) if self._caption_colour
                     else self.palette().windowText().color())
            p.drawText(QRectF(0, h - cap_h, w, cap_h),
                       Qt.AlignmentFlag.AlignCenter, self._caption)


def _default_profile():
    """Baseline CLASSIFY_EP profile — matches pimd_mcu.py PROFILES[4] exactly."""
    band_data = (
        (10601, 40.0, ( 8.56,  8.98,  9.37,  9.72, 10.08, 10.49, 10.96, 11.57, 12.53)),
        (17599, 30.0, ( 8.12,  8.54,  8.92,  9.27,  9.63, 10.02, 10.50, 11.10, 12.03)),
        (29201, 20.0, ( 7.62,  8.03,  8.40,  8.75,  9.11,  9.50,  9.96, 10.55, 11.46)),
        (43003, 10.0, ( 6.80,  7.22,  7.58,  7.93,  8.28,  8.66,  9.11,  9.70, 10.57)),
        (56992,  5.0, ( 6.03,  6.43,  6.78,  7.12,  7.46,  7.84,  8.28,  8.85,  9.71)),
    )
    threshold_v = [4.5 - 0.5 * j for j in range(9)]
    return {
        'name': 'CLASSIFY_EP',
        'averages': 32,
        'bands': [
            {'freq_hz': f, 'pulse_us': p, 'delays_us': list(d), 'threshold_v': threshold_v}
            for f, p, d in band_data
        ],
    }


def _list_profile_files():
    if not os.path.isdir(PROFILES_DIR):
        return []
    return sorted(f[:-5] for f in os.listdir(PROFILES_DIR) if f.endswith('.json'))


def _load_profile_file(name):
    """Returns (profile_dict, raw_bytes) -- the raw bytes are needed for
    profile_sha8 (SHA-256 of the profile JSON bytes as loaded, DESIGN §10),
    which can only be computed from the literal file contents, not a
    re-serialized dict."""
    path = os.path.join(PROFILES_DIR, name + '.json')
    with open(path, 'rb') as f:
        raw = f.read()
    return json.loads(raw), raw


pg.setConfigOptions(background='w', foreground='k', antialias=True)

# Highlight colours, as bare rgb() strings so both the widget stylesheets
# (MainWindow.MY_GREEN/YELLOW/RED, built from these) and the per-field <span>
# backgrounds in the signature readout draw from one definition.
_HL_GREEN  = 'rgb(143, 240, 164)'
_HL_YELLOW = 'rgb(249, 240, 107)'
_HL_RED    = 'rgb(246,  97,  81)'
_HL_BLUE   = 'rgb(153, 193, 241)'

_R = int(Qt.AlignmentFlag.AlignRight) | int(Qt.AlignmentFlag.AlignVCenter)
_C = int(Qt.AlignmentFlag.AlignCenter)


# Value <-> bar-axis transforms for a gauge's draggable threshold marker.
# Every gauge but the amplitude one plots the setting directly; that one plots
# log₁₀ of it, so a dragged position has to come back through _pow10_axis
# before it reaches the spinbox. Named functions rather than lambdas so a
# traceback through a marker drag says which transform it was in.
def _identity(x):
    return x


def _log10_axis(x):
    return math.log10(max(x, 1e-3))


def _pow10_axis(x):
    return 10.0 ** x


def _hl_qcolor(css_rgb):
    """QColor from one of the _HL_* 'rgb(r, g, b)' strings above. Those are
    CSS -- fine for stylesheets and <span> backgrounds, but pyqtgraph's
    mkBrush/mkColor rejects them. Parsed here rather than duplicated as hex
    literals so the colours still have exactly one definition."""
    body = css_rgb[css_rgb.index('(') + 1:css_rgb.index(')')]
    return QColor(*(int(v) for v in body.split(',')))


def _hl_ink(css_rgb):
    """Same hue, darkened for use as a STROKE. The _HL_* colours are
    backgrounds -- _HL_YELLOW is a pale rgb(249,240,107) that reads well as a
    fill behind dark text but is close to invisible as a 2 px line on
    pyqtgraph's white canvas. Derived rather than hard-coded so the fill and
    the stroke stay the same colour."""
    return _hl_qcolor(css_rgb).darker(160)


def _fmt(uv):
    """µV → mV string with 3 d.p."""
    return '{0:.3f}'.format(uv / 1000.0)


def _csv_default_path():
    data_dir = os.path.join(os.path.dirname(os.path.abspath(__file__)), 'data')
    return os.path.join(data_dir, 'signatures_{0}.csv'.format(date.today().strftime('%Y%m%d')))


class ScratchDialog(QDialog):
    """Save Scratch… — the small form behind a quick capture of an
    unregistered object. Deliberately not the Analysis tab's structured
    placement widget set: a scratch object has no registry row, so `long_axis`
    has no dim_a to point along and is written 'na' rather than invented.
    (face_normal and the offsets stopped being inputs anywhere at v1.60, so
    they are no longer part of the distinction.)"""

    def __init__(self, parent, air2_available, default_distance_mm=50):
        super().__init__(parent)
        self.setWindowTitle('Save scratch capture')
        form = QFormLayout(self)

        self.le_label = QLineEdit()
        self.le_label.setPlaceholderText('e.g. rusty hinge')
        form.addRow('Label (required):', self.le_label)

        self.le_note = QLineEdit()
        form.addRow('Note:', self.le_note)

        self.cb_no_distance = QCheckBox('unknown / not measured')
        self.sp_distance = QSpinBox()
        self.sp_distance.setRange(0, 2000)
        self.sp_distance.setValue(int(default_distance_mm))
        self.sp_distance.setSuffix(' mm')
        self.cb_no_distance.toggled.connect(lambda on: self.sp_distance.setEnabled(not on))
        dist_row = QHBoxLayout()
        dist_row.addWidget(self.sp_distance)
        dist_row.addWidget(self.cb_no_distance)
        form.addRow('Distance:', dist_row)

        self.cb_medium = QComboBox()
        self.cb_medium.addItems(SCRATCH_MEDIA)
        form.addRow('Medium:', self.cb_medium)

        self.cb_anchor = QComboBox()
        self.cb_anchor.addItem('static baseline (flat, quick)', 'flat')
        self.cb_anchor.addItem('last training capture (air/target/air)', 'air2')
        if not air2_available:
            # Disabled rather than hidden: the option is real, it just needs a
            # completed Analysis-tab cycle, and saying so is more useful than
            # silently offering one choice.
            model_item = self.cb_anchor.model().item(1)
            if model_item is not None:
                model_item.setEnabled(False)
            self.cb_anchor.setToolTip(
                'Two-anchor (drift-corrected) capture needs a completed, unsaved '
                'Training cycle on the Analysis tab.')
        form.addRow('Air anchor:', self.cb_anchor)

        buttons = QDialogButtonBox(QDialogButtonBox.StandardButton.Save |
                                    QDialogButtonBox.StandardButton.Cancel)
        self._save_button = buttons.button(QDialogButtonBox.StandardButton.Save)
        self._save_button.setEnabled(False)
        self.le_label.textChanged.connect(
            lambda text: self._save_button.setEnabled(bool(text.strip())))
        buttons.accepted.connect(self.accept)
        buttons.rejected.connect(self.reject)
        form.addRow(buttons)

    def values(self):
        return {
            'label': self.le_label.text().strip(),
            'note': self.le_note.text().strip(),
            'distance_mm': None if self.cb_no_distance.isChecked() else self.sp_distance.value(),
            'medium': self.cb_medium.currentText(),
            'anchor': self.cb_anchor.currentData(),
        }


class MainWindow(QMainWindow):
    MY_GREEN  = 'background-color: {0};'.format(_HL_GREEN)
    MY_YELLOW = 'background-color: {0};'.format(_HL_YELLOW)
    MY_RED    = 'background-color: {0};'.format(_HL_RED)
    MY_BLUE   = 'background-color: {0};'.format(_HL_BLUE)

    def __init__(self):
        super().__init__()
        self.setWindowTitle('PIMD ClassViz v{0} by Mark Makies'.format(APP_VERSION))

        # Serial
        self.serial = QSerialPort()
        self.serial.readyRead.connect(self.read_from_serial)
        self._last_cmd    = ''
        self._last_packet = ''
        self._fw_version_line: 'str | None' = None
        # v1.73: callback awaiting the firmware's D response; see
        # _send_dynamic_profile() / process_packet().
        self._pending_d_ready = None
        self._d_ack_timer = QTimer(self)
        self._d_ack_timer.setSingleShot(True)
        self._d_ack_timer.timeout.connect(self._on_d_ack_timeout)

        # Profile dimensions (n_bands, n_cells, labels, etc) — instance state so
        # the heatmap/stats table/single-cell selectors can resize at runtime
        # when a saved profile is loaded from the top-bar selector.
        self._set_profile_dims(_default_profile(), DEFAULT_PROFILE_IDX)

        # Data state — sweep
        self._latest_raw: 'np.ndarray | None' = None   # shape (n_channels,)
        # v1.73: per-cell ADC clip state. _rail_mask is this frame's; _rail_seen
        # is the set reported so far, so the status line and the session mark
        # fire on a TRANSITION rather than once per frame at the sweep rate.
        self._rail_mask: 'np.ndarray | None' = None    # shape (n_channels,) bool
        self._rail_seen: set = set()
        self._rail_label_text = ''     # last text pushed to lbl_rail, so the
                                       # per-frame refresh is a no-op when the
                                       # rail count has not changed
        self._baseline_mean: 'np.ndarray | None' = None  # shape (n_bands, n_cells)
        self._baseline_std:  'np.ndarray | None' = None  # shape (n_bands, n_cells)
        self._baseline_mode = 'static'   # 'static' | 'rolling' | 'nominal'
        self._baseline_age: 'float | None' = None
        self._capture_buf: list = []
        self._capturing   = False
        self._capture_n   = CAPTURE_FRAMES_DEFAULT
        self._rolling_buf: deque = deque(maxlen=10_000)
        # Firmware frame clock for the same frames, appended in lockstep with
        # _rolling_buf and with the same maxlen so index -k aligns in both
        # (v1.64). Kept as a parallel deque rather than widening _rolling_buf's
        # tuple, which many consumers unpack as (ts, arr).
        #
        # It exists because _rolling_buf's timestamp is PC ARRIVAL time, and
        # arrival is burst-batched: read_from_serial() drains several lines per
        # readyRead and stamps them microseconds apart. Measured over all 114k
        # frames of the 2026-07-29 dump, arrival intervals are bimodal -- median
        # 0.0035 s with 57% of them under 10 ms, against p90 0.444 s -- while the
        # firmware clock is uniform at median 0.1440 s with NONE under 10 ms. Both
        # necessarily share the same mean (0.1683 s: same elapsed, same count),
        # which is the trap: an arrival-time mean looks right while its median is
        # 40x too small, and the median is what survives a stall. So arrival time
        # cannot measure how much TIME a window of frames covers, and the
        # firmware's own clock can. This is what the span guard measures against.
        # The degree of batching varies -- one 10k-frame stretch of that session
        # ran only 23% batched -- so this is not a fixed factor to correct for.
        self._fw_ms_buf: deque = deque(maxlen=10_000)
        # Glitch-substituted copy of the same frames, appended in lockstep and
        # with the same maxlen, so index -k aligns across all three (v1.69).
        #
        # _rolling_buf deliberately holds UNFILTERED raw: it feeds the session
        # dump and the capture path, where a recording must stay faithful. But
        # the Std Dev displays are not recordings -- they are the instrument an
        # operator reads to judge the noise floor, and a single 440-880 mV ADC
        # bit-truncation artifact enters sigma at full weight and stays visible
        # for a whole window (~7.2 s at N=50), i.e. a glitch reads as a noisy
        # cell. The Delta/Z/RAW modes never had this because they read
        # _latest_raw, which is already substituted; only the two sigma paths
        # went to the buffer directly.
        #
        # Stored as substituted frames rather than a mask + median because the
        # substitution is per-cell and reconstructing it later costs more than
        # the array. _get_current_baseline()'s rolling mode is left on the raw
        # buffer on purpose: it reduces with a MEDIAN, which is already immune.
        self._rolling_disp_buf: deque = deque(maxlen=10_000)
        self._rolling_T   = ROLLING_SECS_DEFAULT
        # v1.64 window-span guard state (see _window_frames). span/reason are
        # written on every window reduction and read only for display; the
        # nominal cache is keyed on _frame_count so it recomputes once a frame.
        self._window_span_s        = None
        self._window_block_reason  = None
        # v1.69: same two, written on EVERY reduction including record=False,
        # so a caller can read back its own verdict without publishing it.
        self._window_last_span_s   = None
        self._window_last_reason   = None
        self._stddev_block_reason  = None
        self._nominal_frame_cache  = (-1, None)
        # v1.64 stream-gap detection (see _note_frame_gap). Latched for the run:
        # the Rate readout is instantaneous and clears itself, which is no use
        # for an unattended session.
        self._last_fw_time_ms = None
        self._stall_count     = 0
        self._stall_worst_s   = 0.0
        self._stall_last_wall = None
        # v1.72 pack / board-temperature telemetry, replacing v1.64's typed-in
        # number. All None until the firmware says otherwise, so the gauges read
        # '—' rather than a plausible-looking zero -- and _pack_v_value() returns
        # None, which is written as a blank column, not as 0.00 V.
        self._pack_mV          = None
        self._board_temp_dC    = None   # None also means "sentinel seen", i.e. no reading
        self._pack_lockout     = False
        self._sensor_last_wall = None   # wall time of the last accepted P/V reading
        # Fits the live discharge rate behind the gauge's time-remaining figure.
        # Fed note_pulse() from the W handler: sweeps arriving IS the coil
        # running, which is what makes the fitted rate a LOADED one. It also
        # watches for pack swaps, which happen here between runs as packs charge.
        self._pack_tracker     = pimd_pack.PackTracker()
        # v1.66 soak history. The rig's thermal state depends on how long it has
        # actually been sweeping, not on wall-clock elapsed -- a stopped stream
        # cools it, and nothing recorded that. streamed_s accumulates ACROSS
        # stop/start rather than being (now - session_start).
        self._stall_total_s        = 0.0
        self._stream_run_start_wall = None   # wall time this streaming run began
        self._streamed_total_s     = 0.0     # completed runs, this session
        self._last_stream_stop_iso = None    # persisted; drives idle_before_s
        self._soak_last_emit_wall  = None
        # v1.64 per-chart draw pause (see _make_chart_pause_checkbox). Deliberately
        # NOT persisted: a chart that comes back frozen after a restart reads as a
        # bug, and the reason to pause is a condition of the run, not a preference.
        self._analysis_c2_paused = False
        self._analysis_g8_paused = False
        self._analysis_g9_paused = False

        self._freeze       = False
        self._autoscale    = True
        self._manual_range = 200_000.0
        self._display_mode = 'delta'     # 'raw' | 'delta' | 'z'
        self._3d_visible   = False

        self._continuous_log     = False
        self._csv_header_written = False
        self._csv_rows           = 0
        self._frame_count        = 0

        # Throughput monitor — recomputed once/sec by _rate_timer (see below),
        # so the displayed Hz is an exact "frames received in the last second"
        # count, not a smoothed estimate.
        self._fps_hz                = 0.0
        self._fps_last_calc_wall    = time.time()
        self._fps_last_frame_count  = 0
        # Max number of complete lines drained in a single read_from_serial()
        # call since the last rate tick -- consistently >1 means the GUI is
        # falling behind the incoming serial stream and lines are backing up
        # in Qt's serial buffer between readyRead events.
        self._serial_max_batch      = 0

        self._recording           = False
        self._session_file        = None   # open file handle while a session is being recorded
        self._session_path        = None
        self._session_start_wall  = None   # time.time() at recording start (elapsed display)
        self._session_frame_count = 0

        self._ch_glitch_buf: 'np.ndarray | None' = None  # shape (64, n_channels), circular
        self._ch_glitch_pos  = 0

        # Pauses session *recording* (frame rows stop being written, marks are
        # refused) without closing the file. Driven by the Analysis tab's
        # Session Pause button; read by process_packet.
        self._session_paused: bool = False

        # Auto-logging (v1.63). A session dump opens by itself whenever the
        # stream starts, so a bench run can't silently go unrecorded -- the
        # 2026-07-29 session lost its whole profiling window and the 47-minute
        # pack settle before it that way, and raw stream is not recoverable
        # after the fact.
        #   _session_autolog            -- operator preference, persisted.
        #   _session_autolog_suppressed -- latched by an explicit Stop so "stop"
        #                                  means stop; cleared at the next
        #                                  stream start.
        #   _session_autostarted        -- the open file was auto-opened, so
        #                                  Session Start adopts it (adds notes)
        #                                  instead of refusing.
        #   _session_stop_is_forced     -- set by the programmatic force-stops
        #                                  (_apply_profile, start_stop) so
        #                                  _toggle_record_frames can tell them
        #                                  apart from an operator click.
        self._session_autolog            = True
        self._session_autolog_suppressed = False
        self._session_autostarted        = False
        self._session_stop_is_forced     = False

        # Data state — stats
        self._freeze_stats = False
        self._stats_row_height = 22

        # Data state — Analysis tab
        self._analysis_avg_n    = 1
        self._analysis_templates = {}   # (session,target,distance) -> {shape,color,label}

        self._analysis_strip_reset_ts = 0.0
        self._analysis_strip_norm_auto = True
        self._analysis_strip_manual_ref = 0.0
        self._analysis_strip_scale_auto = True
        self._analysis_strip_manual_halfrange = 5.0
        # Strip split (v1.76): off = the historical single all-cell average;
        # on = two curves, early cells (blue) and late cells (red), divided
        # after sd index _analysis_strip_split_sd (1-based, "last early cell").
        # Default 5 is cal_2x11_v5's amplitude-anchored early zone (DESIGN
        # §10) -- the divider the profile was designed around, not a guess.
        # _pref mirrors the Family Plane's band-pair memory (v1.49): the
        # spinbox is only as wide as the LIVE profile, so a value restored
        # under a narrower startup profile must not overwrite the operator's
        # choice. See _rebuild_analysis_strip_split().
        self._analysis_strip_split = False
        self._analysis_strip_split_sd = 5
        self._analysis_strip_split_pref = None

        # Analysis tab — per-group Auto/Manual normalize+scale (heatmap/8-grid/9-grid)
        self._analysis_hm_norm_auto      = True
        self._analysis_hm_display_mode   = 'delta'   # used only when norm is Manual (decoupled)
        self._analysis_hm_scale_auto     = True
        # Manual scale is an explicit (min, max) pair, not a ± half-range
        # (v1.44). Std Dev is the case that forced it: a rolling σ field lives
        # in a narrow band well above zero, so a range anchored at 0 spends
        # most of the colour ramp on values that never occur.
        self._analysis_hm_manual_min_uv  = -200_000.0
        self._analysis_hm_manual_max_uv  = 200_000.0
        # Colorbar-as-range-slider state (v1.45). The bar's axis spans a domain
        # wider than the Min/Max window so the two handles have somewhere to sit
        # *and* somewhere to travel; frozen mid-drag so the value under the
        # cursor doesn't move while the window is being dragged.
        self._analysis_cbar_domain     = None  # (lo, hi) currently on the bar's axis
        self._analysis_cbar_data_range = None  # (lo, hi) of the matrix last drawn
        self._analysis_cbar_dragging   = False
        self._analysis_cbar_syncing    = False  # guards our own setRegion() calls

        self._analysis_c2_norm_auto  = True
        self._analysis_c2_manual_ref = 0.0
        self._analysis_c2_scale_auto = True
        self._analysis_c2_manual_halfrange = 5.0

        self._analysis_g8_norm_auto  = True
        self._analysis_g8_manual_ref = 0.0
        self._analysis_g8_scale_auto = True
        self._analysis_g8_manual_halfrange = 5.0

        self._analysis_g9_norm_auto  = True
        self._analysis_g9_manual_ref = 0.0
        self._analysis_g9_scale_auto = True
        self._analysis_g9_manual_halfrange = 5.0

        # Analysis tab — signature file editing (New/Open-for-editing/Save/Delete)
        self._editable_sig_path       = None   # str|None -- the currently open-for-editing file
        self._editable_sig_session_id = None   # 'gui_YYYYMMDD_HHMMSS', assigned fresh on New/Open
        self._editable_sig_seq        = 0      # running per-file capture_id sequence, reset on New/Open
        self._editable_repeat_counts  = {}     # placement tuple -> count seen, for repeat_idx auto-increment
        # Directory the signature file dialogs open in, persisted across
        # sessions (v1.44). Corpora and scratch files live in several places
        # (src/data/corpora/, src/data/scratch/, ad-hoc directories for
        # another rig's captures), so re-navigating from the CWD on every
        # load was a per-session tax. Only the DIRECTORY is remembered -- a
        # remembered file path would be a stale pointer, which is the foot-gun
        # _load_settings' comment calls out for the editable-file path.
        self._last_sig_dir = CORPORA_DIR

        # Target registry (pimd_target_check.py) -- backs the Analysis tab's inline
        # capture widgets.
        self._targets        = {}    # dict[target_id -> pimd_target_check.Target]
        self._target_issues   = []

        # Analysis tab — automated auto-detect training cycle (v1.34). A
        # second, independent capture channel from _capturing/_capture_buf
        # (which stay hard-wired to the Heatmap tab's "Capture baseline"). One
        # Space press locks the leading air; target placement/removal are
        # auto-detected; the trailing air rolls straight into the next cycle's
        # leading air (same rolling deque).
        self._sig_capture_n    = SIG_CAPTURE_N_DEFAULT
        self._analysis_training_active = False
        # phase: 'air_lead' | 'await_target' | 'target' | 'await_remove' | 'air_trail'
        self._sig_train_phase  = 'air_lead'
        self._sig_train_status = 'settling'  # 'settling' | 'collecting' | 'ready' (collecting phases)
        self._sig_train_buf    = None        # deque(maxlen=N) of (ts, raw_uV.copy()); rolls in 'ready'
        self._sig_train_last_style = None    # stylesheet churn guard for the status label
        self._sig_glitch_skipped = 0    # glitch frames excluded from the current window (v1.31)
        self._sig_air_ref      = None   # np mV vector: median of the locked leading air (auto-detect ref)
        self._sig_air_ref_ts   = None   # wall time it was locked -- DESIGN §17.10 makes reference
                                        # AGE the ceiling on any frozen-reference measurement
        self._sig_await_deadline = None # wall-clock; 30 s guard for await_target/await_remove
        self._sig_removal_armed = False # a settle-loss has been seen during await_remove, so
                                        # the object has physically moved -- drift cannot set this
        self._sig_target_manual = False # placement was forced by Space, so auto-detect can't
                                        # see this target -- removal must be manual too (v1.41)
        self._sig_decide_pending = False  # a computed signature is awaiting Save/Ignore
        self._sig_decide_flash_on = False # flash phase for the Save/Ignore buttons
        self._sig_await_flash_on = False  # flash phase for the place/remove countdown (B)
        self._sig_air_before   = None   # {'t_seconds':(n,), 'frames_mV':(n,n_channels), 'n_frames':int}
        self._sig_air_after    = None   # same shape, optional
        self._sig_target       = None   # same shape
        self._sig_last_stats   = None   # cached dict from _compute_sig_stats(), for the live readout
        # (session, capture_id) keys saved during this app session (v1.38) --
        # they land *checked* in the signature list so a fresh capture is on
        # the charts immediately, without hunting for it. Only ever consulted
        # for a key's first appearance, so unticking one sticks. In-memory
        # only; cleared whenever a different editable file is started/opened.
        self._sig_autocheck_keys = set()

        self._SIG_AWAIT_SECONDS = 30.0  # place/remove-target guard countdown

        # Re-entry guard for the Trigger Levels gauges: a marker drag sets its
        # bound spinbox, whose valueChanged re-renders the column, which would
        # otherwise reposition the very line being dragged.
        self._gauge_marker_drag = False

        # Analysis tab — session recording (alternate path to the Stats tab's
        # Record Session button; drives the same _session_start/_session_stop/
        # _append_mark machinery and the _recording/_session_paused flags).
        self._analysis_session_recording = False

        # Shape Space tab — feature-space view of the SAME signature store the
        # Analysis tab loads into (self._analysis_templates); no second loader,
        # no second copy of the captures. Per-capture features are cached
        # because they only change when the store or the profile changes;
        # anything that depends on the control bar (the custom band range) is
        # derived at draw time from the cached unit shape instead.
        self._shape_feat_cache   = {}     # template key -> feature dict
        self._shape_selected_key = None   # clicked scatter point
        # role -> monotone spacing callable, or None for a plain linear axis.
        # Rebuilt from the drawn captures on every static redraw (v1.47).
        self._shape_scale_map    = None
        # role -> the custom band (lo, hi) the operator actually asked for, as
        # opposed to what the spinboxes are currently able to show (v1.49).
        # The spins are ranged to the LIVE profile, so a pair chosen under a
        # 7-band profile cannot even be represented while the app is still on
        # the 5-band startup profile -- setValue() would clamp it away and the
        # choice would be lost. None until settings load or an operator edit.
        self._shape_band_pref    = {'x': None, 'y': None}
        self._shape_live         = None   # feature dict for the current frame, or None
        # Live feature dicts, appended once per W frame in process_packet so
        # the trail is already populated when the tab is first shown. Only
        # gated frames go in -- below the gate the shape is normalised noise
        # and a trail would make it look like a real trajectory.
        self._shape_trail        = deque(maxlen=SHAPE_TRAIL_MAX)
        self._shape_geom_warned  = False  # one §11 geometry message per store load

        # Shape Space air reference — its OWN, deliberately not the shared
        # _get_current_baseline(). A one-shot static air capture cannot serve
        # this tab: thermal drift (DESIGN §3 ≈ −50 µV/s, §14.1 heavy bands
        # −20…−31 mV) accumulates into the delta as a large *coherent* term,
        # and the SNR gate cannot catch that by construction — splithalf is a
        # short-timescale scatter statistic, so drift inflates amp while
        # leaving splithalf flat. Simulated at the documented rate against a
        # fresh static baseline, coil in air, the frame reads SNR 8.6 after
        # 30 s and 67 after 4½ minutes: the dot goes confidently coloured and
        # wanders on nothing at all. Referencing recent air instead cancels
        # the drift, which is the same reason the Analysis tab's Training
        # cycle brackets every target with air (DESIGN §17.5).
        #
        # Two modes, and Space is the only thing that moves between them:
        #   'air'      every frame feeds the rolling buffer and the reference
        #              is its running median, so the live delta is ~0 by
        #              construction and the cursor sits at the origin.
        #   'measure'  the last 'frames' of air were snapshotted as a fixed
        #              reference; the cursor moves against it.
        # Nothing here auto-detects a target arriving or leaving — an earlier
        # revision did, and it is gone by direction.
        self._shape_air_mode   = 'air'
        self._shape_air_buf    = None    # deque(maxlen=Air frames) of mV frames
        self._shape_air_ref    = None    # np vector, mV
        self._shape_air_ref_ts = None    # wall time the reference was snapshotted

        self._setup_colormaps()
        self._build_ui()
        QApplication.instance().installEventFilter(self)
        self._load_settings()

        self._redraw_timer = QTimer()
        self._redraw_timer.setInterval(REDRAW_MS)
        self._redraw_timer.timeout.connect(self._redraw)
        self._redraw_timer.start()

        self._rate_timer = QTimer()
        self._rate_timer.setInterval(1000)
        self._rate_timer.timeout.connect(self._update_rate)
        self._rate_timer.start()

        # Auto-start (v1.53): reproduce the operator's own opening move --
        # Connect, then Load & Run whatever profile the dropdown remembers.
        # singleShot(0) rather than a direct call so the window is up and the
        # event loop running before any serial I/O; degrades to a status-bar
        # message and a normal idle app if there is no port or no profile.
        QTimer.singleShot(0, self._autostart)

    # ------------------------------------------------------------------
    # Profile dimensions
    # ------------------------------------------------------------------
    def _set_profile_dims(self, profile, profile_idx, profile_raw_bytes=None):
        """Pure data update — sets self._n_bands/_n_cells/_band_labels/etc from
        `profile` (dict: name, averages, bands=[{freq_hz,pulse_us,delays_us,
        threshold_v(optional)}, ...], all bands sharing the same delay count).
        Does not touch any UI widgets — see _apply_profile() for that.

        Also computes self._profile_sha8 (first 8 hex chars of SHA-256 of the
        profile JSON bytes as loaded, DESIGN §10) -- profile_raw_bytes is the
        literal bytes read from a saved profile file (_load_profile_file);
        when there is no file (the built-in _default_profile() fallback), a
        canonical sort_keys=True re-serialization is used as a documented,
        deliberate surrogate since there is nothing to hash literally."""
        bands = profile['bands']
        n_bands = len(bands)
        n_cells = len(bands[0]['delays_us'])
        self._profile           = profile
        self._active_profile_idx = profile_idx
        self._profile_raw_bytes = profile_raw_bytes if profile_raw_bytes is not None \
            else json.dumps(profile, sort_keys=True, separators=(',', ':')).encode('utf-8')
        self._profile_sha8 = pimd_features.profile_sha8_of_bytes(self._profile_raw_bytes)
        self._n_bands    = n_bands
        self._n_cells    = n_cells
        self._n_channels = n_bands * n_cells
        # Keep the (freq_hz, pulse_us, delays_us_tuple) shape used throughout
        # the rest of the file (was the module-level BANDS_META tuple).
        self._bands_meta = [(b['freq_hz'], b['pulse_us'], tuple(b['delays_us']))
                             for b in bands]
        self._band_labels = ['{0:,}Hz / {1:.3f}µs'.format(b['freq_hz'], b['pulse_us'])
                              for b in bands]
        # Sort rows by PULSE WIDTH ascending -- shortest-pulse band first. Combined
        # with invertY(True) on the heatmap plots this puts the shortest pulse at the
        # top and the longest at the bottom, matching this project's standard grid
        # orientation (pimd_rawlog.py header / CHANGELOG v1.13): lowest top-left,
        # highest bottom-right.
        #
        # v1.71: the key was `delays_us[0]`, a PROXY for pulse width rather than the
        # thing itself. v1.70 adopted it having verified only that
        # cal_110_full_range_v4's pulse and first-delay ascend together, which they
        # do -- as they do for every calibrated profile, because a shorter pulse
        # releases the clamp earlier. The proxy fails the moment two bands are given
        # the SAME delay ladder by hand: cal_3x15_v1 starts both its 50 µs and 10 µs
        # bands at 5.160 µs, so the tie fell to protocol order and the rows came out
        # 50/10/100 instead of 10/50/100. Sorting on pulse_us is what the orientation
        # rule actually means, and it is a no-op on every other profile on disk
        # (checked: only cal_3x15_v1 differs between the two keys). Ties between
        # equal pulse widths keep protocol order -- Python's sort is stable -- which
        # is what a profile carrying a duplicated band wants.
        self._band_display_order = sorted(
            range(n_bands), key=lambda i: bands[i]['pulse_us'])
        self._display_band_labels = [self._band_labels[i] for i in self._band_display_order]
        self._band_stats_order  = list(self._band_display_order)
        self._stats_band_labels = [self._band_labels[i] for i in self._band_stats_order]
        self._has_threshold_v = all(
            'threshold_v' in b and len(b['threshold_v']) == n_cells for b in bands)
        if self._has_threshold_v:
            self._cell_labels = ['{0:.3f}V'.format(v) for v in bands[0]['threshold_v']]
            self._nominal_baseline_uv = np.array(
                [[v * 1_000_000 for v in b['threshold_v']] for b in bands], dtype=float)
        else:
            self._cell_labels = ['d{0}'.format(j) for j in range(n_cells)]
            self._nominal_baseline_uv = np.zeros((n_bands, n_cells))
        # Cells sorted threshold_v DESCENDING -- with _pulse_sort_order below,
        # this is what puts a live frame into pimd_shape's vector convention
        # (band-major, pulse ascending, thresholds high->low), the same order
        # the corpus rows are sorted into on save. Live and stored shapes are
        # only comparable because both go through these two reindexes.
        if self._has_threshold_v:
            thr = bands[0]['threshold_v']
            self._cell_sort_order = [int(j) for j in
                                      np.argsort([-float(v) for v in thr], kind='stable')]
            self._threshold_v_sorted = [float(thr[j]) for j in self._cell_sort_order]
        else:
            self._cell_sort_order = list(range(n_cells))
            self._threshold_v_sorted = [float('nan')] * n_cells
        # Analysis tab: bands sorted pulse_us ascending. Raw protocol/profile
        # band order is NOT reliably pulse-ascending -- the live default
        # CLASSIFY_EP profile is actually pulse-*descending* (40->5us) -- so
        # every Analysis chart that plots "vs pulse width" must reindex by
        # this instead of assuming index order.
        # As of v1.71 this is the SAME permutation as _band_display_order above
        # (that one used to key on delays_us[0]). Kept as a separate name because
        # the two express different requirements -- grid orientation there, "vs
        # pulse width" plotting here -- and only coincide while both are defined
        # as pulse-ascending. Do not collapse one into the other.
        self._pulse_sort_order = sorted(range(n_bands), key=lambda i: bands[i]['pulse_us'])
        self._pulse_us_sorted  = [bands[i]['pulse_us'] for i in self._pulse_sort_order]
        # Per-cell delay_us range across all bands, for the Analysis heatmap's
        # threshold-axis sub-label (threshold_v is constant per cell across
        # bands; delay_us is not, so it can only be shown as a range there).
        self._cell_delay_range_us = [
            (min(b['delays_us'][j] for b in bands), max(b['delays_us'][j] for b in bands))
            for j in range(n_cells)
        ]
        self._cell_delay_avg_us = [
            float(np.mean([b['delays_us'][j] for b in bands])) for j in range(n_cells)
        ]

    def _apply_profile(self, profile, profile_idx, profile_raw_bytes=None):
        """Switch the active profile at runtime: updates dimensions, clears any
        old-shape buffered data, and resizes the heatmap/3D surface/stats table/
        single-cell selectors to match. Called once for the default profile (via
        _set_profile_dims directly, before _build_ui) and again whenever a
        saved profile is loaded and run from the top-bar selector."""
        self._set_profile_dims(profile, profile_idx, profile_raw_bytes)

        # Old-shape data must not survive a dimension change.
        was_recording = self._recording
        if self._recording:
            self._session_stop_is_forced = True   # not an operator Stop; don't suppress auto-log
            self.pb_record.setChecked(False)      # triggers _toggle_record_frames → auto-save
        self._rolling_buf.clear()
        self._fw_ms_buf.clear()      # v1.64: must stay index-aligned with the above
        self._rolling_disp_buf.clear()   # v1.69: likewise
        self._baseline_mean = None
        self._baseline_std  = None
        self._baseline_age  = None
        self._latest_raw     = None
        self._frame_count    = 0
        self._ch_glitch_buf  = None
        self._ch_glitch_pos  = 0
        # v1.73: rail state is per-geometry -- channel indices mean something
        # different under a new profile, and which cells clip is precisely what
        # changing the delay ladder changes. Reset so the new profile reports
        # its own rails afresh.
        self._rail_mask      = None
        self._rail_seen      = set()
        self._rail_label_text = ''
        self.lbl_rail.setText('')
        self.lbl_rail.setStyleSheet('')

        # Shape Space state is invalidated BEFORE anything redraws: the cached
        # features and the live trail were computed under the old geometry,
        # and _refresh_analysis_overlays() below reaches the Shape Space
        # panels, which would otherwise repopulate from the stale cache.
        if hasattr(self, 'shape_scatter'):
            self._shape_invalidate_features()
            self._shape_trail.clear()
            self._shape_live = None
            self._shape_selected_key = None
            self._shape_air_restart()   # old-geometry air reference is unusable

        self._rebuild_heatmap_axes()
        self._rebuild_3d_surface()
        self._rebuild_stats_table()
        if hasattr(self, 'analysis_plot'):
            self._rebuild_analysis_heatmap_axes()
            self._rebuild_analysis_chart2_ticks()
            self._rebuild_analysis_grid8()
            self._rebuild_analysis_grid9()
            self._apply_g8_scale()
            self._apply_g9_scale()
            self._analysis_strip_reset_ts = 0.0
            self._rebuild_analysis_strip_split()   # divider is in cells; n_cells just changed
            self._reset_sig_capture_state()   # old raw arrays would mismatch the new n_channels
            self._refresh_analysis_overlays()  # tail-calls _shape_redraw_static()
        self.header_label.setText('Profile {0} — {1} ({2} bands × {3} cells)'.format(
            profile_idx, profile.get('name', '?'), self._n_bands, self._n_cells))

        # v1.63: the dump we just force-closed was headed with the *old*
        # profile_json/sha8, so continuing into it was never an option -- open
        # a fresh, correctly-headed one rather than leave the rest of the run
        # unlogged. Only if a recording was actually interrupted; a profile
        # change while idle stays idle. Last in the method so the new header is
        # written against the fully-applied profile.
        if was_recording:
            self._maybe_autostart_session('profile change')

    # ------------------------------------------------------------------
    # Colormaps
    # ------------------------------------------------------------------
    def _setup_colormaps(self):
        try:
            self.cm_div = pg.colormap.get('RdBu_r', source='matplotlib')
        except Exception:
            try:
                self.cm_div = pg.colormap.get('RdBu_r')
            except Exception:
                self.cm_div = pg.ColorMap(
                    pos=np.array([0.0, 0.5, 1.0]),
                    color=np.array([[0, 0, 220, 255], [255, 255, 255, 255],
                                    [220, 0, 0, 255]], dtype=np.uint8))
        try:
            self.cm_seq = pg.colormap.get('plasma', source='matplotlib')
        except Exception:
            try:
                self.cm_seq = pg.colormap.get('plasma')
            except Exception:
                self.cm_seq = pg.colormap.get('viridis')

    # ------------------------------------------------------------------
    # UI
    # ------------------------------------------------------------------
    def _build_ui(self):
        central = QWidget()
        layout  = QVBoxLayout(central)

        # Top bar — always visible on both tabs
        row1 = QHBoxLayout()
        row1.addWidget(QLabel('Port:'))
        self.le_port = QLineEdit(DEFAULT_PORT)
        self.le_port.setMaximumWidth(150)
        row1.addWidget(self.le_port)

        self.pb_connect = QPushButton('Not Connected')
        self.pb_connect.setStyleSheet(self.MY_YELLOW)
        self.pb_connect.clicked.connect(self.connect_port)
        row1.addWidget(self.pb_connect)

        self.pb_start = QPushButton('Stopped')
        self.pb_start.setStyleSheet(self.MY_YELLOW)
        self.pb_start.clicked.connect(self.start_stop)
        row1.addWidget(self.pb_start)

        # Saved-profile selector — replaces the old Profile Builder tab; picks a
        # profile JSON from data/profiles/ and sends it straight to the board.
        row1.addWidget(QLabel('Saved profile:'))
        self.cb_profile_file = QComboBox()
        self._refresh_profile_file_list()
        self.cb_profile_file.setSizeAdjustPolicy(QComboBox.SizeAdjustPolicy.AdjustToContents)
        row1.addWidget(self.cb_profile_file)
        self.pb_load_run_profile = QPushButton('Load && Run')
        self.pb_load_run_profile.setStyleSheet(self.MY_YELLOW)
        self.pb_load_run_profile.clicked.connect(self._on_load_run_profile)
        row1.addWidget(self.pb_load_run_profile)

        self.header_label = QLabel('Profile {0} — {1} ({2} bands × {3} cells)'.format(
            self._active_profile_idx, self._profile.get('name', '?'),
            self._n_bands, self._n_cells))
        row1.addWidget(self.header_label, stretch=1)

        # Session-level supply (DESIGN §12 — battery/PSU noise floor differs
        # and can't be auto-detected). Not per-capture: shared by the
        # Analysis-tab quick-capture save path and the session mark-writing
        # path.
        row1.addWidget(QLabel('Supply:'))
        self.cb_supply = QComboBox()
        self.cb_supply.addItems(SUPPLY_CHOICES)
        row1.addWidget(self.cb_supply)

        # Throughput readout — visible on every tab, updated once/sec by
        # _rate_timer/_update_rate. Answers "is data flowing at full speed".
        self.lbl_rate = QLabel('Rate: — (idle)')
        row1.addWidget(self.lbl_rate)

        # v1.73: ADC-rail indicator, same reasoning as lbl_rate above -- a
        # standing condition needs a standing readout. This started as a
        # status-bar message and that was wrong: the bar is shared with ~80
        # other showMessage() callers, so a one-shot line announcing a
        # condition that then persists for the whole run is gone before anyone
        # looks (bench, 2026-08-11). Blank when nothing is clipping, so it
        # costs no space in the normal case.
        self.lbl_rail = QLabel('')
        self.lbl_rail.setToolTip(
            'Cells sitting at the ADC full scale. Their values are limits, not\n'
            'measurements, and any feature computed over them inherits that.\n'
            'Fix it at the delay ladder, not in software.')
        row1.addWidget(self.lbl_rail)
        layout.addLayout(row1)

        # Tab widget
        self.tabs = QTabWidget()
        self.tabs.addTab(self._build_heatmap_tab(), 'Heatmap')
        self.tabs.addTab(self._build_stats_tab(),   'Stats')
        self._analysis_tab_index = self.tabs.addTab(self._build_analysis_tab(), 'Analysis')
        self._shape_tab_index = self.tabs.addTab(self._build_shape_tab(), SHAPE_TAB_TITLE)
        layout.addWidget(self.tabs, stretch=1)

        self.setCentralWidget(central)
        self.statusBar().showMessage('Not connected')

        # Loaded here (after every tab -- and its target combo(s) -- is
        # built) so the initial population/degrade behavior applies before
        # _load_settings() restores any persisted target_id.
        self._load_targets_registry(show_dialog_on_error=True)

    # ------------------------------------------------------------------
    # Tab 0 — Heatmap
    # ------------------------------------------------------------------
    def _build_heatmap_tab(self):
        w      = QWidget()
        layout = QVBoxLayout(w)

        # Row 2 — display + baseline controls
        row2 = QHBoxLayout()
        row2.addWidget(QLabel('Display:'))
        self.cb_display = QComboBox()
        self.cb_display.addItems(['Δ deviation [default]', 'Z normalised', 'RAW abs µV',
                                   'Std Dev (rolling N, see Stats tab)'])
        self.cb_display.setCurrentIndex(0)
        self.cb_display.currentIndexChanged.connect(self._on_display_changed)
        row2.addWidget(self.cb_display)

        row2.addWidget(QLabel('Baseline:'))
        self.cb_baseline = QComboBox()
        self.cb_baseline.addItems(['Static capture', 'Rolling median', 'Nominal thresholds'])
        self.cb_baseline.currentIndexChanged.connect(self._on_baseline_mode_changed)
        row2.addWidget(self.cb_baseline)

        row2.addWidget(QLabel('N='))
        self.sp_capture_n = QSpinBox()
        self.sp_capture_n.setRange(1, 4096)
        self.sp_capture_n.setValue(CAPTURE_FRAMES_DEFAULT)
        row2.addWidget(self.sp_capture_n)

        self.pb_capture = QPushButton('Capture baseline')
        self.pb_capture.clicked.connect(self._start_capture)
        row2.addWidget(self.pb_capture)

        self.pb_clear = QPushButton('Clear baseline')
        self.pb_clear.clicked.connect(self.clear_baseline)
        row2.addWidget(self.pb_clear)

        self.pb_freeze = QPushButton('Freeze')
        self.pb_freeze.setCheckable(True)
        self.pb_freeze.toggled.connect(self._on_freeze_toggled)
        row2.addWidget(self.pb_freeze)
        layout.addLayout(row2)

        # Row 3 — scale + rolling T + baseline info
        row3 = QHBoxLayout()
        self.cb_autoscale = QCheckBox('Auto ±')
        self.cb_autoscale.setChecked(True)
        self.cb_autoscale.toggled.connect(self._on_autoscale_toggled)
        row3.addWidget(self.cb_autoscale)

        row3.addWidget(QLabel('Range (µV):'))
        self.sp_range = QDoubleSpinBox()
        self.sp_range.setRange(100, 5_000_000)
        self.sp_range.setSingleStep(10_000)
        self.sp_range.setDecimals(0)
        self.sp_range.setValue(self._manual_range)
        self.sp_range.setEnabled(False)
        self.sp_range.valueChanged.connect(self._on_range_changed)
        row3.addWidget(self.sp_range)

        row3.addWidget(QLabel('Rolling T (s):'))
        self.sp_rolling_t = QDoubleSpinBox()
        self.sp_rolling_t.setRange(0.5, 60.0)
        self.sp_rolling_t.setSingleStep(0.5)
        self.sp_rolling_t.setDecimals(1)
        self.sp_rolling_t.setValue(ROLLING_SECS_DEFAULT)
        self.sp_rolling_t.valueChanged.connect(self._on_rolling_t_changed)
        row3.addWidget(self.sp_rolling_t)

        self.lbl_baseline_info = QLabel('No baseline')
        row3.addWidget(self.lbl_baseline_info, stretch=1)

        self.lbl_scale = QLabel('Scale: —')
        row3.addWidget(self.lbl_scale)
        layout.addLayout(row3)

        # Main view stack (2D heatmap / 3D surface)
        self.stack = QStackedWidget()
        self.stack.addWidget(self._build_heatmap_widget())   # index 0
        self.stack.addWidget(self._build_3d_widget())        # index 1
        layout.addWidget(self.stack, stretch=1)

        btn_toggle = QHBoxLayout()
        self.pb_toggle3d = QPushButton('Switch to 3D Surface')
        self.pb_toggle3d.clicked.connect(self._toggle_3d)
        btn_toggle.addWidget(self.pb_toggle3d)
        btn_toggle.addStretch(1)
        layout.addLayout(btn_toggle)

        # Zero-crossing summary
        self.lbl_crossings = QLabel('Crossings: —')
        layout.addWidget(self.lbl_crossings)

        # ML bridge — row A
        ml_a = QHBoxLayout()
        ml_a.addWidget(QLabel('Label:'))
        self.le_label = QLineEdit()
        self.le_label.setPlaceholderText('e.g. air / silver_coin / stainless_bolt')
        ml_a.addWidget(self.le_label, stretch=1)

        self.pb_snapshot = QPushButton('Record Snapshot')
        self.pb_snapshot.clicked.connect(self._record_snapshot)
        ml_a.addWidget(self.pb_snapshot)

        self.cb_continuous = QCheckBox('Log Continuously')
        self.cb_continuous.toggled.connect(self._on_continuous_toggled)
        ml_a.addWidget(self.cb_continuous)

        self.lbl_rows = QLabel('Rows: 0')
        ml_a.addWidget(self.lbl_rows)
        layout.addLayout(ml_a)

        # ML bridge — row B (CSV path)
        ml_b = QHBoxLayout()
        ml_b.addWidget(QLabel('CSV:'))
        self.le_csv = QLineEdit(_csv_default_path())
        ml_b.addWidget(self.le_csv, stretch=1)
        pb_browse = QPushButton('Browse…')
        pb_browse.clicked.connect(self._browse_csv)
        ml_b.addWidget(pb_browse)
        layout.addLayout(ml_b)

        return w

    def _build_heatmap_widget(self):
        self.gw = pg.GraphicsLayoutWidget()
        self.plot = self.gw.addPlot()
        self.plot.invertY(True)
        self.plot.setDefaultPadding(0)

        self.img = pg.ImageItem()
        self.img.setColorMap(self.cm_div)
        self.plot.addItem(self.img)

        self._rebuild_heatmap_axes()

        self.plot.scene().sigMouseMoved.connect(self._on_mouse_move)
        return self.gw

    def _rebuild_heatmap_axes(self):
        ax_b = self.plot.getAxis('bottom')
        ax_b.setTicks([[(j + 0.5, self._cell_labels[j]) for j in range(self._n_cells)]])
        ax_b.setLabel('Threshold' if self._has_threshold_v else 'Cell')

        ax_l = self.plot.getAxis('left')
        ax_l.setTicks([[(d + 0.5, self._display_band_labels[d]) for d in range(self._n_bands)]])
        ax_l.setLabel('Band')

        self.plot.setXRange(0, self._n_cells, padding=0)
        self.plot.setYRange(0, self._n_bands, padding=0)

    def _build_3d_widget(self):
        if not _GL_AVAILABLE:
            w   = QWidget()
            lbl = QLabel('3D view requires PyOpenGL — install python3-pyopengl')
            lbl.setAlignment(Qt.AlignmentFlag.AlignCenter)
            QVBoxLayout(w).addWidget(lbl)
            return w

        self.gl_widget = gl.GLViewWidget()
        self.gl_widget.setCameraPosition(distance=15, elevation=30, azimuth=45)
        self._surface = gl.GLSurfacePlotItem(
            x=np.arange(self._n_cells, dtype=float),
            y=np.arange(self._n_bands, dtype=float),
            z=np.zeros((self._n_cells, self._n_bands)),
            smooth=False,
        )
        self.gl_widget.addItem(self._surface)
        return self.gl_widget

    def _rebuild_3d_surface(self):
        if not _GL_AVAILABLE or not hasattr(self, '_surface'):
            return
        self._surface.setData(
            x=np.arange(self._n_cells, dtype=float),
            y=np.arange(self._n_bands, dtype=float),
            z=np.zeros((self._n_cells, self._n_bands)))

    # ------------------------------------------------------------------
    # Tab 1 — Stats & Isolation
    # ------------------------------------------------------------------
    def _build_stats_tab(self):
        w      = QWidget()
        layout = QVBoxLayout(w)

        # Controls row
        ctrl = QHBoxLayout()
        self.pb_freeze_stats = QPushButton('Freeze')
        self.pb_freeze_stats.setCheckable(True)
        self.pb_freeze_stats.toggled.connect(self._on_freeze_stats_toggled)
        ctrl.addWidget(self.pb_freeze_stats)

        lbl_std_n = QLabel('Std dev N:')
        lbl_std_n.setToolTip('Rolling sample window, shared with the Heatmap tab\'s '
                              '"Std Dev" display mode and the Analysis tab heatmap.')
        ctrl.addWidget(lbl_std_n)
        self.sp_stats_window = QSpinBox()
        self.sp_stats_window.setRange(2, 2000)
        self.sp_stats_window.setSingleStep(10)
        self.sp_stats_window.setValue(50)
        self.sp_stats_window.setToolTip(lbl_std_n.toolTip())
        ctrl.addWidget(self.sp_stats_window)

        pb_save_stats = QPushButton('Save table CSV…')
        pb_save_stats.clicked.connect(self._save_stats_csv)
        ctrl.addWidget(pb_save_stats)

        self.pb_record = QPushButton('Record Session')
        self.pb_record.setCheckable(True)
        self.pb_record.setStyleSheet(self.MY_YELLOW)
        self.pb_record.toggled.connect(self._toggle_record_frames)
        ctrl.addWidget(self.pb_record)

        ctrl.addWidget(QLabel('Std:'))
        self.sp_std_lower = QDoubleSpinBox()
        self.sp_std_lower.setRange(0.0, 999.0)
        self.sp_std_lower.setDecimals(2)
        self.sp_std_lower.setSingleStep(0.05)
        self.sp_std_lower.setValue(0.50)
        self.sp_std_lower.setMaximumWidth(70)
        ctrl.addWidget(self.sp_std_lower)

        ctrl.addWidget(QLabel('–'))

        self.sp_std_upper = QDoubleSpinBox()
        self.sp_std_upper.setRange(0.0, 999.0)
        self.sp_std_upper.setDecimals(2)
        self.sp_std_upper.setSingleStep(0.05)
        self.sp_std_upper.setValue(1.00)
        self.sp_std_upper.setMaximumWidth(70)
        ctrl.addWidget(self.sp_std_upper)

        ctrl.addStretch(1)

        pb_rows_shrink = QPushButton('−')
        pb_rows_shrink.setMaximumWidth(28)
        pb_rows_shrink.clicked.connect(self._stats_rows_shrink)
        ctrl.addWidget(pb_rows_shrink)

        pb_rows_grow = QPushButton('+')
        pb_rows_grow.setMaximumWidth(28)
        pb_rows_grow.clicked.connect(self._stats_rows_grow)
        ctrl.addWidget(pb_rows_grow)

        ctrl.addWidget(QLabel('All values in mV'))
        layout.addLayout(ctrl)

        # Stats table: Band | Threshold | Delay µs | Latest mV | Mean mV | Std mV
        self.tbl_stats = QTableWidget(self._n_channels, 6)
        self.tbl_stats.setHorizontalHeaderLabels(
            ['Band', 'Threshold', 'Delay (µs)', 'Latest (mV)', 'Mean (mV)', 'Std (mV)'])
        self.tbl_stats.horizontalHeader().setSectionResizeMode(QHeaderView.ResizeMode.Stretch)
        self.tbl_stats.setEditTriggers(QTableWidget.EditTrigger.NoEditTriggers)
        self.tbl_stats.setAlternatingRowColors(True)
        self._rebuild_stats_table()

        layout.addWidget(self.tbl_stats, stretch=1)
        return w

    def _rebuild_stats_table(self):
        self.tbl_stats.setRowCount(self._n_channels)
        for d in range(self._n_bands):
            b = self._band_stats_order[d]
            freq_hz, pulse_us, delays = self._bands_meta[b]
            for c in range(self._n_cells):
                row = d * self._n_cells + c
                for col, text in enumerate([self._stats_band_labels[d],
                                            self._cell_labels[c],
                                            '{0:.3f}'.format(delays[c])]):
                    item = QTableWidgetItem(text)
                    item.setTextAlignment(_C)
                    self.tbl_stats.setItem(row, col, item)
                for col in range(3, 6):
                    item = QTableWidgetItem('—')
                    item.setTextAlignment(_R)
                    self.tbl_stats.setItem(row, col, item)

    # ------------------------------------------------------------------
    # Saved-profile selector (top bar) — load a profile JSON from disk and
    # send it straight to the board as a dynamic (RAM-only) profile.
    # ------------------------------------------------------------------
    def _refresh_profile_file_list(self):
        self.cb_profile_file.clear()
        for name in _list_profile_files():
            self.cb_profile_file.addItem(name)

    def _build_d_command(self, profile):
        parts = ['D{0}'.format(profile['averages'])]
        for b in profile['bands']:
            fields = [str(b['freq_hz']), '{0:.3f}'.format(b['pulse_us'])]
            fields += ['{0:.3f}'.format(d) for d in b['delays_us']]
            parts.append(','.join(fields))
        return ';'.join(parts)

    def _on_load_run_profile(self):
        name = self.cb_profile_file.currentText()
        if not name:
            self.statusBar().showMessage('No saved profile selected')
            return
        try:
            profile, profile_raw_bytes = _load_profile_file(name)
        except Exception as e:
            self.statusBar().showMessage('Load failed: {0}'.format(e))
            return
        if not self.serial.isOpen():
            self.statusBar().showMessage('Not connected')
            return
        if self._pending_d_ready is not None:
            # v1.73: one handshake at a time. Two overlapping sends would let
            # the FIRST D's reply fire the SECOND profile's callback, sending
            # Q/G before the second D had been acknowledged -- reintroducing
            # the exact race the handshake exists to close.
            self.statusBar().showMessage(
                'A profile send is already in flight — wait for it to finish')
            return
        # v1.73: hold Q/G back until the firmware confirms the D actually took.
        # Sending them blind is how a session ends up recording one profile's
        # geometry under another profile's name -- see _send_dynamic_profile().
        self._send_dynamic_profile(
            profile,
            lambda: self._finish_load_run_profile(profile, profile_raw_bytes, name))
        self.statusBar().showMessage('Sending profile {0}...'.format(
            profile.get('name', name)))

    def _finish_load_run_profile(self, profile, profile_raw_bytes, name):
        """Second half of _on_load_run_profile, run only once the firmware has
        acknowledged the D. Everything here commits to the new geometry -- the
        profile the GUI displays, the profile the session header records -- so
        none of it may happen against a D that was refused."""
        self.send_command('Q{0}'.format(DYNAMIC_PROFILE_INDEX))
        self.send_command('G')
        # v1.74: the stream starts HERE, so the soak/stall run state is armed here
        # -- ahead of _apply_profile, which can reopen the dump. Before v1.74 this
        # path never armed it at all and every soak line it produced was wrong.
        self._begin_stream_run()
        self._apply_profile(profile, DYNAMIC_PROFILE_INDEX, profile_raw_bytes)
        self.pb_start.setText('Running')
        self.pb_start.setStyleSheet(self.MY_GREEN)
        # This path sends its own 'G' rather than going through start_stop(), so
        # it has to arm auto-logging itself -- and it matters most here: it is
        # the v1.53 launch auto-start, i.e. the whole warm-up and settle window
        # before anyone presses anything. No double-open risk: if _apply_profile
        # above already reopened a dump, _maybe_autostart_session no-ops.
        self._session_autolog_suppressed = False
        self._maybe_autostart_session('profile load + run')
        # v1.74: matches start_stop()'s start branch, so a run begun by Load & Run
        # is bracketed by stream-start/stream-stop like any other.
        self._append_soak('stream-start')
        self.statusBar().showMessage('Loaded and running profile: {0}'.format(
            profile.get('name', name)))

    # ------------------------------------------------------------------
    # Dynamic-profile handshake (v1.73)
    # ------------------------------------------------------------------
    def _send_dynamic_profile(self, profile, on_ready):
        """Send E + D for `profile`, then hold Q<n>/G back until the firmware's
        own D response confirms it took -- process_packet() calls `on_ready`
        once that arrives. Ported from pimd_delaycal.py v1.41, which has run
        this shape since.

        Q<n>/G must never fire after a D the firmware rejected. The firmware
        refuses the WHOLE D on any invalid cell and leaves the previous dynamic
        profile in place, so Q<n> would then select that stale profile and G
        would stream its geometry -- while _apply_profile() had already told the
        GUI, and the session header, that the new one was running. That is a CSV
        that names a profile it does not contain, which no amount of offline
        analysis can detect afterwards."""
        self._pending_d_ready = on_ready
        self.send_command('E')
        self.send_command(self._build_d_command(profile))
        # A reply always comes (D OK or a Command Input ERROR), but a dropped
        # line must not leave the app waiting forever -- this path is also the
        # v1.53 launch auto-start, where a silent stall reads as "ClassViz never
        # started" with nothing on screen to say why.
        self._d_ack_timer.start(D_ACK_TIMEOUT_MS)

    def _on_d_ack_timeout(self):
        """No D response inside D_ACK_TIMEOUT_MS. Drop the pending callback --
        Q/G are NOT sent. Failing closed is the whole point: streaming on an
        unconfirmed profile is exactly the mislabelled-session outcome this
        handshake exists to prevent."""
        if self._pending_d_ready is None:
            return
        self._pending_d_ready = None
        self.statusBar().showMessage(
            'No response to the profile (D) command after {0:.0f} s -- profile NOT '
            'loaded, stream not started. Check the board and try Load & Run again.'
            .format(D_ACK_TIMEOUT_MS / 1000.0))

    # ------------------------------------------------------------------
    # Tab 2 — Analysis
    # ------------------------------------------------------------------
    def _style_compact(self, plot, title=None):
        """Small tick font + a little padding + optional small title --
        applied to every Analysis-tab plot so ~20 small panels can share
        one screen without their chrome eating the plot area."""
        font = QFont()
        font.setPointSize(7)
        plot.getAxis('bottom').setStyle(tickFont=font)
        plot.getAxis('left').setStyle(tickFont=font)
        plot.setDefaultPadding(0.02)
        if title:
            plot.setTitle(title, size='7pt')

    def _build_analysis_tab(self):
        w = QWidget()
        layout = QVBoxLayout(w)
        layout.setContentsMargins(4, 4, 4, 4)
        layout.setSpacing(4)

        # Left column: Controls + Signatures + Training above, Heatmap below,
        # sharing one width -- Signatures/Controls used to span the full tab
        # width above everything else; now they're grouped with the heatmap so
        # the right side (charts) can reach the top of the tab.
        #
        # The two halves are split (v1.38) rather than stacked with a fixed
        # heatmap stretch: the heatmap used to own a fixed share of the column
        # height regardless of how many signatures were loaded, so the
        # signature list stayed ~2 rows tall and was unusable for picking
        # overlays out of a 10+ capture corpus. The handle now trades heatmap
        # height for signature-list height, and the heatmap can be dragged
        # away entirely on a capture-only day.
        left_col = QWidget()
        left_v = QVBoxLayout(left_col)
        left_v.setContentsMargins(0, 0, 0, 0)
        left_v.setSpacing(4)

        top_box = QGroupBox('Controls')
        top_v = QVBoxLayout(top_box)
        top_v.setContentsMargins(4, 4, 4, 4)
        top_v.setSpacing(2)
        top_v.addLayout(self._build_analysis_ctrl_row_a())
        left_v.addWidget(top_box)
        left_v.addWidget(self._build_analysis_signatures_group(), stretch=1)
        left_v.addWidget(self._build_analysis_training_group())

        left_split = QSplitter(Qt.Orientation.Vertical)
        left_split.setHandleWidth(4)
        left_split.addWidget(left_col)
        left_split.addWidget(self._build_analysis_heatmap_group())
        left_split.setStretchFactor(0, 1)
        left_split.setStretchFactor(1, 1)
        left_split.setSizes([620, 380])
        left_split.setCollapsible(0, False)   # capture controls must stay reachable
        left_split.setCollapsible(1, True)    # the heatmap may be dragged fully away
        self.analysis_left_split = left_split

        # Right column: row1 (trigger gauges | strips | chart2 side by side)
        # + 8-grid + 9-grid. The gauges sit leftmost and take no share of a
        # resize -- they are four fixed-height rows, so extra width is wasted
        # on them and wanted by the charts.
        row1_split = QSplitter(Qt.Orientation.Horizontal)
        row1_split.setHandleWidth(4)
        row1_split.addWidget(self._build_analysis_gauges_group())
        row1_split.addWidget(self._build_analysis_strips_group())
        row1_split.addWidget(self._build_analysis_chart2_group())
        row1_split.setSizes([300, 600, 600])
        row1_split.setStretchFactor(0, 0)
        row1_split.setCollapsible(0, True)
        self.analysis_row1_split = row1_split

        right_split = QSplitter(Qt.Orientation.Vertical)
        right_split.setHandleWidth(4)
        right_split.addWidget(row1_split)
        right_split.addWidget(self._build_analysis_grid8_group())
        right_split.addWidget(self._build_analysis_grid9_group())
        # Row 1 opens at 320 rather than the old 220: five 46 px gauge rows,
        # the 8 px gaps between them and the group title need ~290, and
        # anything less opens them squashed to their 26 px minimum. The handle
        # still trades it back for grid height, and analysis_row1_split_sizes
        # persists whatever you choose.
        right_split.setSizes([320, 210, 210])
        self.analysis_right_split = right_split

        main_split = QSplitter(Qt.Orientation.Horizontal)
        main_split.setHandleWidth(4)
        main_split.addWidget(left_split)
        main_split.addWidget(right_split)
        main_split.setSizes([560, 1440])
        # v1.79: these two are persisted like the other pair. main_split is the
        # vertical divider that sets the heatmap's WIDTH (left_split only sets
        # its height), so without it a resized heatmap panel came back at 560 px
        # every launch -- the one divider on this tab whose position was always
        # discarded.
        self.analysis_main_split = main_split
        layout.addWidget(main_split, stretch=1)

        return w

    def _build_analysis_ctrl_row_a(self):
        ctrl_a = QHBoxLayout()
        ctrl_a.addWidget(QLabel('Avg N frames:'))
        self.sp_analysis_avg_n = QSpinBox()
        self.sp_analysis_avg_n.setRange(1, 200)
        self.sp_analysis_avg_n.setValue(self._analysis_avg_n)
        self.sp_analysis_avg_n.valueChanged.connect(self._on_analysis_avg_n_changed)
        ctrl_a.addWidget(self.sp_analysis_avg_n)

        self.pb_analysis_capture = QPushButton('Capture baseline')
        self.pb_analysis_capture.clicked.connect(self._start_capture)
        ctrl_a.addWidget(self.pb_analysis_capture)

        self.pb_analysis_clear = QPushButton('Clear baseline')
        self.pb_analysis_clear.clicked.connect(self.clear_baseline)
        ctrl_a.addWidget(self.pb_analysis_clear)

        self.lbl_analysis_baseline_info = QLabel('No baseline')
        ctrl_a.addWidget(self.lbl_analysis_baseline_info)
        ctrl_a.addStretch(1)
        return ctrl_a

    def _build_analysis_signatures_group(self):
        box = QGroupBox('Signatures')
        v = QVBoxLayout(box)
        v.setContentsMargins(4, 4, 4, 4)
        v.setSpacing(2)
        self._build_sig_row1_files(v)
        v.addWidget(self.lw_analysis_templates, stretch=1)
        self._build_sig_row2_capture_inputs(v)
        self._build_sig_row3_readout_save(v)
        self._build_sig_row4_session(v)
        self._update_sig_mode_label()
        self._update_sig_session_status_label()
        return box

    def _build_sig_row1_files(self, v):
        row_a = QHBoxLayout()
        pb_load_sigs = QPushButton('Load signatures…')
        pb_load_sigs.clicked.connect(self._on_load_signatures_clicked)
        row_a.addWidget(pb_load_sigs)

        pb_new = QPushButton('New file…')
        pb_new.clicked.connect(self._on_sig_new_file_clicked)
        row_a.addWidget(pb_new)
        row_a.addStretch(1)
        v.addLayout(row_a)

        row_b = QHBoxLayout()
        pb_open = QPushButton('Open for editing…')
        pb_open.clicked.connect(self._on_sig_open_for_edit_clicked)
        row_b.addWidget(pb_open)

        pb_clear_sigs = QPushButton('Clear signatures')
        pb_clear_sigs.clicked.connect(self._on_clear_signatures_clicked)
        row_b.addWidget(pb_clear_sigs)

        self.lbl_sig_mode = QLabel('Mode: read-only')
        row_b.addWidget(self.lbl_sig_mode, stretch=1)
        v.addLayout(row_b)

        # Changed from the original wrapped left-to-right "tag" flow --
        # labels now carry amp/SNR/quality text, so a normal scrollable
        # top-to-bottom list is more legible. It takes all the height the
        # left splitter gives it (v1.38): the old 46px *maximum* pinned it to
        # ~2 visible rows, which made a 10+ capture corpus unpickable; 46px is
        # now the floor instead, and the surplus comes out of the heatmap.
        self.lw_analysis_templates = QListWidget()
        self.lw_analysis_templates.setFlow(QListWidget.Flow.TopToBottom)
        self.lw_analysis_templates.setMinimumHeight(46)
        self.lw_analysis_templates.itemChanged.connect(self._on_analysis_template_item_changed)
        self.lw_analysis_templates.currentItemChanged.connect(lambda *_: self._update_sig_capture_gating())

    # -- Target/placement widget set (Analysis tab inline capture inputs) ----

    def _build_target_placement_widget_set(self, layout, prefix, emphasise_target=False):
        """Builds a target-registry combo + structured placement widgets into
        `layout`, storing them as self.{prefix}_target, {prefix}_distance_mm,
        {prefix}_long_axis, {prefix}_medium, {prefix}_repeat_idx. Pure
        construction -- caller wires signals and calls
        _populate_target_combo() to fill the target combo from the currently
        loaded registry. Kept as a separate builder (rather than inlined into
        its one caller) because the field set is the corpus schema's placement
        tuple -- it deserves one definition even with a single instantiation
        site. The second call site, the Training Session tab's per-row
        Placement dialog, went with that tab in v1.39.

        emphasise_target: bold/enlarge the Target label + combo (v1.38), where
        that one combo decides what every Save writes into the corpus and
        picking the wrong one silently mislabels a capture -- it shouldn't
        look like just another dropdown."""
        row_a = QHBoxLayout()
        lbl_target = QLabel('Target:')
        target_combo = QComboBox()
        target_combo.setMinimumWidth(220)
        if emphasise_target:
            emph_font = QFont()
            emph_font.setPointSize(12)
            emph_font.setBold(True)
            lbl_target.setFont(emph_font)
            target_combo.setFont(emph_font)
            target_combo.setMinimumWidth(300)
            target_combo.setMinimumHeight(30)
        row_a.addWidget(lbl_target)
        setattr(self, '{0}_target'.format(prefix), target_combo)
        row_a.addWidget(target_combo, stretch=1)

        row_a.addWidget(QLabel('Distance (mm):'))
        distance_mm = QSpinBox()
        distance_mm.setRange(0, 5000)
        distance_mm.setValue(50)
        distance_mm.setToolTip('Coil face → nearest target surface, in mm.')
        setattr(self, '{0}_distance_mm'.format(prefix), distance_mm)
        row_a.addWidget(distance_mm)
        layout.addLayout(row_a)

        row_b = QHBoxLayout()
        row_b.addWidget(QLabel('Long axis:'))
        long_axis = QComboBox()
        long_axis.addItems(['na', 'x', 'y', 'z'])
        long_axis.setToolTip(
            "Direction the target registry's dim_a points. x = coil long axis "
            '(520mm direction), y = coil short axis (360mm), z = coil normal '
            '(vertical). na for compact/isotropic targets.')
        setattr(self, '{0}_long_axis'.format(prefix), long_axis)
        row_b.addWidget(long_axis)

        # Tilt (v1.67). The oblique-pose input long_axis cannot express: the
        # 2026-07-31 corpus analysis could confirm the two-basis model's rank-2
        # structure but not its mixing law, because every capture on disk sits
        # at exactly 0 or 90 deg to the coil axis.
        tilt_tip = (
            'Tilt of dim_a AWAY FROM THE COIL NORMAL, in degrees. 0 = dim_a '
            'straight down the coil axis (same pose as Long axis = z), '
            '90 = dim_a lying in the coil plane (same pose as x/y). Only '
            'meaningful with Long axis = z, and written blank otherwise — '
            'blank means "not recorded", which is NOT the same as a recorded 0.')
        lbl_tilt = QLabel('Tilt (°):')
        lbl_tilt.setToolTip(tilt_tip)
        setattr(self, '{0}_tilt_deg_label'.format(prefix), lbl_tilt)
        row_b.addWidget(lbl_tilt)
        tilt_deg = QSpinBox()
        tilt_deg.setRange(0, 90)
        tilt_deg.setSingleStep(5)
        tilt_deg.setValue(0)
        tilt_deg.setToolTip(tilt_tip)
        setattr(self, '{0}_tilt_deg'.format(prefix), tilt_deg)
        row_b.addWidget(tilt_deg)
        long_axis.currentTextChanged.connect(
            lambda _t, p=prefix: self._update_tilt_enabled(p))

        row_b.addWidget(QLabel('Medium:'))
        medium = QComboBox()
        medium.addItems(['air', 'soil', 'other'])
        setattr(self, '{0}_medium'.format(prefix), medium)
        row_b.addWidget(medium)

        # Repeat # shared row B with the offsets' row until v1.60 removed
        # those; on its own it did not earn a row of its own.
        repeat_tip = (
            'Provenance metadata only — distinguishes repeated captures of the '
            'same placement tuple (target, distance, long axis, medium) so '
            'they don\'t collide as one signature in the corpus CSV. '
            'Auto-suggested as count+1 from the open file\'s existing captures; '
            'editable. Not used in any matching/classification math.')
        lbl_repeat = QLabel('Repeat #:')
        lbl_repeat.setToolTip(repeat_tip)
        row_b.addWidget(lbl_repeat)
        repeat_idx = QSpinBox()
        repeat_idx.setRange(1, 999)
        repeat_idx.setValue(1)
        repeat_idx.setToolTip(repeat_tip)
        setattr(self, '{0}_repeat_idx'.format(prefix), repeat_idx)
        row_b.addWidget(repeat_idx)
        row_b.addStretch(1)
        layout.addLayout(row_b)

    def _populate_target_combo(self, combo, selected_target_id=None):
        combo.blockSignals(True)
        combo.clear()
        combo.addItem('air — (no target)', 'air')
        for target_id in sorted(self._targets):
            t = self._targets[target_id]
            combo.addItem('{0} — {1}'.format(target_id, t.short_name), target_id)
        idx = combo.findData(selected_target_id) if selected_target_id else -1
        combo.setCurrentIndex(idx if idx >= 0 else 0)
        combo.blockSignals(False)

    def _placement_from_widgets(self, prefix):
        """Reads the current values of a _build_target_placement_widget_set()
        instance back into a plain dict, keyed the same as
        pimd_features.parse_mark_target_line()'s companion fields."""
        target_combo = getattr(self, '{0}_target'.format(prefix))
        return {
            'target_id': target_combo.currentData(),
            'distance_mm': getattr(self, '{0}_distance_mm'.format(prefix)).value(),
            'long_axis': getattr(self, '{0}_long_axis'.format(prefix)).currentText(),
            # Not inputs since v1.60 -- they were never set, and face_normal
            # being a *persisted* combo meant a value chosen once silently
            # attached itself to every later capture (all 12 captures of a
            # tube in the v3 corpus carry face_normal=z, which is meaningless
            # for that shape). Still keys of this dict, so the CSV column, the
            # session dump's mark_target: line and the placement tuple are all
            # unchanged -- pimd_corpus_check.PLACEMENT_FIELDS still expects
            # them, and older corpora carry real values.
            'face_normal': 'na',
            'offset_x_mm': 0,
            'offset_y_mm': 0,
            'medium': getattr(self, '{0}_medium'.format(prefix)).currentText(),
            'repeat_idx': getattr(self, '{0}_repeat_idx'.format(prefix)).value(),
            # v1.67. The single place the blank-when-not-applicable rule lives.
            # A tilt is only defined relative to the coil normal, so it is only
            # recorded when the operator declared that pose; for x/y/na the
            # angle is already implied by long_axis and writing a number here
            # would key those captures differently from every historical one.
            'tilt_deg': (getattr(self, '{0}_tilt_deg'.format(prefix)).value()
                         if getattr(self, '{0}_long_axis'.format(prefix)).currentText() == 'z'
                         else ''),
            # The Notes entry box was dropped in v1.38 (dead weight in the
            # capture flow -- nothing was being typed into it). The key and
            # the corpus 'notes' column stay, always empty, so build_rows()
            # and the session dump's mark_target: line are unchanged.
            'notes': '',
        }

    def _update_tilt_enabled(self, prefix):
        """Tilt is only meaningful when dim_a was declared along the coil
        normal, so the spinbox follows the Long axis combo (v1.67). Kept
        separate from _update_sig_capture_gating() because that one is about
        whether a file is open, and both conditions have to hold."""
        tilt = getattr(self, '{0}_tilt_deg'.format(prefix), None)
        if tilt is None:
            return   # mid-build
        is_z = getattr(self, '{0}_long_axis'.format(prefix)).currentText() == 'z'
        enabled = is_z and (self._editable_sig_path is not None
                            if prefix == 'sig' else True)
        tilt.setEnabled(enabled)
        getattr(self, '{0}_tilt_deg_label'.format(prefix)).setEnabled(enabled)

    def _update_sig_repeat_idx_suggestion(self):
        """Auto-increments the Analysis tab's repeat_idx spinbox to the next
        unused value for the current placement tuple, per the brief's rule
        (still user-editable afterward -- this only sets a suggestion)."""
        if not hasattr(self, 'sig_target'):
            return
        placement = self._placement_from_widgets('sig')
        key = self._placement_tuple_key(placement)
        suggested = self._editable_repeat_counts.get(key, 0) + 1
        self.sig_repeat_idx.blockSignals(True)
        self.sig_repeat_idx.setValue(suggested)
        self.sig_repeat_idx.blockSignals(False)

    # -- Target registry loading / degrade behavior --------------------------

    def _load_targets_registry(self, show_dialog_on_error=True):
        """(Re)loads the target registry and repopulates every combo built by
        _build_target_placement_widget_set(). Degrade behavior:
          - missing/unreadable file -> air-only, status bar message.
          - loads with errors -> dialog (if show_dialog_on_error) + only the
            non-erroring targets loaded, 'air' always present.
          - loads with only warnings -> status bar summary, fully populated.
        Called once at UI-build time. The Analysis tab's "Reload targets"
        button was dropped in v1.38 -- the registry is a slow-moving reference
        file, so a mid-session reload was never worth a permanent control;
        restart ClassViz to pick up registry edits."""
        try:
            targets, issues = pimd_target_check.load_targets(TARGETS_REGISTRY_PATH)
        except OSError as e:
            self._targets, self._target_issues = {}, []
            self.statusBar().showMessage(
                "Target registry not found at {0} -- capture disabled except 'air' "
                '({1})'.format(TARGETS_REGISTRY_PATH, e))
            self._repopulate_target_combos()
            return

        self._targets, self._target_issues = targets, issues
        errors = [i for i in issues if i.severity == 'error']
        warnings = [i for i in issues if i.severity == 'warning']
        if errors and show_dialog_on_error:
            QMessageBox.critical(
                self, 'Target registry errors',
                "The target registry has {0} error(s) -- affected rows are unusable "
                "(only 'air' and valid rows are selectable):\n\n{1}".format(
                    len(errors), '\n'.join(str(i) for i in errors)))
        if errors:
            self.statusBar().showMessage(
                'Target registry: {0} usable target(s), {1} error(s), {2} warning(s) '
                '-- see dialog / run pimd_target_check.py for detail'.format(
                    len(targets), len(errors), len(warnings)))
        elif warnings:
            self.statusBar().showMessage(
                'Target registry loaded: {0} target(s), {1} warning(s) (run '
                'pimd_target_check.py for detail)'.format(len(targets), len(warnings)))
        else:
            self.statusBar().showMessage('Target registry loaded: {0} target(s)'.format(len(targets)))
        self._repopulate_target_combos()

    def _repopulate_target_combos(self):
        if hasattr(self, 'sig_target'):
            current = self.sig_target.currentData()
            self._populate_target_combo(self.sig_target, selected_target_id=current)
        if hasattr(self, '_update_sig_capture_gating'):
            self._update_sig_capture_gating()

    def _build_sig_row2_capture_inputs(self, v):
        self._build_target_placement_widget_set(v, 'sig', emphasise_target=True)
        self.sig_target.currentIndexChanged.connect(self._update_sig_capture_gating)
        for widget, signal_name in (
            (self.sig_target, 'currentIndexChanged'), (self.sig_distance_mm, 'valueChanged'),
            (self.sig_long_axis, 'currentIndexChanged'),
            (self.sig_medium, 'currentIndexChanged'),
            # v1.67: tilt joined the placement tuple, so changing it selects a
            # different placement and must re-run the Repeat # suggestion --
            # otherwise a 30 deg capture inherits the 0 deg placement's count.
            (self.sig_tilt_deg, 'valueChanged'),
        ):
            getattr(widget, signal_name).connect(self._update_sig_repeat_idx_suggestion)

    def _build_analysis_training_group(self):
        """Training group (v1.34) — automated auto-detect capture cycle. One
        Space press per cycle locks the leading air; target placement and
        removal are auto-detected (settle + Detect threshold), with 30 s guard
        countdowns and a Save/Ignore decision. The settle gate, glitch
        exclusion and stats math (pimd_features) are unchanged from v1.33."""
        box = QGroupBox('Training')
        v = QVBoxLayout(box)
        v.setContentsMargins(4, 4, 4, 4)
        v.setSpacing(2)

        # -- Row 1: Start/Stop, Frames, Settle, Detect, Space-override --------
        row1 = QHBoxLayout()
        self.pb_sig_train_start = QPushButton('Start Training')
        self.pb_sig_train_start.setCheckable(True)
        self.pb_sig_train_start.toggled.connect(self._on_sig_train_start_toggled)
        row1.addWidget(self.pb_sig_train_start)

        row1.addWidget(QLabel('Frames:'))
        self.sp_sig_capture_n = QSpinBox()
        self.sp_sig_capture_n.setRange(10, 2000)
        self.sp_sig_capture_n.setValue(self._sig_capture_n)
        self.sp_sig_capture_n.valueChanged.connect(self._update_sig_capture_n_warning)
        self._sig_capture_n_last_style = None
        self._update_sig_capture_n_warning(self.sp_sig_capture_n.value())
        row1.addWidget(self.sp_sig_capture_n)
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
